hristoandreev/UA3REO-DDC-Transceiver/Schematic/Wolf/Altium_Designer/Mod-LZ1HAA-hardware/MOTHERBOARD/3d/conn-jack-sma-str-molex-73391-0060-rf-slash-coaxial/Renderings/floorsma.JPG

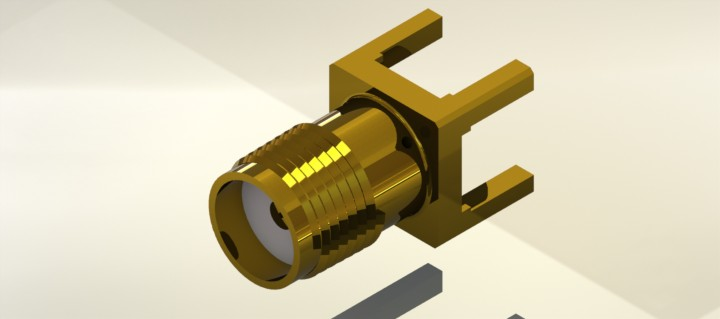
Schematic/Wolf/Altium_Designer/Mod-LZ1HAA-hardware/MOTHERBOARD/3d/conn-jack-sma-str-molex-73391-0060-rf-slash-coaxial/Renderings/floorsma.JPG
