hristoandreev/UA3REO-DDC-Transceiver/Schematic/Wolf/Altium_Designer/Mod-LZ1HAA-hardware/FRONT-UNIT-7/Project Outputs for FRONT-UNIT-7/BOM/Bill of Materials-FRONT-UNIT-7.xlsx

Comment | Description | Designator | Footprint | Quantity
0R | RES_0805 | R6, R7, R8 | RES_0805 | 3
1k | RES_0805 | R17, R18, R19, R20, R44 | RES_0805 | 5
1nF | CAP_1206 | C5 | CAP_1206 | 1
1uF | CAP_0805 | C48, C50, C51, C52, C53 | CAP_0805 | 5
1uF | CAP_1206 | C3 | CAP_1206 | 1
1uF 10V | CAPAE_4.3x4.3h5.4 | C34, C37, C42 | CAPAE_4.3x4.3h5.4 | 3
2k | RES_0805 | R21, R22, R23, R24 | RES_0805 | 4
4.7k | Chip Resistor | R32, R33 | R-0805 | 2
4.7k | RES_0805 | R3, R4, R5, R13, R14, R15, R16, R26, R27, R28, R29 | RES_0805 | 11
4.7k 1% | RES_0805 | R9 | RES_0805 | 1
5.6k | RES_0805 | R35, R36, R37, R38 | RES_0805 | 4
7.5k 1% | RES_0805 | R1 | RES_0805 | 1
10k | RES_0805 | R34, R39 | RES_0805 | 2
10nF | CAP_0805 | C30, C31 | CAP_0805 | 2
10uF 10V | CAPAE_4.3x4.3h5.4 | C15, C17, C18, C33, C35, C41, C44 | CAPAE_4.3x4.3h5.4 | 7
15k 1% | RES_0805 | R10 | RES_0805 | 1
22uF 10V | CAPAE_4.3x4.3h5.4 | C9, C11, C22, C24 | CAPAE_4.3x4.3h5.4 | 4
30k | RES_0805 | R45, R46 | RES_0805 | 2
39k 1% | RES_0805 | R2 | RES_0805 | 1
47k |  | R30 | CH0805R | 1
47k |  | R31 | CH0805C | 1
47k | RES_0805 | R41, R42, R43 | RES_0805 | 3
100nF |  | C27 | CH0805C | 1
100nF | CAP_0805 | C8, C10, C12, C14, C16, C19, C20, C21, C25, C26, C28, C29, C32, C36, C40, C43, C49 | CAP_0805 | 17
100nF | CAP_1206 | C4 | CAP_1206 | 1
100R |  | R25 | CH0805R | 1
120pF | CAP_1206 | C7 | CAP_1206 | 1
220pF | CAP_0805 | C38, C39, C45 | CAP_0805 | 3
470pF | CAP_1206 | C6 | CAP_1206 | 1
470uF 25V | CAP ALUM 470UF 20% 25V SMD | C1, C2 | SMD-G-10X10.2 | 2
680R | RES_0805 | R40 | RES_0805 | 1
42878-6216 | Connector | J3 | 428786216 | 1
744045003 | SMD-RF-Inductor WE-LQ, L = 3.30 µH | L3, L6 | WE-LQ-L | 2
AFC07-S60FCA-00 |  | J2 | AFC07-S60FCA-00 | 1
EEE1EA220SP | Capacitor Polarised | C13, C23 | EEE1AA101SP | 2
ESP8266_ESP-07 | Connector | J1 | ESP8266ESP07 | 1
IHLP2525CZER100M01 | Inductor | L1, L2, L4, L5 | INDPM6965X300N | 4
LCD-RA8875 | LCD-RA8875 | U1 | LCD-RA8875 | 1
MCP3008-I/SL | MCP3008-I/SL | U5 | MCP3008-I/SL | 1
MCP6001UT |  | U6, U7 | SOT23-5 | 2
PAM8406 | PAM8406 | U9 | PAM8403 | 1
PEC12 | PEC12 | ENC1 | PEC12 | 1
PJ-3583-B | Connector | J5, J6, J7 | PJ3583B | 3
PTS645SK50LFS | PTS645SK50LFS | S1, S2, S3, S4, S5, S6, S7, S8, S9, S10, S11, S12 | PTS645SK50LFS | 12
PTV09A-4030F-A102 | Adjustable Resistor PTV09 | R11, R12 | PTV09 | 2
S4B-PH-SM4-TB_LF__SN_ | Connector | J4 | S4B-PH-SM4-TB | 1
S5B-PH-SM4-TB(LF)(SN) | Male Header, Pitch 2 mm, 1 x 5 Position, Height 5.5 mm, -25 to 85 degC, RoHS, Tape and Reel | P1, P3 | JST-S5B-PH-SM4-TB_V | 2
S6B-PH-SM4-TB(LF)(SN) | Male Header, Pitch 2 mm, 1 x 6 Position, Height 5.5 mm, -25 to 85 degC | P2 | JST-S6B-PH-SM4-TB(LF)(SN)_V | 1
SMAJ5.0A-TR | Diode | D1, D2, D3, D4, D5, D6, D7 | SMBJ36CATR | 7
ST1S10 | ST1S10 | U2, U4 | ST1S10 | 2
T495D227K010ATE100 | CAP TANT 220UF 10% 10V 2917 | C46, C47 | FP-T495D227K010ATE100-MFG | 2
TPS79633DCQR | Single Output High PSRR LDO, 1 A, Fixed 3.3 V Output, 2.7 to 5.5 V Input, 6-pin SOT-223 (DCQ), -40 to 125 degC, Green (RoHS & no Sb/Br) | U3 | DCQ0006A_L | 1
WM8731 | WM8731 | U8 | WM8731 | 1
