hristoandreev/UA3REO-DDC-Transceiver/Schematic/Wolf/Altium_Designer/Mod-LZ1HAA-hardware/MOTHERBOARD/PDNAnalyzer_Output/MOTHERBOARD_Hristo_JLC2313_sdcard/Motherboard/Results-0/pins.csv

refdes | pin | voltage | current
J7 | 3 | 13.7993 | 0.0
J7 | 4 | 13.7993 | 0.0
J7 | 1 | 0.0 | -0.370706
J7 | 2 | 0.0 | -0.370706
L5 | 2 | 4.99822 | 1.6657
U12 | 9 | -0.000111179 | -0.308096
U12 | 8 | -0.000111179 | -0.308096
U12 | 4 | -0.000111179 | -0.308096
U11 | 107 | 2.49972 | -0.00799748
U11 | 96 | 2.49972 | -0.00799743
U11 | 75 | 2.49973 | -0.00799781
U11 | 35 | 2.49979 | -0.0080008
U11 | 3 | 2.49991 | -0.00800651
U11 | pdna_pin_145_1 | 0.00145045 | 0.02288067
U11 | pdna_pin_145_2 | 0.0 | 0.0
U11 | 140 | 0.00122659 | 0.02294482
U11 | 131 | 0.00114387 | 0.02296855
U11 | 123 | 0.00148096 | 0.02287187
U11 | 118 | 0.00122022 | 0.02294668
U11 | 108 | 0.00124122 | 0.022940620000000002
U11 | 97 | 0.0014233399999999997 | 0.02288838
U11 | 95 | 0.00144557 | 0.02288201
U11 | 94 | 0.00144526 | 0.02288213
U11 | 82 | 0.00158142 | 0.02284306
U11 | 79 | 0.00155592 | 0.02285042
U11 | 74 | 0.00161322 | 0.022833939999999997
U11 | 63 | 0.00166629 | 0.02281874
U11 | 57 | 0.0016726400000000002 | 0.022816879999999998
U11 | 48 | 0.0016924 | 0.022811230000000002
U11 | 41 | 0.00173304 | 0.02279963
U11 | 36 | 0.00173022 | 0.02280037
U11 | 27 | 0.00169233 | 0.022811230000000002
U11 | 22 | 0.0016202099999999997 | 0.02283192
U11 | 19 | 0.0015784199999999999 | 0.02284393
U11 | 4 | 0.0015008700000000003 | 0.022866200000000003
U11 | 2 | 0.00149893 | 0.02286678
U18 | 11 | 3.29584 | -0.0284892
U18 | 20 | 3.29595 | -0.0285227
U18 | 21 | 3.29597 | -0.0285296
U18 | 27 | 3.29628 | -0.0286243
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
U16 | 1 | 0.000621993 | 0.0001
L3 | 1 | 4.98913 | -0.1301
U4 | 2 | 0.00174795 | 0.0001
U7 | 3 | 4.99413 | -0.09759999999999999
U7 | 1 | 4.99413 | -0.09759999999999999
U7 | 2 | 0.000861907 | 0.0001
U8 | 3 | 3.29911 | -0.07005
U8 | 1 | 3.29911 | -0.07005
U8 | 2 | 0.00149597 | 0.0001
U1 | 1 | 4.98743 | -0.27755
U1 | 2 | 4.98743 | -0.27755
U1 | 3 | 0.00179304 | 4.99981e-05
U1 | 6 | 0.00178536 | 5.00019e-05
U12 | 1 | 13.202 | -0.370767
U12 | 2 | 13.2019 | -0.370644
U13 | 4 | 3.30009 | 0.345
U15 | 4 | 2.50008 | 0.4401
U16 | 4 | 1.21233 | 0.4
U4 | 5 | 3.30009 | 0.13
U7 | 5 | 3.30009 | 0.1951
U8 | 5 | 1.80605 | 0.14
C1 | 1 | 3.30009 | 0.555
C75 | 2 | 13.2993 | -9.999999999177334e-07
C74 | 2 | 13.2029 | 0.741412
