hristoandreev/UA3REO-DDC-Transceiver/Schematic/Wolf/Altium_Designer/Mod-LZ1HAA-hardware/FRONT-UNIT-7/3d/SSOP28_10P2X5P3X1P75_CIR.step

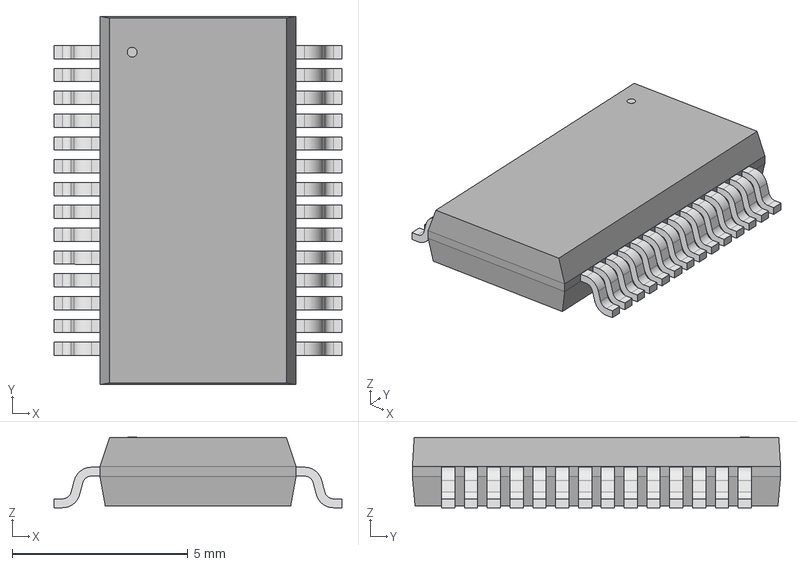
[picture p29: CAD file, 2022-07-08]
Schematic/Wolf/Altium_Designer/Mod-LZ1HAA-hardware/FRONT-UNIT-7/3d/SSOP28_10P2X5P3X1P75_CIR.step
8.20 x 10.5 x 2.01 mm
