hristoandreev/UA3REO-DDC-Transceiver/Schematic/Wolf/Altium_Designer/Mod-LZ1HAA-hardware/MOTHERBOARD/3d/SO8W_5P49X5P49_MRN.step

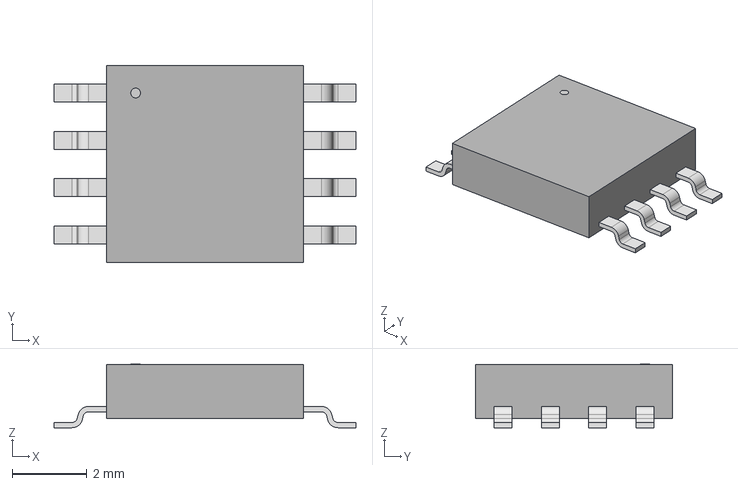
[picture p30: CAD file, 2022-07-08]
Schematic/Wolf/Altium_Designer/Mod-LZ1HAA-hardware/MOTHERBOARD/3d/SO8W_5P49X5P49_MRN.step
8.10 x 5.28 x 1.70 mm
