hristoandreev/UA3REO-DDC-Transceiver/Schematic/Wolf/CASE/3'2/3DPrinter/ST-212.step

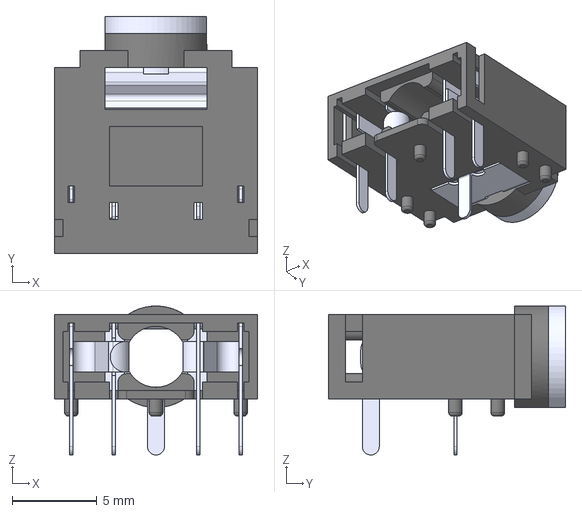
[picture p31: CAD file, 2022-07-29]
Schematic/Wolf/CASE/3'2/3DPrinter/ST-212.step
12.0 x 14.0 x 8.80 mm
