hristoandreev/UA3REO-DDC-Transceiver/Schematic/Wolf/CASE/VFO/VFO38WithExt.stl

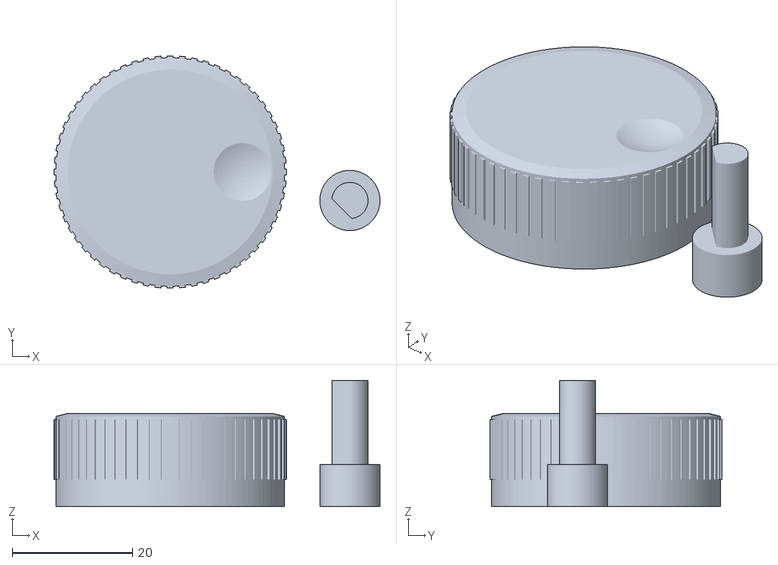
[picture p33: CAD file, 2022-07-29]
Schematic/Wolf/CASE/VFO/VFO38WithExt.stl
54.1 x 38.6 x 21.0
