hristoandreev/UA3REO-DDC-Transceiver/Schematic/Wolf/Altium_Designer/Mod-LZ1HAA-hardware/MOTHERBOARD/3d/QFN-64_UP_LIT.step

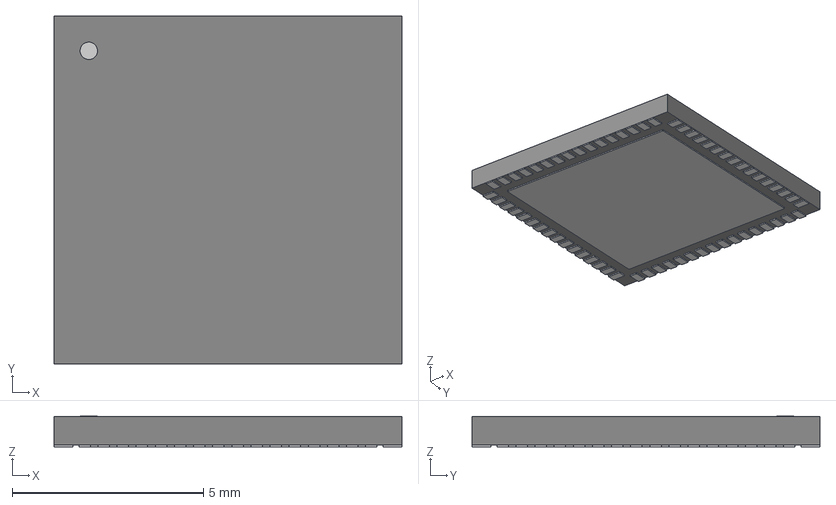
[picture p35: CAD file, 2022-07-08]
Schematic/Wolf/Altium_Designer/Mod-LZ1HAA-hardware/MOTHERBOARD/3d/QFN-64_UP_LIT.step
9.10 x 9.10 x 0.803 mm
