hristoandreev/UA3REO-DDC-Transceiver/Schematic/Wolf/CASE/VFO/ExtEncoder.stl

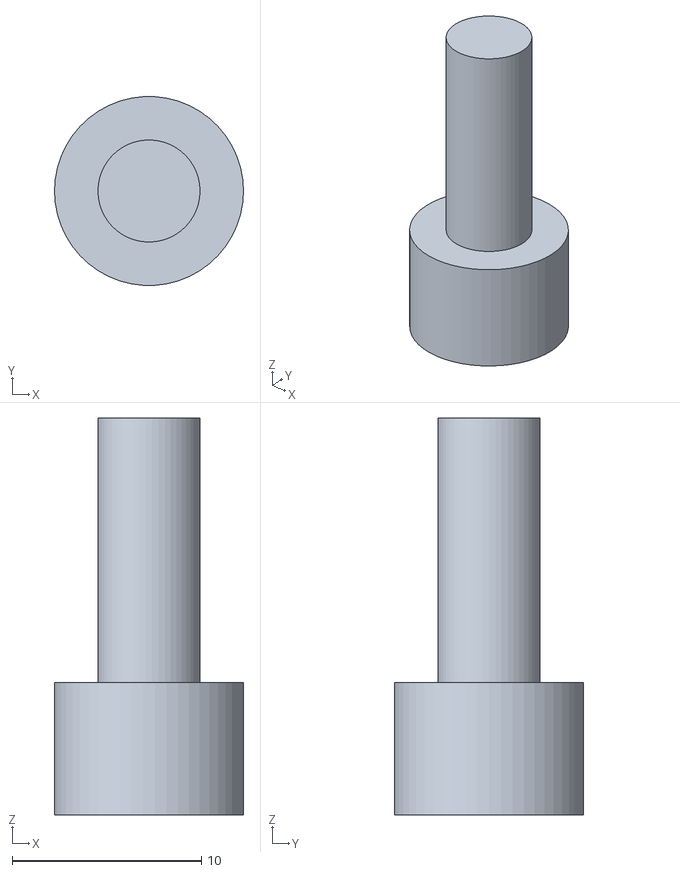
[picture p37: CAD file, 2022-07-29]
Schematic/Wolf/CASE/VFO/ExtEncoder.stl
10.0 x 9.98 x 21.0
