hristoandreev/UA3REO-DDC-Transceiver/Schematic/Wolf/Altium_Designer/Mod-LZ1HAA-hardware/MOTHERBOARD/3d/idc10.STEP

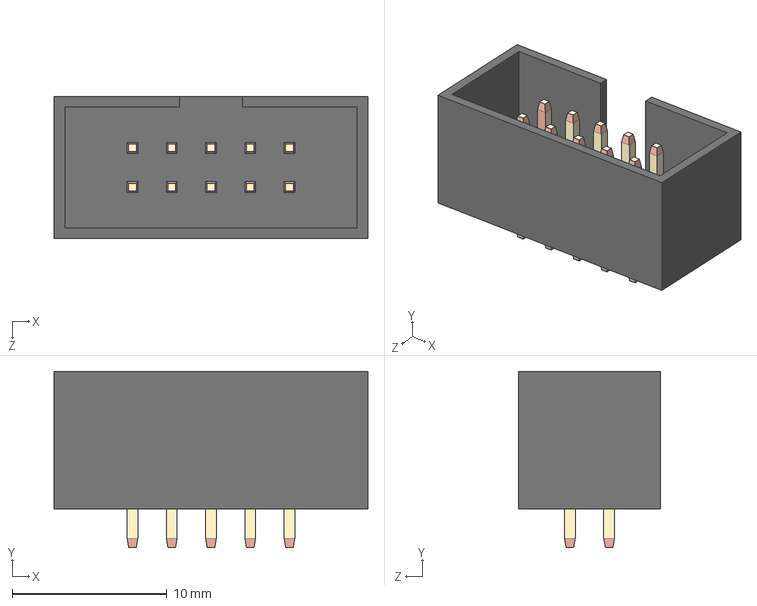
[picture p38: CAD file, 2022-07-08]
Schematic/Wolf/Altium_Designer/Mod-LZ1HAA-hardware/MOTHERBOARD/3d/idc10.STEP
20.3 x 11.4 x 9.20 mm
