hristoandreev/UA3REO-DDC-Transceiver/Schematic/Wolf/CASE/3'2/3DPrinter/case/encoder_mount_front.SLDPRT

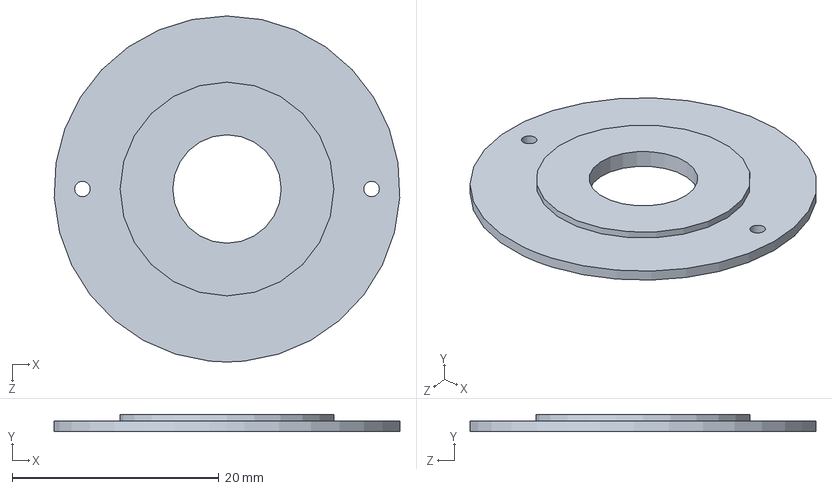
[picture p39: CAD file, 2022-07-29]
Schematic/Wolf/CASE/3'2/3DPrinter/case/encoder_mount_front.SLDPRT
33.5 x 1.65 x 33.5 mm
