hristoandreev/UA3REO-DDC-Transceiver/Schematic/Wolf/CASE/3'2/3DPrinter/Rotary Encoder.SLDPRT

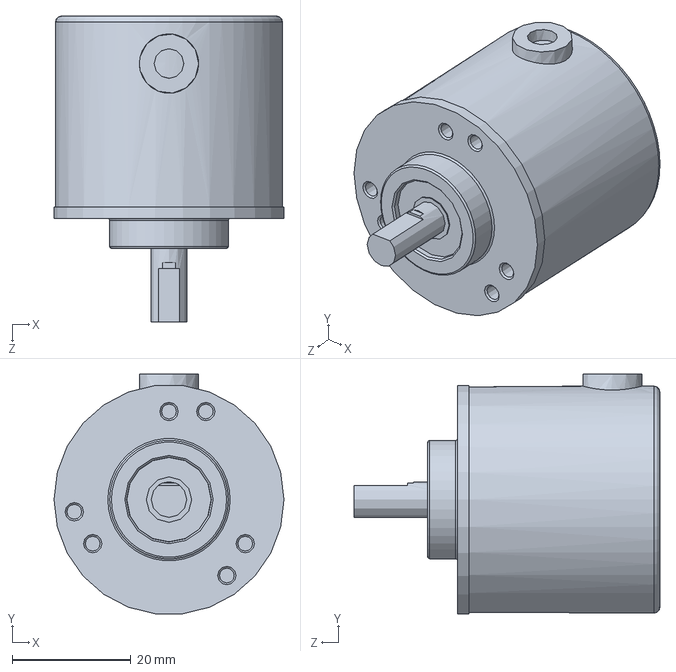
[picture p40: CAD file, 2022-07-29]
Schematic/Wolf/CASE/3'2/3DPrinter/Rotary Encoder.SLDPRT
38.7 x 40.3 x 51.5 mm
