hristoandreev/UA3REO-DDC-Transceiver/Schematic/Wolf/Altium_Designer/Mod-LZ1HAA-hardware/MOTHERBOARD/3d/SON_T4-6T_MNC.step

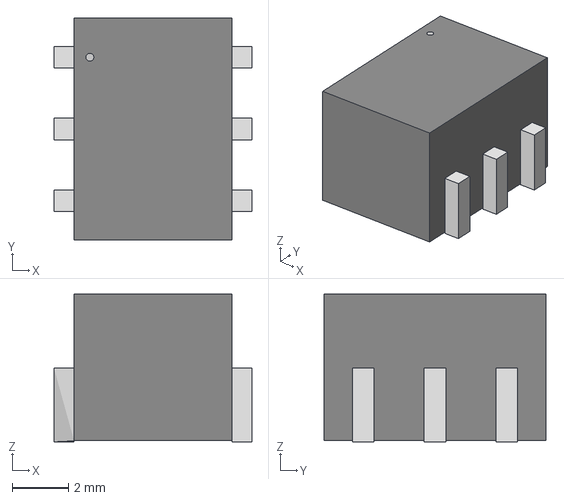
[picture p41: CAD file, 2022-07-08]
Schematic/Wolf/Altium_Designer/Mod-LZ1HAA-hardware/MOTHERBOARD/3d/SON_T4-6T_MNC.step
7.01 x 7.87 x 5.24 mm
