hristoandreev/UA3REO-DDC-Transceiver/Schematic/Wolf/CASE/3'2/3DPrinter/DS-261A.step

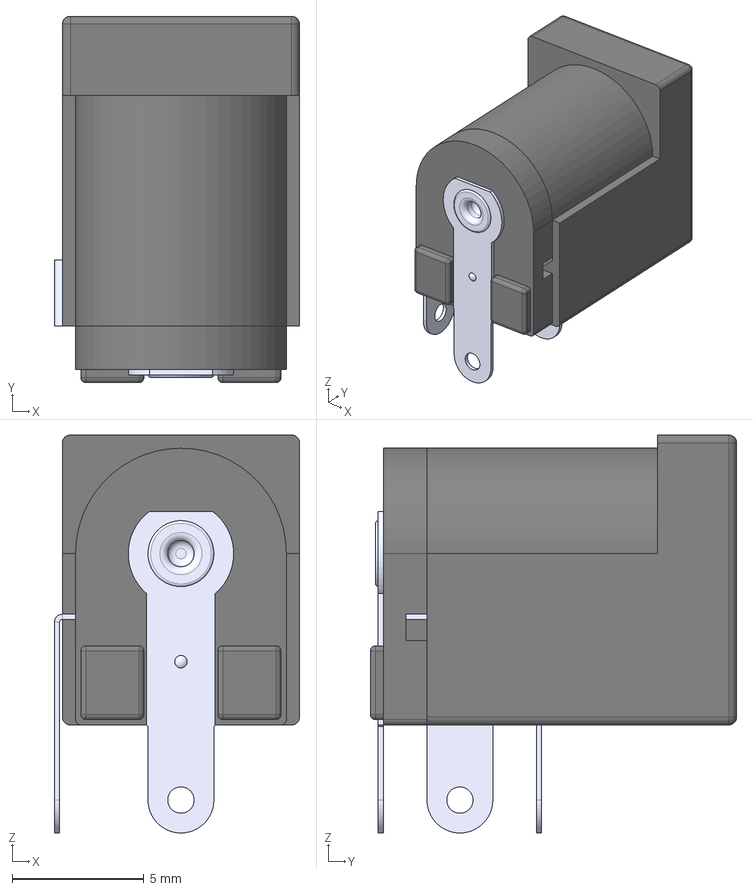
[picture p43: CAD file, 2022-07-29]
Schematic/Wolf/CASE/3'2/3DPrinter/DS-261A.step
9.30 x 13.9 x 15.1 mm
