hristoandreev/UA3REO-DDC-Transceiver/Schematic/Wolf/Altium_Designer/Mod-LZ1HAA-hardware/MOTHERBOARD/3d/NDP0003B.stp

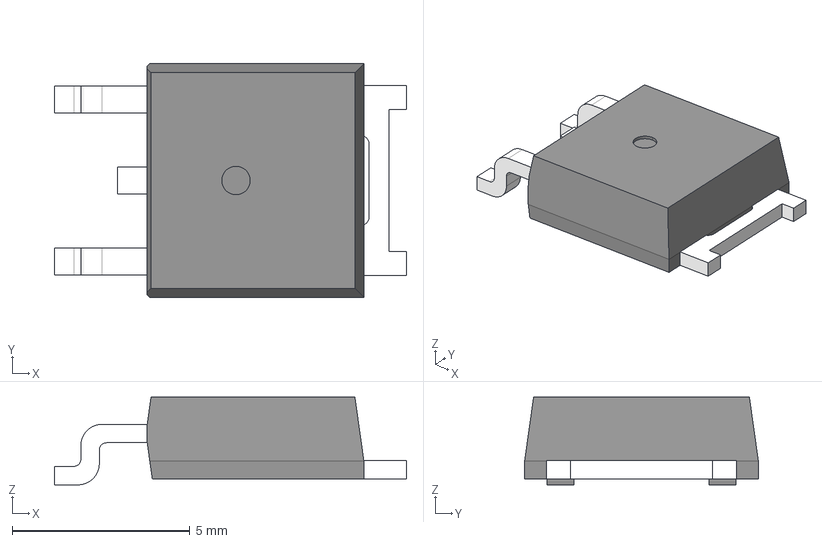
[picture p44: CAD file, 2022-07-08]
Schematic/Wolf/Altium_Designer/Mod-LZ1HAA-hardware/MOTHERBOARD/3d/NDP0003B.stp
9.91 x 6.58 x 2.47 mm
BODY_NDP0003B
HSINK_NDP0003B
LEAD_NDP0003B x 2
CLEAD_NDP0003B
