hristoandreev/UA3REO-DDC-Transceiver/Schematic/Wolf/CASE/3'2/3DPrinter/case/shuttle_knob.SLDPRT

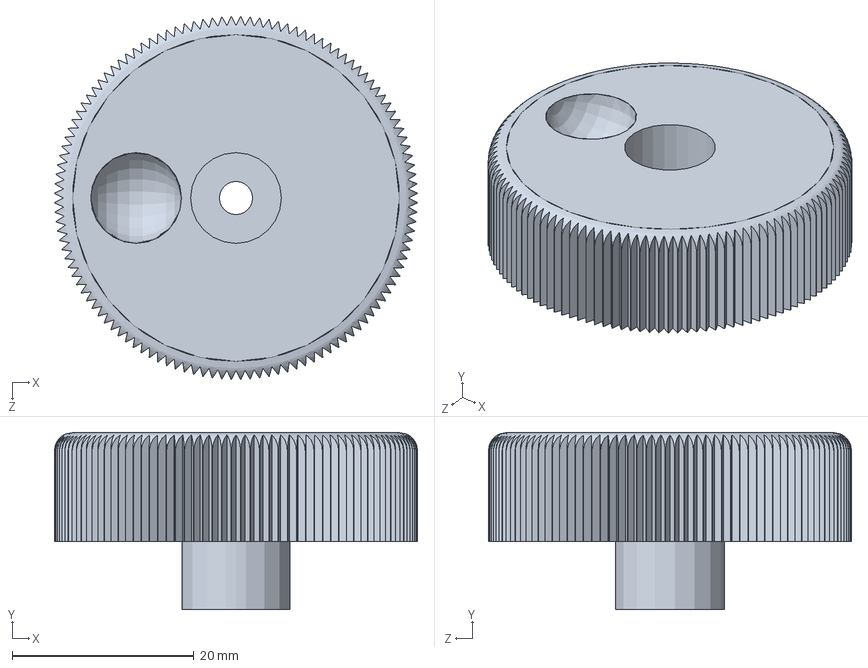
[picture p45: CAD file, 2022-07-29]
Schematic/Wolf/CASE/3'2/3DPrinter/case/shuttle_knob.SLDPRT
40.0 x 19.5 x 40.0 mm
