hristoandreev/UA3REO-DDC-Transceiver/Schematic/Wolf/Altium_Designer/Mod-LZ1HAA-hardware/MOTHERBOARD/3d/VG-4513CA122_8800M-GGCT3_EPS.step

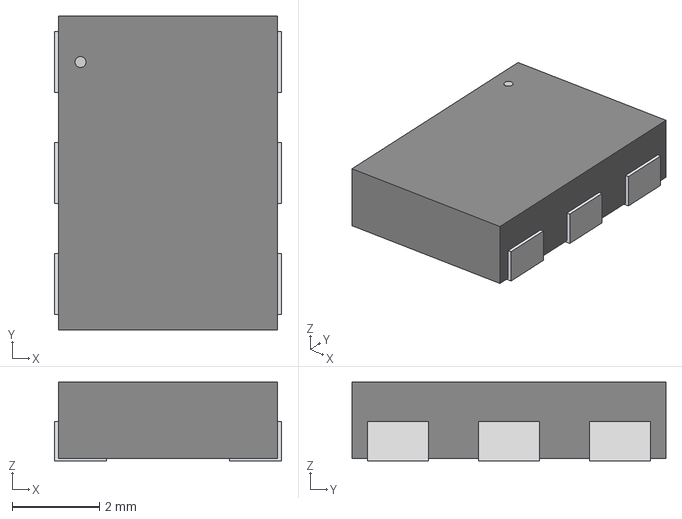
[picture p47: CAD file, 2022-07-08]
Schematic/Wolf/Altium_Designer/Mod-LZ1HAA-hardware/MOTHERBOARD/3d/VG-4513CA122_8800M-GGCT3_EPS.step
5.20 x 7.19 x 1.81 mm
