hristoandreev/UA3REO-DDC-Transceiver/Schematic/Wolf/Altium_Designer/Mod-LZ1HAA-hardware/MOTHERBOARD/3d/Pin Header 1x2 TH Pitch 2.54mm.stp

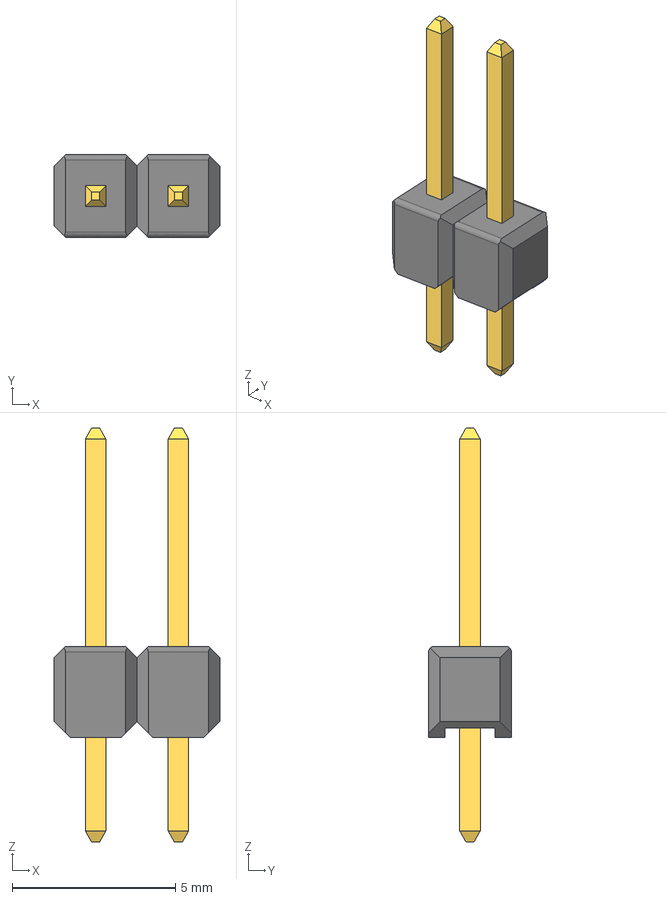
[picture p48: CAD file, 2022-07-08]
Schematic/Wolf/Altium_Designer/Mod-LZ1HAA-hardware/MOTHERBOARD/3d/Pin Header 1x2 TH Pitch 2.54mm.stp
5.08 x 2.54 x 12.7 mm
