hristoandreev/UA3REO-DDC-Transceiver/Schematic/Wolf/Altium_Designer/Mod-LZ1HAA-hardware/MOTHERBOARD/3d/SOIC_16JLSSIG_WIN.step

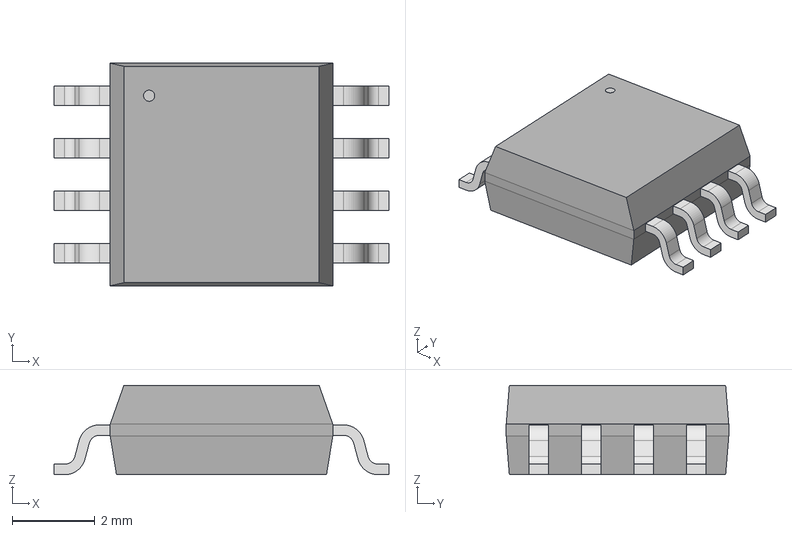
[picture p49: CAD file, 2022-07-08]
Schematic/Wolf/Altium_Designer/Mod-LZ1HAA-hardware/MOTHERBOARD/3d/SOIC_16JLSSIG_WIN.step
8.10 x 5.38 x 2.16 mm
