hristoandreev/UA3REO-DDC-Transceiver/Schematic/Wolf/Altium_Designer/Mod-LZ1HAA-hardware/MOTHERBOARD/3d/SOIC_150MIL_WIN.step

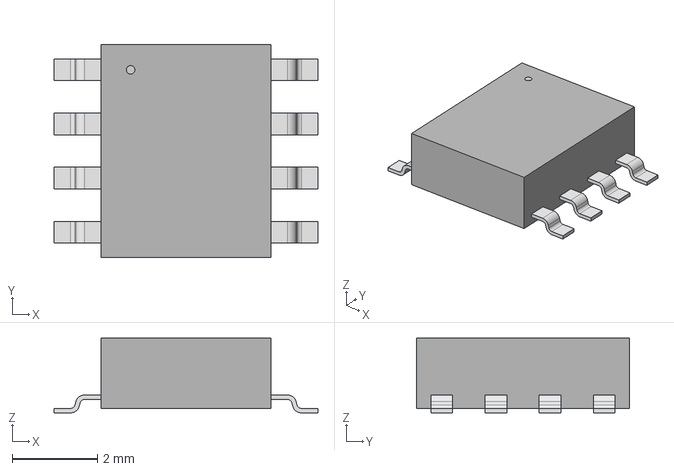
[picture p52: CAD file, 2022-07-08]
Schematic/Wolf/Altium_Designer/Mod-LZ1HAA-hardware/MOTHERBOARD/3d/SOIC_150MIL_WIN.step
6.20 x 5.00 x 1.75 mm
