hristoandreev/UA3REO-DDC-Transceiver/Schematic/Wolf/CASE/3'2/3DPrinter/case/case_connector_cap.SLDPRT

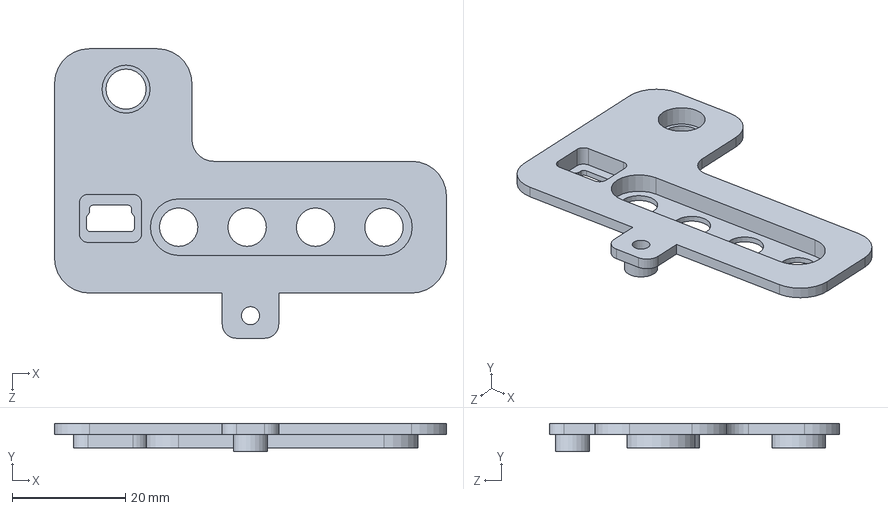
[picture p53: CAD file, 2022-07-29]
Schematic/Wolf/CASE/3'2/3DPrinter/case/case_connector_cap.SLDPRT
69.3 x 5.00 x 51.2 mm
