hristoandreev/UA3REO-DDC-Transceiver/Schematic/Wolf/CASE/3'2/3DPrinter/case/button.SLDPRT

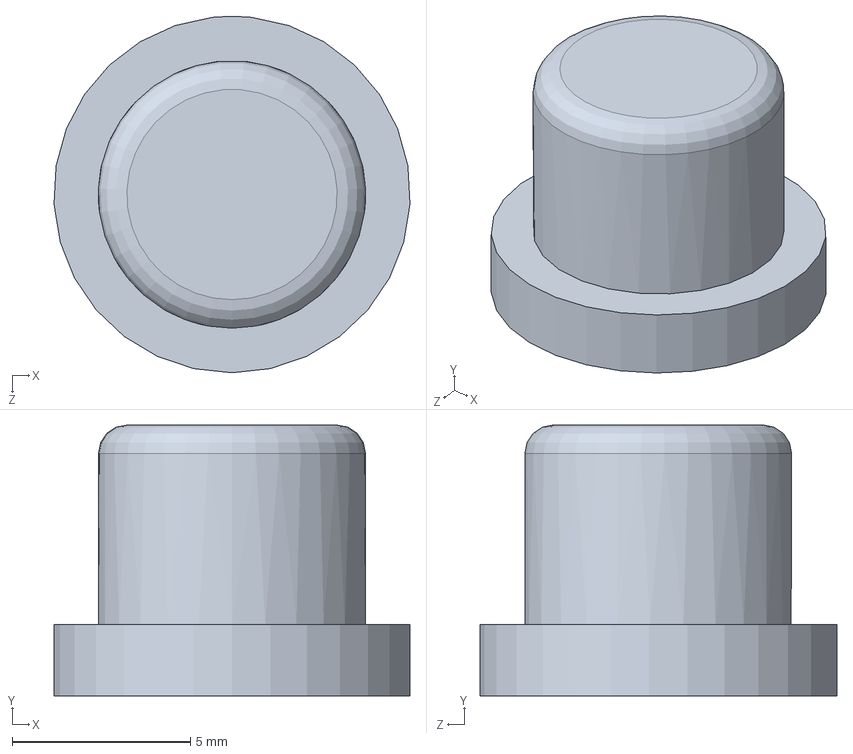
[picture p54: CAD file, 2022-07-29]
Schematic/Wolf/CASE/3'2/3DPrinter/case/button.SLDPRT
9.99 x 7.60 x 10.0 mm
