hristoandreev/UA3REO-DDC-Transceiver/Schematic/Wolf/CASE/3'2/3DPrinter/GX12-6P v2.step

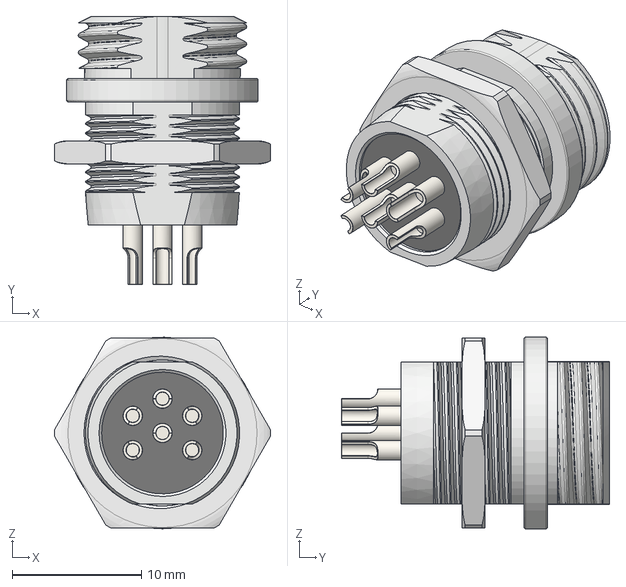
[picture p55: CAD file, 2022-07-29]
Schematic/Wolf/CASE/3'2/3DPrinter/GX12-6P v2.step
16.7 x 20.7 x 14.8 mm
