hristoandreev/UA3REO-DDC-Transceiver/Schematic/Wolf/CASE/3'2/3DPrinter/case/case_speaker_cap.SLDPRT

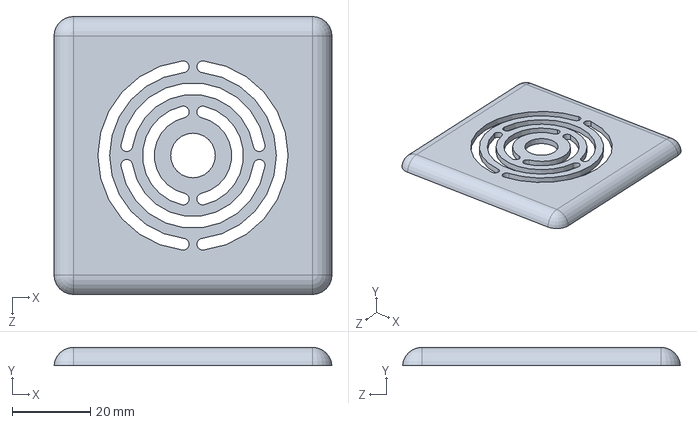
[picture p56: CAD file, 2022-07-29]
Schematic/Wolf/CASE/3'2/3DPrinter/case/case_speaker_cap.SLDPRT
71.0 x 4.70 x 71.0 mm
