hristoandreev/UA3REO-DDC-Transceiver/Schematic/Wolf/CASE/3'2/3DPrinter/tactileswitch-long.SLDPRT

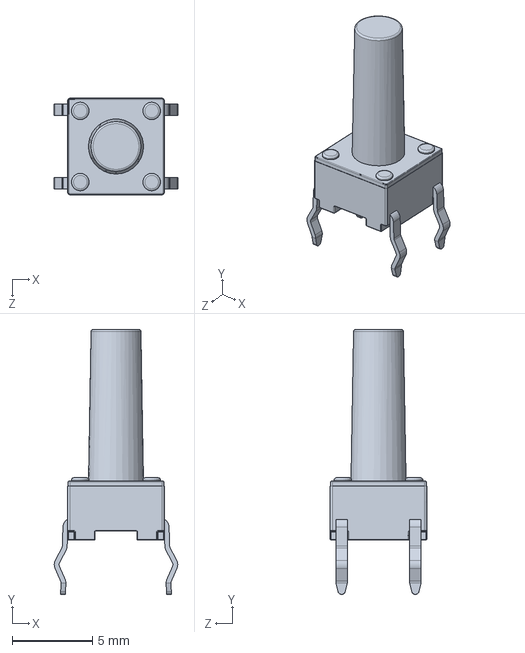
[picture p57: CAD file, 2022-07-29]
Schematic/Wolf/CASE/3'2/3DPrinter/tactileswitch-long.SLDPRT
7.69 x 16.5 x 6.01 mm
