hristoandreev/UA3REO-DDC-Transceiver/Schematic/Wolf/CASE/3'2/3DPrinter/RF.SLDPRT

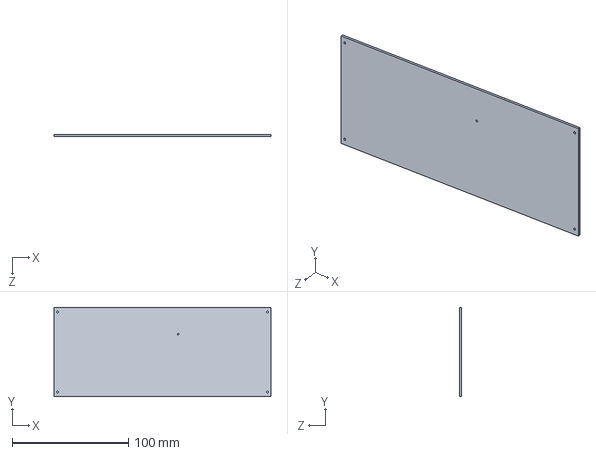
[picture p59: CAD file, 2022-07-29]
Schematic/Wolf/CASE/3'2/3DPrinter/RF.SLDPRT
187.0 x 77.0 x 1.60 mm
