hristoandreev/UA3REO-DDC-Transceiver/Schematic/Wolf/CASE/3'2/3DPrinter/beam_long.SLDPRT

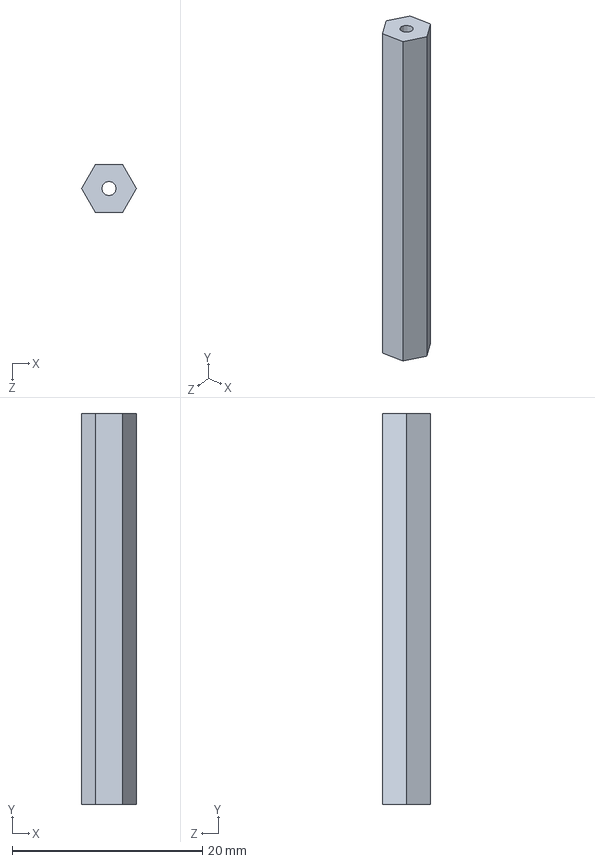
[picture p61: CAD file, 2022-07-29]
Schematic/Wolf/CASE/3'2/3DPrinter/beam_long.SLDPRT
5.77 x 41.1 x 5.00 mm
