hristoandreev/UA3REO-DDC-Transceiver/Schematic/Wolf/CASE/3'2/3DPrinter/encoder_knob.SLDPRT

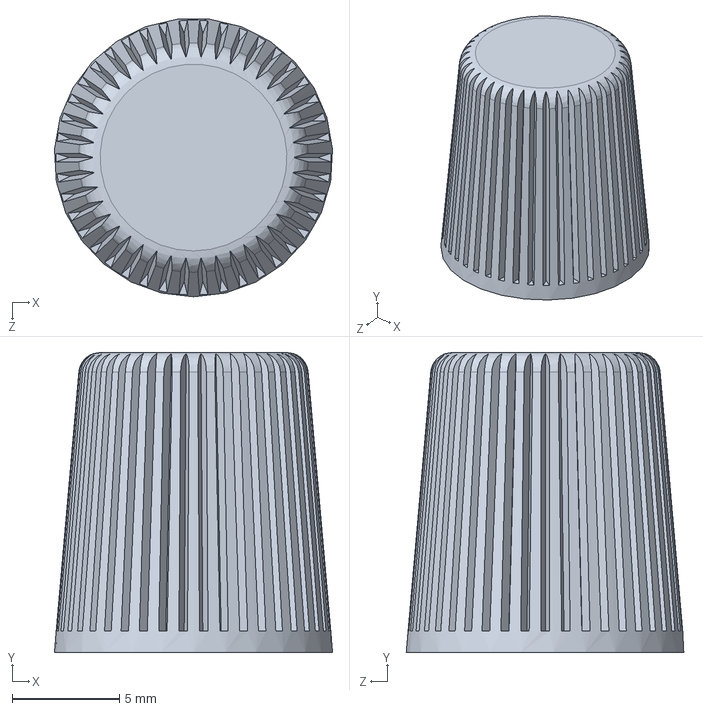
[picture p63: CAD file, 2022-07-29]
Schematic/Wolf/CASE/3'2/3DPrinter/encoder_knob.SLDPRT
13.0 x 14.0 x 13.0 mm
