hristoandreev/UA3REO-DDC-Transceiver/Schematic/Wolf/CASE/3'2/3DPrinter/Encoder_Axis.SLDPRT

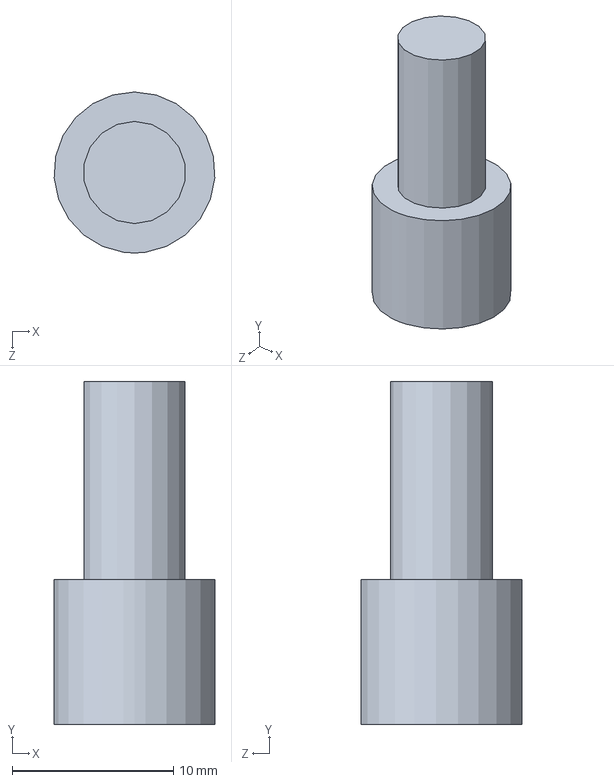
[picture p67: CAD file, 2022-07-29]
Schematic/Wolf/CASE/3'2/3DPrinter/Encoder_Axis.SLDPRT
9.98 x 21.3 x 10.0 mm
