hristoandreev/UA3REO-DDC-Transceiver/Schematic/Wolf/Addons/TS4994_Add_on_v1/_Print/3D_BOT.JPG

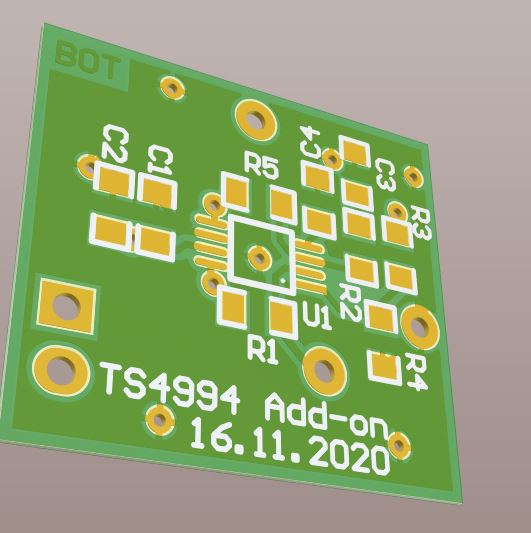
Schematic/Wolf/Addons/TS4994_Add_on_v1/_Print/3D_BOT.JPG
