hristoandreev/UA3REO-DDC-Transceiver/Schematic/Wolf/Altium_Designer/Mod-LZ1HAA-hardware/MOTHERBOARD/PDNAnalyzer_Output/MOTHERBOARD_Hristo_JLC2313_sdcard/FPGA_VCORE/Results/vias.csv

x | y | layer1 | layer2 | voltage1 | voltage2 | current
31.6703 | 563.937 | TOP_LAYER | GND | 0.000740942 | 0.00074094 | 1.50109e-05
31.6703 | 563.937 | GND | POWER | 0.00074094 | 0.000740908 | 1.50109e-05
31.6703 | 563.937 | POWER | BOTTOM_LAYER | 0.000740908 | 0.000740901 | 4.61479e-05
31.6703 | 591.657 | TOP_LAYER | GND | 0.000741112 | 0.000741107 | 3.77152e-05
31.6703 | 591.657 | GND | POWER | 0.000741107 | 0.000741026 | 3.77152e-05
31.6703 | 591.657 | POWER | BOTTOM_LAYER | 0.000741026 | 0.000741014 | 8.64245e-05
31.6703 | 1378.82 | TOP_LAYER | GND | 0.000743203 | 0.000743206 | -1.67594e-05
31.6703 | 1378.82 | GND | POWER | 0.000743206 | 0.000743242 | -1.67594e-05
31.6703 | 1378.82 | POWER | BOTTOM_LAYER | 0.000743242 | 0.000743241 | 7.50229e-07
31.7827 | 1406.54 | TOP_LAYER | GND | 0.000743247 | 0.000743248 | -6.72565e-06
31.7827 | 1406.54 | GND | POWER | 0.000743248 | 0.000743263 | -6.72565e-06
31.7827 | 1406.54 | POWER | BOTTOM_LAYER | 0.000743263 | 0.000743263 | -3.62727e-06
35.2127 | 42.7816 | TOP_LAYER | GND | 0.000733509 | 0.000733511 | -1.46654e-05
35.2127 | 42.7816 | GND | POWER | 0.000733511 | 0.000733503 | 3.67812e-06
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
