hristoandreev/UA3REO-DDC-Transceiver/Schematic/Wolf/Altium_Designer/Mod-LZ1HAA-hardware/MOTHERBOARD/PDNAnalyzer_Output/MOTHERBOARD_Hristo_JLC2313_sdcard/FPGA_VCORE/Results/vcomp2id.csv

vrefdes | id
VCOMP0 | 0
VCOMP1 | 1
