hristoandreev/UA3REO-DDC-Transceiver/Schematic/Wolf/Altium_Designer/Mod-LZ1HAA-hardware/MOTHERBOARD/PDNAnalyzer_Output/MOTHERBOARD_Hristo_JLC2313_sdcard/FPGA_VCORE/Results/vpins.csv

refdes | pin | voltage | current | rpin
VCOMP0 | VCOMP0-0 | 1.1995 | 0.5 | 0
VCOMP0 | VCOMP0-1 | 0 | -0.5 | 0
VCOMP1 | VCOMP1-0 | 1.19643 | -0.0277821 | 4.03902
VCOMP1 | VCOMP1-1 | 1.19647 | -0.0277921 | 4.03902
VCOMP1 | VCOMP1-2 | 1.19627 | -0.0277421 | 4.03902
VCOMP1 | VCOMP1-3 | 1.19594 | -0.0276596 | 4.03902
VCOMP1 | VCOMP1-4 | 1.19573 | -0.0276088 | 4.03902
VCOMP1 | VCOMP1-5 | 1.19605 | -0.0276876 | 4.03902
VCOMP1 | VCOMP1-6 | 1.19605 | -0.0276881 | 4.03902
VCOMP1 | VCOMP1-7 | 1.19614 | -0.0277096 | 4.03902
VCOMP1 | VCOMP1-8 | 1.1961 | -0.0277002 | 4.03902
VCOMP1 | VCOMP1-9 | 1.19619 | -0.0277233 | 4.03902
VCOMP1 | VCOMP1-10 | 1.19643 | -0.0277809 | 4.03902
VCOMP1 | VCOMP1-11 | 1.19675 | -0.0278616 | 4.03902
VCOMP1 | VCOMP1-12 | 1.19686 | -0.0278874 | 4.03902
VCOMP1 | VCOMP1-13 | 1.19684 | -0.0278834 | 4.03902
VCOMP1 | VCOMP1-14 | 1.19693 | -0.027906 | 4.03902
VCOMP1 | VCOMP1-15 | 1.19698 | -0.0279173 | 4.03902
VCOMP1 | VCOMP1-16 | 1.19663 | -0.0278308 | 4.03902
VCOMP1 | VCOMP1-17 | 1.19666 | -0.0278397 | 4.03902
VCOMP1 | VCOMP1-18 | 0.000726181 | 0.0227366 | 4.03902
VCOMP1 | VCOMP1-19 | 0 | 0 | 4.03902
VCOMP1 | VCOMP1-20 | 0.000656341 | 0.0227539 | 4.03902
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
