hristoandreev/UA3REO-DDC-Transceiver/Schematic/Wolf/Addons/R7KBI/RF-UNIT.pdf

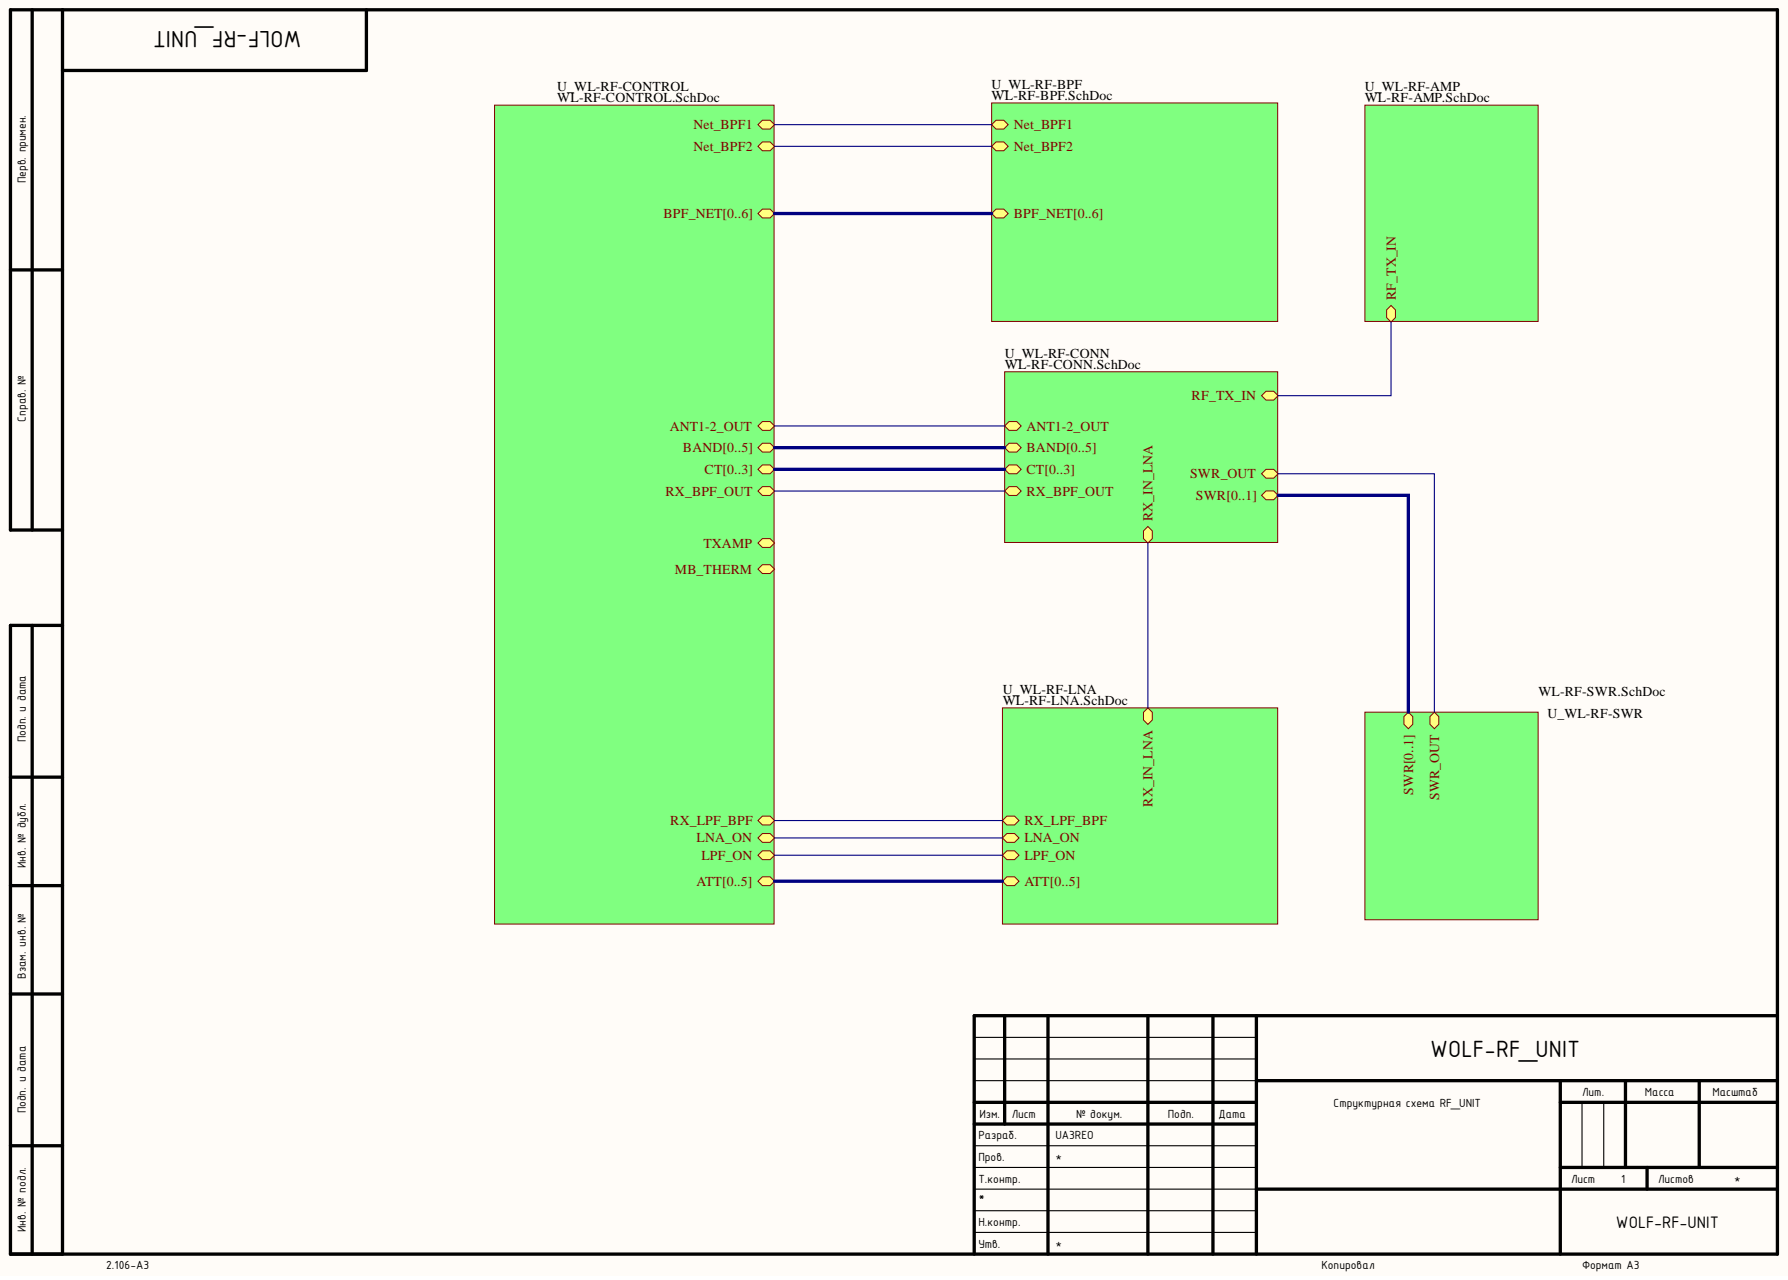
[picture p138: page 1]

U_WL-RF-CONTROL WL-RF-CONTROL.SchDoc

U_WL-RF-BPF WL-RF-BPF.SchDoc

U_WL-RF-AMP WL-RF-AMP.SchDoc

Инв. № подл. Инв. № дубл. Подп. и дата Взам. инв. № Подп. и дата Перв. примен. Справ. №

U_WL-RF-CONN WL-RF-CONN.SchDoc

U_WL-RF-LNA WL-RF-LNA.SchDoc

WL-RF-SWR.SchDoc
U_WL-RF-SWR

WOLF-RF_UNIT

Структурная схема RF_UNIT | Лит. | Масса | Масштаб

Изм. | Лист | № докум. | Подп. | Дата

Разраб. | | UA3REO

Пров. | | *

Т.контр. | | | | | Лист | Листов *
* | | | | | WOLF-RF-UNIT

Н.контр.

Утв. | *

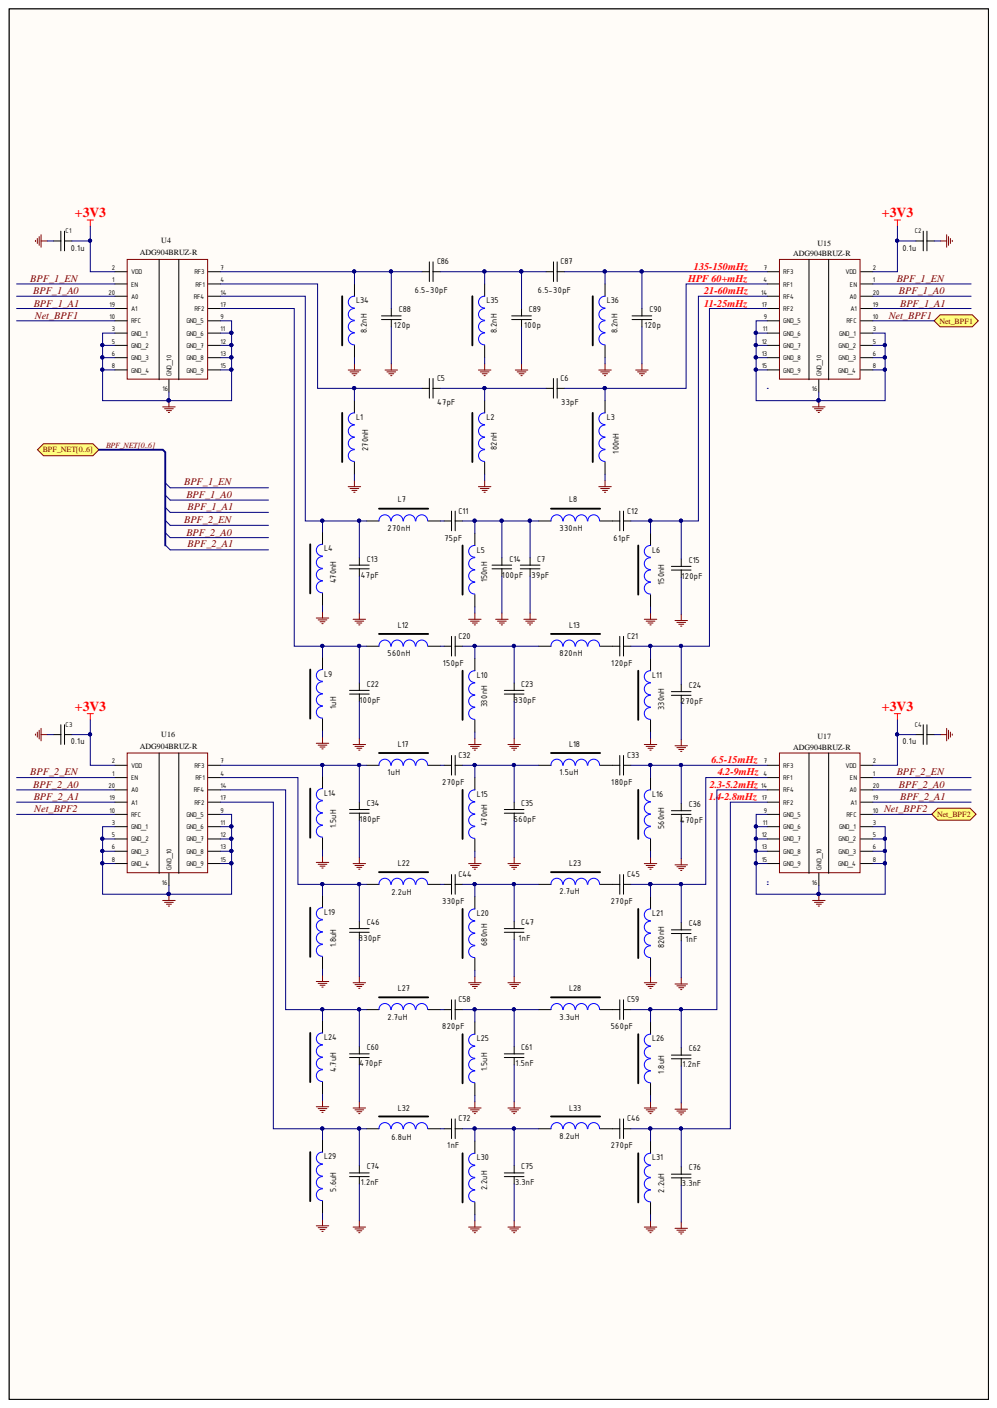
[picture p139: page 2]

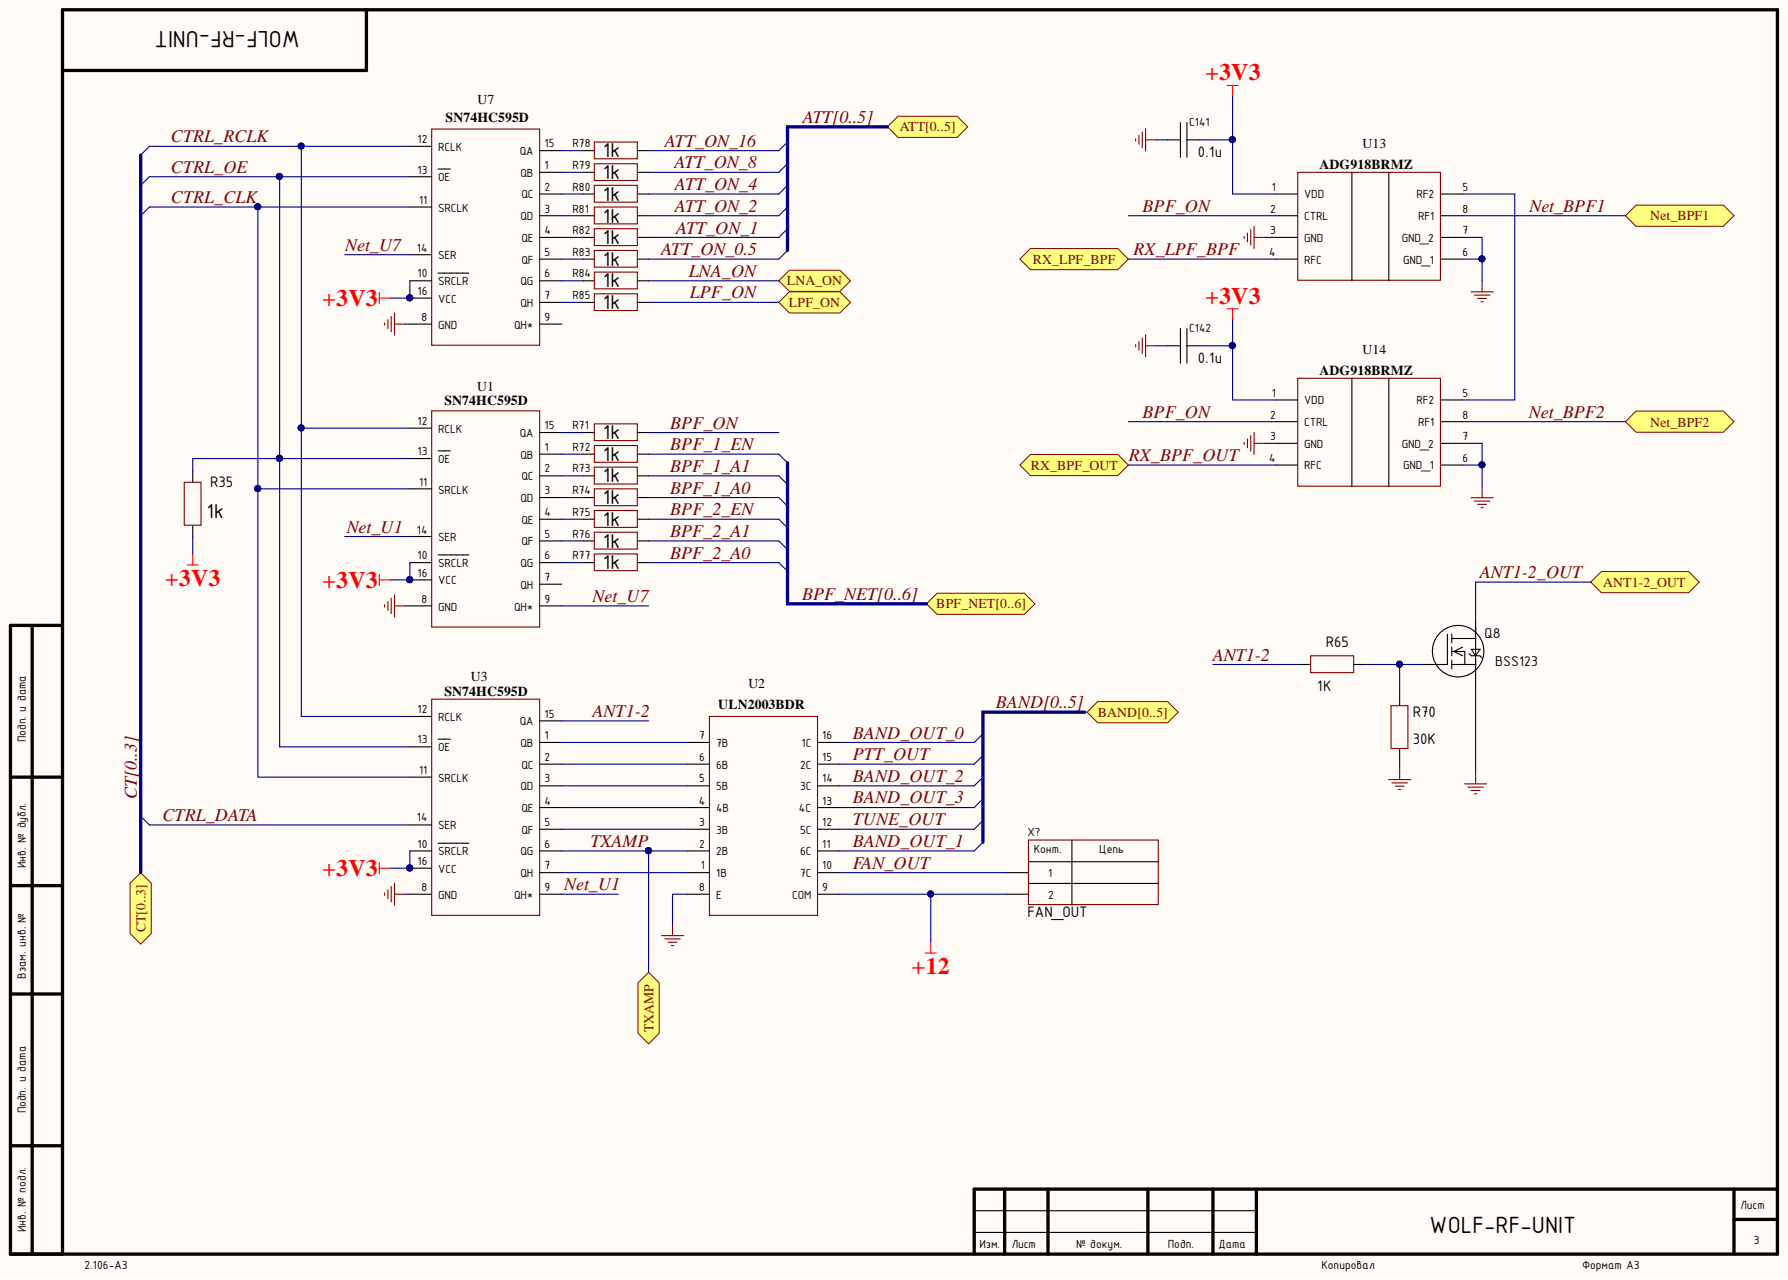
[picture p140: page 3]

VD D CT R L G N D RFC | RF2 RF1 G N D_2 G N D_1

1 6
8 | | 1 k

Инв. № подл. Инв. № дубл. Подп. и дата Взам. инв. № Подп. и дата

1 1 | 2 6 | 1 5 PTT_O U T

3 5 | BAND_O UT_2 1 4

4 4 | BAND_O UT_3 1 3

5 3 | TUNE_O U T 1 2

Конт . | Цепь

1 6 | 7 | 1 | FAN_O U T 1 0

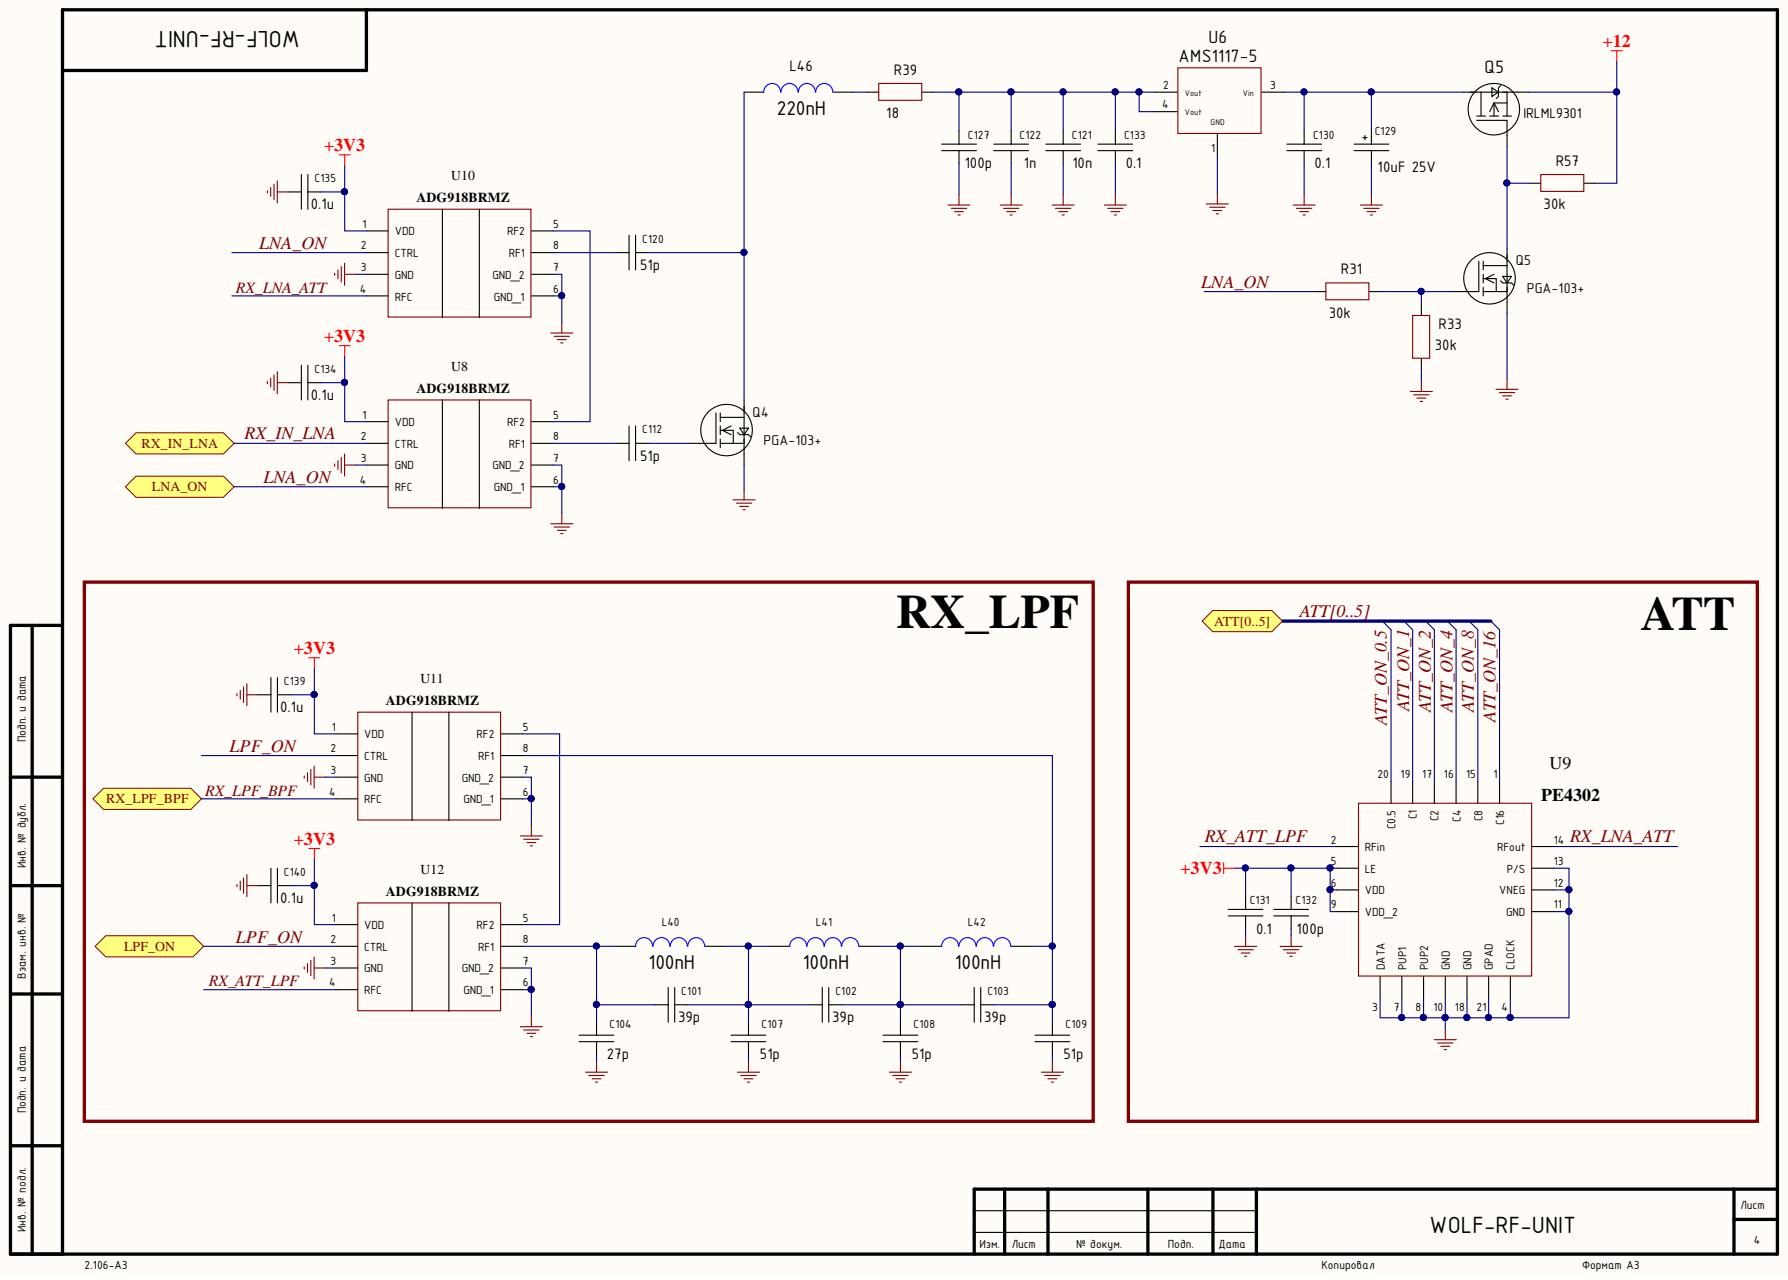
[picture p141: page 4]

Инв. № подл. Инв. № дубл. Подп. и дата Взам. инв. № Подп. и дата

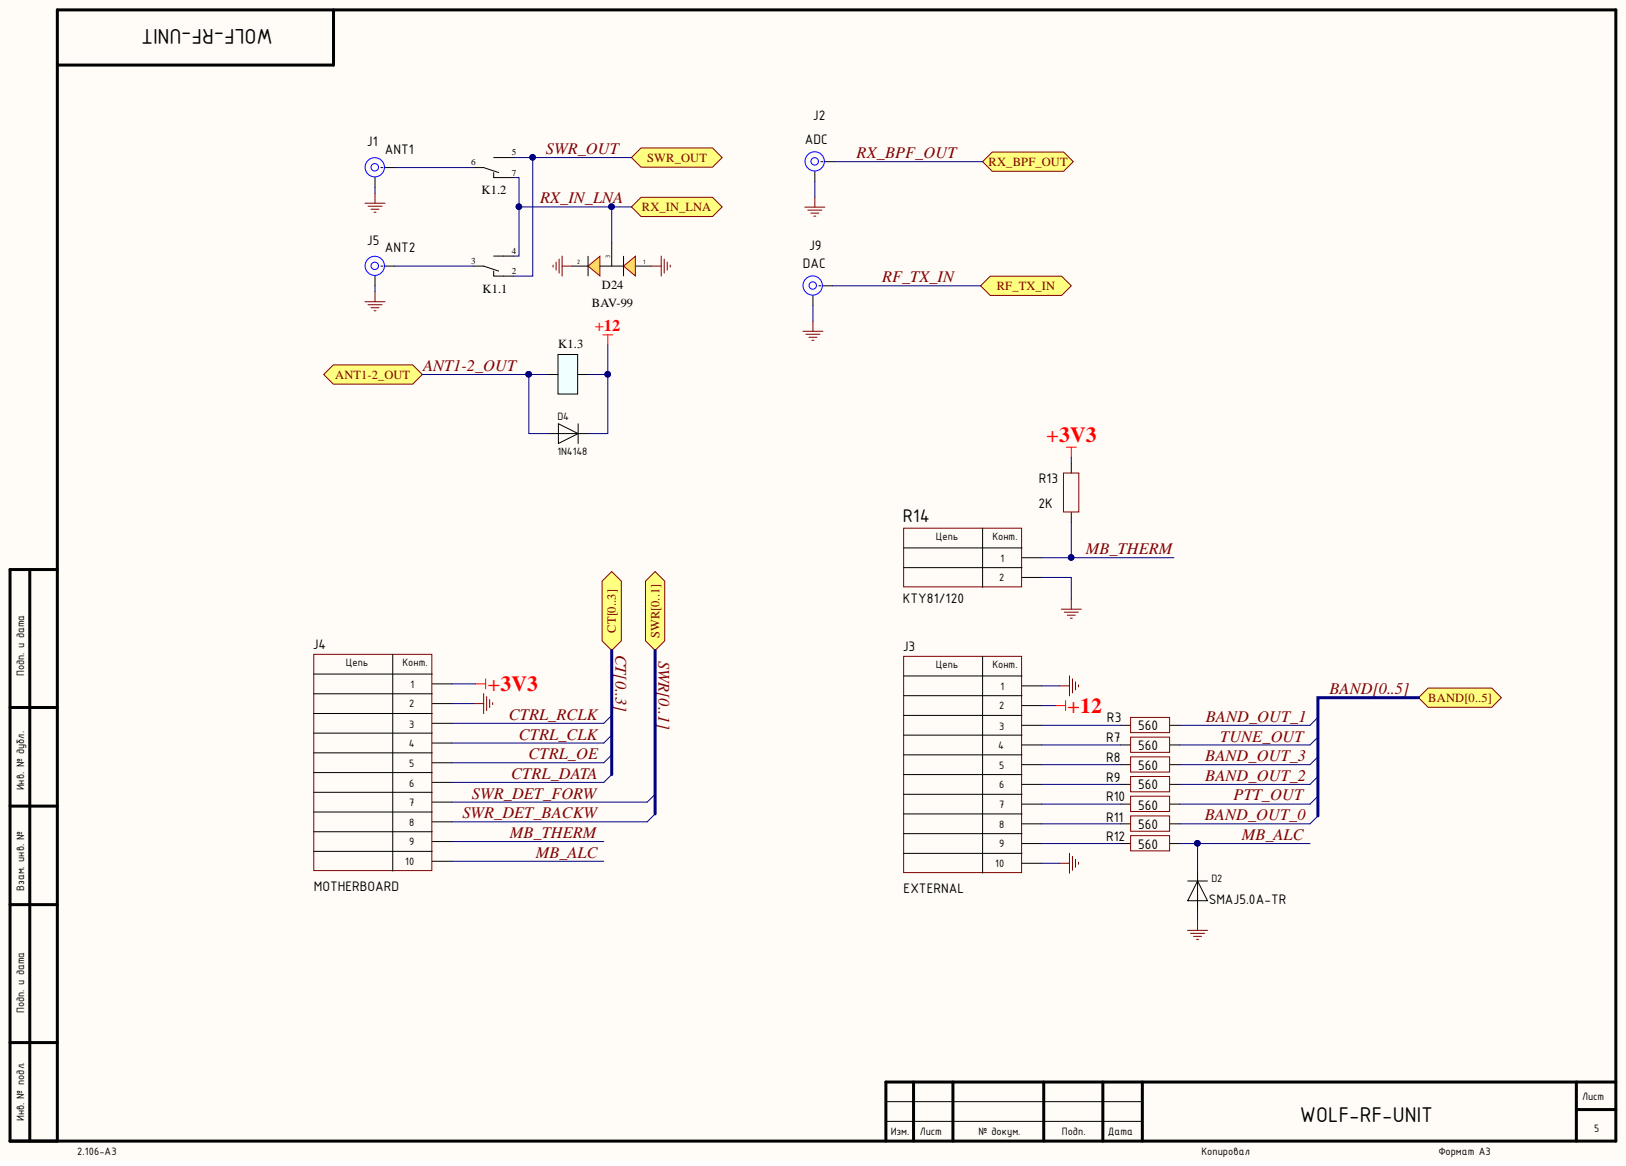
[picture p142: page 5]

Цепь | Конт .

Инв. № подл. Инв. № дубл. Подп. и дата Взам. инв. № Подп. и дата

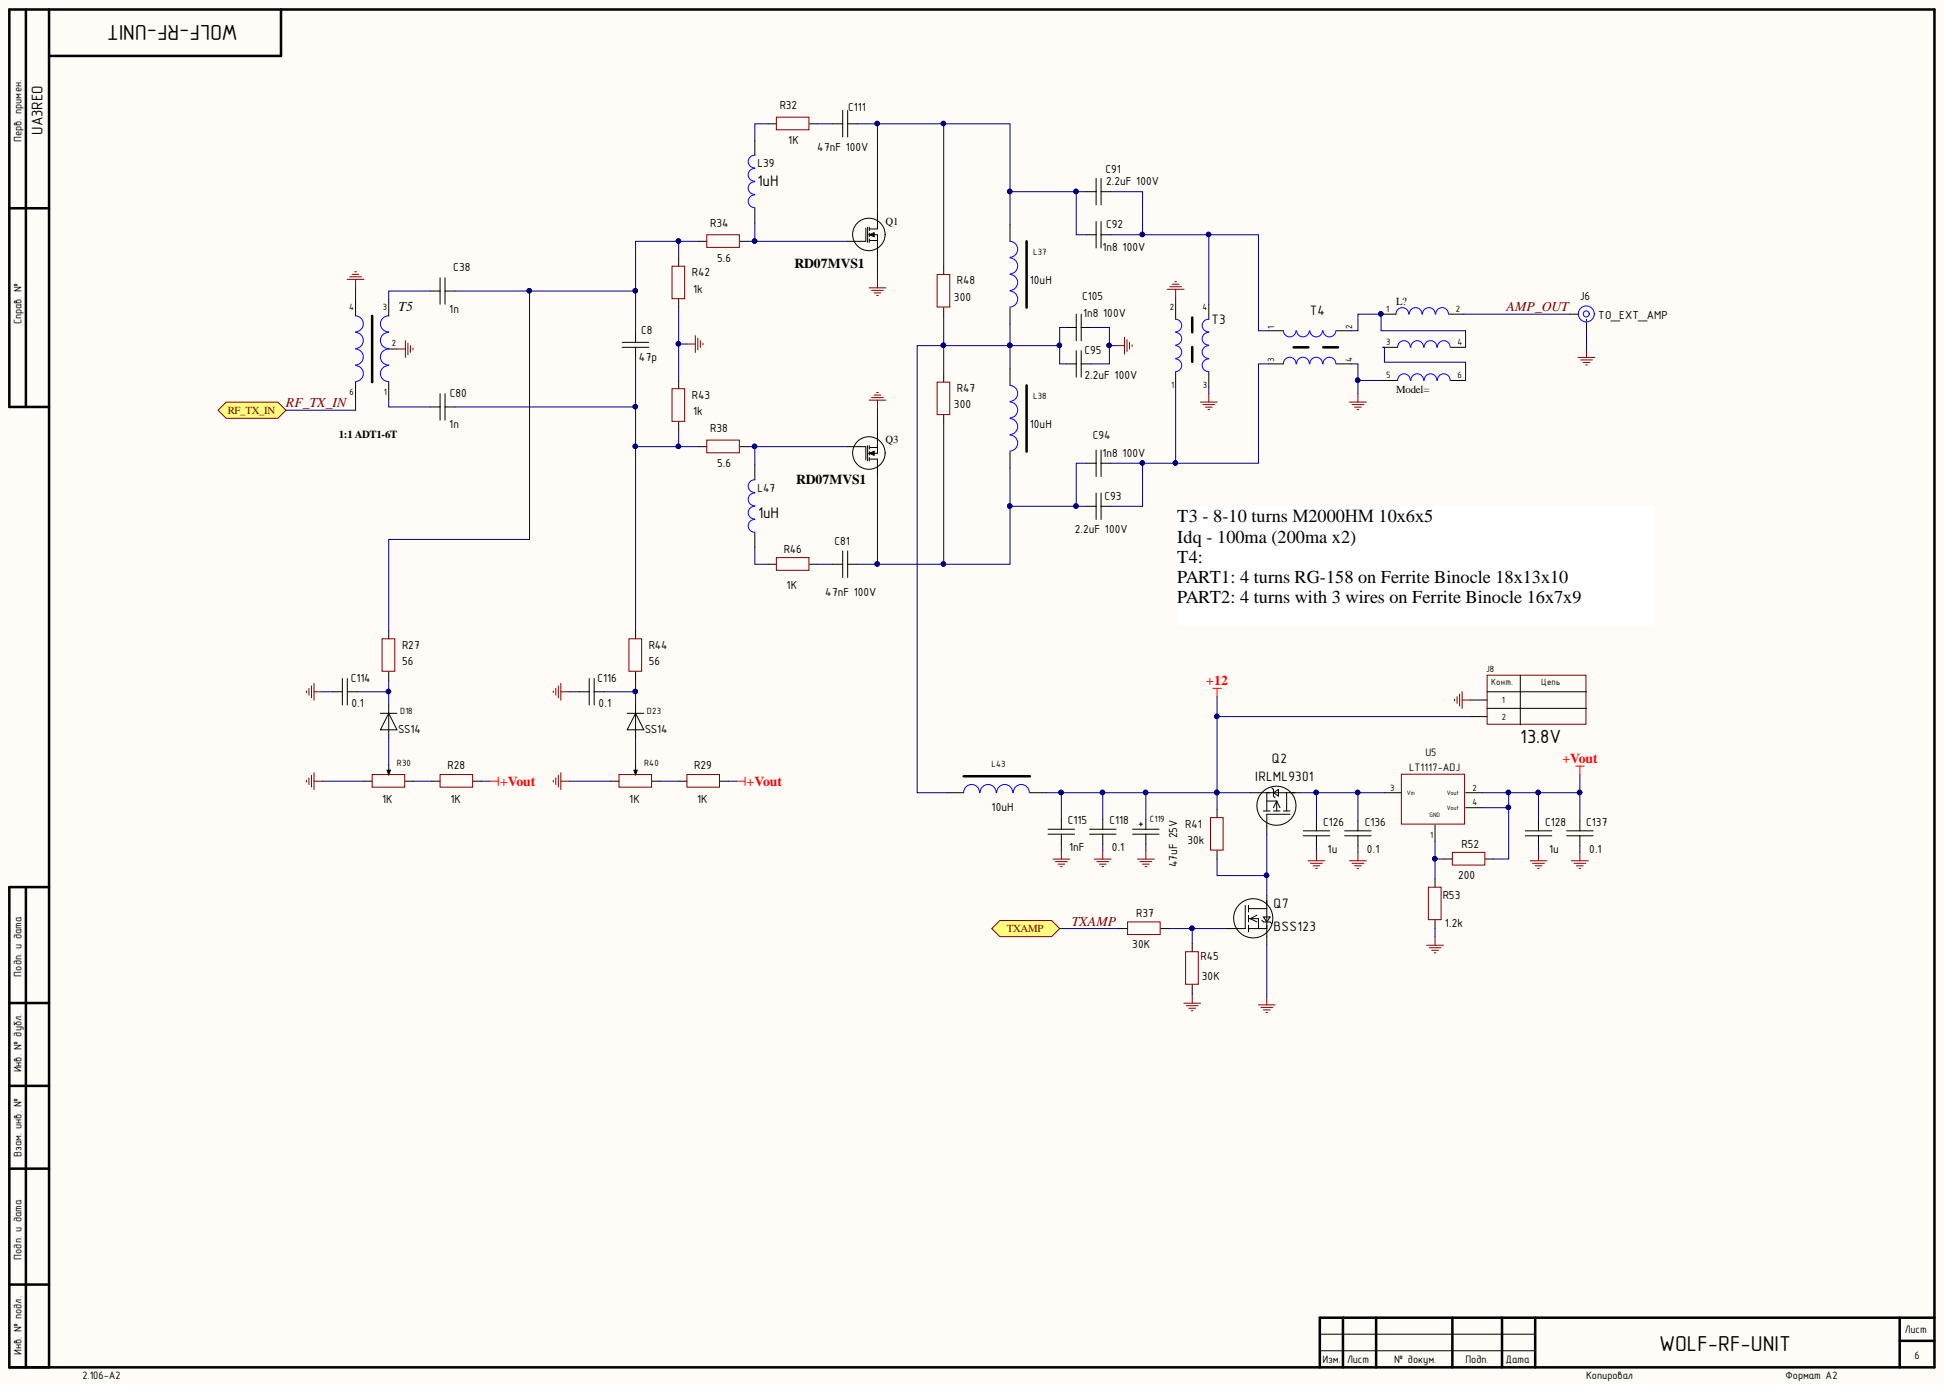
[picture p143: page 6]

Инв. № подл. Инв. № дубл. Подп. и дата Взам. инв. № Подп. и дата Перв. примен. Справ. №

T3 - 8-10 turns М2000НМ 10х6х5
Idq - 100ma (200ma x2)
PART1: 4 turns RG-158 on Ferrite Binocle 18х13x10
PART2: 4 turns with 3 wires on Ferrite Binocle 16x7x9

Конт. | Цепь

Лист | № докум. | Подп. | Дата | WOLF-RF-UNIT Изм.

Лист

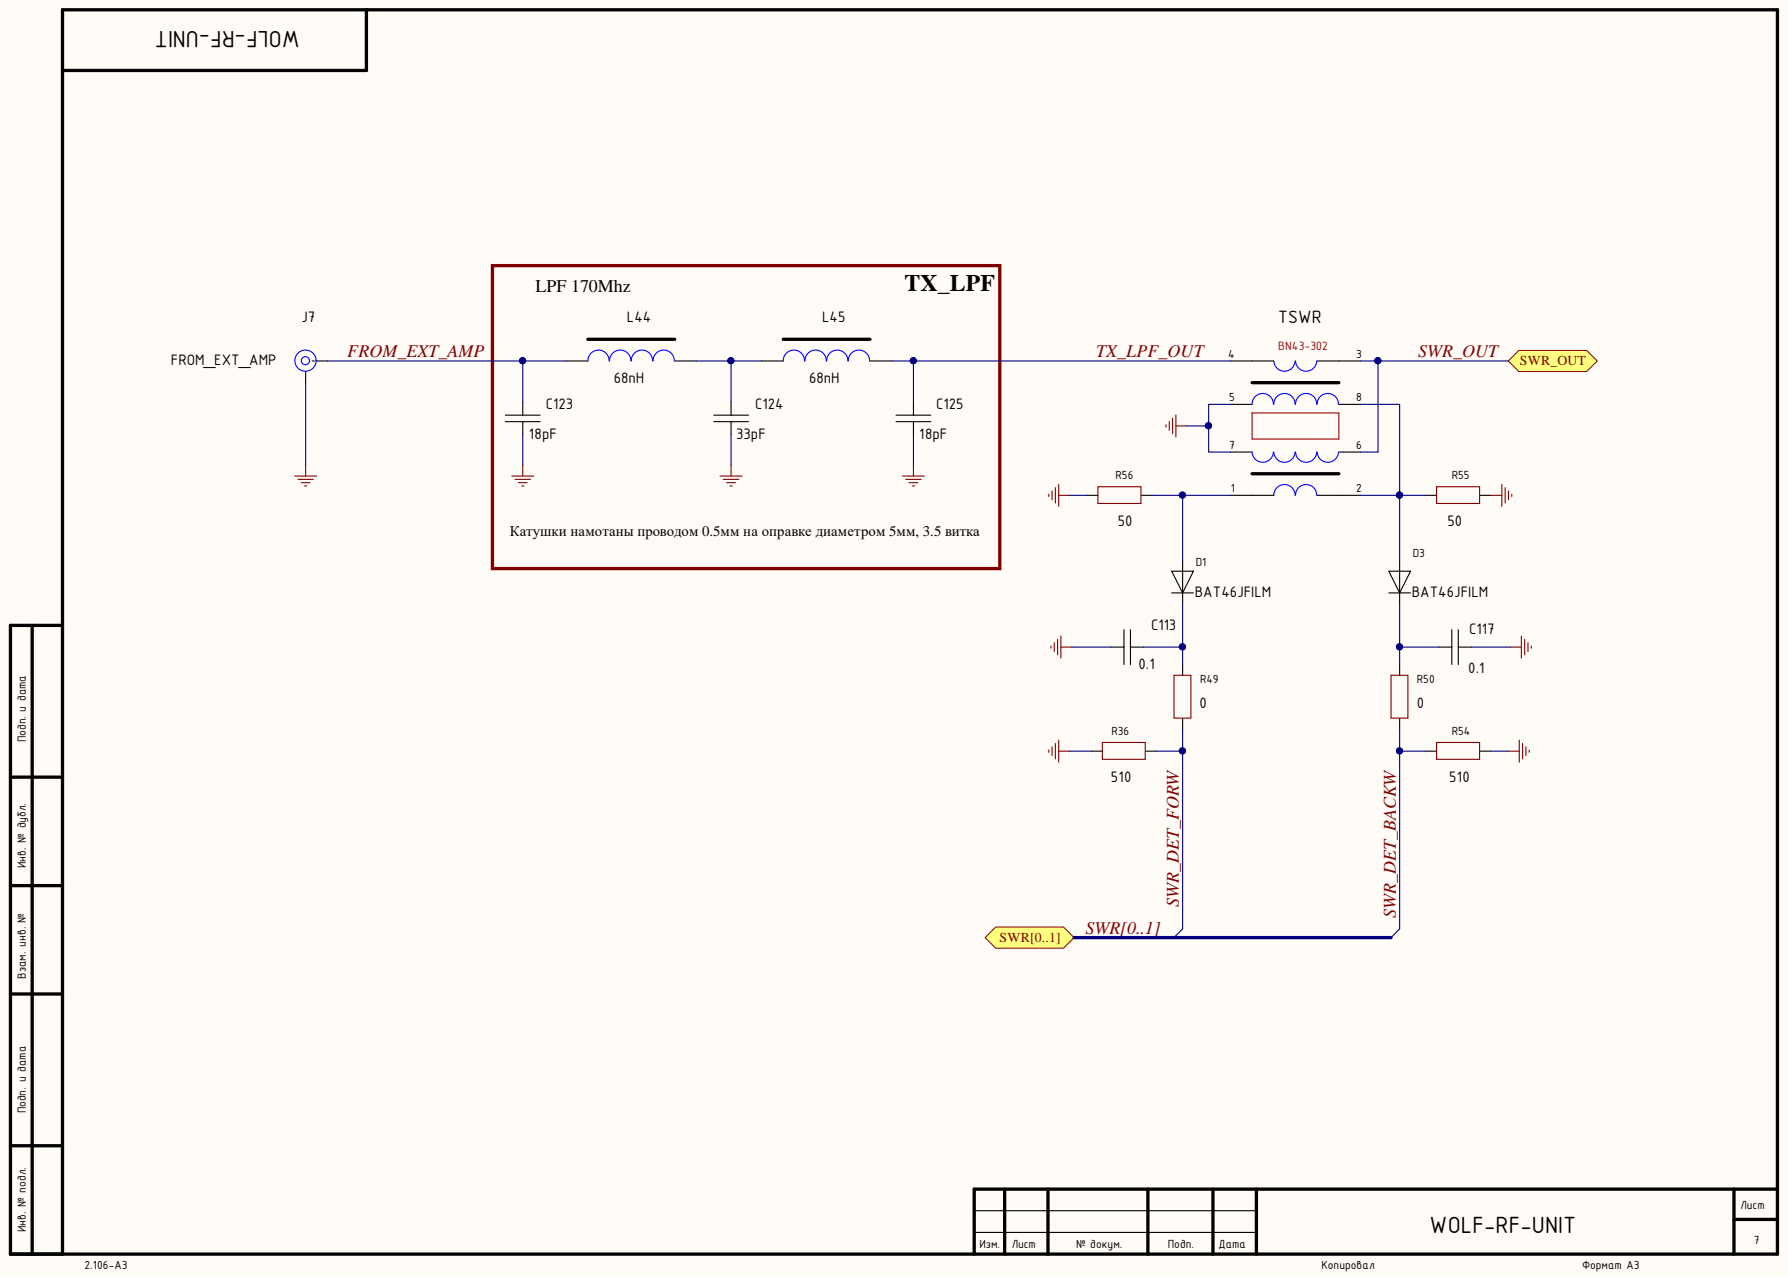
[picture p144: page 7]

Катушки намотаны проводом 0.5мм на оправке диаметром 5мм, 3.5 витка

Инв. № подл. Инв. № дубл. Подп. и дата Взам. инв. № Подп. и дата

Comment | Description | Designator | Footprint | LibRef | Quantity
0.1u | | C1, C2, C3, C4, C141, C142 | CH0201C | Capacitor | 6
47pF | | C5, C13 | CH0805C | Capacitor | 2
33pF | | C6, C124 | CH0805C | Capacitor | 2
39pF | | C7 | CH0805C | Capacitor | 1
47p | | C8 | CH0805C | Capacitor | 1
75pF | | C11 | CH0805C | Capacitor | 1
61pF | | C12 | CH0805C | Capacitor | 1
100pF | | C14, C22 | CH0805C | Capacitor | 2
120pF | | C15, C21 | CH0805C | Capacitor | 2
150pF | | C20 | CH0805C | Capacitor | 1
330pF | | C23, C44, C46 | CH0805C | Capacitor | 3
270pF | | C24, C32, C45, C46 | CH0805C | Capacitor | 4
180pF | | C33, C34 | CH0805C | Capacitor | 2
560pF | | C35, C59 | CH0805C | Capacitor | 2
470pF | | C36, C60 | CH0805C | Capacitor | 2
1n | | C38, C80, C122 | CH0805C | Capacitor | 3
1nF | | C47, C48, C72, C115 | CH0805C | Capacitor | 4
820pF | | C58 | CH0805C | Capacitor | 1
1.5nF | | C61 | CH0805C | Capacitor | 1
1.2nF | | C62, C74 | CH0805C | Capacitor | 2
3.3nF | | C75, C76 | CH0805C | Capacitor | 2
47nF 100V | | C81, C111 | CH0805C | Capacitor | 2
6.5-30pF | | C86, C87 | CH0805C | Capacitor | 2
120p | | C88, C90 | CH0805C | Capacitor | 2
100p | | C89, C127, C132 | CH0805C | Capacitor | 3
2.2uF 100V | | C91, C93, C95 | CH0805C | Capacitor | 3
1n8 100V | | C92, C94, C105 | CH0805C | Capacitor | 3
39p | | C101, C102, C103 | CH0805C | Capacitor | 3
27p | | C104 | CH0805C | Capacitor | 1
51p | | C107, C108, C109, C112, C120 | CH0805C | Capacitor | 5
0.1 | | C113, C114, C116, C117, C118, C130, C131, C133, C136, C137 | CH0805C | Capacitor | 10
47uF 25V | | C119 | TANTAL_B | TantalCap | 1
10n | | C121 | CH0805C | Capacitor | 1
18pF | | C123, C125 | CH0805C | Capacitor | 2
1u | | C126, C128 | CH0805C | Capacitor | 2
10uF 25V | | C129 | TANTAL_B | TantalCap | 1
0.1u | | C134, C135, C139, C140 | CH0805C | Capacitor | 4
BAT46JFILM | | D1, D3 | D9B | Diod | 2
SMAJ5.0A-TR | | D2 | SOD123 | Diod | 1
1N4148 | | D4 | SOD123 | Diod | 1
SS14 | | D18, D23 | SOD123 | Diod | 2
BAV-99 | | D24 | SOT23_132 | BAV-99 | 1
ANT1 | RF | J1 | CON: SMA | SMA | 1
ADC | RF | J2 | CON: SMA | SMA | 1
EXTERNAL | | J3 | CON: 0533751010 | 10-Connector | 1
MOTHERBOARD | | J4 | CON: 0533751010 | 10-Connector | 1
ANT2 | RF | J5 | CON: SMA | SMA | 1
TO_EXT_AMP | RF | J6 | CON: SMA | SMA | 1
FROM_EXT_AMP | RF | J7 | CON: SMA | SMA | 1
13.8V | | J8 | CON: 300-02P-5.0 | 2-Connector | 1
DAC | RF | J9 | CON: SMA | SMA | 1
IM06 | | K1 | IMG06 | IM06-1 | 1
270nH | | L1, L7 | L1210 | TRANS | 2
82nH | | L2 | L1210 | TRANS | 1
100nH | | L3 | L1210 | TRANS | 1
470nH | | L4, L15 | L1210 | TRANS | 2
150nH | | L5, L6 | L1210 | TRANS | 2
330nH | | L8, L10, L11 | L1210 | TRANS | 3
1uH | | L9, L17 | L1210 | TRANS | 2
560nH | | L12, L16 | L1210 | TRANS | 2
820nH | | L13, L21 | L1210 | TRANS | 2
1.5uH | | L14, L18, L25 | L1210 | TRANS | 3
1.8uH | | L19, L26 | L1210 | TRANS | 2
680nH | | L20 | L1210 | TRANS | 1
2.2uH | | L22, L30, L31 | L1210 | TRANS | 3
2.7uH | | L23, L27 | L1210 | TRANS | 2
4.7uH | | L24 | L1210 | TRANS | 1
3.3uH | | L28 | L1210 | TRANS | 1
5.6uH | | L29 | L1210 | TRANS | 1
6.8uH | | L32 | L1210 | TRANS | 1
8.2uH | | L33 | L1210 | TRANS | 1
8.2nH | | L34, L35, L36 | L1210 | TRANS | 3
10uH | | L37, L38, L43 | | TRANS | 3
1uH | | L39, L47 | IND: R24 | Inductor ring | 2
100nH | | L40, L41, L42 | IND: R24 | Inductor ring | 3
68nH | | L44, L45 | | TRANS | 2
220nH | | L46 | IND: R24 | Inductor ring | 1
Model= | | L? | | Inductor-3 | 1
RD07MVS1 | | Q1, Q3 | RD07 | N | 2
IRLML9301 | | Q2, Q5 | D2PAK_132 | P-KANAL | 2
PGA-103+ | | Q4, Q5 | SOT23_132 | N-KANAL | 2
BSS123 | | Q7, Q8 | SOT23_132 | N-KANAL | 2
560 | | R3, R7, R8, R9, R10, R11, R12 | CH0805R | Resistor | 7
2K | | R13 | CH0805R | Resistor | 1
KTY81/120 | | R14 | CON: CWF-2 | 2-Connector | 1
56 | | R27, R44 | CH0805R | Resistor | 2
1K | | R28, R29, R32, R35, R42, R43, R46, R65, R71, R72, R73, R74, R75, R76, R77, R78, R79, R80, R81, R82, R83, R84, R85 | CH0805R | Resistor | 23
1K | | R30, R40 | RES: 3296W | ADJ resistor | 2
30k | | R31, R33, R37, R41, R45, R57, R70 | CH0805R | Resistor | 7
5.6 | | R34, R38 | CH0805R | Resistor | 2
510 | | R36, R54 | CH1206R | Resistor | 2
18 | | R39 | CH0805R | Resistor | 1
300 | | R47, R48 | CH0805R | Resistor | 2
0 | | R49, R50 | CH1206R | Resistor | 2
200 | | R52 | CH0805R | Resistor | 1
1.2k | | R53 | CH0805R | Resistor | 1
50 | | R55, R56 | CH1206R | Resistor | 2
BN-43-302 | | T3, T4 | | BN-43-302 | 2
1:1 ADT1-6T | | T5 | TC1-4 | TC4-1 | 1
BN43-302 | | TSWR | TANDEM | BN43-302 | 1
SN74HC595D | | U1, U3, U7 | 16-SOIC | SN74HC595D | 3
ULN2003BDR | | U2 | 16-SOIC | ULN2003BDR_1 | 1
ADG904BRUZ-R | | U4, U15, U16, U17 | 20-SOIC (W) | ADG904BRUZ-R | 4
LT1117-ADJ | | U5 | SOT223 | AMS117 | 1
AMS1117-5 | | U6 | SOT223 | AMS117 | 1
ADG918BRMZ | | U8, U10, U11, U12, U13, U14 | 8-MSOP (NO PAD) | ADG918BRMZ | 6
PE4302 | | U9 | | PE4302 | 1
FAN_OUT | | X? | CON: 300-02P-5.0 | 2-Connector | 1
