hristoandreev/UA3REO-DDC-Transceiver/Schematic/Wolf/Altium_Designer/RF-UNIT-QRP_20W/!AdditionalInfo/Heatsink_QRP++.pdf

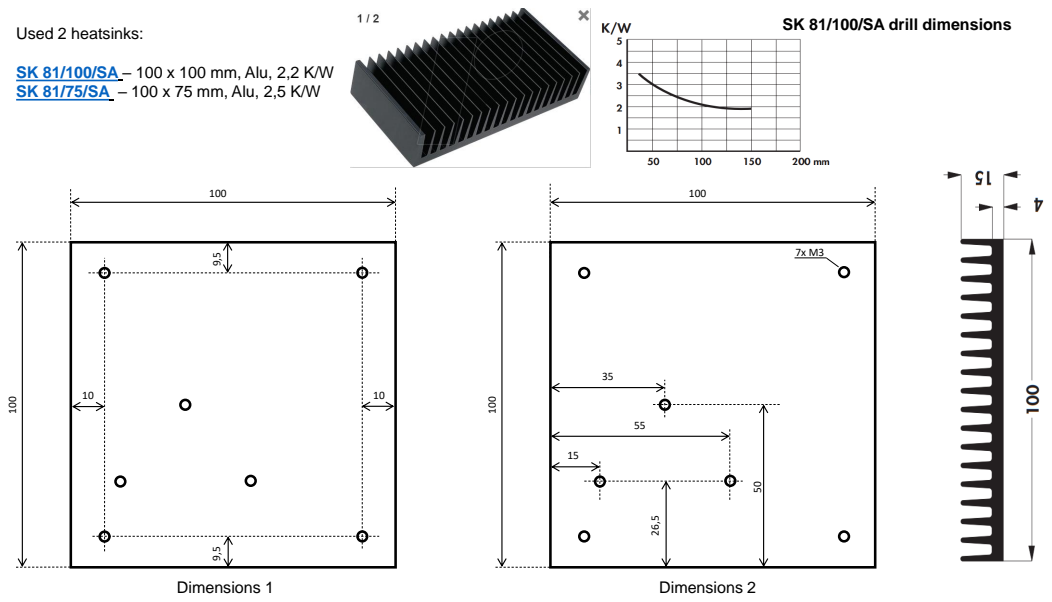
[picture p147: page 1]
Used 2 heatsinks:; Dimensions 1; Dimensions 2

SK 81/100/SA drill dimensions

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

SK 81/75/SA drill dimensions

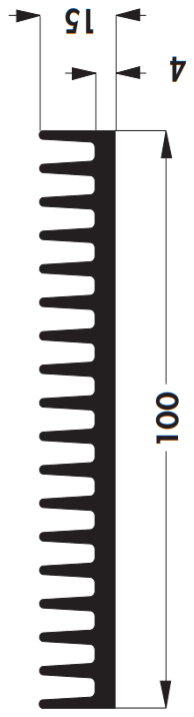
[picture p148: figure]
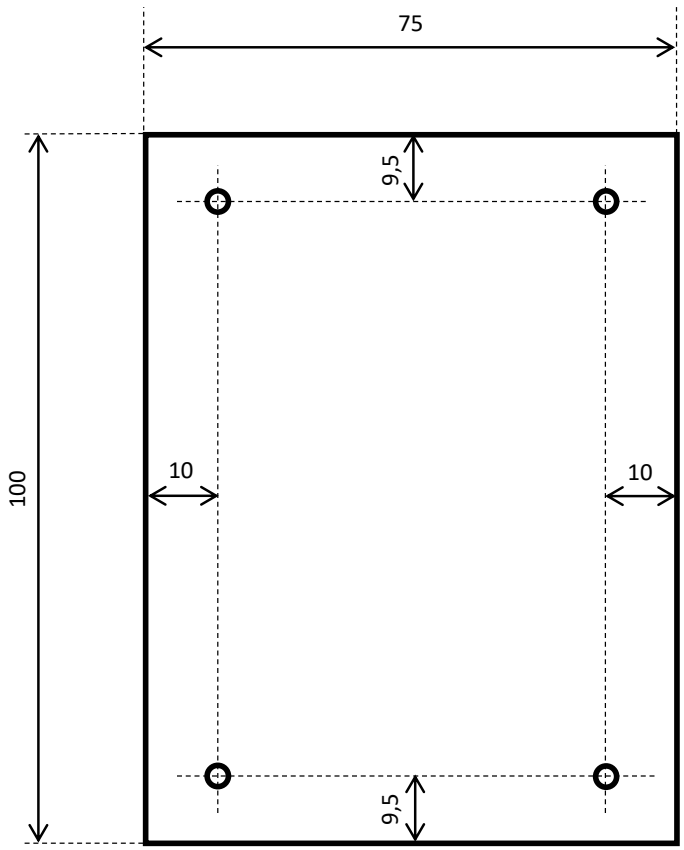
[picture p149: figure]
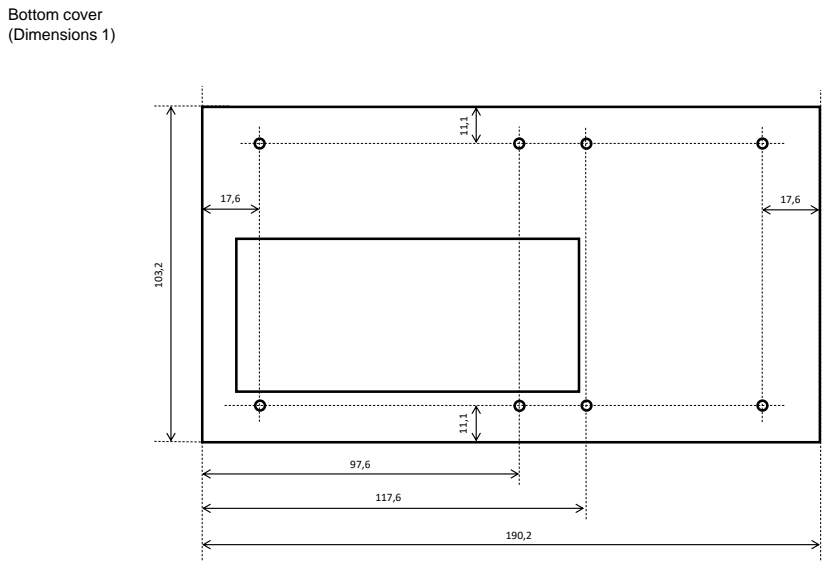
[picture p150: page 3]
Bottom cover (Dimensions 1)

Bottom cover
(Dimensions 2)

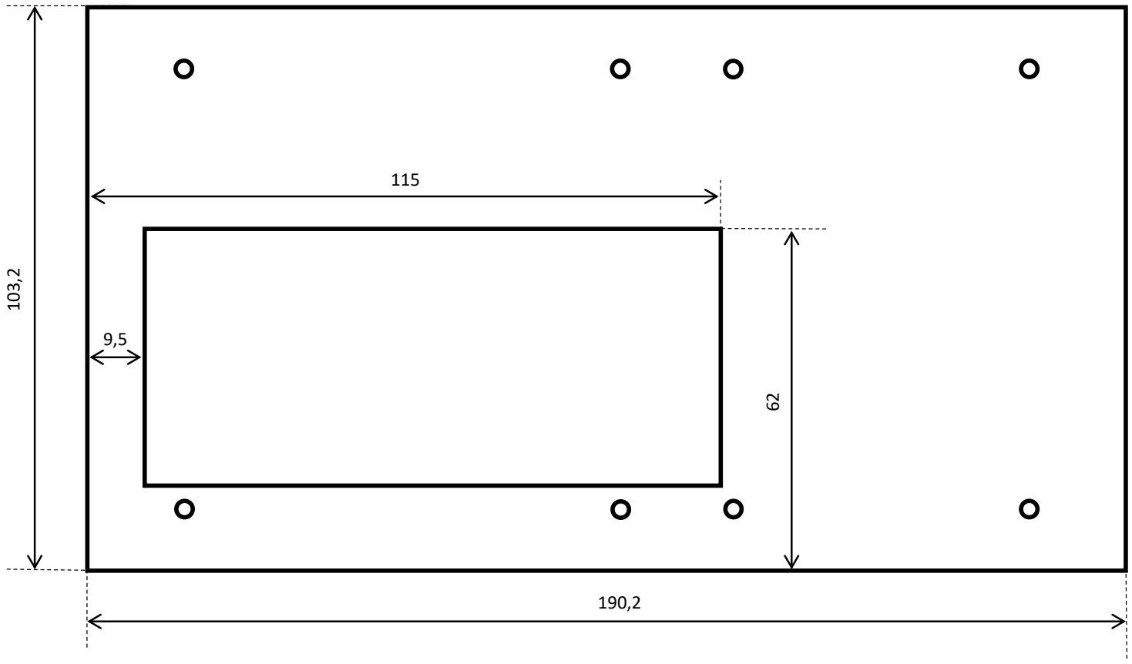
[picture p151: figure]
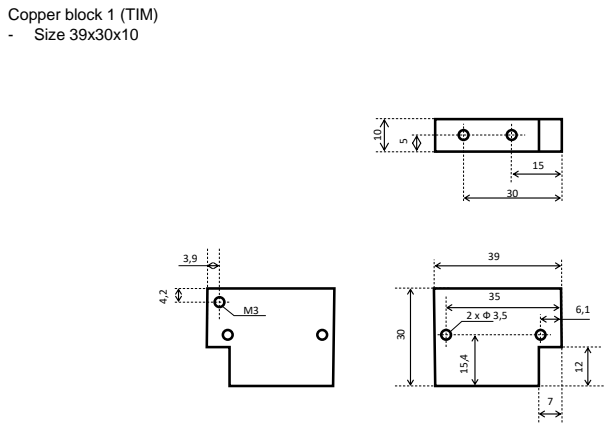
[picture p152: page 5]

Copper block 1 (TIM)
- Size 39x30x10

Copper block 1 (TIM)
- Size 39x20x8

8

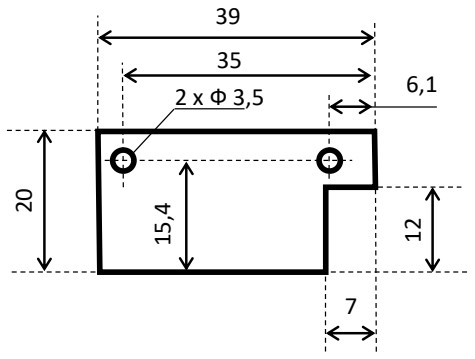
[picture p153: figure]
