hristoandreev/UA3REO-DDC-Transceiver/Schematic/Wolf-X1/Scheme/X1_PA_V0.4.pdf

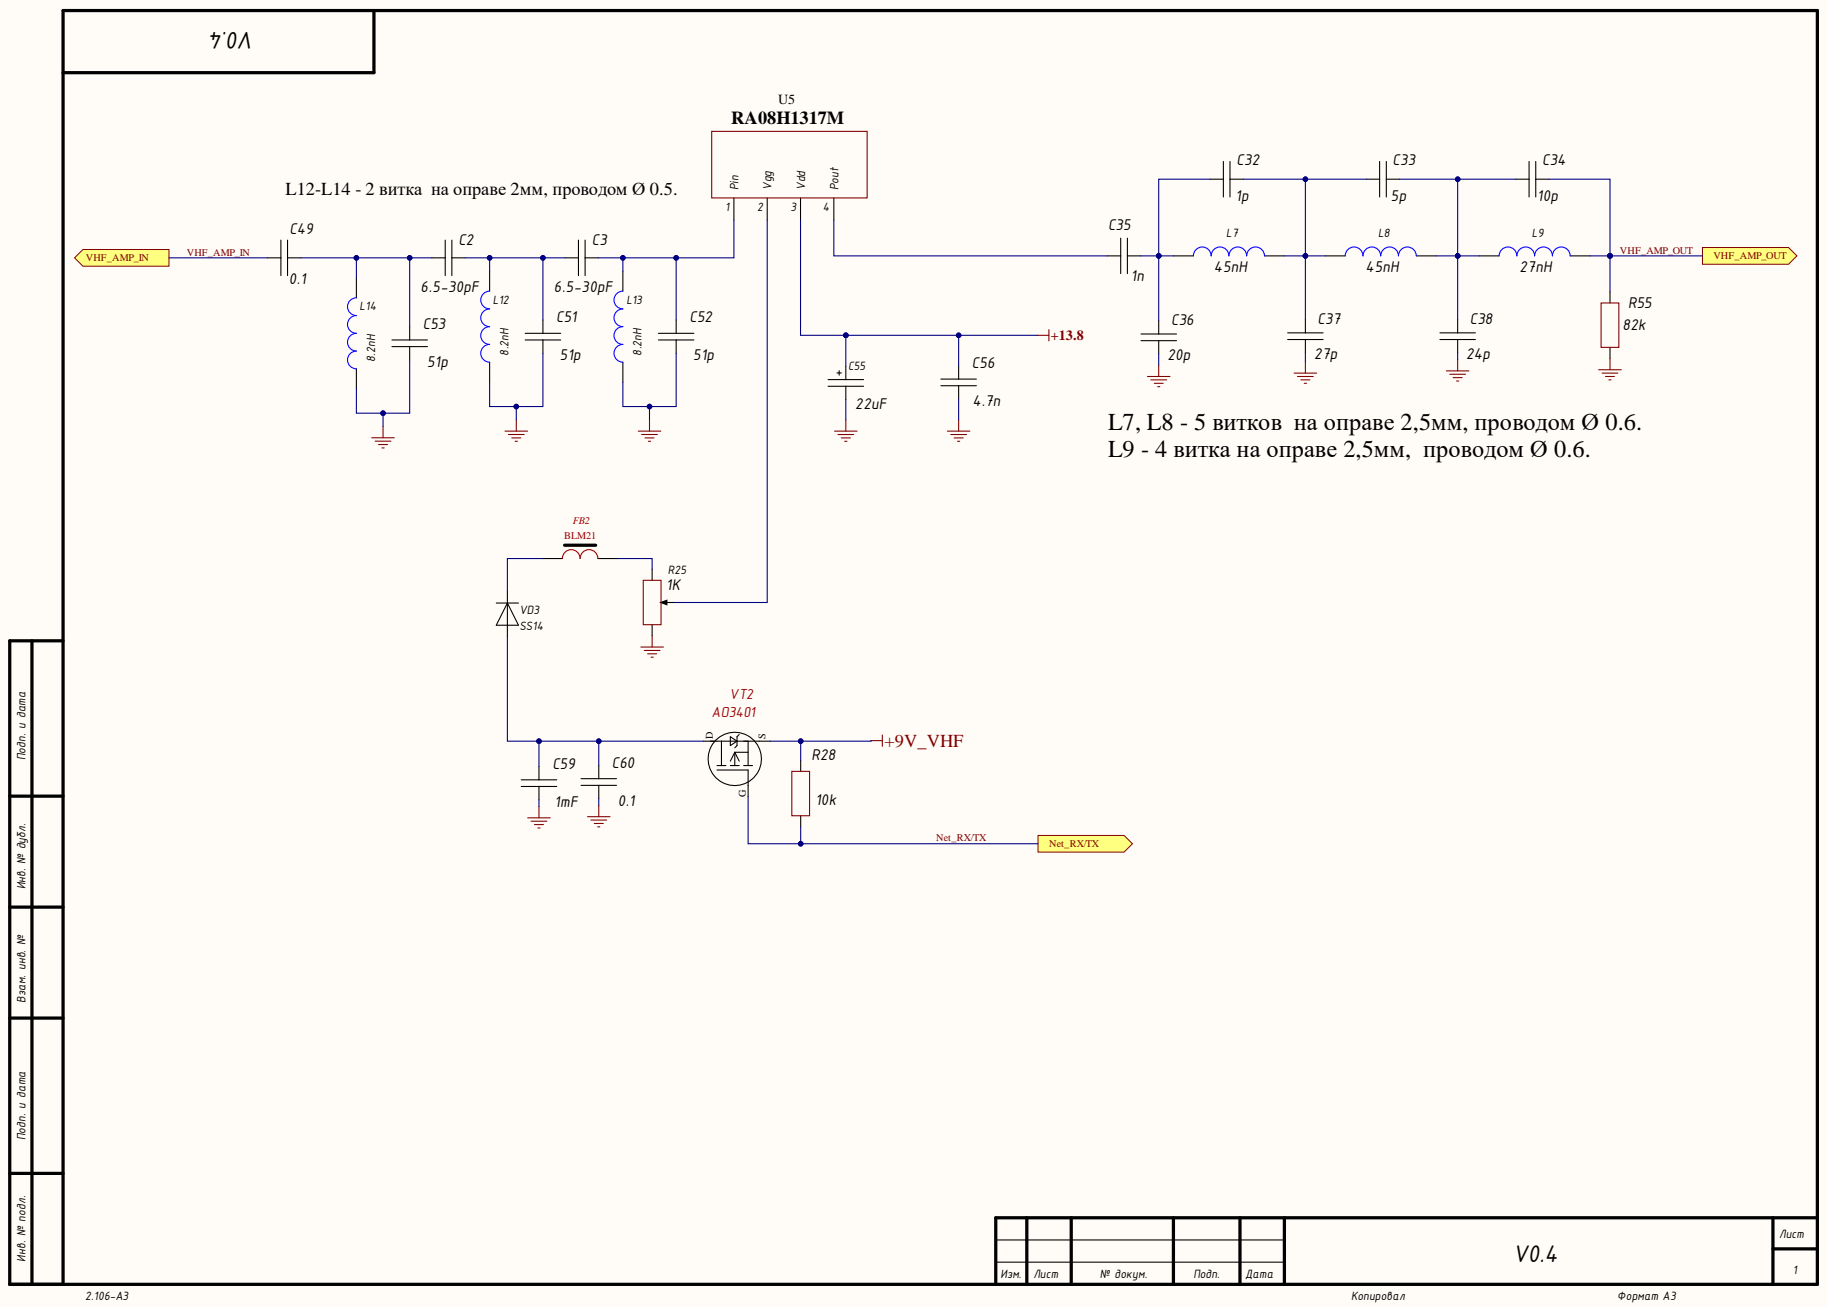
[picture p178: page 1]

L12-L14 - 2 витка на оправе 2мм, проводом Ø 0.5.

L7, L8 - 5 витков на оправе 2,5мм, проводом Ø 0.6.
L9 - 4 витка на оправе 2,5мм, проводом Ø 0.6.

Инв. № подл. Инв. № дубл. Подп. и дата Взам. инв. № Подп. и дата

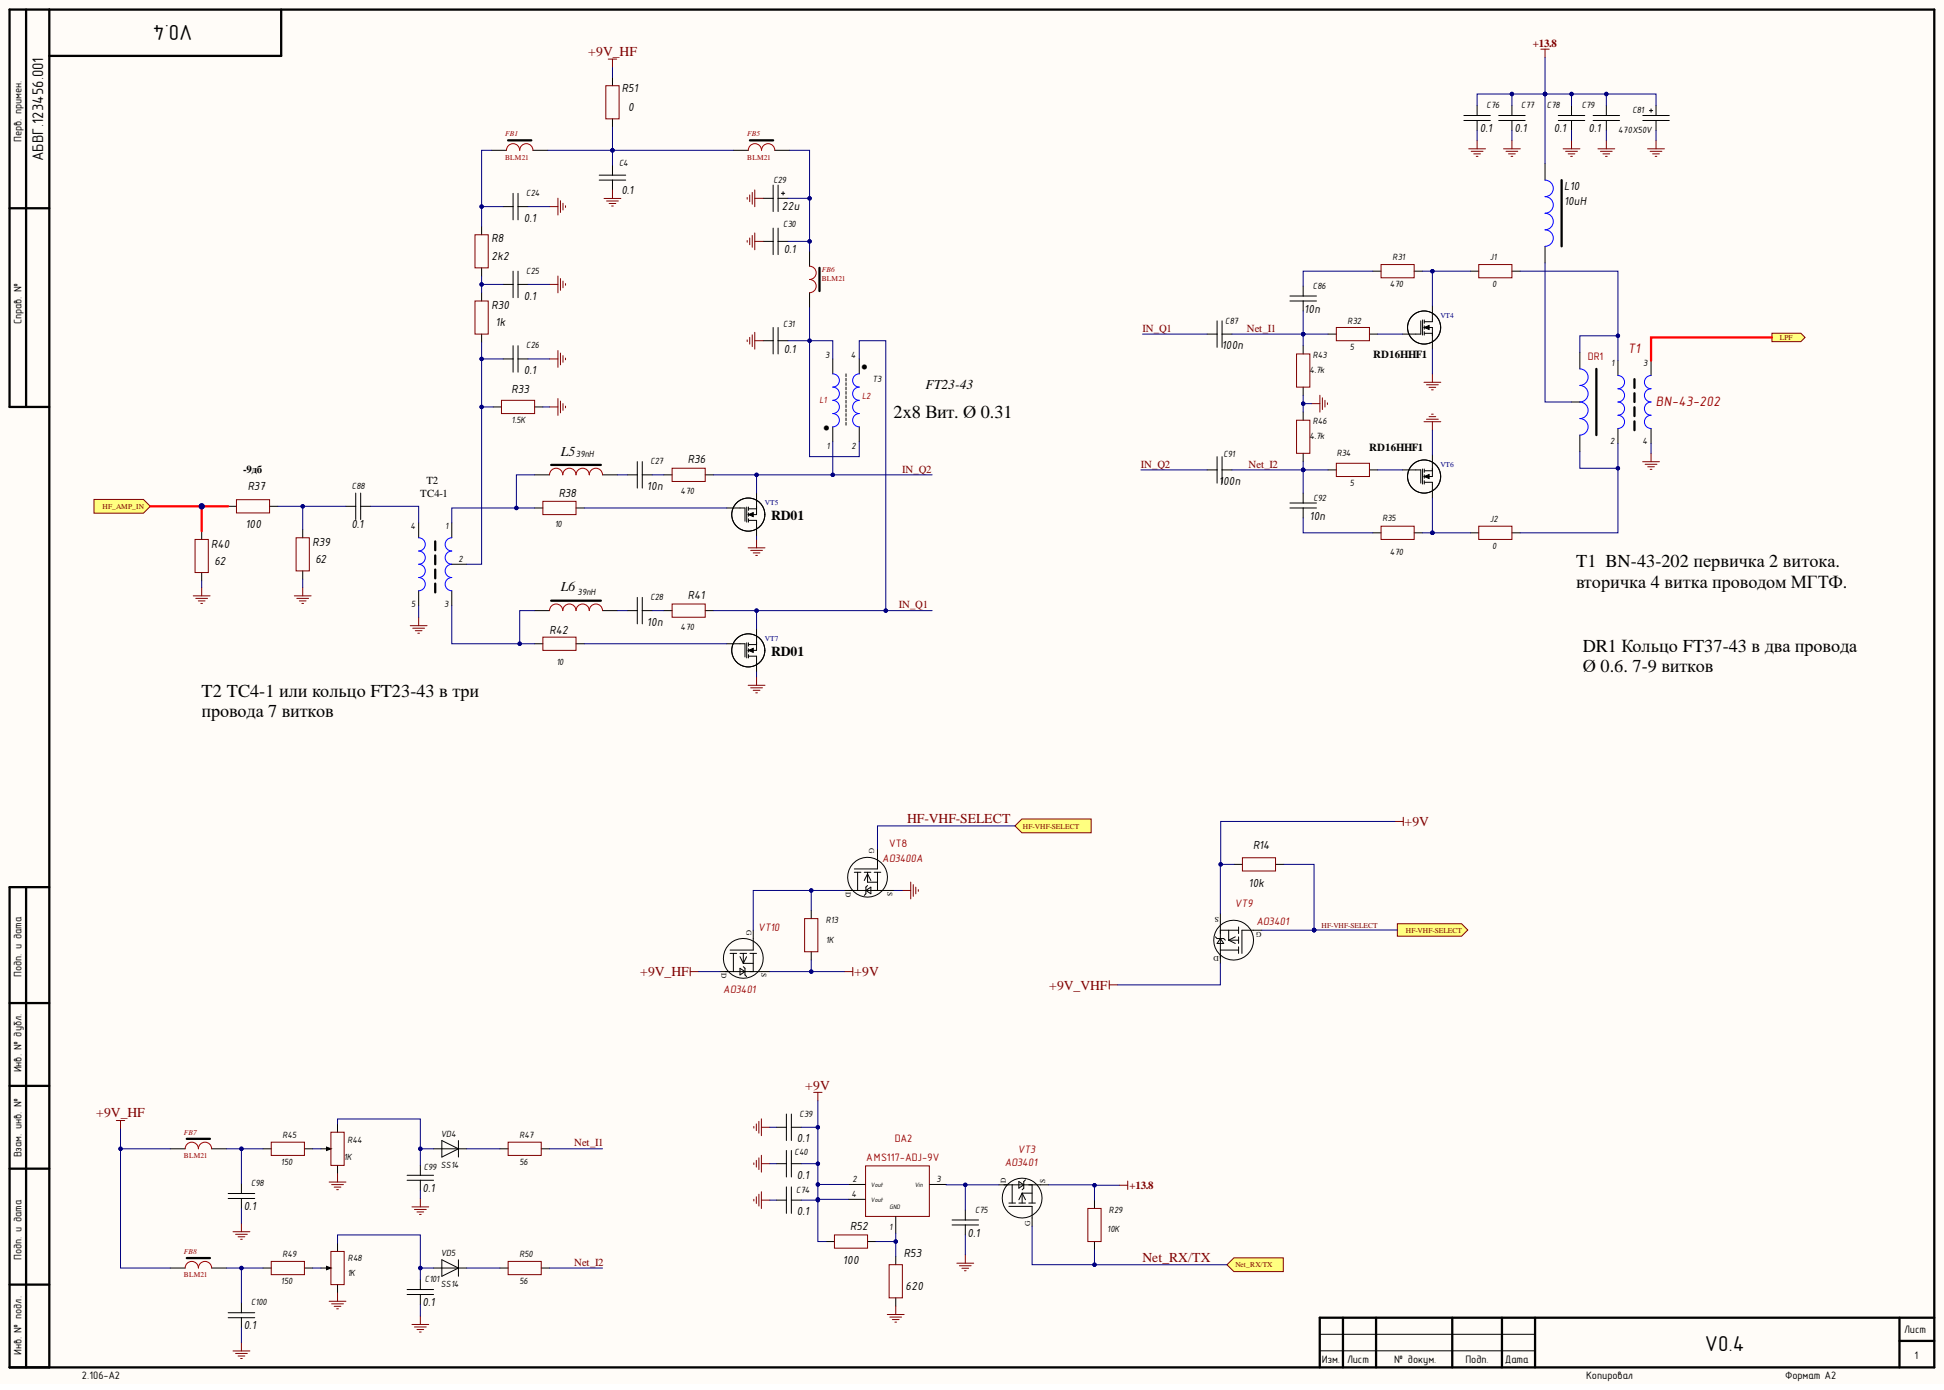
[picture p179: page 2]

Инв. № подл. Инв. № дубл. Подп. и дата Взам. инв. № Подп. и дата Перв. примен. Справ. №

T1 BN-43-202 первичка 2 витока.
вторичка 4 витка проводом МГТФ.

HF-VHF-SELECT

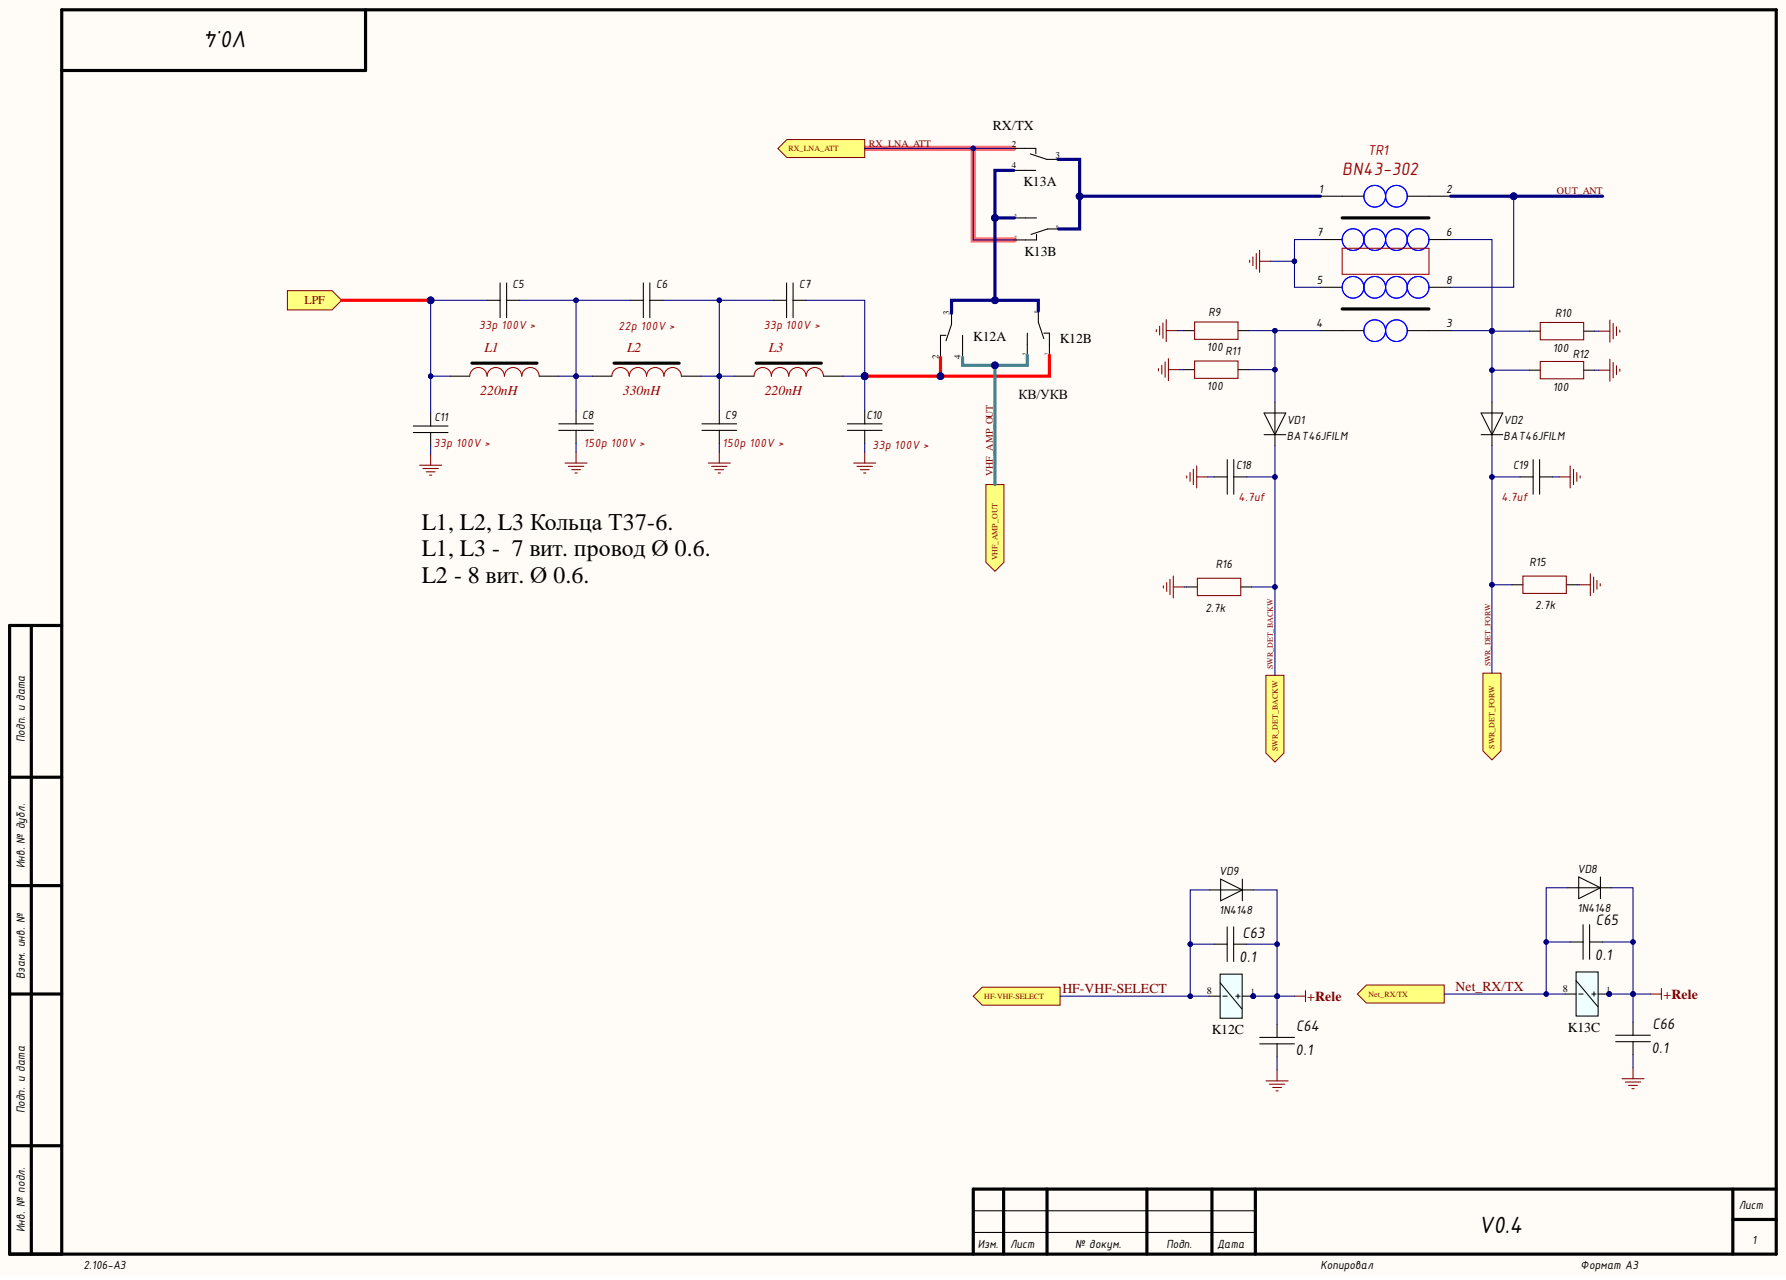
[picture p180: page 3]

Инв. № подл. Инв. № дубл. Подп. и дата Взам. инв. № Подп. и дата

+Rele HF-VHF-SELECT

Изм. | Лист | № докум. | Подп. | Дата

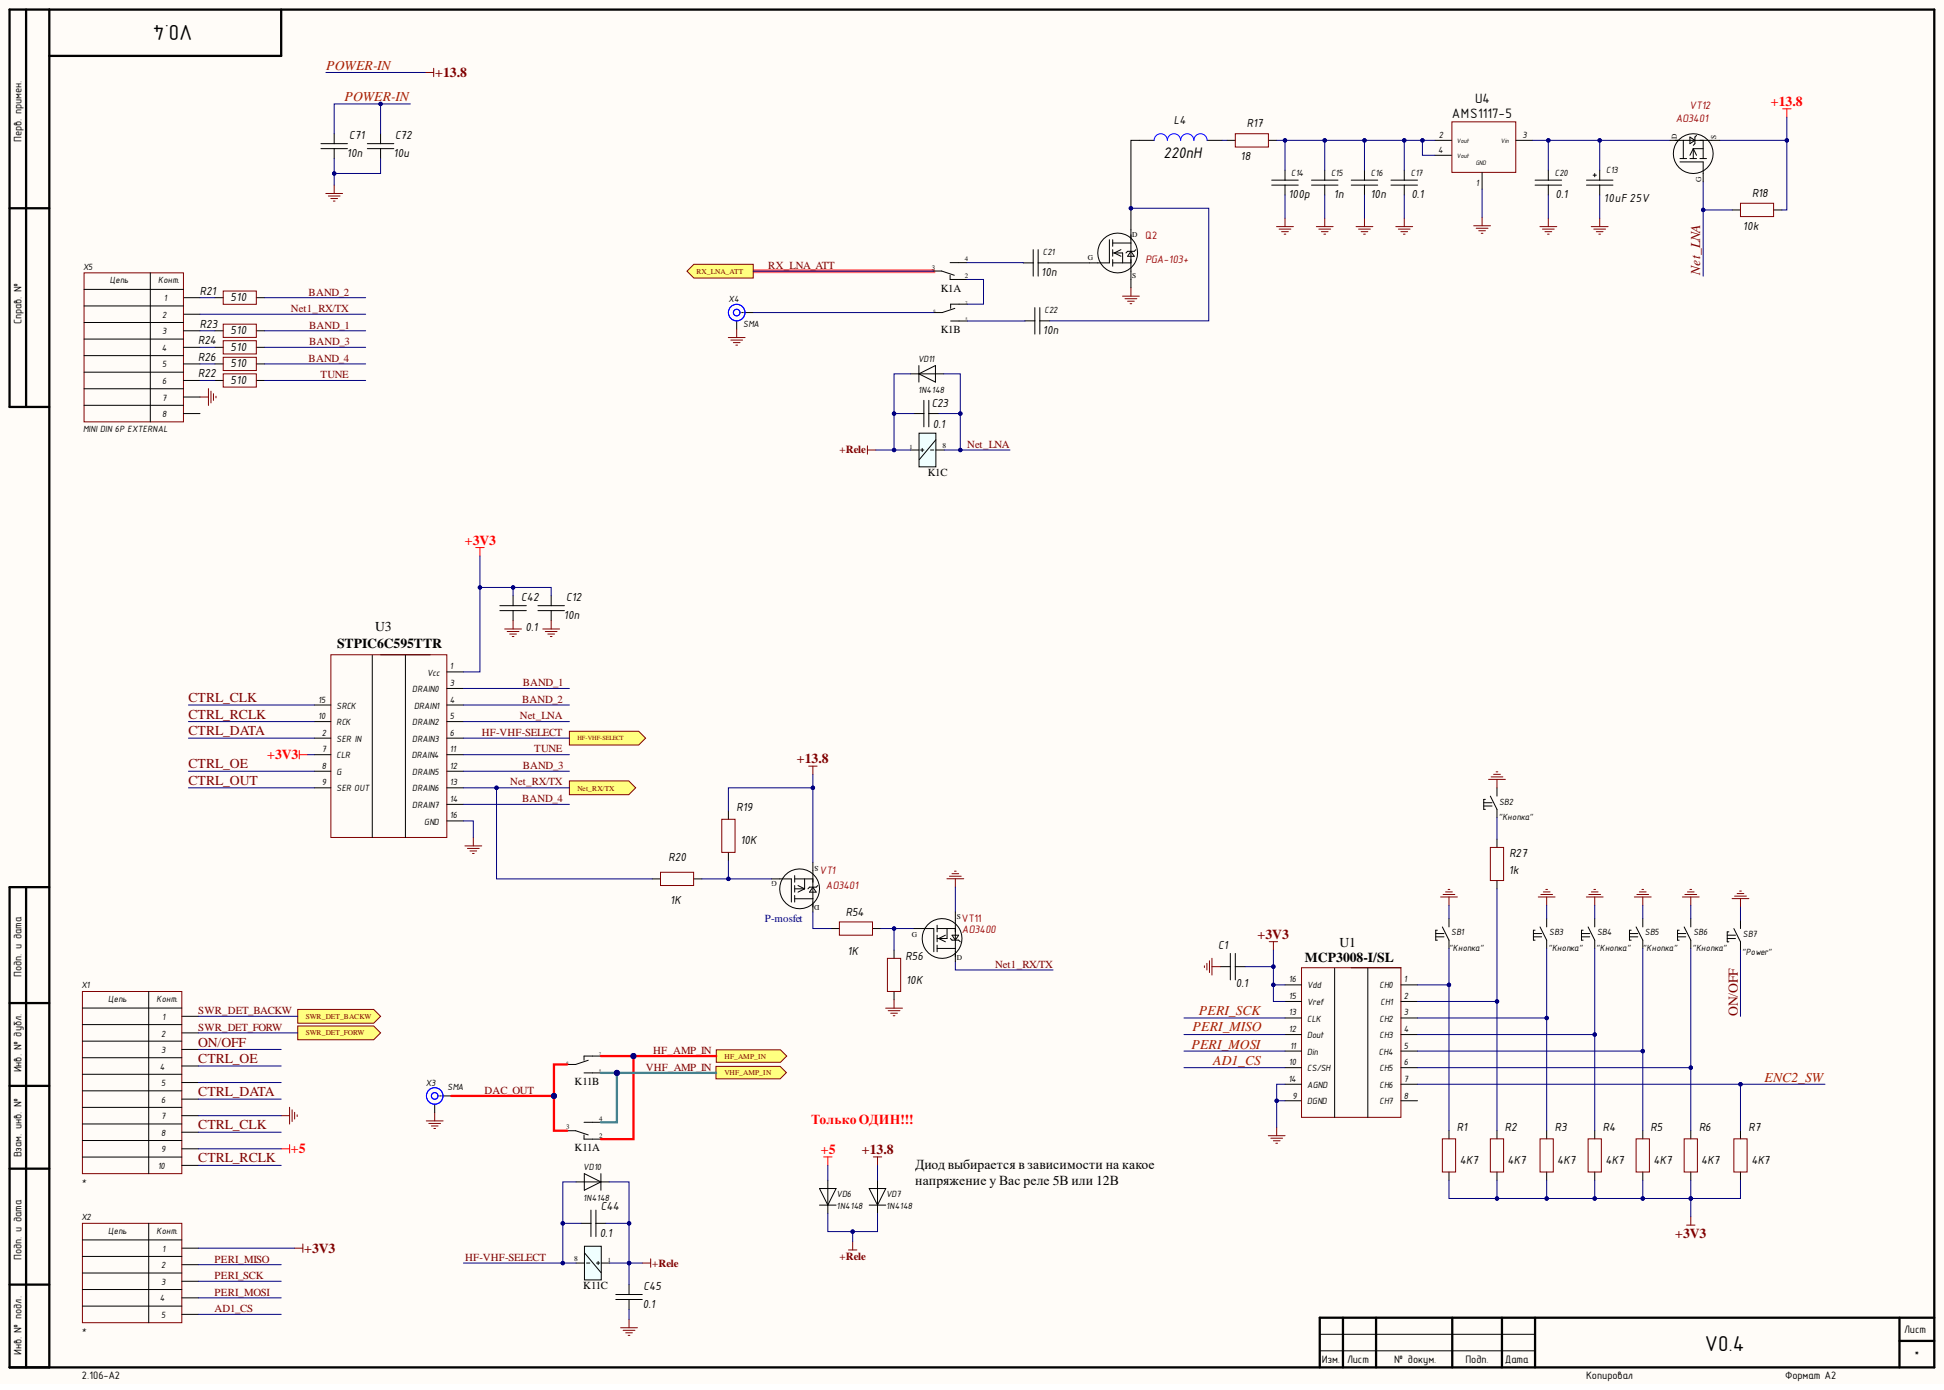
[picture p181: page 4]

Инв. № подл. Инв. № дубл. Подп. и дата Взам. инв. № Подп. и дата Перв. примен. Справ. №

Цепь | Конт.

Диод выбирается в зависимости на какое
напряжение у Вас реле 5В или 12В
