hristoandreev/UA3REO-DDC-Transceiver/Schematic/Wolf/Addons/R7KBI/MOTHERBOARD.pdf

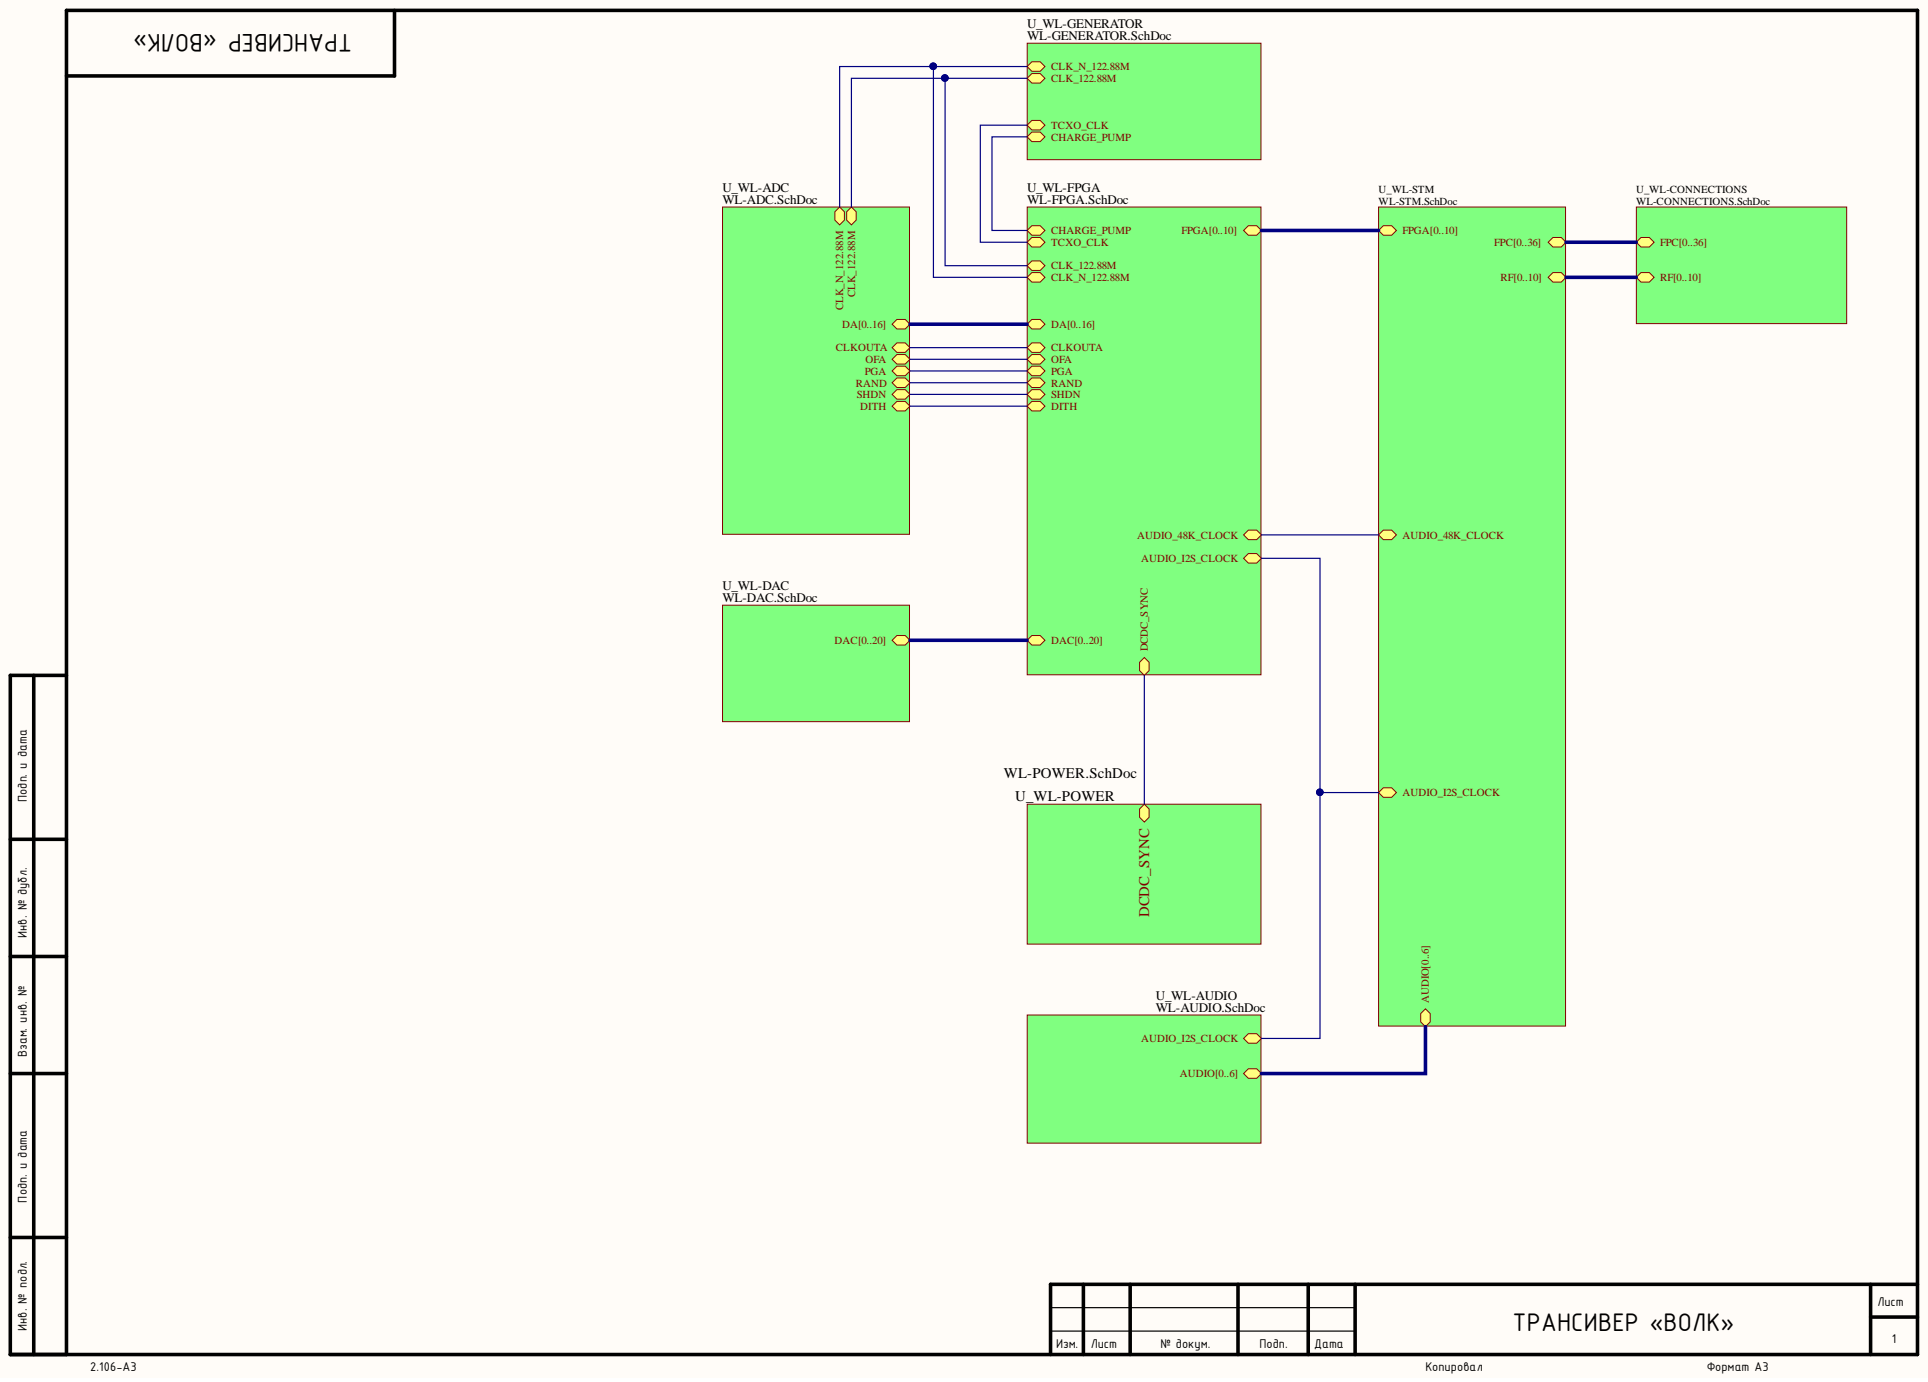
[picture p182: page 1]

U_WL-GENERATOR WL-GENERATOR.SchDoc

U_WL-ADC WL-ADC.SchDoc

U_WL-FPGA WL-FPGA.SchDoc

U_WL-DAC WL-DAC.SchDoc

Инв. № подл. Инв. № дубл. Подп. и дата Взам. инв. № Подп. и дата

U_WL-AUDIO WL-AUDIO.SchDoc

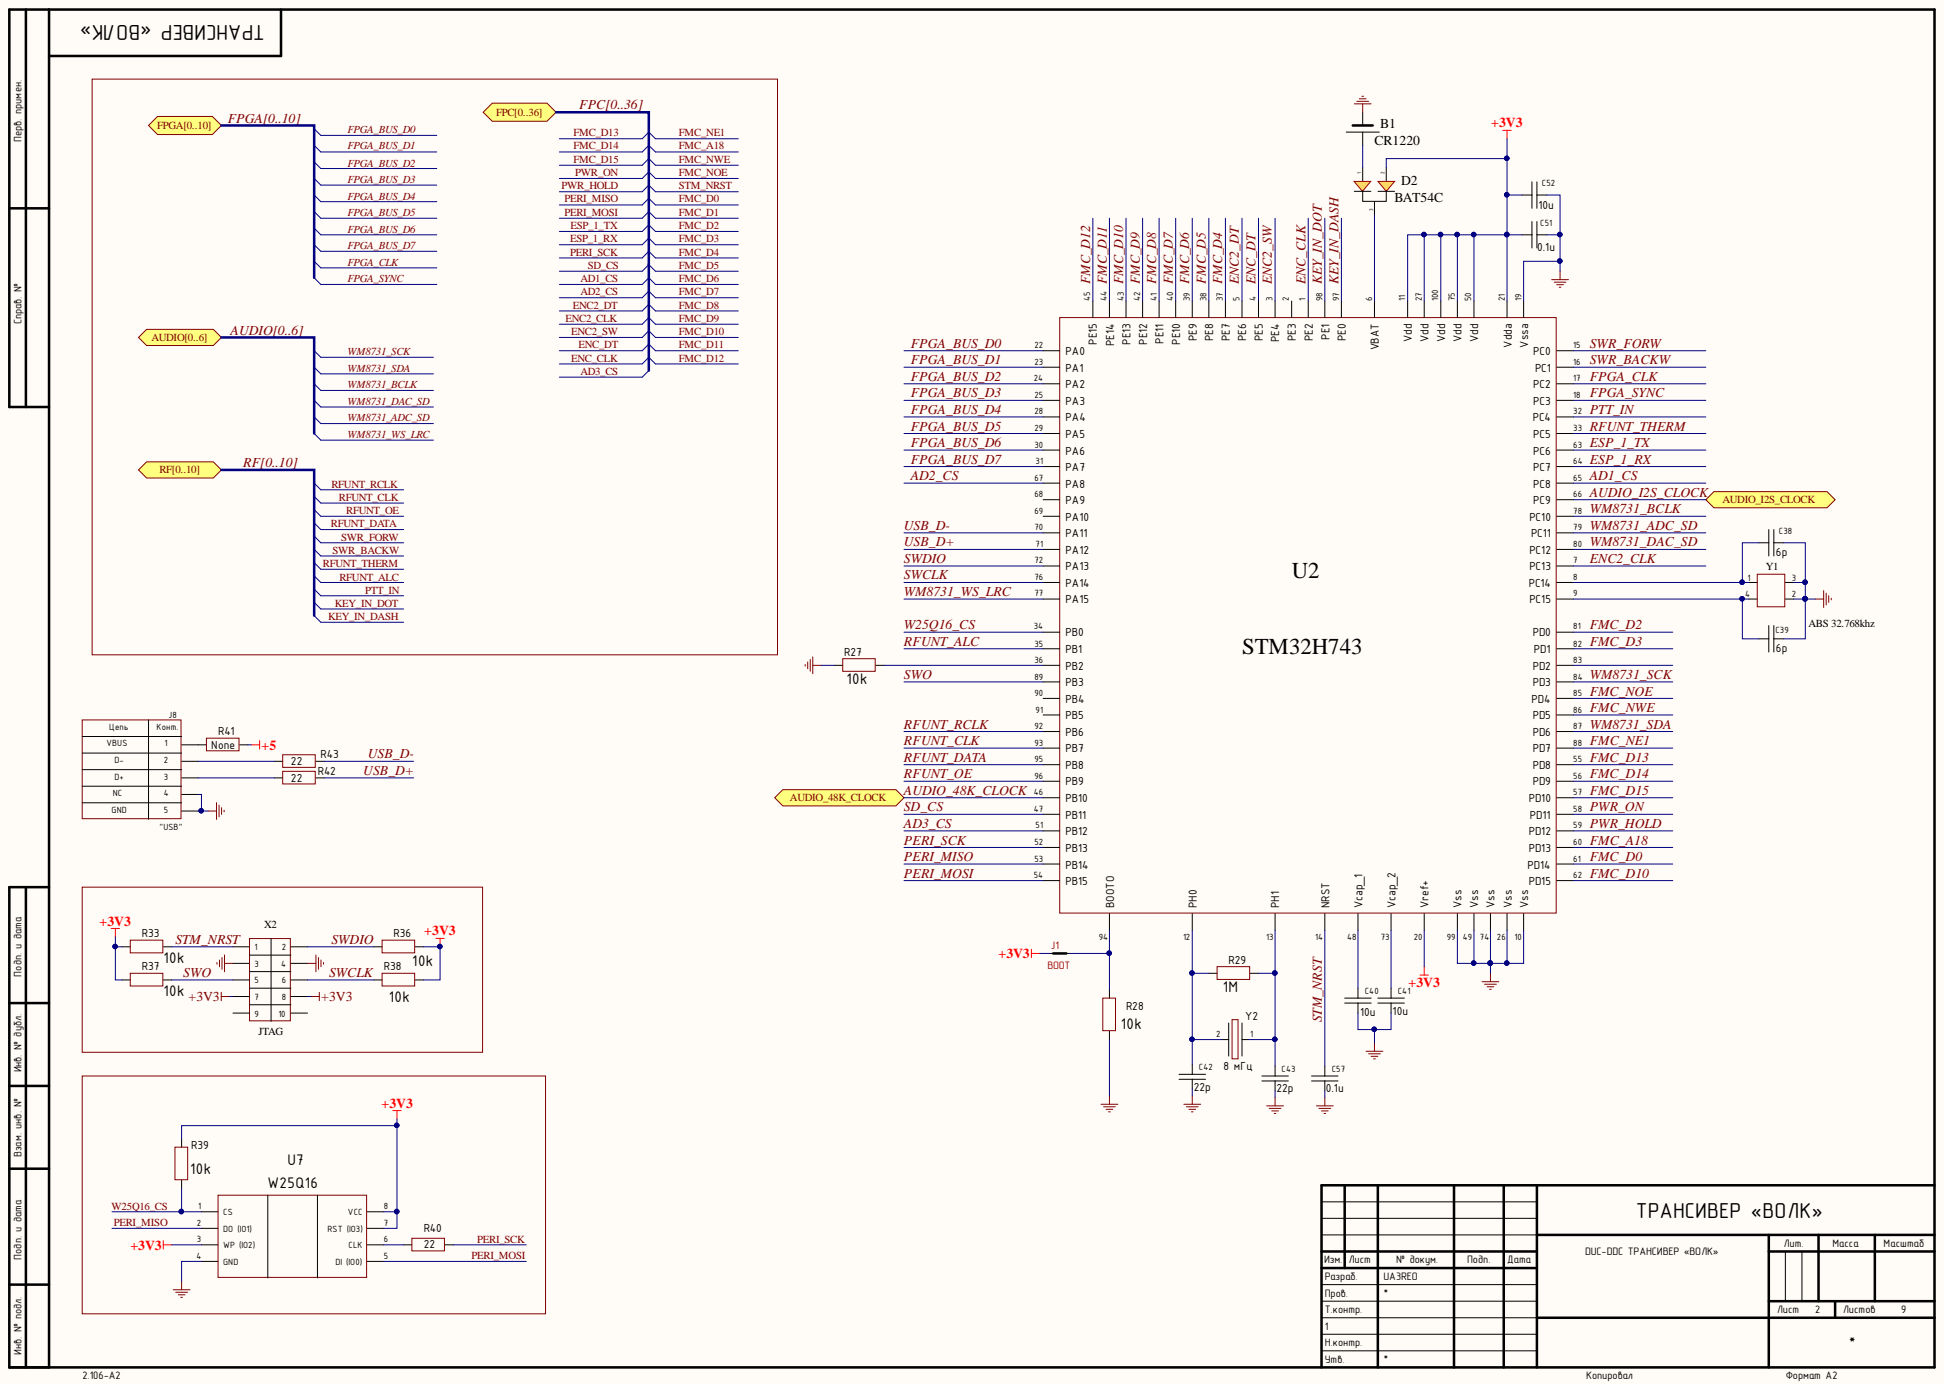
[picture p183: page 2]

Инв. № подл. Инв. № дубл. Подп. и дата Взам. инв. № Подп. и дата Перв. примен. Справ. №

Цепь | Конт.

VBUS | 1

D- | 2
D+ | 3 | R42 22

GND | 5

ТРАНСИВЕР «ВОЛК»

DUC-DDC ТРАНСИВЕР «ВОЛК» | Лит. | Масса | Масштаб

Изм. | Лист | № докум. | Подп. | Дата
Разраб. | | UA3REO
Пров. | | *
Т.контр. | | | | | Лист | Листов 9

Н.контр.
Утв. | *

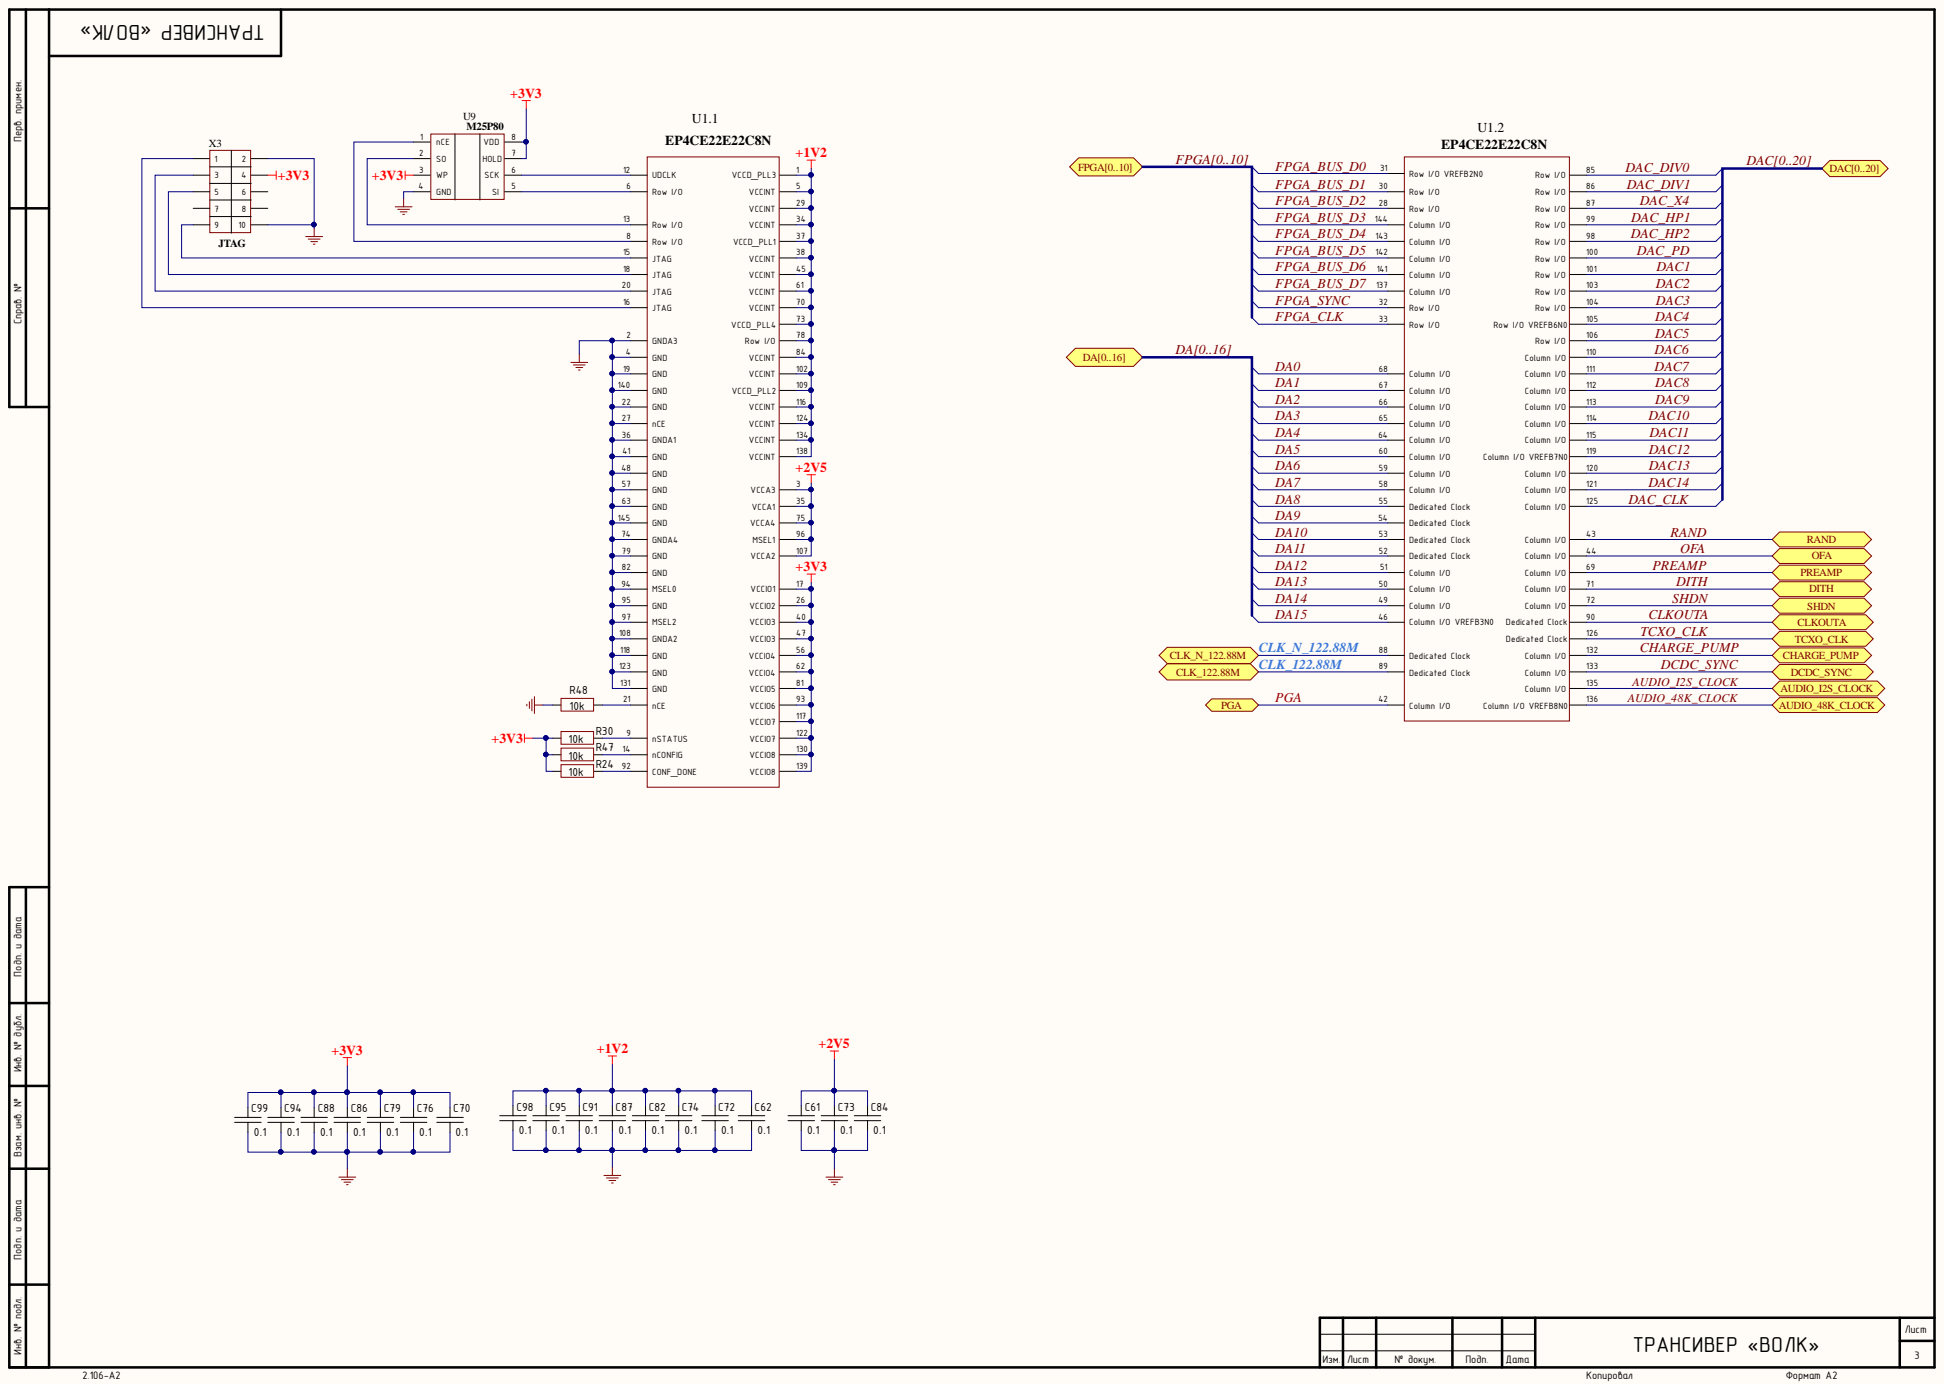
[picture p184: page 3]

Инв. № подл. Инв. № дубл. Подп. и дата Взам. инв. № Подп. и дата Перв. примен. Справ. №

nCE 1

1 | 2 | +3V3 | +3V3 | WP 3 | SCK | 6

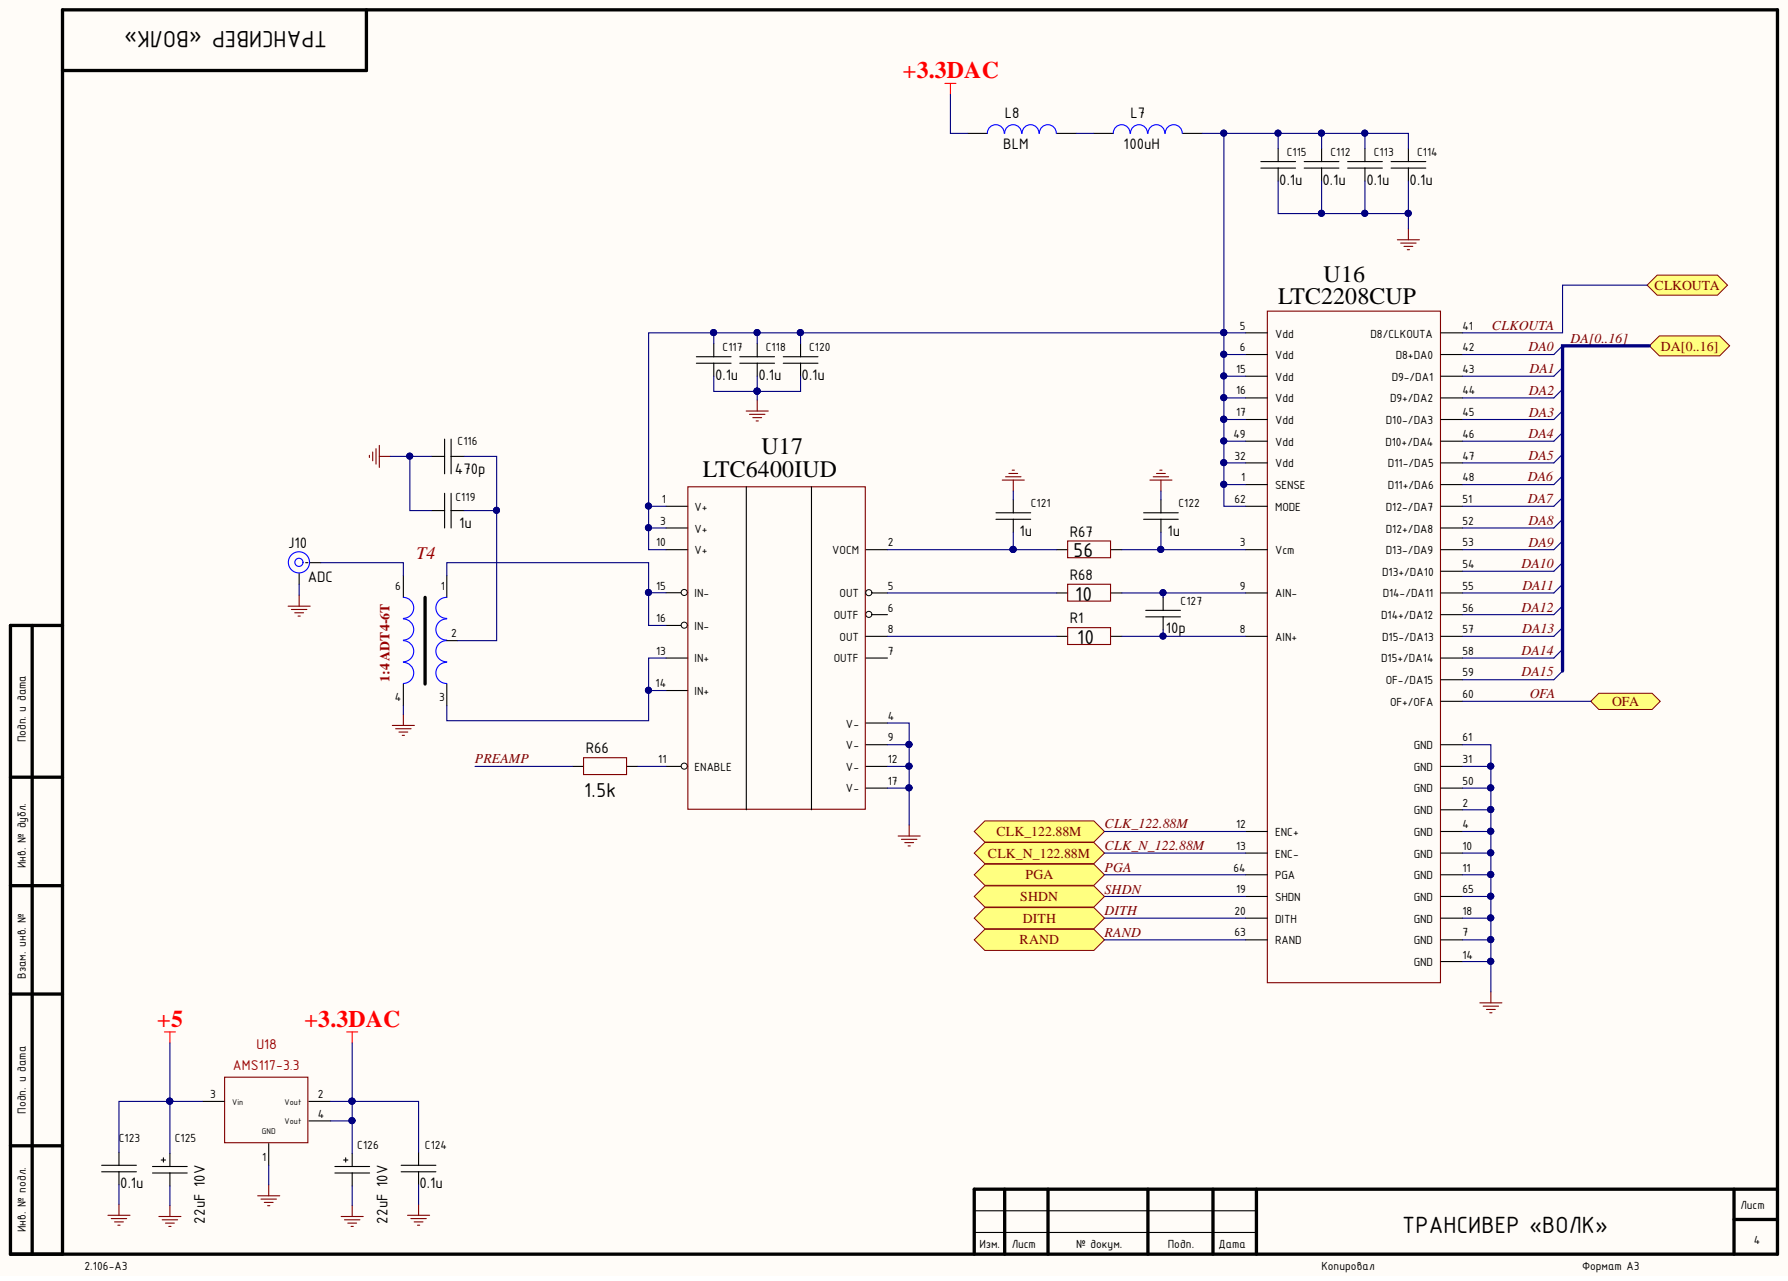
[picture p185: page 4]

Инв. № подл. Инв. № дубл. Подп. и дата Взам. инв. № Подп. и дата

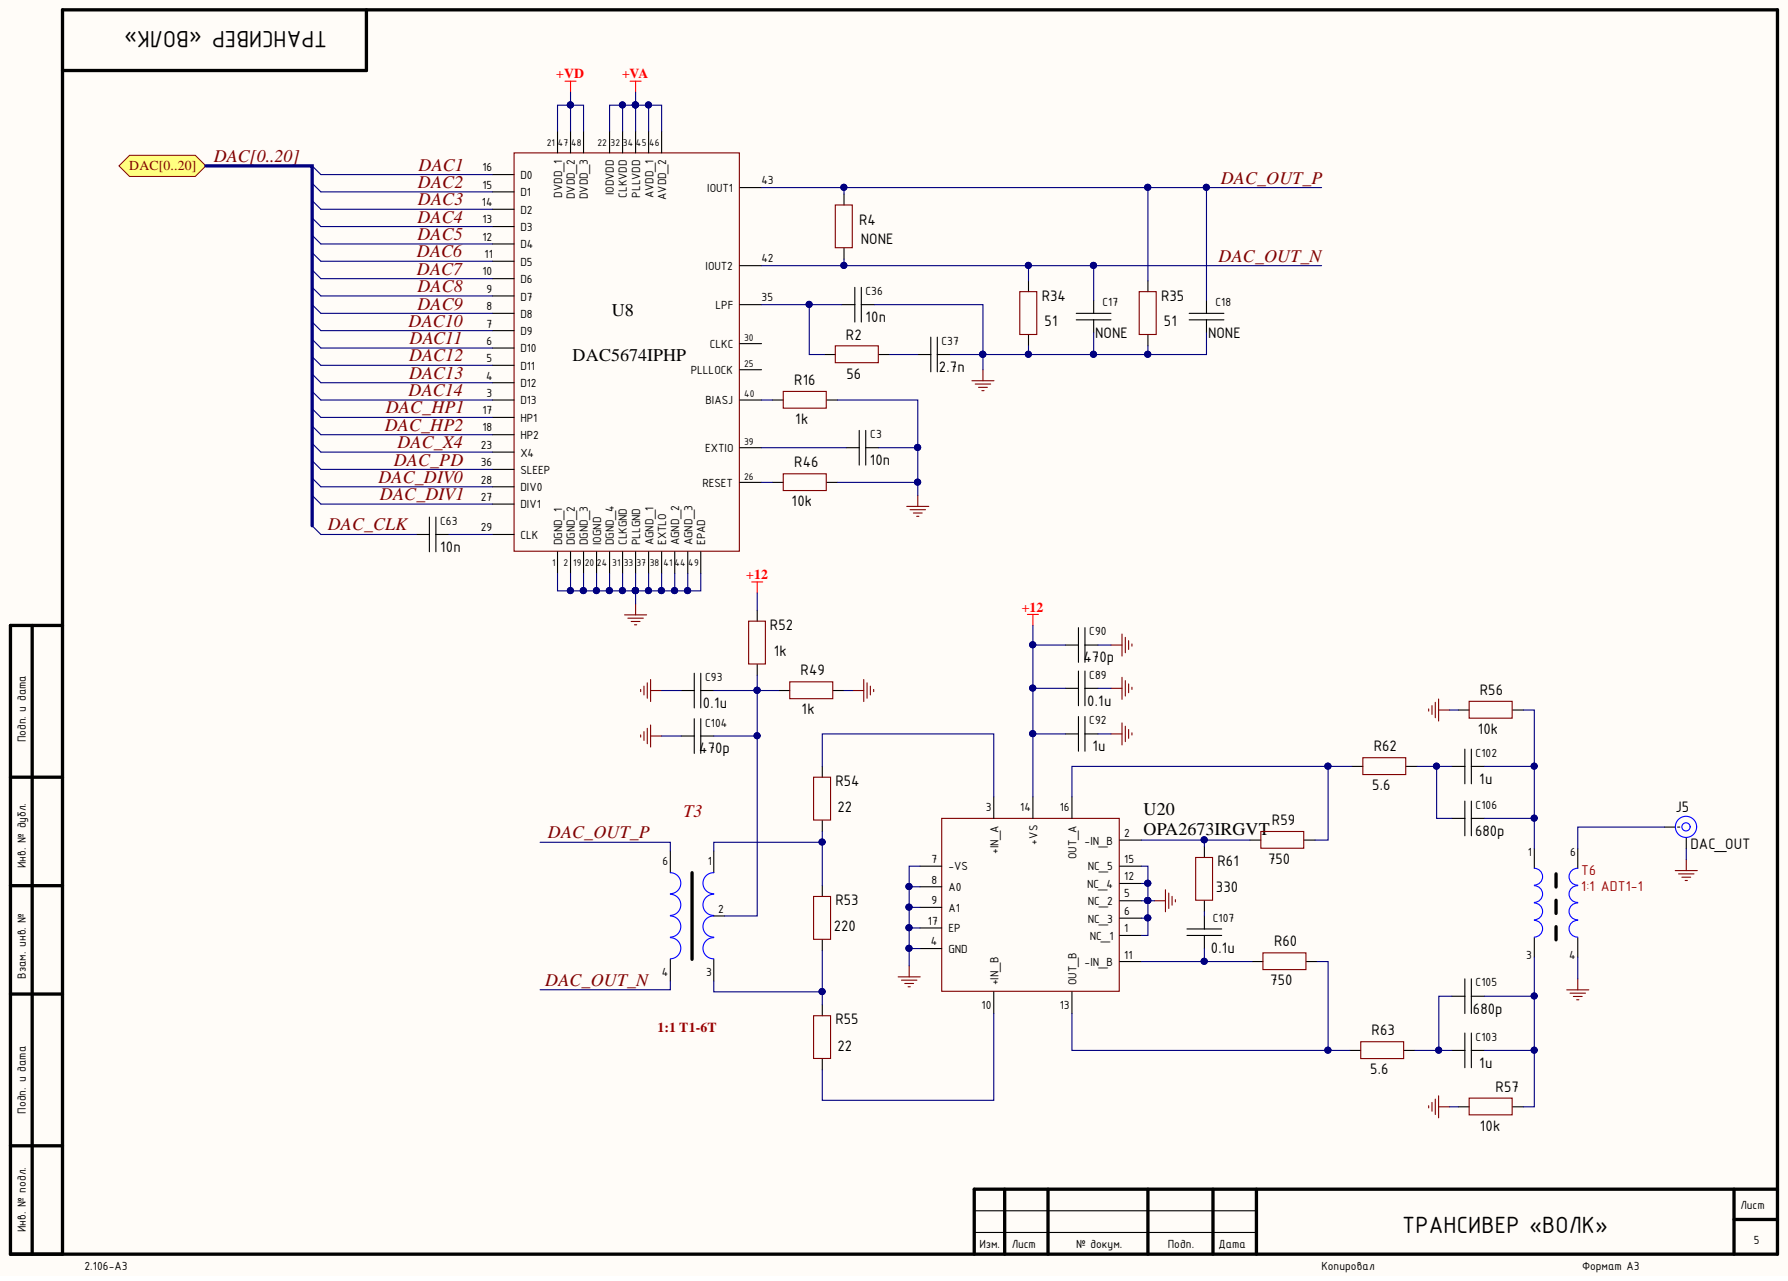
[picture p186: page 5]

Инв. № подл. Инв. № дубл. Подп. и дата Взам. инв. № Подп. и дата

8 | 1 2

1 7

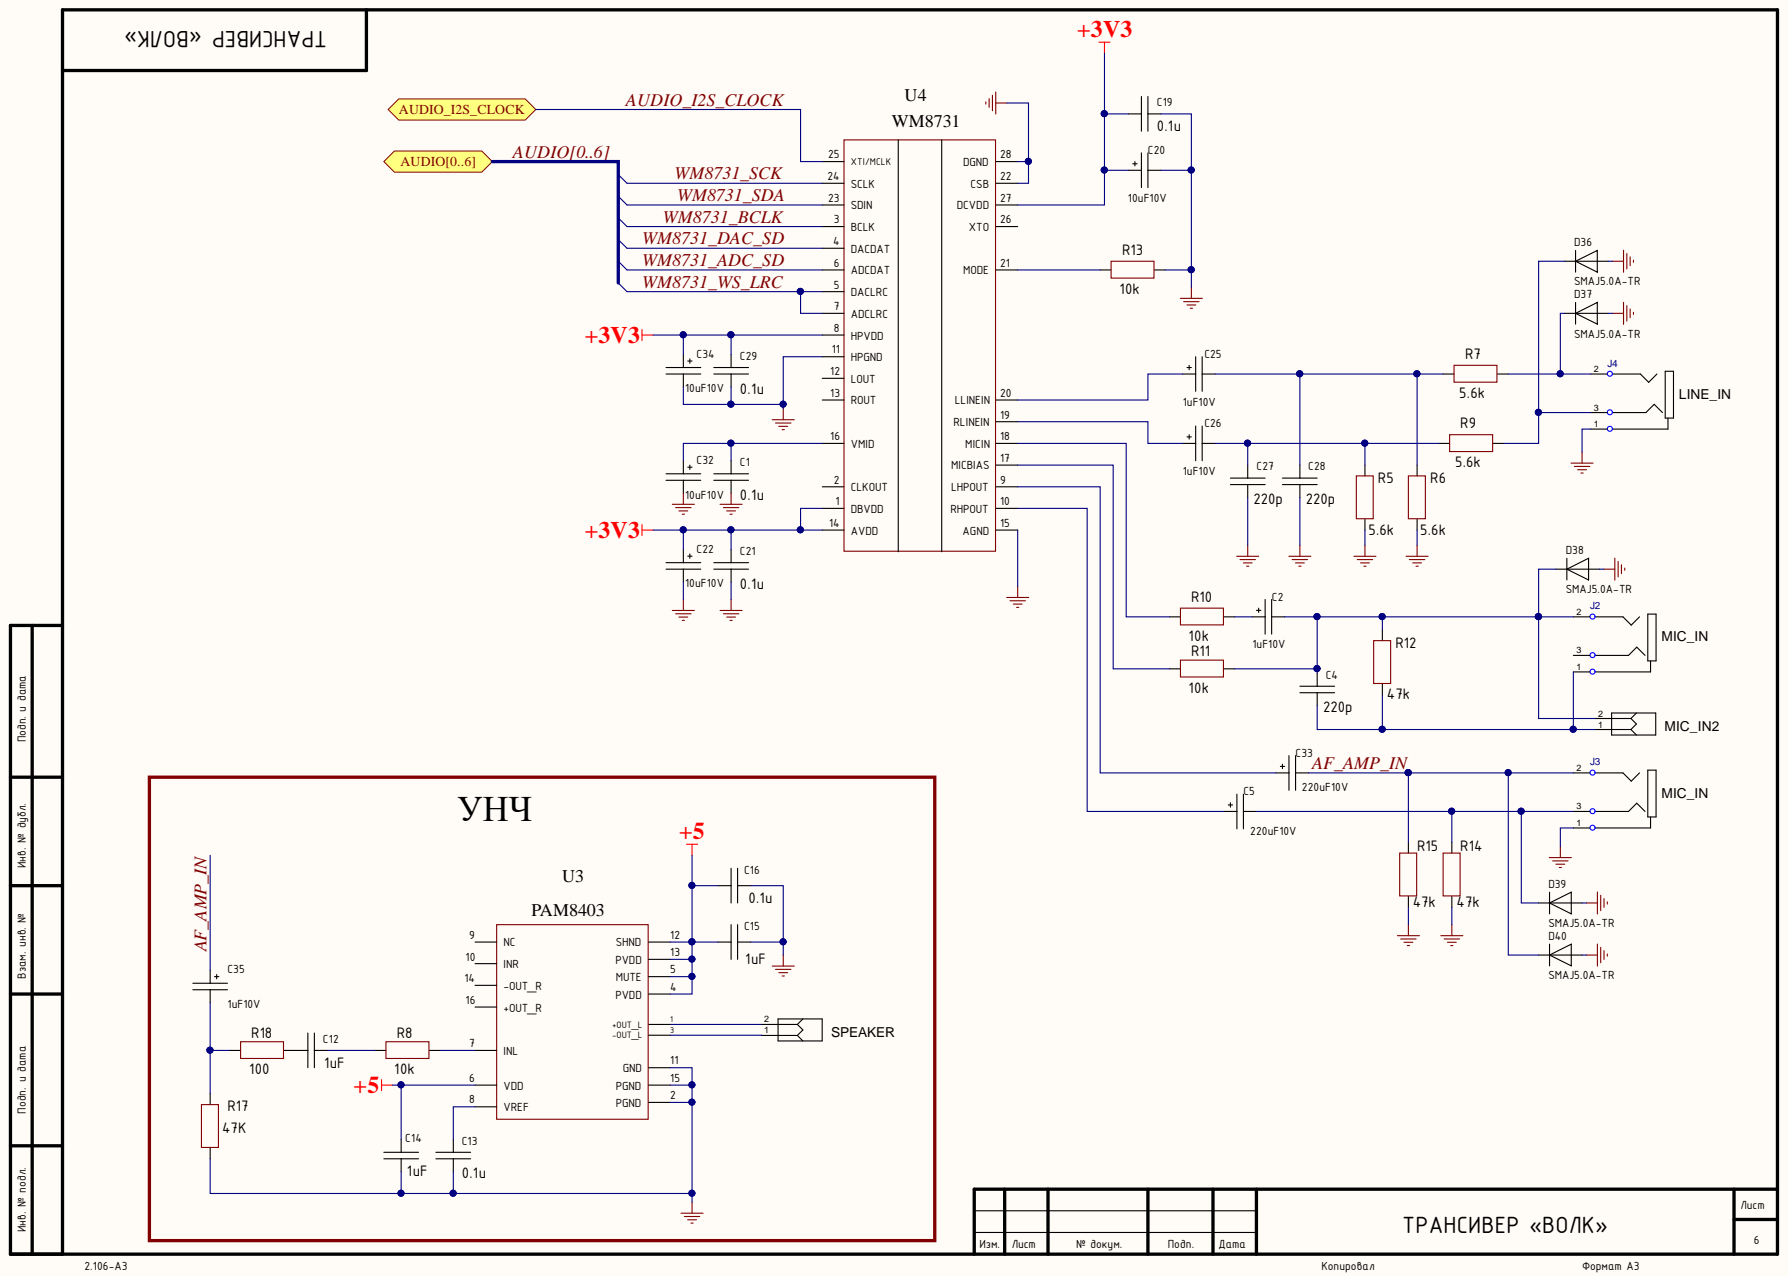
[picture p187: page 6]

XTI/MCLK 25

SCLK 24 SDIN 23 BCLK 3 DACDAT 4 ADCDAT 6 DACLRC 5 ADCLRC 7

LOUT 12

Инв. № подл. Инв. № дубл. Подп. и дата Взам. инв. № Подп. и дата

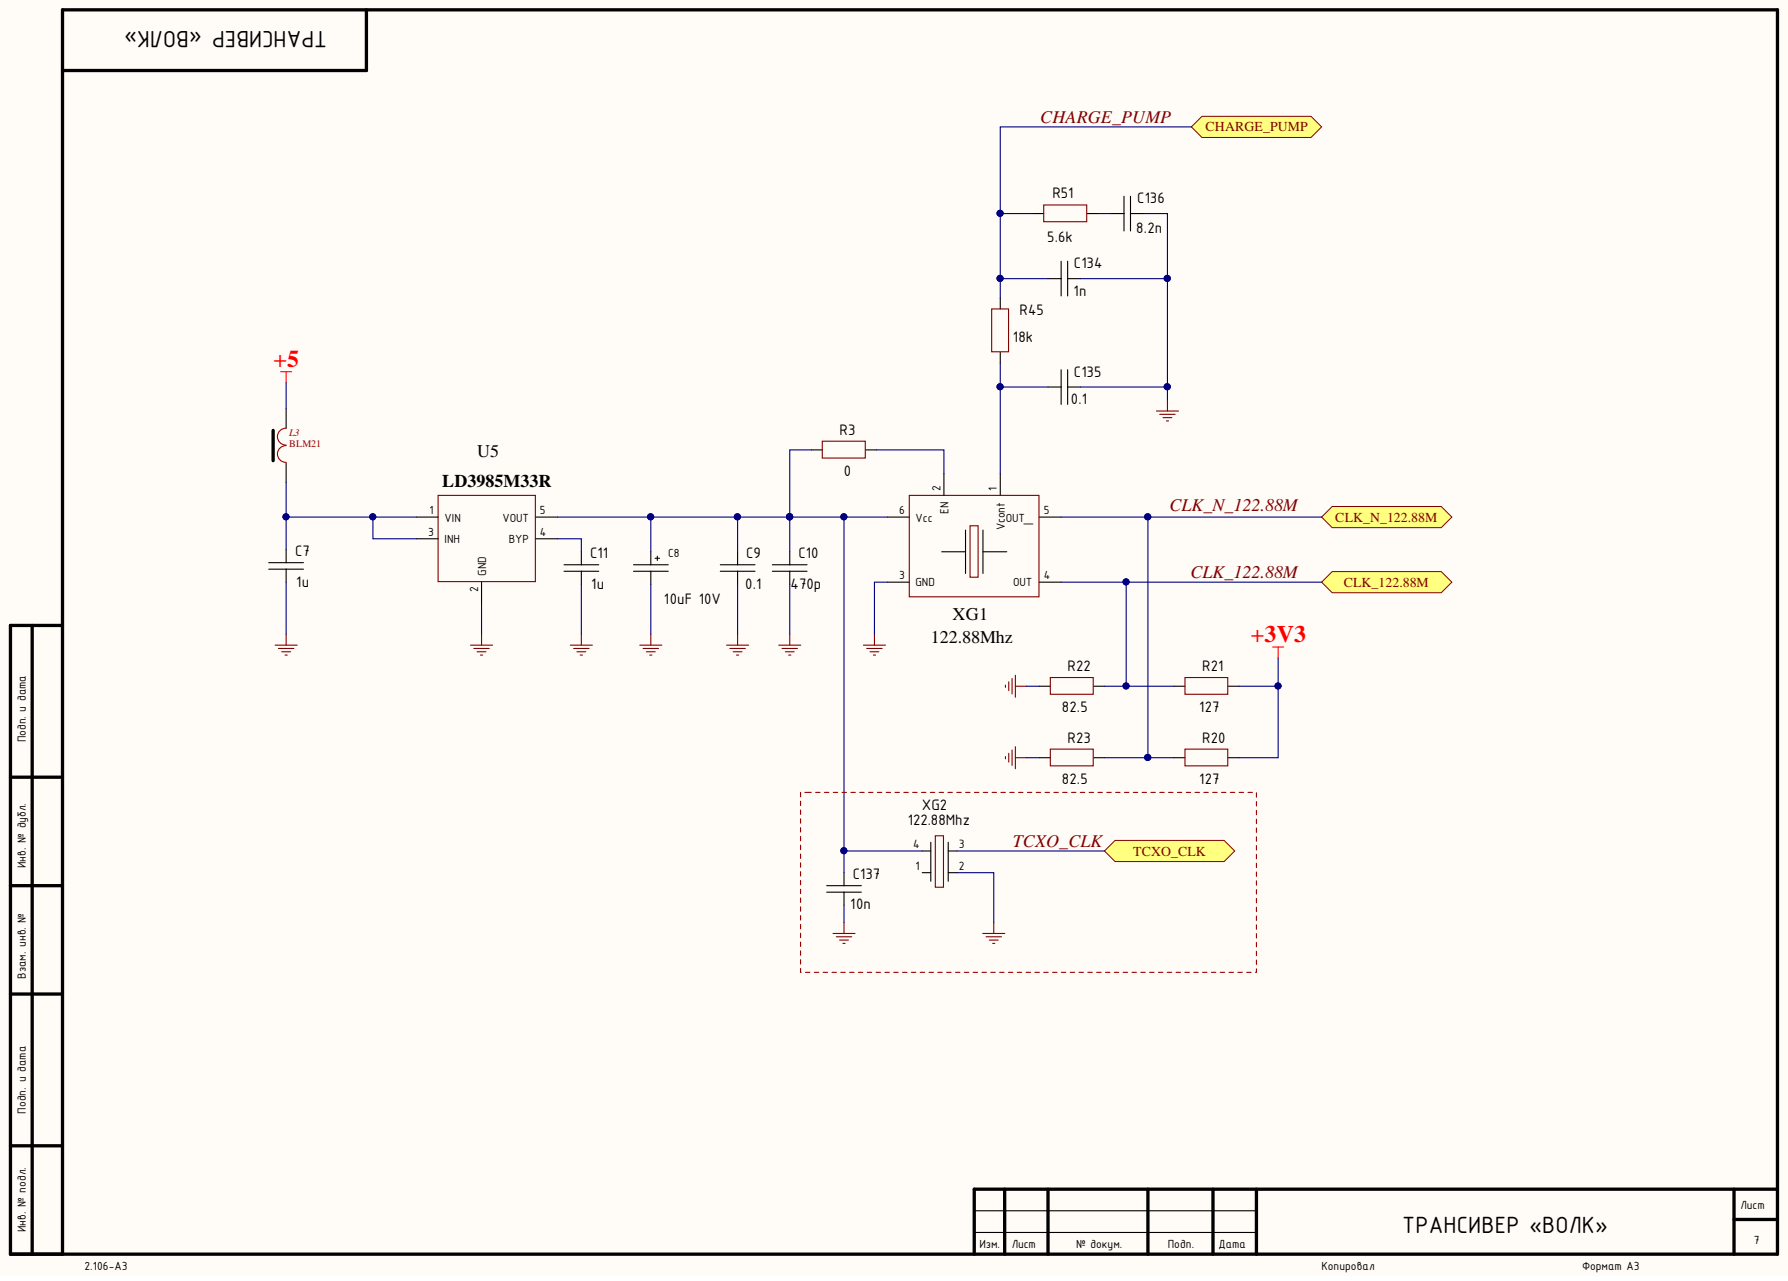
[picture p188: page 7]

Инв. № подл. Инв. № дубл. Подп. и дата Взам. инв. № Подп. и дата

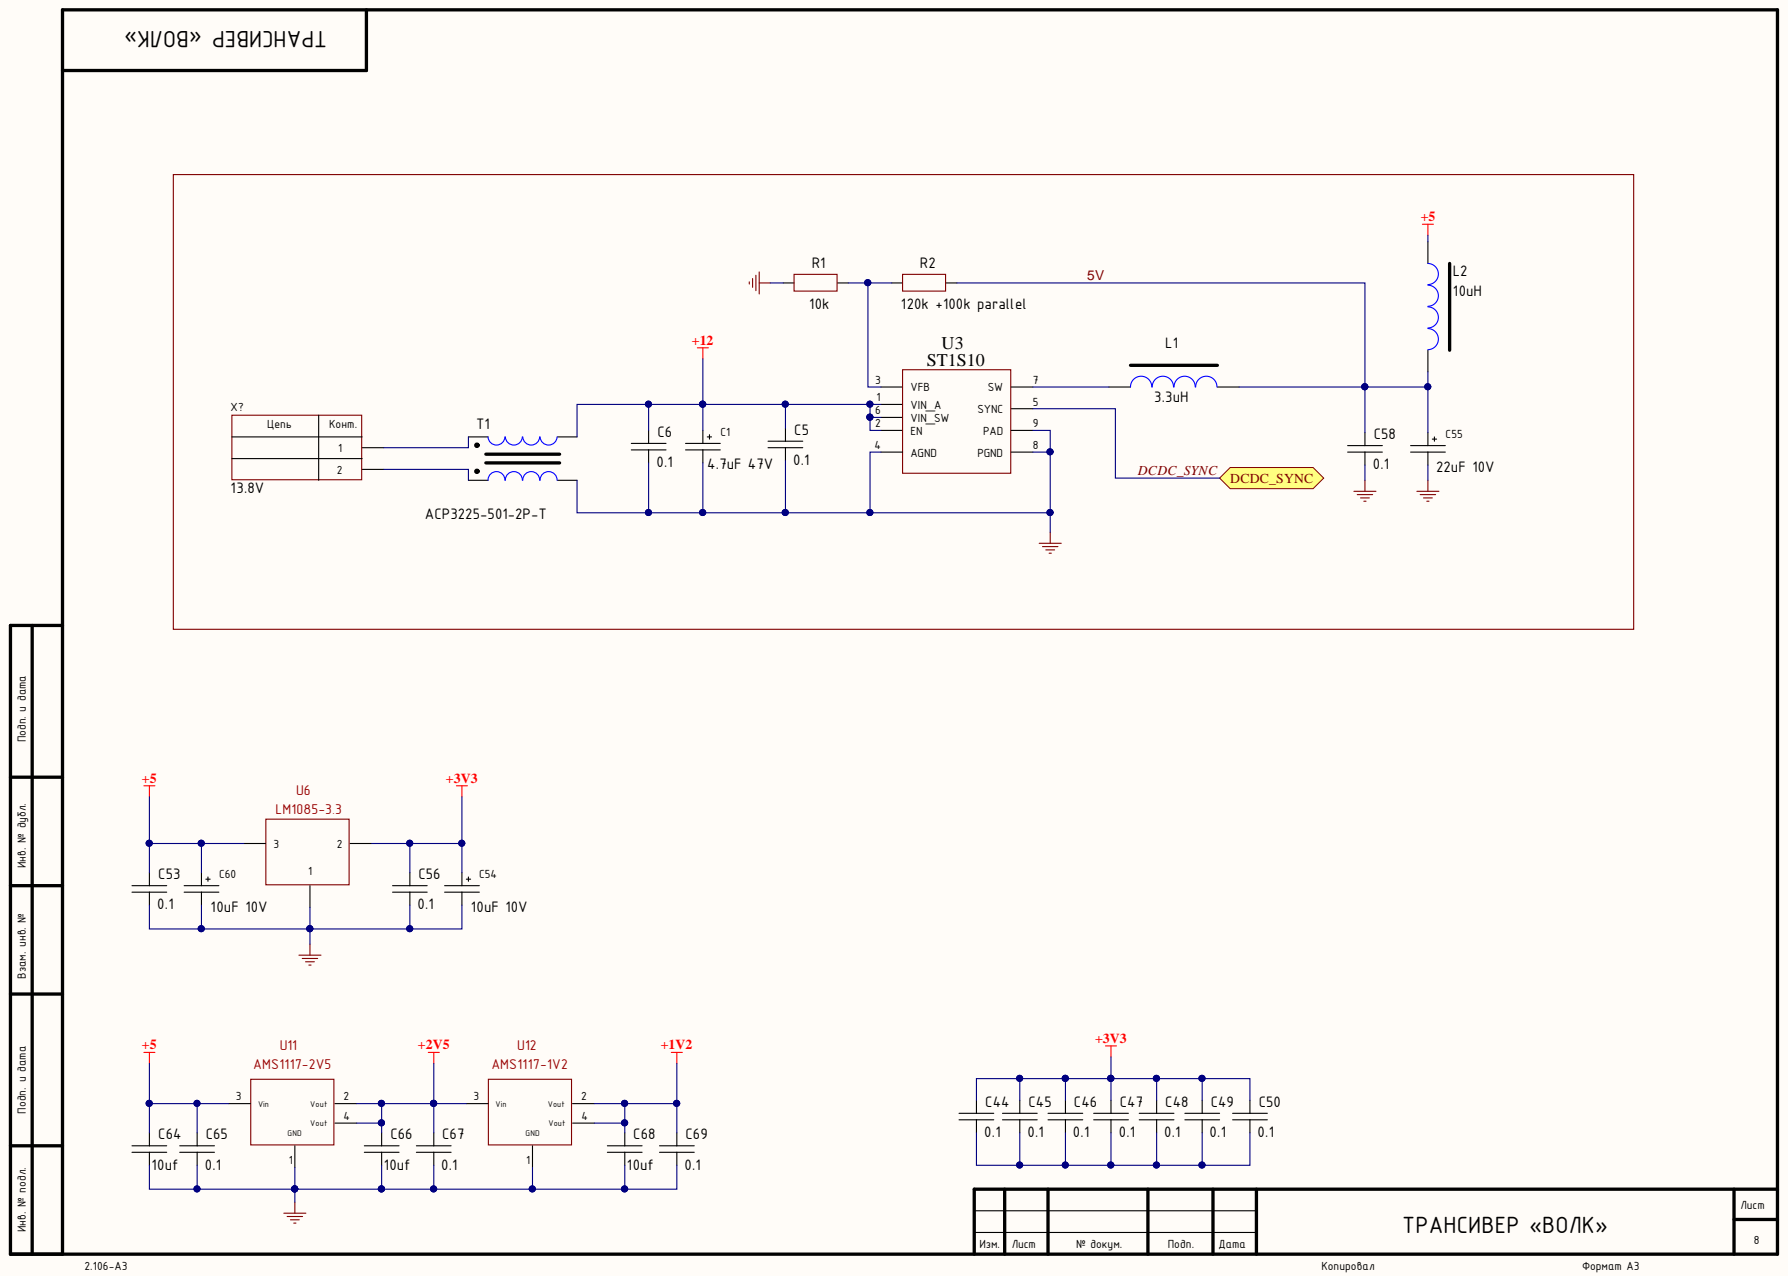
[picture p189: page 8]

VIN_A 1 VFB 3 SYNC PGND | 3.3uH

EN 2 VIN_SW 6 | 5

Цепь | Конт.

AGND 4 | | 8

Инв. № подл. Инв. № дубл. Подп. и дата Взам. инв. № Подп. и дата

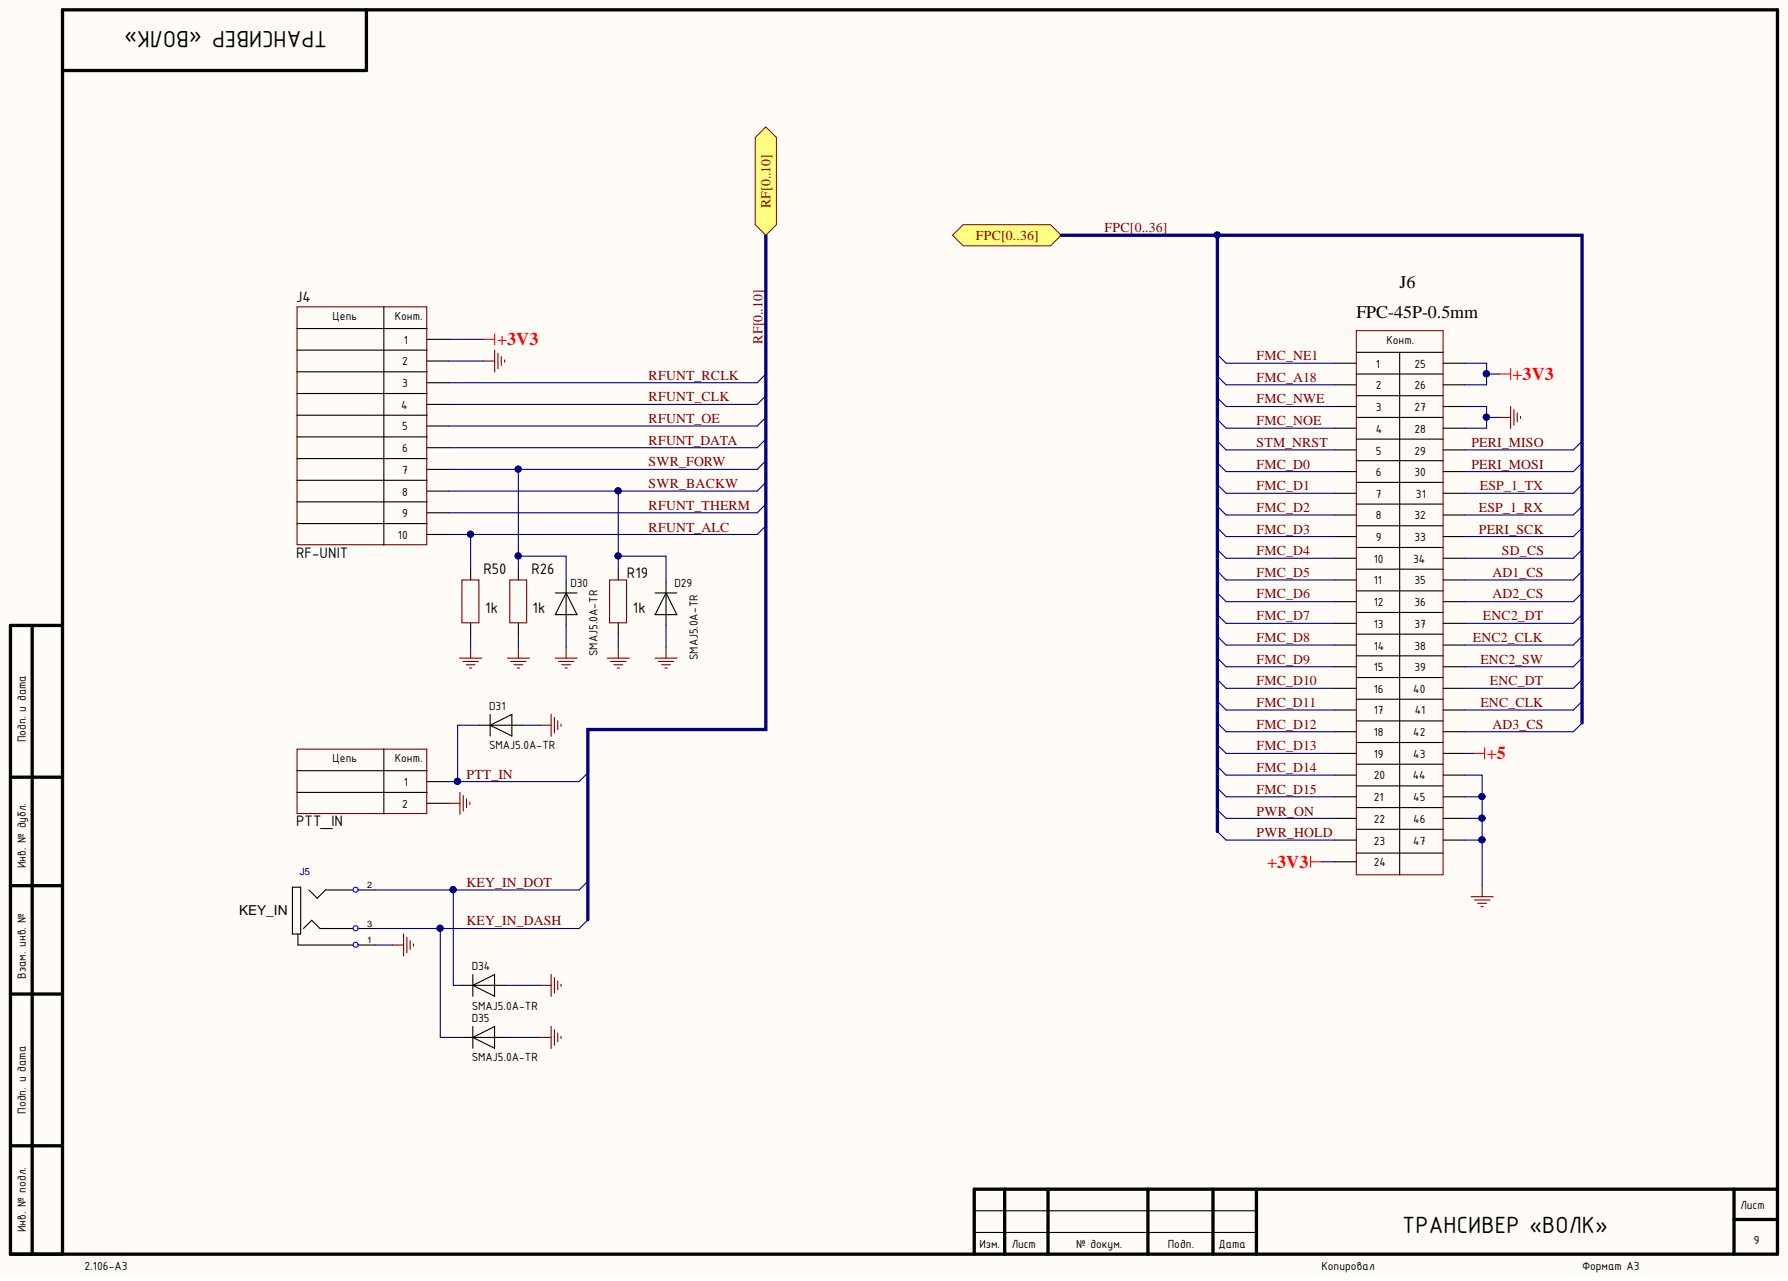
[picture p190: page 9]

S W R_BACKW
R FUNT_THER M
R FUNT_ALC

39
241 40

Инв. № подл. Инв. № дубл. Подп. и дата Взам. инв. № Подп. и дата

Цепь | Конт .
