hristoandreev/UA3REO-DDC-Transceiver/STM32/Src/system_menu.c

#include "system_menu.h"
#include "FT8/FT8_main.h"
#include "INA226_PWR_monitor.h"
#include "agc.h"
#include "audio_filters.h"
#include "auto_calibration.h"
#include "bands.h"
#include "bootloader.h"
#include "callsign.h"
#include "cw.h"
#include "filemanager.h"
#include "fonts.h"
#include "front_unit.h"
#include "functions.h"
#include "hardware.h"
#include "lcd.h"
#include "locator.h"
#include "noise_blanker.h"
#include "rf_unit.h"
#include "rtty_decoder.h"
#include "screen_layout.h"
#include "sd.h"
#include "self_test.h"
#include "settings.h"
#include "spec_analyzer.h"
#include "swr_analyzer.h"
#include "usbd_ua3reo.h"
#include "wifi.h"
#include "wspr.h"

static void SYSMENU_HANDL_TRX_RFPower(int8_t direction);
static void SYSMENU_HANDL_TRX_BandMap(int8_t direction);
static void SYSMENU_HANDL_TRX_ChannelMode(int8_t direction);
static void SYSMENU_HANDL_TRX_RF_Gain_For_Each_Band(int8_t direction);
static void SYSMENU_HANDL_TRX_RF_Gain_For_Each_Mode(int8_t direction);
static void SYSMENU_HANDL_TRX_AutoGain(int8_t direction);
static void SYSMENU_HANDL_TRX_TWO_SIGNAL_TUNE(int8_t direction);
static void SYSMENU_HANDL_TRX_RFFilters(int8_t direction);
static void SYSMENU_HANDL_TRX_INPUT_TYPE_MAIN(int8_t direction);
static void SYSMENU_HANDL_TRX_INPUT_TYPE_DIGI(int8_t direction);
static void SYSMENU_HANDL_TRX_Auto_Input_Switch(int8_t direction);
static void SYSMENU_HANDL_TRX_Auto_Snap(int8_t direction);
static void SYSMENU_HANDL_TRX_RIT_INTERVAL(int8_t direction);
static void SYSMENU_HANDL_TRX_XIT_INTERVAL(int8_t direction);
static void SYSMENU_HANDL_TRX_SAMPLERATE_MAIN(int8_t direction);
static void SYSMENU_HANDL_TRX_SAMPLERATE_FM(int8_t direction);
static void SYSMENU_HANDL_TRX_FRQ_STEP(int8_t direction);
static void SYSMENU_HANDL_TRX_FRQ_FAST_STEP(int8_t direction);
static void SYSMENU_HANDL_TRX_FRQ_ENC_STEP(int8_t direction);
static void SYSMENU_HANDL_TRX_FRQ_ENC_FAST_STEP(int8_t direction);
static void SYSMENU_HANDL_TRX_FRQ_ENC_WFM_STEP_KHZ(int8_t direction);
static void SYSMENU_HANDL_TRX_FRQ_CW_STEP_DIVIDER(int8_t direction);
static void SYSMENU_HANDL_TRX_ENC_ACCELERATE(int8_t direction);
static void SYSMENU_HANDL_TRX_ATT_STEP(int8_t direction);
static void SYSMENU_HANDL_TRX_ATT_DB(int8_t direction);
static void SYSMENU_HANDL_TRX_DEBUG_TYPE(int8_t direction);
static void SYSMENU_HANDL_TRX_SetCallsign(int8_t direction);
static void SYSMENU_HANDL_TRX_SetLocator(int8_t direction);
static void SYSMENU_HANDL_TRX_SetURSICode(int8_t direction);
static void SYSMENU_HANDL_TRX_TRANSV_ENABLE(int8_t direction);
static void SYSMENU_HANDL_TRX_ATU_I(int8_t direction);
static void SYSMENU_HANDL_TRX_ATU_C(int8_t direction);
static void SYSMENU_HANDL_TRX_ATU_T(int8_t direction);
static void SYSMENU_HANDL_TRX_ATU_Enabled(int8_t direction);
static void SYSMENU_HANDL_TRX_TUNER_Enabled(int8_t direction);
static void SYSMENU_HANDL_TRX_TRANSV_70CM(int8_t direction);
static void SYSMENU_HANDL_TRX_TRANSV_23CM(int8_t direction);
static void SYSMENU_HANDL_TRX_TRANSV_13CM(int8_t direction);
static void SYSMENU_HANDL_TRX_TRANSV_6CM(int8_t direction);
static void SYSMENU_HANDL_TRX_TRANSV_3CM(int8_t direction);
static void SYSMENU_HANDL_TRX_FineRITTune(int8_t direction);
static void SYSMENU_HANDL_TRX_VGA_GAIN(int8_t direction);

static void SYSMENU_HANDL_AUDIO_Volume(int8_t direction);
static void SYSMENU_HANDL_AUDIO_Volume_Step(int8_t direction);
static void SYSMENU_HANDL_AUDIO_IFGain(int8_t direction);
static void SYSMENU_HANDL_AUDIO_DNR(int8_t direction);
static void SYSMENU_HANDL_AUDIO_NOISE_BLANKER(int8_t direction);
static void SYSMENU_HANDL_AUDIO_AGC(int8_t direction);
static void SYSMENU_HANDL_AUDIO_AGC_GAIN_TARGET(int8_t direction);
static void SYSMENU_HANDL_AUDIO_MIC_Gain(int8_t direction);
static void SYSMENU_HANDL_AUDIO_MIC_Boost(int8_t direction);
static void SYSMENU_HANDL_AUDIO_MIC_NOISE_GATE(int8_t direction);
static void SYSMENU_HANDL_AUDIO_DNR1_THRES(int8_t direction);
static void SYSMENU_HANDL_AUDIO_DNR2_THRES(int8_t direction);
static void SYSMENU_HANDL_AUDIO_DNR_AVERAGE(int8_t direction);
static void SYSMENU_HANDL_AUDIO_DNR_MINMAL(int8_t direction);
static void SYSMENU_HANDL_AUDIO_NOISE_BLANKER_THRESHOLD(int8_t direction);
static void SYSMENU_HANDL_AUDIO_MIC_EQ_P1_SSB(int8_t direction);
static void SYSMENU_HANDL_AUDIO_MIC_EQ_P2_SSB(int8_t direction);
static void SYSMENU_HANDL_AUDIO_MIC_EQ_P3_SSB(int8_t direction);
static void SYSMENU_HANDL_AUDIO_MIC_EQ_P4_SSB(int8_t direction);
static void SYSMENU_HANDL_AUDIO_MIC_EQ_P5_SSB(int8_t direction);
static void SYSMENU_HANDL_AUDIO_MIC_EQ_P1_AMFM(int8_t direction);
static void SYSMENU_HANDL_AUDIO_MIC_EQ_P2_AMFM(int8_t direction);
static void SYSMENU_HANDL_AUDIO_MIC_EQ_P3_AMFM(int8_t direction);
static void SYSMENU_HANDL_AUDIO_MIC_EQ_P4_AMFM(int8_t direction);
static void SYSMENU_HANDL_AUDIO_MIC_EQ_P5_AMFM(int8_t direction);
static void SYSMENU_HANDL_AUDIO_MIC_REVERBER(int8_t direction);
static void SYSMENU_HANDL_AUDIO_RX_EQ_P1(int8_t direction);
static void SYSMENU_HANDL_AUDIO_RX_EQ_P2(int8_t direction);
static void SYSMENU_HANDL_AUDIO_RX_EQ_P3(int8_t direction);
static void SYSMENU_HANDL_AUDIO_RX_EQ_P4(int8_t direction);
static void SYSMENU_HANDL_AUDIO_RX_EQ_P5(int8_t direction);
static void SYSMENU_HANDL_AUDIO_RX_AGC_SSB_Speed(int8_t direction);
static void SYSMENU_HANDL_AUDIO_RX_AGC_CW_Speed(int8_t direction);
static void SYSMENU_HANDL_AUDIO_RX_AGC_Max_gain(int8_t direction);
static void SYSMENU_HANDL_AUDIO_RX_AGC_Hold(int8_t direction);
static void SYSMENU_HANDL_AUDIO_TX_CompressorSpeed_SSB(int8_t direction);
static void SYSMENU_HANDL_AUDIO_TX_CompressorSpeed_AMFM(int8_t direction);
static void SYSMENU_HANDL_AUDIO_TX_CompressorMaxGain_SSB(int8_t direction);
static void SYSMENU_HANDL_AUDIO_TX_CompressorMaxGain_AMFM(int8_t direction);
static void SYSMENU_HANDL_AUDIO_FMSquelch(int8_t direction);
static void SYSMENU_HANDL_AUDIO_Squelch(int8_t direction);
static void SYSMENU_HANDL_AUDIO_Beeper(int8_t direction);
static void SYSMENU_HANDL_AUDIO_CTCSS_Freq(int8_t direction);
static void SYSMENU_HANDL_AUDIO_SELFHEAR_Volume(int8_t direction);
static void SYSMENU_HANDL_AUDIO_FM_Stereo(int8_t direction);
static void SYSMENU_HANDL_AUDIO_AGC_Spectral(int8_t direction);
static void SYSMENU_HANDL_AUDIO_TX_CESSB(int8_t direction);
static void SYSMENU_HANDL_AUDIO_TX_CESSB_COMPRESS_DB(int8_t direction);
static void SYSMENU_HANDL_AUDIO_VAD_THRESHOLD(int8_t direction);
static void SYSMENU_HANDL_AUDIO_VOX(int8_t direction);
static void SYSMENU_HANDL_AUDIO_VOX_TIMEOUT(int8_t direction);
static void SYSMENU_HANDL_AUDIO_VOX_THRESHOLD(int8_t direction);

static void SYSMENU_HANDL_CW_Pitch(int8_t direction);
static void SYSMENU_HANDL_CW_SelfHear(int8_t direction);
static void SYSMENU_HANDL_CW_Keyer(int8_t direction);
static void SYSMENU_HANDL_CW_Keyer_WPM(int8_t direction);
static void SYSMENU_HANDL_CW_Key_timeout(int8_t direction);
static void SYSMENU_HANDL_CW_GaussFilter(int8_t direction);
static void SYSMENU_HANDL_CW_DotToDashRate(int8_t direction);
static void SYSMENU_HANDL_CW_Iambic(int8_t direction);
static void SYSMENU_HANDL_CW_Invert(int8_t direction);
static void SYSMENU_HANDL_CW_PTT_Type(int8_t direction);

static void SYSMENU_HANDL_SCREEN_FFT_Enabled(int8_t direction);
static void SYSMENU_HANDL_SCREEN_COLOR_THEME(int8_t direction);
static void SYSMENU_HANDL_SCREEN_LAYOUT_THEME(int8_t direction);
static void SYSMENU_HANDL_SCREEN_FFT_Averaging(int8_t direction);
static void SYSMENU_HANDL_SCREEN_FFT_Window(int8_t direction);
static void SYSMENU_HANDL_SCREEN_FFT_Zoom(int8_t direction);
static void SYSMENU_HANDL_SCREEN_FFT_ZoomCW(int8_t direction);
static void SYSMENU_HANDL_SCREEN_LCD_Brightness(int8_t direction);
static void SYSMENU_HANDL_SCREEN_LCD_SleepTimeout(int8_t direction);
static void SYSMENU_HANDL_SCREEN_WTF_Moving(int8_t direction);
static void SYSMENU_HANDL_SCREEN_FFT_Height(int8_t direction);
static void SYSMENU_HANDL_SCREEN_FFT_Style(int8_t direction);
static void SYSMENU_HANDL_SCREEN_FFT_BW_Style(int8_t direction);
static void SYSMENU_HANDL_SCREEN_FFT_Color(int8_t direction);
static void SYSMENU_HANDL_SCREEN_WTF_Color(int8_t direction);
static void SYSMENU_HANDL_SCREEN_FFT_FreqGrid(int8_t direction);
static void SYSMENU_HANDL_SCREEN_FFT_dBmGrid(int8_t direction);
static void SYSMENU_HANDL_SCREEN_FFT_Background(int8_t direction);
static void SYSMENU_HANDL_SCREEN_FFT_Speed(int8_t direction);
static void SYSMENU_HANDL_SCREEN_FFT_Sensitivity(int8_t direction);
static void SYSMENU_HANDL_SCREEN_FFT_Compressor(int8_t direction);
static void SYSMENU_HANDL_SCREEN_FFT_Lens(int8_t direction);
static void SYSMENU_HANDL_SCREEN_FFT_HoldPeaks(int8_t direction);
static void SYSMENU_HANDL_SCREEN_FFT_3D(int8_t direction);
static void SYSMENU_HANDL_SCREEN_FFT_Automatic(int8_t direction);
static void SYSMENU_HANDL_SCREEN_FFT_ManualBottom(int8_t direction);
static void SYSMENU_HANDL_SCREEN_FFT_ManualTop(int8_t direction);
#if HRDW_HAS_WIFI
static void SYSMENU_HANDL_SCREEN_FFT_DXCluster(int8_t direction);
static void SYSMENU_HANDL_SCREEN_FFT_DXCluster_Azimuth(int8_t direction);
static void SYSMENU_HANDL_SCREEN_FFT_DXCluster_Timeout(int8_t direction);
#endif
static void SYSMENU_HANDL_SCREEN_Show_Sec_VFO(int8_t direction);
static void SYSMENU_HANDL_SCREEN_FFT_Scale_Type(int8_t direction);
static void SYSMENU_HANDL_SCREEN_FUNC_BUTTON1(int8_t direction);
static void SYSMENU_HANDL_SCREEN_FUNC_BUTTON2(int8_t direction);
static void SYSMENU_HANDL_SCREEN_FUNC_BUTTON3(int8_t direction);
static void SYSMENU_HANDL_SCREEN_FUNC_BUTTON4(int8_t direction);
static void SYSMENU_HANDL_SCREEN_FUNC_BUTTON5(int8_t direction);
static void SYSMENU_HANDL_SCREEN_FUNC_BUTTON6(int8_t direction);
static void SYSMENU_HANDL_SCREEN_FUNC_BUTTON7(int8_t direction);
static void SYSMENU_HANDL_SCREEN_FUNC_BUTTON8(int8_t direction);
static void SYSMENU_HANDL_SCREEN_FUNC_BUTTON9(int8_t direction);
static void SYSMENU_HANDL_SCREEN_FUNC_BUTTON10(int8_t direction);
static void SYSMENU_HANDL_SCREEN_FUNC_BUTTON11(int8_t direction);
static void SYSMENU_HANDL_SCREEN_FUNC_BUTTON12(int8_t direction);
static void SYSMENU_HANDL_SCREEN_FUNC_BUTTON13(int8_t direction);
static void SYSMENU_HANDL_SCREEN_FUNC_BUTTON14(int8_t direction);
static void SYSMENU_HANDL_SCREEN_FUNC_BUTTON15(int8_t direction);
static void SYSMENU_HANDL_SCREEN_FUNC_BUTTON16(int8_t direction);
static void SYSMENU_HANDL_SCREEN_FUNC_BUTTON17(int8_t direction);
static void SYSMENU_HANDL_SCREEN_FUNC_BUTTON18(int8_t direction);
static void SYSMENU_HANDL_SCREEN_FUNC_BUTTON19(int8_t direction);
static void SYSMENU_HANDL_SCREEN_FUNC_BUTTON20(int8_t direction);
static void SYSMENU_HANDL_SCREEN_FUNC_BUTTON21(int8_t direction);
static void SYSMENU_HANDL_SCREEN_FUNC_BUTTON22(int8_t direction);
static void SYSMENU_HANDL_SCREEN_FUNC_BUTTON23(int8_t direction);
static void SYSMENU_HANDL_SCREEN_FUNC_BUTTON24(int8_t direction);
static void SYSMENU_HANDL_SCREEN_FUNC_BUTTON25(int8_t direction);
static void SYSMENU_HANDL_SCREEN_FUNC_BUTTON26(int8_t direction);
static void SYSMENU_HANDL_SCREEN_FUNC_BUTTON27(int8_t direction);
static void SYSMENU_HANDL_SCREEN_FUNC_BUTTON28(int8_t direction);
#if FUNCBUTTONS_COUNT > 28
static void SYSMENU_HANDL_SCREEN_FUNC_BUTTON29(int8_t direction);
static void SYSMENU_HANDL_SCREEN_FUNC_BUTTON30(int8_t direction);
#if FUNCBUTTONS_COUNT > 30
static void SYSMENU_HANDL_SCREEN_FUNC_BUTTON31(int8_t direction);
static void SYSMENU_HANDL_SCREEN_FUNC_BUTTON32(int8_t direction);
#endif
#endif

static void SYSMENU_HANDL_DECODERS_CW_Decoder(int8_t direction);
static void SYSMENU_HANDL_DECODERS_CW_Decoder_Threshold(int8_t direction);
static void SYSMENU_HANDL_DECODERS_RDS_Decoder(int8_t direction);
static void SYSMENU_HANDL_DECODERS_RTTY_Speed(int8_t direction);
static void SYSMENU_HANDL_DECODERS_RTTY_Shift(int8_t direction);
static void SYSMENU_HANDL_DECODERS_RTTY_Freq(int8_t direction);
static void SYSMENU_HANDL_DECODERS_RTTY_StopBits(int8_t direction);
static void SYSMENU_HANDL_DECODERS_RTTY_InvertBits(int8_t direction);

static void SYSMENU_HANDL_ADC_PGA(int8_t direction);
static void SYSMENU_HANDL_ADC_RAND(int8_t direction);
static void SYSMENU_HANDL_ADC_SHDN(int8_t direction);
static void SYSMENU_HANDL_ADC_DITH(int8_t direction);
static void SYSMENU_HANDL_ADC_DRIVER(int8_t direction);

#if HRDW_HAS_WIFI
static void SYSMENU_HANDL_WIFI_Enabled(int8_t direction);
static void SYSMENU_HANDL_WIFI_SelectAP1(int8_t direction);
static void SYSMENU_HANDL_WIFI_SetAP1password(int8_t direction);
static void SYSMENU_HANDL_WIFI_SelectAP2(int8_t direction);
static void SYSMENU_HANDL_WIFI_SetAP2password(int8_t direction);
static void SYSMENU_HANDL_WIFI_SelectAP3(int8_t direction);
static void SYSMENU_HANDL_WIFI_SetAP3password(int8_t direction);
static void SYSMENU_HANDL_WIFI_Timezone(int8_t direction);
static void SYSMENU_HANDL_WIFI_CAT_Server(int8_t direction);
static void SYSMENU_HANDL_WIFI_UpdateFW(int8_t direction);
#endif

#if HRDW_HAS_SD
static void SYSMENU_HANDL_SD_Filemanager(int8_t direction);
static void SYSMENU_HANDL_SD_FormatDialog(int8_t direction);
static void SYSMENU_HANDL_SD_Format(int8_t direction);
static void SYSMENU_HANDL_SD_ExportSettingsDialog(int8_t direction);
static void SYSMENU_HANDL_SD_ExportSettings(int8_t direction);
static void SYSMENU_HANDL_SD_ImportSettingsDialog(int8_t direction);
static void SYSMENU_HANDL_SD_ImportSettings(int8_t direction);
static void SYSMENU_HANDL_SD_USB(int8_t direction);
#endif

static void SYSMENU_HANDL_SETTIME(int8_t direction);
static void SYSMENU_HANDL_Bootloader(int8_t direction);
#if HRDW_HAS_SD
static void SYSMENU_HANDL_OTA_Update(int8_t direction);
#endif
static void SYSMENU_HANDL_SYSINFO(int8_t direction);
static void SYSMENU_HANDL_SUPPORT(int8_t direction);
static void SYSMENU_HANDL_Back(int8_t direction);

static void SYSMENU_HANDL_CALIB_ENCODER_SLOW_RATE(int8_t direction);
static void SYSMENU_HANDL_CALIB_ENCODER_INVERT(int8_t direction);
static void SYSMENU_HANDL_CALIB_ENCODER2_INVERT(int8_t direction);
static void SYSMENU_HANDL_CALIB_ENCODER_DEBOUNCE(int8_t direction);
static void SYSMENU_HANDL_CALIB_ENCODER2_DEBOUNCE(int8_t direction);
static void SYSMENU_HANDL_CALIB_ENCODER_ON_FALLING(int8_t direction);
static void SYSMENU_HANDL_CALIB_ENCODER_ACCELERATION(int8_t direction);
static void SYSMENU_HANDL_CALIB_RF_unit_type(int8_t direction);
static void SYSMENU_HANDL_CALIB_TangentType(int8_t direction);
static void SYSMENU_HANDL_CALIB_CICCOMP_48K_SHIFT(int8_t direction);
static void SYSMENU_HANDL_CALIB_CICCOMP_96K_SHIFT(int8_t direction);
static void SYSMENU_HANDL_CALIB_CICCOMP_192K_SHIFT(int8_t direction);
static void SYSMENU_HANDL_CALIB_CICCOMP_384K_SHIFT(int8_t direction);
static void SYSMENU_HANDL_CALIB_TXCICCOMP_SHIFT(int8_t direction);
static void SYSMENU_HANDL_CALIB_DAC_SHIFT(int8_t direction);
static void SYSMENU_HANDL_CALIB_DAC_driver_mode(int8_t direction);
static void SYSMENU_HANDL_CALIB_RF_GAIN_2200M(int8_t direction);
static void SYSMENU_HANDL_CALIB_RF_GAIN_160M(int8_t direction);
static void SYSMENU_HANDL_CALIB_RF_GAIN_80M(int8_t direction);
static void SYSMENU_HANDL_CALIB_RF_GAIN_40M(int8_t direction);
static void SYSMENU_HANDL_CALIB_RF_GAIN_30M(int8_t direction);
static void SYSMENU_HANDL_CALIB_RF_GAIN_20M(int8_t direction);
static void SYSMENU_HANDL_CALIB_RF_GAIN_17M(int8_t direction);
static void SYSMENU_HANDL_CALIB_RF_GAIN_15M(int8_t direction);
static void SYSMENU_HANDL_CALIB_RF_GAIN_12M(int8_t direction);
static void SYSMENU_HANDL_CALIB_RF_GAIN_CB(int8_t direction);
static void SYSMENU_HANDL_CALIB_RF_GAIN_10M(int8_t direction);
static void SYSMENU_HANDL_CALIB_RF_GAIN_6M(int8_t direction);
static void SYSMENU_HANDL_CALIB_RF_GAIN_4M(int8_t direction);
static void SYSMENU_HANDL_CALIB_RF_GAIN_2M(int8_t direction);
static void SYSMENU_HANDL_CALIB_S_METER_HF(int8_t direction);
static void SYSMENU_HANDL_CALIB_S_METER_VHF(int8_t direction);
static void SYSMENU_HANDL_CALIB_ADC_OFFSET(int8_t direction);
static void SYSMENU_HANDL_CALIB_LPF_END(int8_t direction);
static void SYSMENU_HANDL_CALIB_BPF_0_START(int8_t direction);
static void SYSMENU_HANDL_CALIB_BPF_0_END(int8_t direction);
static void SYSMENU_HANDL_CALIB_BPF_1_START(int8_t direction);
static void SYSMENU_HANDL_CALIB_BPF_1_END(int8_t direction);
static void SYSMENU_HANDL_CALIB_BPF_2_START(int8_t direction);
static void SYSMENU_HANDL_CALIB_BPF_2_END(int8_t direction);
static void SYSMENU_HANDL_CALIB_BPF_3_START(int8_t direction);
static void SYSMENU_HANDL_CALIB_BPF_3_END(int8_t direction);
static void SYSMENU_HANDL_CALIB_BPF_4_START(int8_t direction);
static void SYSMENU_HANDL_CALIB_BPF_4_END(int8_t direction);
static void SYSMENU_HANDL_CALIB_BPF_5_START(int8_t direction);
static void SYSMENU_HANDL_CALIB_BPF_5_END(int8_t direction);
static void SYSMENU_HANDL_CALIB_BPF_6_START(int8_t direction);
static void SYSMENU_HANDL_CALIB_BPF_6_END(int8_t direction);
static void SYSMENU_HANDL_CALIB_BPF_7_START(int8_t direction);
static void SYSMENU_HANDL_CALIB_BPF_7_END(int8_t direction);
static void SYSMENU_HANDL_CALIB_BPF_8_START(int8_t direction);
static void SYSMENU_HANDL_CALIB_BPF_8_END(int8_t direction);
static void SYSMENU_HANDL_CALIB_BPF_9_START(int8_t direction);
static void SYSMENU_HANDL_CALIB_BPF_9_END(int8_t direction);
static void SYSMENU_HANDL_CALIB_HPF_START(int8_t direction);
static void SYSMENU_HANDL_CALIB_MAX_RF_POWER_ON_METER(int8_t direction);
static void SYSMENU_HANDL_CALIB_SWR_FWD_RATE_HF(int8_t direction);
static void SYSMENU_HANDL_CALIB_SWR_REF_RATE_HF(int8_t direction);
static void SYSMENU_HANDL_CALIB_SWR_FWD_RATE_6M(int8_t direction);
static void SYSMENU_HANDL_CALIB_SWR_REF_RATE_6M(int8_t direction);
static void SYSMENU_HANDL_CALIB_SWR_FWD_RATE_VHF(int8_t direction);
static void SYSMENU_HANDL_CALIB_SWR_REF_RATE_VHF(int8_t direction);
static void SYSMENU_HANDL_CALIB_VCXO(int8_t direction);
static void SYSMENU_HANDL_CALIB_FW_AD8307_SLP(int8_t direction);  // Tisho
static void SYSMENU_HANDL_CALIB_FW_AD8307_OFFS(int8_t direction); // Tisho
static void SYSMENU_HANDL_CALIB_BW_AD8307_SLP(int8_t direction);  // Tisho
static void SYSMENU_HANDL_CALIB_BW_AD8307_OFFS(int8_t direction); // Tisho
static void SYSMENU_HANDL_CALIB_FAN_MEDIUM_START(int8_t direction);
static void SYSMENU_HANDL_CALIB_FAN_MEDIUM_STOP(int8_t direction);
static void SYSMENU_HANDL_CALIB_FAN_FULL_START(int8_t direction);
static void SYSMENU_HANDL_CALIB_TRX_MAX_RF_TEMP(int8_t direction);
static void SYSMENU_HANDL_CALIB_TRX_MAX_SWR(int8_t direction);
static void SYSMENU_HANDL_CALIB_FM_DEVIATION_SCALE(int8_t direction);
static void SYSMENU_HANDL_CALIB_SSB_POWER_ADDITION(int8_t direction);
static void SYSMENU_HANDL_CALIB_AM_MODULATION_INDEX(int8_t direction);
static void SYSMENU_HANDL_CALIB_TUNE_MAX_POWER(int8_t direction);
static void SYSMENU_HANDL_CALIB_RTC_COARSE_CALIBRATION(int8_t direction);
static void SYSMENU_HANDL_CALIB_RTC_CALIBRATION(int8_t direction);
static void SYSMENU_HANDL_CALIB_EXT_2200m(int8_t direction);
static void SYSMENU_HANDL_CALIB_EXT_160m(int8_t direction);
static void SYSMENU_HANDL_CALIB_EXT_80m(int8_t direction);
static void SYSMENU_HANDL_CALIB_EXT_60m(int8_t direction);
static void SYSMENU_HANDL_CALIB_EXT_40m(int8_t direction);
static void SYSMENU_HANDL_CALIB_EXT_30m(int8_t direction);
static void SYSMENU_HANDL_CALIB_EXT_20m(int8_t direction);
static void SYSMENU_HANDL_CALIB_EXT_17m(int8_t direction);
static void SYSMENU_HANDL_CALIB_EXT_15m(int8_t direction);
static void SYSMENU_HANDL_CALIB_EXT_12m(int8_t direction);
static void SYSMENU_HANDL_CALIB_EXT_CB(int8_t direction);
static void SYSMENU_HANDL_CALIB_EXT_10m(int8_t direction);
static void SYSMENU_HANDL_CALIB_EXT_6m(int8_t direction);
static void SYSMENU_HANDL_CALIB_EXT_4m(int8_t direction);
static void SYSMENU_HANDL_CALIB_EXT_FM(int8_t direction);
static void SYSMENU_HANDL_CALIB_EXT_2m(int8_t direction);
static void SYSMENU_HANDL_CALIB_EXT_70cm(int8_t direction);
static void SYSMENU_HANDL_CALIB_EXT_TRANSV_70cm(int8_t direction);
static void SYSMENU_HANDL_CALIB_EXT_TRANSV_23cm(int8_t direction);
static void SYSMENU_HANDL_CALIB_EXT_TRANSV_13cm(int8_t direction);
static void SYSMENU_HANDL_CALIB_EXT_TRANSV_6cm(int8_t direction);
static void SYSMENU_HANDL_CALIB_EXT_TRANSV_3cm(int8_t direction);
static void SYSMENU_HANDL_CALIB_NOTX_NOTHAM(int8_t direction);
static void SYSMENU_HANDL_CALIB_NOTX_2200m(int8_t direction);
static void SYSMENU_HANDL_CALIB_NOTX_160m(int8_t direction);
static void SYSMENU_HANDL_CALIB_NOTX_80m(int8_t direction);
static void SYSMENU_HANDL_CALIB_NOTX_60m(int8_t direction);
static void SYSMENU_HANDL_CALIB_NOTX_40m(int8_t direction);
static void SYSMENU_HANDL_CALIB_NOTX_30m(int8_t direction);
static void SYSMENU_HANDL_CALIB_NOTX_20m(int8_t direction);
static void SYSMENU_HANDL_CALIB_NOTX_17m(int8_t direction);
static void SYSMENU_HANDL_CALIB_NOTX_15m(int8_t direction);
static void SYSMENU_HANDL_CALIB_NOTX_12m(int8_t direction);
static void SYSMENU_HANDL_CALIB_NOTX_CB(int8_t direction);
static void SYSMENU_HANDL_CALIB_NOTX_10m(int8_t direction);
static void SYSMENU_HANDL_CALIB_NOTX_6m(int8_t direction);
static void SYSMENU_HANDL_CALIB_NOTX_4m(int8_t direction);
static void SYSMENU_HANDL_CALIB_NOTX_FM(int8_t direction);
static void SYSMENU_HANDL_CALIB_NOTX_2m(int8_t direction);
static void SYSMENU_HANDL_CALIB_NOTX_70cm(int8_t direction);
static void SYSMENU_HANDL_CALIB_ENABLE_60m_band(int8_t direction);
static void SYSMENU_HANDL_CALIB_ENABLE_4m_band(int8_t direction);
static void SYSMENU_HANDL_CALIB_ENABLE_AIR_band(int8_t direction);
static void SYSMENU_HANDL_CALIB_ENABLE_marine_band(int8_t direction);
static void SYSMENU_HANDL_CALIB_TRANSV_OFFSET_Custom(int8_t direction);
static void SYSMENU_HANDL_CALIB_TRANSV_RF_70cm(int8_t direction);
static void SYSMENU_HANDL_CALIB_TRANSV_IF_70cm(int8_t direction);
static void SYSMENU_HANDL_CALIB_TRANSV_RF_23cm(int8_t direction);
static void SYSMENU_HANDL_CALIB_TRANSV_IF_23cm(int8_t direction);
static void SYSMENU_HANDL_CALIB_TRANSV_RF_13cm(int8_t direction);
static void SYSMENU_HANDL_CALIB_TRANSV_IF_13cm(int8_t direction);
static void SYSMENU_HANDL_CALIB_TRANSV_RF_6cm(int8_t direction);
static void SYSMENU_HANDL_CALIB_TRANSV_IF_6cm(int8_t direction);
static void SYSMENU_HANDL_CALIB_TRANSV_RF_3cm(int8_t direction);
static void SYSMENU_HANDL_CALIB_TRANSV_IF_3cm(int8_t direction);
static void SYSMENU_HANDL_CALIB_OTA_update(int8_t direction);
static void SYSMENU_HANDL_CALIB_TX_StartDelay(int8_t direction);
static void SYSMENU_HANDL_CALIB_PWR_VLT_Calibration(int8_t direction);
static void SYSMENU_HANDL_CALIB_PWR_CUR_Calibration(int8_t direction);
static void SYSMENU_HANDL_CALIB_LCD_Rotate(int8_t direction);
static void SYSMENU_HANDL_CALIB_TOUCHPAD_horizontal_flip(int8_t direction);
static void SYSMENU_HANDL_INA226_PWR_MON(int8_t direction); // Tisho
static void SYSMENU_HANDL_INA226_CUR_CALL(int8_t direction);
static void SYSMENU_HANDL_CALIB_ATU_AVERAGING(int8_t direction);
static void SYSMENU_HANDL_CALIB_CAT_Type(int8_t direction);
static void SYSMENU_HANDL_CALIB_LNA_compensation(int8_t direction);
static void SYSMENU_HANDL_CALIB_TwoSignalTune_Balance(int8_t direction);
static void SYSMENU_HANDL_CALIB_LinearPowerControl(int8_t direction);
static void SYSMENU_HANDL_CALIB_FlashGT911(int8_t direction);
static void SYSMENU_HANDL_CALIB_IF_GAIN_MIN(int8_t direction);
static void SYSMENU_HANDL_CALIB_IF_GAIN_MAX(int8_t direction);
static void SYSMENU_HANDL_CALIB_SETTINGS_RESET(int8_t direction);
static void SYSMENU_HANDL_CALIB_CALIBRATION_RESET(int8_t direction);
static void SYSMENU_HANDL_CALIB_WIFI_RESET(int8_t direction);

static void SYSMENU_HANDL_TRXMENU(int8_t direction);
static void SYSMENU_HANDL_AUDIOMENU(int8_t direction);
static void SYSMENU_HANDL_CWMENU(int8_t direction);
static void SYSMENU_HANDL_LCDMENU(int8_t direction);
static void SYSMENU_HANDL_DECODERSMENU(int8_t direction);
static void SYSMENU_HANDL_ADCMENU(int8_t direction);
static void SYSMENU_HANDL_CALIBRATIONMENU(int8_t direction);

#if HRDW_HAS_WIFI
static void SYSMENU_HANDL_WIFIMENU(int8_t direction);
static void SYSMENU_HANDL_DX_CLUSTER(int8_t direction);
static void SYSMENU_HANDL_RDA_STATS(int8_t direction);
static void SYSMENU_HANDL_PROPAGINATION(int8_t direction);
static void SYSMENU_HANDL_DAYNIGHT_MAP(int8_t direction);
static void SYSMENU_HANDL_IONOGRAM(int8_t direction);
#endif
static void SYSMENU_HANDL_SPECTRUMMENU(int8_t direction);
static void SYSMENU_HANDL_SWR_ANALYSER_MENU(int8_t direction);
static void SYSMENU_HANDL_WSPRMENU(int8_t direction);
#if HRDW_HAS_SD
static void SYSMENU_HANDL_SDMENU(int8_t direction);
static void SYSMENU_HANDL_RECORD_CQ_WAV(int8_t direction);
#endif
static void SYSMENU_HANDL_FT8_Decoder(int8_t direction);     // Tisho
static void SYSMENU_HANDL_SWR_Tandem_Ctrl(int8_t direction); // Tisho
static void SYSMENU_HANDL_LOCATOR_INFO(int8_t direction);
static void SYSMENU_HANDL_CALLSIGN_INFO(int8_t direction);
static void SYSMENU_HANDL_SELF_TEST(int8_t direction);
static void SYSMENU_HANDL_AUTO_CALIBRATION(int8_t direction);

static void SYSMENU_HANDL_SPECTRUM_Begin(int8_t direction);
static void SYSMENU_HANDL_SPECTRUM_Start(int8_t direction);
static void SYSMENU_HANDL_SPECTRUM_End(int8_t direction);
static void SYSMENU_HANDL_SPECTRUM_TopDBM(int8_t direction);
static void SYSMENU_HANDL_SPECTRUM_BottomDBM(int8_t direction);

static void SYSMENU_HANDL_SWR_BAND_START(int8_t direction);
static void SYSMENU_HANDL_SWR_HF_START(int8_t direction);
static void SYSMENU_HANDL_SWR_CUSTOM_Begin(int8_t direction);
static void SYSMENU_HANDL_SWR_CUSTOM_Start(int8_t direction);
static void SYSMENU_HANDL_SWR_CUSTOM_End(int8_t direction);

static void SYSMENU_HANDL_WSPR_Start(int8_t direction);
static void SYSMENU_HANDL_WSPR_FREQ_OFFSET(int8_t direction);
static void SYSMENU_HANDL_WSPR_BAND160(int8_t direction);
static void SYSMENU_HANDL_WSPR_BAND80(int8_t direction);
static void SYSMENU_HANDL_WSPR_BAND40(int8_t direction);
static void SYSMENU_HANDL_WSPR_BAND30(int8_t direction);
static void SYSMENU_HANDL_WSPR_BAND20(int8_t direction);
static void SYSMENU_HANDL_WSPR_BAND17(int8_t direction);
static void SYSMENU_HANDL_WSPR_BAND15(int8_t direction);
static void SYSMENU_HANDL_WSPR_BAND12(int8_t direction);
static void SYSMENU_HANDL_WSPR_BAND10(int8_t direction);
static void SYSMENU_HANDL_WSPR_BAND6(int8_t direction);
static void SYSMENU_HANDL_WSPR_BAND2(int8_t direction);

static void SYSMENU_HANDL_AUTO_CALIBRATION_SWR(int8_t direction);
static void SYSMENU_HANDL_AUTO_CALIBRATION_POWER(int8_t direction);

static bool SYSMENU_HANDL_CHECK_HAS_LPF(void);
static bool SYSMENU_HANDL_CHECK_HAS_HPF(void);
static bool SYSMENU_HANDL_CHECK_HAS_BPF_8(void);
static bool SYSMENU_HANDL_CHECK_HAS_BPF_9(void);
static bool SYSMENU_HANDL_CHECK_HAS_BPF_10(void);
static bool SYSMENU_HANDL_CHECK_HAS_RFFILTERS_BYPASS(void);
static bool SYSMENU_HANDL_CHECK_HIDDEN_ENABLED(void);

#ifdef LCD_SMALL_INTERFACE
#define interactive_menu_top 46
#else
#define interactive_menu_top 54
#endif

const static struct sysmenu_item_handler sysmenu_handlers[] =
	{
		{"TRX Settings", SYSMENU_MENU, NULL, NULL, SYSMENU_HANDL_TRXMENU},
		{"AUDIO Settings", SYSMENU_MENU, NULL, NULL, SYSMENU_HANDL_AUDIOMENU},
		{"CW Settings", SYSMENU_MENU, NULL, NULL, SYSMENU_HANDL_CWMENU},
		{"SCREEN Settings", SYSMENU_MENU, NULL, NULL, SYSMENU_HANDL_LCDMENU},
		{"Decoders", SYSMENU_MENU, NULL, NULL, SYSMENU_HANDL_DECODERSMENU},
		{"ADC/DAC Settings", SYSMENU_MENU, NULL, NULL, SYSMENU_HANDL_ADCMENU},
		#if HRDW_HAS_WIFI
		{"WIFI Settings", SYSMENU_MENU, NULL, NULL, SYSMENU_HANDL_WIFIMENU},
		#endif
		#if HRDW_HAS_SD
		{"SD Card", SYSMENU_MENU, NULL, NULL, SYSMENU_HANDL_SDMENU},
		#endif
		{"Set Clock Time", SYSMENU_RUN, NULL, NULL, SYSMENU_HANDL_SETTIME},
		{"DFU Mode", SYSMENU_RUN, NULL, NULL, SYSMENU_HANDL_Bootloader},
		#if HRDW_HAS_SD
		{"OTA Update", SYSMENU_RUN, NULL, NULL, SYSMENU_HANDL_OTA_Update},
		#endif
		{"Services", SYSMENU_RUN, NULL, NULL, SYSMENU_HANDL_SERVICESMENU},
		{"System info", SYSMENU_RUN, NULL, NULL, SYSMENU_HANDL_SYSINFO},
		{"Support project", SYSMENU_RUN, NULL, NULL, SYSMENU_HANDL_SUPPORT},
		{"Calibration", SYSMENU_MENU, SYSMENU_HANDL_CHECK_HIDDEN_ENABLED, NULL, SYSMENU_HANDL_CALIBRATIONMENU},
};

const static struct sysmenu_item_handler sysmenu_trx_handlers[] =
	{
		{"RF Power", SYSMENU_UINT8, NULL, &TRX.RF_Gain, SYSMENU_HANDL_TRX_RFPower},
        {"Power for each band", SYSMENU_BOOLEAN, NULL, &TRX.RF_Gain_For_Each_Band, SYSMENU_HANDL_TRX_RF_Gain_For_Each_Band},
        {"Power for each mode", SYSMENU_BOOLEAN, NULL, &TRX.RF_Gain_For_Each_Mode, SYSMENU_HANDL_TRX_RF_Gain_For_Each_Mode},
        {"Channel Mode", SYSMENU_BOOLEAN, NULL, &TRX.ChannelMode, SYSMENU_HANDL_TRX_ChannelMode},
		{"Band Map", SYSMENU_BOOLEAN, NULL, &TRX.BandMapEnabled, SYSMENU_HANDL_TRX_BandMap},
		{"AutoGainer", SYSMENU_BOOLEAN, NULL, &TRX.AutoGain, SYSMENU_HANDL_TRX_AutoGain},
#if !defined(FRONTPANEL_LITE)
		{"RF_Filters", SYSMENU_BOOLEAN, SYSMENU_HANDL_CHECK_HAS_RFFILTERS_BYPASS, &TRX.RF_Filters, SYSMENU_HANDL_TRX_RFFilters},
#endif
		{"Two Signal TUNE", SYSMENU_BOOLEAN, NULL, &TRX.TWO_SIGNAL_TUNE, SYSMENU_HANDL_TRX_TWO_SIGNAL_TUNE},
		{"RIT Interval", SYSMENU_UINT16, NULL, &TRX.RIT_INTERVAL, SYSMENU_HANDL_TRX_RIT_INTERVAL},
		{"XIT Interval", SYSMENU_UINT16, NULL, &TRX.XIT_INTERVAL, SYSMENU_HANDL_TRX_XIT_INTERVAL},
#if !defined(FRONTPANEL_LITE) && !defined(FRONTPANEL_X1)
		{"Fine RIT Tune", SYSMENU_BOOLEAN, NULL, &TRX.FineRITTune, SYSMENU_HANDL_TRX_FineRITTune},
#endif
		{"TRX Samplerate", SYSMENU_ENUM, NULL, &TRX.SAMPLERATE_MAIN, SYSMENU_HANDL_TRX_SAMPLERATE_MAIN, {"48khz", "96khz", "192khz", "384khz"}},
		{"FM Samplerate", SYSMENU_ENUM, NULL, &TRX.SAMPLERATE_FM, SYSMENU_HANDL_TRX_SAMPLERATE_FM, {"48khz", "96khz", "192khz", "384khz"}},
		{"Freq Step", SYSMENU_UINT32R, NULL, &TRX.FRQ_STEP, SYSMENU_HANDL_TRX_FRQ_STEP},
		{"Freq Step FAST", SYSMENU_UINT32R, NULL, &TRX.FRQ_FAST_STEP, SYSMENU_HANDL_TRX_FRQ_FAST_STEP},
		{"Freq Step ENC2", SYSMENU_UINT32R, NULL, &TRX.FRQ_ENC_STEP, SYSMENU_HANDL_TRX_FRQ_ENC_STEP},
		{"Freq Step ENC2 FAST", SYSMENU_UINT32R, NULL, &TRX.FRQ_ENC_FAST_STEP, SYSMENU_HANDL_TRX_FRQ_ENC_FAST_STEP},
		{"Freq Step WFM, kHz", SYSMENU_UINT32R, NULL, &TRX.FRQ_ENC_WFM_STEP_KHZ, SYSMENU_HANDL_TRX_FRQ_ENC_WFM_STEP_KHZ},
		{"CW Freq Step divider", SYSMENU_UINT8, NULL, &TRX.FRQ_CW_STEP_DIVIDER, SYSMENU_HANDL_TRX_FRQ_CW_STEP_DIVIDER},
		{"Encoder Accelerate", SYSMENU_BOOLEAN, NULL, &TRX.Encoder_Accelerate, SYSMENU_HANDL_TRX_ENC_ACCELERATE},
		{"Att step, dB", SYSMENU_UINT8, NULL, &TRX.ATT_STEP, SYSMENU_HANDL_TRX_ATT_STEP},
		{"Attenuation, dB", SYSMENU_FLOAT32, NULL, &TRX.ATT_DB, SYSMENU_HANDL_TRX_ATT_DB},
#if HRDW_HAS_VGA
        {"VGA Gain, dB", SYSMENU_FLOAT32, NULL, &TRX.VGA_GAIN, SYSMENU_HANDL_TRX_VGA_GAIN},
#endif
#if HRDW_HAS_USB_DEBUG
		{"DEBUG Console", SYSMENU_ENUM, NULL, &TRX.Debug_Type, SYSMENU_HANDL_TRX_DEBUG_TYPE, {"OFF", "SYSTEM", "WIFI", "BUTTONS", "TOUCH", "CAT"}},
#endif
		{"Auto Input Switch", SYSMENU_BOOLEAN, NULL, &TRX.Auto_Input_Switch, SYSMENU_HANDL_TRX_Auto_Input_Switch},
		{"Auto Snap", SYSMENU_BOOLEAN, NULL, &TRX.Auto_Snap, SYSMENU_HANDL_TRX_Auto_Snap},
		{"Input Type MAIN", SYSMENU_ENUM, NULL, &TRX.InputType_MAIN, SYSMENU_HANDL_TRX_INPUT_TYPE_MAIN, {"MIC", "LINE", "USB"}},
		{"Input Type DIGI", SYSMENU_ENUM, NULL, &TRX.InputType_DIGI, SYSMENU_HANDL_TRX_INPUT_TYPE_DIGI, {"MIC", "LINE", "USB"}},
		{"Callsign", SYSMENU_RUN, NULL, NULL, SYSMENU_HANDL_TRX_SetCallsign},
		{"Locator", SYSMENU_RUN, NULL, NULL, SYSMENU_HANDL_TRX_SetLocator},
		{"URSI Code", SYSMENU_RUN, NULL, NULL, SYSMENU_HANDL_TRX_SetURSICode},
		{"Transverter 70cm", SYSMENU_BOOLEAN, NULL, &TRX.Transverter_70cm, SYSMENU_HANDL_TRX_TRANSV_70CM},
		{"Transverter 23cm", SYSMENU_BOOLEAN, NULL, &TRX.Transverter_23cm, SYSMENU_HANDL_TRX_TRANSV_23CM},
		{"Transverter 13cm", SYSMENU_BOOLEAN, NULL, &TRX.Transverter_13cm, SYSMENU_HANDL_TRX_TRANSV_13CM},
		{"Transverter 6cm", SYSMENU_BOOLEAN, NULL, &TRX.Transverter_6cm, SYSMENU_HANDL_TRX_TRANSV_6CM},
		{"Transverter 3cm", SYSMENU_BOOLEAN, NULL, &TRX.Transverter_3cm, SYSMENU_HANDL_TRX_TRANSV_3CM},
		{"Custom Transverter", SYSMENU_BOOLEAN, NULL, &TRX.Custom_Transverter_Enabled, SYSMENU_HANDL_TRX_TRANSV_ENABLE},
		{"TUNER Enabled", SYSMENU_BOOLEAN, SYSMENU_HANDL_CHECK_HAS_ATU, &TRX.TUNER_Enabled, SYSMENU_HANDL_TRX_TUNER_Enabled},
		{"ATU Enabled", SYSMENU_BOOLEAN, SYSMENU_HANDL_CHECK_HAS_ATU, &TRX.ATU_Enabled, SYSMENU_HANDL_TRX_ATU_Enabled},
		{"ATU Ind", SYSMENU_ATU_I, SYSMENU_HANDL_CHECK_HAS_ATU, &TRX.ATU_I, SYSMENU_HANDL_TRX_ATU_I},
		{"ATU Cap", SYSMENU_ATU_C, SYSMENU_HANDL_CHECK_HAS_ATU, &TRX.ATU_C, SYSMENU_HANDL_TRX_ATU_C},
		{"ATU T", SYSMENU_BOOLEAN, SYSMENU_HANDL_CHECK_HAS_ATU, &TRX.ATU_T, SYSMENU_HANDL_TRX_ATU_T},
		{"", SYSMENU_INFOLINE, SYSMENU_HANDL_CHECK_HAS_ATU, NULL},
		{"SWR:", SYSMENU_INFOLINE, SYSMENU_HANDL_CHECK_HAS_ATU, NULL},
		{TRX_SWR_SMOOTHED_STR, SYSMENU_INFOLINE, SYSMENU_HANDL_CHECK_HAS_ATU, NULL},
};

const static struct sysmenu_item_handler sysmenu_audio_handlers[] = {
#if defined(FRONTPANEL_X1) || defined(FRONTPANEL_LITE)
		{"Volume", SYSMENU_UINT8, NULL, &TRX.Volume, SYSMENU_HANDL_AUDIO_Volume},
		{"Volume Step", SYSMENU_UINT8, NULL, &TRX.Volume_Step, SYSMENU_HANDL_AUDIO_Volume_Step},
#endif
    {"IF Gain, dB", SYSMENU_UINT8, NULL, &TRX.IF_Gain, SYSMENU_HANDL_AUDIO_IFGain},
    {"DNR", SYSMENU_ENUM, NULL, &TRX.DNR_shadow, SYSMENU_HANDL_AUDIO_DNR, {"OFF", "DNR1", "DNR2"}},
    {"AGC", SYSMENU_BOOLEAN, NULL, &TRX.AGC_shadow, SYSMENU_HANDL_AUDIO_AGC},
    {"AGC Gain target, LKFS", SYSMENU_INT8, NULL, &TRX.AGC_GAIN_TARGET, SYSMENU_HANDL_AUDIO_AGC_GAIN_TARGET},
    {"Mic Gain, dB", SYSMENU_FLOAT32, NULL, &TRX.MIC_GAIN_DB, SYSMENU_HANDL_AUDIO_MIC_Gain},
    {"Mic Boost", SYSMENU_BOOLEAN, NULL, &TRX.MIC_Boost, SYSMENU_HANDL_AUDIO_MIC_Boost},
    {"MIC Noise Gate", SYSMENU_INT8, NULL, &TRX.MIC_NOISE_GATE, SYSMENU_HANDL_AUDIO_MIC_NOISE_GATE},
    {"DNR1 Threshold", SYSMENU_UINT8, NULL, &TRX.DNR1_SNR_THRESHOLD, SYSMENU_HANDL_AUDIO_DNR1_THRES},
#if !defined(FRONTPANEL_LITE)
		{"DNR2 Threshold", SYSMENU_UINT8, NULL, &TRX.DNR2_SNR_THRESHOLD, SYSMENU_HANDL_AUDIO_DNR2_THRES},
#endif
    {"DNR Average", SYSMENU_UINT8, NULL, &TRX.DNR_AVERAGE, SYSMENU_HANDL_AUDIO_DNR_AVERAGE},
    {"DNR Minimal", SYSMENU_UINT8, NULL, &TRX.DNR_MINIMAL, SYSMENU_HANDL_AUDIO_DNR_MINMAL},
    {"Noise blanker", SYSMENU_BOOLEAN, NULL, &TRX.NOISE_BLANKER, SYSMENU_HANDL_AUDIO_NOISE_BLANKER},
    {"NB Threshold", SYSMENU_UINT8, NULL, &TRX.NOISE_BLANKER_THRESHOLD, SYSMENU_HANDL_AUDIO_NOISE_BLANKER_THRESHOLD},
    {"SSB HPF RX Pass", SYSMENU_UINT16, NULL, &TRX.SSB_HPF_RX_Filter, SYSMENU_HANDL_AUDIO_SSB_HPF_RX_pass},
    {"SSB HPF TX Pass", SYSMENU_UINT16, NULL, &TRX.SSB_HPF_TX_Filter, SYSMENU_HANDL_AUDIO_SSB_HPF_TX_pass},
    {"SSB LPF RX Pass", SYSMENU_UINT16, NULL, &TRX.SSB_LPF_RX_Filter, SYSMENU_HANDL_AUDIO_SSB_LPF_RX_pass},
    {"SSB LPF TX Pass", SYSMENU_UINT16, NULL, &TRX.SSB_LPF_TX_Filter, SYSMENU_HANDL_AUDIO_SSB_LPF_TX_pass},
    {"CW LPF Pass", SYSMENU_UINT16, NULL, &TRX.CW_LPF_Filter, SYSMENU_HANDL_AUDIO_CW_LPF_pass},
    {"DIGI LPF Pass", SYSMENU_UINT16, NULL, &TRX.DIGI_LPF_Filter, SYSMENU_HANDL_AUDIO_DIGI_LPF_pass},
    {"AM LPF RX Pass", SYSMENU_UINT16, NULL, &TRX.AM_LPF_RX_Filter, SYSMENU_HANDL_AUDIO_AM_LPF_RX_pass},
    {"AM LPF TX Pass", SYSMENU_UINT16, NULL, &TRX.AM_LPF_TX_Filter, SYSMENU_HANDL_AUDIO_AM_LPF_TX_pass},
    {"FM LPF RX Pass", SYSMENU_UINT16, NULL, &TRX.FM_LPF_RX_Filter, SYSMENU_HANDL_AUDIO_FM_LPF_RX_pass},
    {"FM LPF TX Pass", SYSMENU_UINT16, NULL, &TRX.FM_LPF_TX_Filter, SYSMENU_HANDL_AUDIO_FM_LPF_TX_pass},
    {"Squelch", SYSMENU_BOOLEAN, NULL, &TRX.SQL_shadow, SYSMENU_HANDL_AUDIO_Squelch},
    {"FM Squelch level, dbm", SYSMENU_INT8, NULL, &TRX.FM_SQL_threshold_dbm_shadow, SYSMENU_HANDL_AUDIO_FMSquelch},
    {"Beeper", SYSMENU_BOOLEAN, NULL, &TRX.Beeper, SYSMENU_HANDL_AUDIO_Beeper},
#if !defined(STM32F407xx)
		{"MIC Reverber", SYSMENU_UINT8, NULL, &TRX.MIC_REVERBER, SYSMENU_HANDL_AUDIO_MIC_REVERBER},
#endif
		{"MIC EQ 0.3k SSB", SYSMENU_INT8, NULL, &TRX.MIC_EQ_P1_SSB, SYSMENU_HANDL_AUDIO_MIC_EQ_P1_SSB},
		{"MIC EQ 0.7k SSB", SYSMENU_INT8, NULL, &TRX.MIC_EQ_P2_SSB, SYSMENU_HANDL_AUDIO_MIC_EQ_P2_SSB},
		{"MIC EQ 1.2k SSB", SYSMENU_INT8, NULL, &TRX.MIC_EQ_P3_SSB, SYSMENU_HANDL_AUDIO_MIC_EQ_P3_SSB},
		{"MIC EQ 1.8k SSB", SYSMENU_INT8, NULL, &TRX.MIC_EQ_P4_SSB, SYSMENU_HANDL_AUDIO_MIC_EQ_P4_SSB},
		{"MIC EQ 2.3k SSB", SYSMENU_INT8, NULL, &TRX.MIC_EQ_P5_SSB, SYSMENU_HANDL_AUDIO_MIC_EQ_P5_SSB},
		{"MIC EQ 0.3k AMFM", SYSMENU_INT8, NULL, &TRX.MIC_EQ_P1_AMFM, SYSMENU_HANDL_AUDIO_MIC_EQ_P1_AMFM},
		{"MIC EQ 0.7k AMFM", SYSMENU_INT8, NULL, &TRX.MIC_EQ_P2_AMFM, SYSMENU_HANDL_AUDIO_MIC_EQ_P2_AMFM},
		{"MIC EQ 1.2k AMFM", SYSMENU_INT8, NULL, &TRX.MIC_EQ_P3_AMFM, SYSMENU_HANDL_AUDIO_MIC_EQ_P3_AMFM},
		{"MIC EQ 1.8k AMFM", SYSMENU_INT8, NULL, &TRX.MIC_EQ_P4_AMFM, SYSMENU_HANDL_AUDIO_MIC_EQ_P4_AMFM},
		{"MIC EQ 2.3k AMFM", SYSMENU_INT8, NULL, &TRX.MIC_EQ_P5_AMFM, SYSMENU_HANDL_AUDIO_MIC_EQ_P5_AMFM},
		{"RX EQ 0.3k", SYSMENU_INT8, NULL, &TRX.RX_EQ_P1, SYSMENU_HANDL_AUDIO_RX_EQ_P1},
		{"RX EQ 0.7k", SYSMENU_INT8, NULL, &TRX.RX_EQ_P2, SYSMENU_HANDL_AUDIO_RX_EQ_P2},
		{"RX EQ 1.2k", SYSMENU_INT8, NULL, &TRX.RX_EQ_P3, SYSMENU_HANDL_AUDIO_RX_EQ_P3},
		{"RX EQ 1.8k", SYSMENU_INT8, NULL, &TRX.RX_EQ_P4, SYSMENU_HANDL_AUDIO_RX_EQ_P4},
		{"RX EQ 2.3k", SYSMENU_INT8, NULL, &TRX.RX_EQ_P5, SYSMENU_HANDL_AUDIO_RX_EQ_P5},
		{"RX AGC SSB Speed", SYSMENU_UINT8, NULL, &TRX.RX_AGC_SSB_speed, SYSMENU_HANDL_AUDIO_RX_AGC_SSB_Speed},
		{"RX AGC CW Speed", SYSMENU_UINT8, NULL, &TRX.RX_AGC_CW_speed, SYSMENU_HANDL_AUDIO_RX_AGC_CW_Speed},
		{"RX AGC Max gain", SYSMENU_UINT8, NULL, &TRX.RX_AGC_Max_gain, SYSMENU_HANDL_AUDIO_RX_AGC_Max_gain},
		{"RX AGC Hold time", SYSMENU_UINT16, NULL, &TRX.RX_AGC_Hold, SYSMENU_HANDL_AUDIO_RX_AGC_Hold},
		{"TX Compr Speed SSB", SYSMENU_UINT8, NULL, &TRX.TX_Compressor_speed_SSB, SYSMENU_HANDL_AUDIO_TX_CompressorSpeed_SSB},
		{"TX Compr MaxGain SSB", SYSMENU_UINT8, NULL, &TRX.TX_Compressor_maxgain_SSB, SYSMENU_HANDL_AUDIO_TX_CompressorMaxGain_SSB},
		{"TX Compr Speed AMFM", SYSMENU_UINT8, NULL, &TRX.TX_Compressor_speed_AMFM, SYSMENU_HANDL_AUDIO_TX_CompressorSpeed_AMFM},
		{"TX Compr MaxGain AMFM", SYSMENU_UINT8, NULL, &TRX.TX_Compressor_maxgain_AMFM, SYSMENU_HANDL_AUDIO_TX_CompressorMaxGain_AMFM},
		{"CTCSS Frequency", SYSMENU_FLOAT32, NULL, &TRX.CTCSS_Freq, SYSMENU_HANDL_AUDIO_CTCSS_Freq},
		{"SelfHear Volume", SYSMENU_UINT8, NULL, &TRX.SELFHEAR_Volume, SYSMENU_HANDL_AUDIO_SELFHEAR_Volume},
#if !defined(STM32F407xx)
		{"WFM Stereo", SYSMENU_BOOLEAN, NULL, &TRX.FM_Stereo, SYSMENU_HANDL_AUDIO_FM_Stereo},
#endif
		{"AGC Spectral", SYSMENU_BOOLEAN, NULL, &TRX.AGC_Spectral, SYSMENU_HANDL_AUDIO_AGC_Spectral},
		{"TX CESSB", SYSMENU_BOOLEAN, NULL, &TRX.TX_CESSB, SYSMENU_HANDL_AUDIO_TX_CESSB},
		{"TX CESSB Compress, dB", SYSMENU_FLOAT32, NULL, &TRX.TX_CESSB_COMPRESS_DB, SYSMENU_HANDL_AUDIO_TX_CESSB_COMPRESS_DB},
		{"VAD Threshold", SYSMENU_UINT8, NULL, &TRX.VAD_THRESHOLD, SYSMENU_HANDL_AUDIO_VAD_THRESHOLD},
		{"VOX", SYSMENU_BOOLEAN, NULL, &TRX.VOX, SYSMENU_HANDL_AUDIO_VOX},
		{"VOX Timeout, ms", SYSMENU_UINT16, NULL, &TRX.VOX_TIMEOUT, SYSMENU_HANDL_AUDIO_VOX_TIMEOUT},
		{"VOX Threshold, dbFS", SYSMENU_INT8, NULL, &TRX.VOX_THRESHOLD, SYSMENU_HANDL_AUDIO_VOX_THRESHOLD},
};

const static struct sysmenu_item_handler sysmenu_cw_handlers[] =
	{
		{"CW Key timeout", SYSMENU_UINT16, NULL, &TRX.CW_Key_timeout, SYSMENU_HANDL_CW_Key_timeout},
		{"CW Pitch", SYSMENU_UINT16, NULL, &TRX.CW_Pitch, SYSMENU_HANDL_CW_Pitch},
		{"CW Self Hear", SYSMENU_BOOLEAN, NULL, &TRX.CW_SelfHear, SYSMENU_HANDL_CW_SelfHear},
		{"CW Keyer", SYSMENU_BOOLEAN, NULL, &TRX.CW_KEYER, SYSMENU_HANDL_CW_Keyer},
		{"CW Keyer WPM", SYSMENU_UINT8, NULL, &TRX.CW_KEYER_WPM, SYSMENU_HANDL_CW_Keyer_WPM},
		{"CW Gauss filter", SYSMENU_BOOLEAN, NULL, &TRX.CW_GaussFilter, SYSMENU_HANDL_CW_GaussFilter},
		{"CW DotToDash Rate", SYSMENU_FLOAT32, NULL, &TRX.CW_DotToDashRate, SYSMENU_HANDL_CW_DotToDashRate},
		{"CW Iambic Keyer", SYSMENU_BOOLEAN, NULL, &TRX.CW_Iambic, SYSMENU_HANDL_CW_Iambic},
		{"CW Key Invert", SYSMENU_BOOLEAN, NULL, &TRX.CW_Invert, SYSMENU_HANDL_CW_Invert},
		{"CW PTT Type", SYSMENU_ENUMR, NULL, &TRX.CW_PTT_Type, SYSMENU_HANDL_CW_PTT_Type, {"Key", "PTT", "KEY+PTT"}},
};

const static struct sysmenu_item_handler sysmenu_screen_handlers[] =
	{
		{"FFT Zoom", SYSMENU_UINT8, NULL, &TRX.FFT_Zoom, SYSMENU_HANDL_SCREEN_FFT_Zoom},
		{"FFT Zoom CW", SYSMENU_UINT8, NULL, &TRX.FFT_ZoomCW, SYSMENU_HANDL_SCREEN_FFT_ZoomCW},
#ifdef HAS_BRIGHTNESS_CONTROL
		{"LCD Brightness", SYSMENU_UINT8, NULL, &TRX.LCD_Brightness, SYSMENU_HANDL_SCREEN_LCD_Brightness},
		{"LCD Sleep Timeout", SYSMENU_UINT16, NULL, &TRX.LCD_SleepTimeout, SYSMENU_HANDL_SCREEN_LCD_SleepTimeout},
#endif
#ifdef LAY_160x128
		{"Color Theme", SYSMENU_ENUMR, NULL, &TRX.ColorThemeId, SYSMENU_HANDL_SCREEN_COLOR_THEME, {"Black", "White", "Colored", "CN", "C+Green", "C+White"}},
#else
		{"Color Theme", SYSMENU_ENUMR, NULL, &TRX.ColorThemeId, SYSMENU_HANDL_SCREEN_COLOR_THEME, {"Black", "White", "Colored", "CN", "CN+Green", "CN+White"}},
#endif
#ifdef LAY_480x320
		{"Layout Theme", SYSMENU_ENUMR, NULL, &TRX.LayoutThemeId, SYSMENU_HANDL_SCREEN_LAYOUT_THEME, {"Default", "7 Segm"}},
#endif
#ifdef LAY_800x480
		{"Layout Theme", SYSMENU_ENUMR, NULL, &TRX.LayoutThemeId, SYSMENU_HANDL_SCREEN_LAYOUT_THEME, {"Default", "Analog", "7 Segm", "Classic", "Default+", "Analog+", "CN", "CN+"}},
#endif
		{"FFT Speed", SYSMENU_UINT8, NULL, &TRX.FFT_Speed, SYSMENU_HANDL_SCREEN_FFT_Speed},
		{"FFT Automatic", SYSMENU_BOOLEAN, NULL, &TRX.FFT_Automatic, SYSMENU_HANDL_SCREEN_FFT_Automatic},
		{"FFT Scale Type", SYSMENU_ENUM, NULL, &TRX.FFT_Scale_Type, SYSMENU_HANDL_SCREEN_FFT_Scale_Type, {"Ampl", "Squared", "dBm"}},
		{"FFT Sensitivity", SYSMENU_UINT8, NULL, &TRX.FFT_Sensitivity, SYSMENU_HANDL_SCREEN_FFT_Sensitivity},
		{"FFT Manual Bottom, dBm", SYSMENU_INT16, NULL, &TRX.FFT_ManualBottom, SYSMENU_HANDL_SCREEN_FFT_ManualBottom},
		{"FFT Manual Top, dBm", SYSMENU_INT16, NULL, &TRX.FFT_ManualTop, SYSMENU_HANDL_SCREEN_FFT_ManualTop},
		{"FFT Height", SYSMENU_UINT8, NULL, &TRX.FFT_Height, SYSMENU_HANDL_SCREEN_FFT_Height},
		{"FFT Style", SYSMENU_ENUMR, NULL, &TRX.FFT_Style, SYSMENU_HANDL_SCREEN_FFT_Style, {"", "Gradien", "Fill", "Dots", "Contour"}},
#if !defined(FRONTPANEL_LITE)
		{"FFT BW Style", SYSMENU_ENUMR, NULL, &TRX.FFT_BW_Style, SYSMENU_HANDL_SCREEN_FFT_BW_Style, {"", "Fill", "LowOp", "Line"}},
#endif
    {"FFT Color",
     SYSMENU_ENUMR,
     NULL,
     &TRX.FFT_Color,
     SYSMENU_HANDL_SCREEN_FFT_Color,
     {"Blu>Y>R", "BlB>Y>R", "BlR>Y>R", "BGYRM", "Bla>Y>R", "Bla>Y>G", "Bla>R", "Bla>G", "Bla>Blu", "Bla>W"}},
    {"WTF Color",
     SYSMENU_ENUMR,
     NULL,
     &TRX.WTF_Color,
     SYSMENU_HANDL_SCREEN_WTF_Color,
     {"Blu>Y>R", "BlB>Y>R", "BlR>Y>R", "BGYRM", "Bla>Y>R", "Bla>Y>G", "Bla>R", "Bla>G", "Bla>Blu", "Bla>W"}},
    {"FFT Freq Grid", SYSMENU_ENUM, NULL, (uint32_t *)&TRX.FFT_FreqGrid, SYSMENU_HANDL_SCREEN_FFT_FreqGrid, {"NO", "Top", "All", "Bott"}},
#if !defined(FRONTPANEL_LITE)
		{"FFT dBm Grid", SYSMENU_BOOLEAN, NULL, &TRX.FFT_dBmGrid, SYSMENU_HANDL_SCREEN_FFT_dBmGrid},
#endif
		{"FFT Background", SYSMENU_BOOLEAN, NULL, &TRX.FFT_Background, SYSMENU_HANDL_SCREEN_FFT_Background},
#if !defined(FRONTPANEL_LITE)
		{"FFT Lens", SYSMENU_BOOLEAN, NULL, &TRX.FFT_Lens, SYSMENU_HANDL_SCREEN_FFT_Lens},
		{"FFT Hold Peaks", SYSMENU_BOOLEAN, NULL, &TRX.FFT_HoldPeaks, SYSMENU_HANDL_SCREEN_FFT_HoldPeaks},
		{"FFT 3D Mode", SYSMENU_ENUM, NULL, &TRX.FFT_3D, SYSMENU_HANDL_SCREEN_FFT_3D, {"NO", "Lines", "Dots"}},
#endif
		{"FFT Enabled", SYSMENU_BOOLEAN, NULL, &TRX.FFT_Enabled, SYSMENU_HANDL_SCREEN_FFT_Enabled},
		{"WTF Moving", SYSMENU_BOOLEAN, NULL, &TRX.WTF_Moving, SYSMENU_HANDL_SCREEN_WTF_Moving},
		{"FFT Compressor", SYSMENU_BOOLEAN, NULL, &TRX.FFT_Compressor, SYSMENU_HANDL_SCREEN_FFT_Compressor},
		{"FFT Averaging", SYSMENU_UINT8, NULL, &TRX.FFT_Averaging, SYSMENU_HANDL_SCREEN_FFT_Averaging},
		{"FFT Window", SYSMENU_ENUMR, NULL, &TRX.FFT_Window, SYSMENU_HANDL_SCREEN_FFT_Window, {"", "Dolph", "Blckman", "Nutall", "BlNutll", "Hann", "Hamming", "No"}},
#if HRDW_HAS_WIFI
		{"FFT DXCluster", SYSMENU_BOOLEAN, NULL, &TRX.FFT_DXCluster, SYSMENU_HANDL_SCREEN_FFT_DXCluster},
		{"FFT DXCluster Azimuth", SYSMENU_BOOLEAN, NULL, &TRX.FFT_DXCluster_Azimuth, SYSMENU_HANDL_SCREEN_FFT_DXCluster_Azimuth},
		{"FFT DXCluster Timeout", SYSMENU_UINT8, NULL, &TRX.FFT_DXCluster_Timeout, SYSMENU_HANDL_SCREEN_FFT_DXCluster_Timeout},
#endif
#if !defined(FRONTPANEL_LITE)
		{"Show Sec VFO", SYSMENU_BOOLEAN, NULL, &TRX.Show_Sec_VFO, SYSMENU_HANDL_SCREEN_Show_Sec_VFO},
#endif
#ifdef HRDW_HAS_FUNCBUTTONS
		{"Func button 1", SYSMENU_FUNCBUTTON, NULL, &TRX.FuncButtons[0], SYSMENU_HANDL_SCREEN_FUNC_BUTTON1},
		{"Func button 2", SYSMENU_FUNCBUTTON, NULL, &TRX.FuncButtons[1], SYSMENU_HANDL_SCREEN_FUNC_BUTTON2},
		{"Func button 3", SYSMENU_FUNCBUTTON, NULL, &TRX.FuncButtons[2], SYSMENU_HANDL_SCREEN_FUNC_BUTTON3},
		{"Func button 4", SYSMENU_FUNCBUTTON, NULL, &TRX.FuncButtons[3], SYSMENU_HANDL_SCREEN_FUNC_BUTTON4},
		{"Func button 5", SYSMENU_FUNCBUTTON, NULL, &TRX.FuncButtons[4], SYSMENU_HANDL_SCREEN_FUNC_BUTTON5},
		{"Func button 6", SYSMENU_FUNCBUTTON, NULL, &TRX.FuncButtons[5], SYSMENU_HANDL_SCREEN_FUNC_BUTTON6},
		{"Func button 7", SYSMENU_FUNCBUTTON, NULL, &TRX.FuncButtons[6], SYSMENU_HANDL_SCREEN_FUNC_BUTTON7},
		{"Func button 8", SYSMENU_FUNCBUTTON, NULL, &TRX.FuncButtons[7], SYSMENU_HANDL_SCREEN_FUNC_BUTTON8},
		{"Func button 9", SYSMENU_FUNCBUTTON, NULL, &TRX.FuncButtons[8], SYSMENU_HANDL_SCREEN_FUNC_BUTTON9},
		{"Func button 10", SYSMENU_FUNCBUTTON, NULL, &TRX.FuncButtons[9], SYSMENU_HANDL_SCREEN_FUNC_BUTTON10},
		{"Func button 11", SYSMENU_FUNCBUTTON, NULL, &TRX.FuncButtons[10], SYSMENU_HANDL_SCREEN_FUNC_BUTTON11},
		{"Func button 12", SYSMENU_FUNCBUTTON, NULL, &TRX.FuncButtons[11], SYSMENU_HANDL_SCREEN_FUNC_BUTTON12},
		{"Func button 13", SYSMENU_FUNCBUTTON, NULL, &TRX.FuncButtons[12], SYSMENU_HANDL_SCREEN_FUNC_BUTTON13},
		{"Func button 14", SYSMENU_FUNCBUTTON, NULL, &TRX.FuncButtons[13], SYSMENU_HANDL_SCREEN_FUNC_BUTTON14},
		{"Func button 15", SYSMENU_FUNCBUTTON, NULL, &TRX.FuncButtons[14], SYSMENU_HANDL_SCREEN_FUNC_BUTTON15},
		{"Func button 16", SYSMENU_FUNCBUTTON, NULL, &TRX.FuncButtons[15], SYSMENU_HANDL_SCREEN_FUNC_BUTTON16},
		{"Func button 17", SYSMENU_FUNCBUTTON, NULL, &TRX.FuncButtons[16], SYSMENU_HANDL_SCREEN_FUNC_BUTTON17},
		{"Func button 18", SYSMENU_FUNCBUTTON, NULL, &TRX.FuncButtons[17], SYSMENU_HANDL_SCREEN_FUNC_BUTTON18},
		{"Func button 19", SYSMENU_FUNCBUTTON, NULL, &TRX.FuncButtons[18], SYSMENU_HANDL_SCREEN_FUNC_BUTTON19},
		{"Func button 20", SYSMENU_FUNCBUTTON, NULL, &TRX.FuncButtons[19], SYSMENU_HANDL_SCREEN_FUNC_BUTTON20},
		{"Func button 21", SYSMENU_FUNCBUTTON, NULL, &TRX.FuncButtons[20], SYSMENU_HANDL_SCREEN_FUNC_BUTTON21},
		{"Func button 22", SYSMENU_FUNCBUTTON, NULL, &TRX.FuncButtons[21], SYSMENU_HANDL_SCREEN_FUNC_BUTTON22},
		{"Func button 23", SYSMENU_FUNCBUTTON, NULL, &TRX.FuncButtons[22], SYSMENU_HANDL_SCREEN_FUNC_BUTTON23},
		{"Func button 24", SYSMENU_FUNCBUTTON, NULL, &TRX.FuncButtons[23], SYSMENU_HANDL_SCREEN_FUNC_BUTTON24},
		{"Func button 25", SYSMENU_FUNCBUTTON, NULL, &TRX.FuncButtons[24], SYSMENU_HANDL_SCREEN_FUNC_BUTTON25},
#if (FUNCBUTTONS_ON_PAGE * FUNCBUTTONS_PAGES) > 25
		{"Func button 26", SYSMENU_FUNCBUTTON, NULL, &TRX.FuncButtons[25], SYSMENU_HANDL_SCREEN_FUNC_BUTTON26},
		{"Func button 27", SYSMENU_FUNCBUTTON, NULL, &TRX.FuncButtons[26], SYSMENU_HANDL_SCREEN_FUNC_BUTTON27},
#if (FUNCBUTTONS_ON_PAGE * FUNCBUTTONS_PAGES) > 27
		{"Func button 28", SYSMENU_FUNCBUTTON, NULL, &TRX.FuncButtons[27], SYSMENU_HANDL_SCREEN_FUNC_BUTTON28},
		{"Func button 29", SYSMENU_FUNCBUTTON, NULL, &TRX.FuncButtons[28], SYSMENU_HANDL_SCREEN_FUNC_BUTTON29},
		{"Func button 30", SYSMENU_FUNCBUTTON, NULL, &TRX.FuncButtons[29], SYSMENU_HANDL_SCREEN_FUNC_BUTTON30},
#if (FUNCBUTTONS_ON_PAGE * FUNCBUTTONS_PAGES) > 30
		{"Func button 31", SYSMENU_FUNCBUTTON, NULL, &TRX.FuncButtons[30], SYSMENU_HANDL_SCREEN_FUNC_BUTTON31},
		{"Func button 32", SYSMENU_FUNCBUTTON, NULL, &TRX.FuncButtons[31], SYSMENU_HANDL_SCREEN_FUNC_BUTTON32},
#endif
#endif
#endif
#endif
};

const static struct sysmenu_item_handler sysmenu_decoders_handlers[] =
	{
		#if !defined(FRONTPANEL_LITE)
		{"CW Decoder", SYSMENU_BOOLEAN, NULL, &TRX.CW_Decoder, SYSMENU_HANDL_DECODERS_CW_Decoder},
		{"CW Decoder Threshold", SYSMENU_UINT8, NULL, &TRX.CW_Decoder_Threshold, SYSMENU_HANDL_DECODERS_CW_Decoder_Threshold},
		{"RDS Decoder", SYSMENU_BOOLEAN, NULL, &TRX.RDS_Decoder, SYSMENU_HANDL_DECODERS_RDS_Decoder},
		#endif
		{"RTTY Speed", SYSMENU_UINT16, NULL, &TRX.RTTY_Speed, SYSMENU_HANDL_DECODERS_RTTY_Speed},
		{"RTTY Shift", SYSMENU_UINT16, NULL, &TRX.RTTY_Shift, SYSMENU_HANDL_DECODERS_RTTY_Shift},
		{"RTTY Freq", SYSMENU_UINT16, NULL, &TRX.RTTY_Freq, SYSMENU_HANDL_DECODERS_RTTY_Freq},
		{"RTTY StopBits", SYSMENU_ENUM, NULL, &TRX.RTTY_StopBits, SYSMENU_HANDL_DECODERS_RTTY_StopBits, {"1", "1.5", "2"}},
		{"RTTY InvertBits", SYSMENU_BOOLEAN, NULL, &TRX.RTTY_InvertBits, SYSMENU_HANDL_DECODERS_RTTY_InvertBits},
};

const static struct sysmenu_item_handler sysmenu_adc_handlers[] =
	{
		{"ADC Driver", SYSMENU_BOOLEAN, NULL, &TRX.ADC_Driver, SYSMENU_HANDL_ADC_DRIVER},
		#if !defined(FRONTPANEL_LITE)
		{"ADC Preamp", SYSMENU_BOOLEAN, NULL, &TRX.ADC_PGA, SYSMENU_HANDL_ADC_PGA},
		{"ADC Dither", SYSMENU_BOOLEAN, NULL, &TRX.ADC_DITH, SYSMENU_HANDL_ADC_DITH},
		{"ADC Randomizer", SYSMENU_BOOLEAN, NULL, &TRX.ADC_RAND, SYSMENU_HANDL_ADC_RAND},
		#endif
		{"ADC Shutdown", SYSMENU_BOOLEAN, NULL, &TRX.ADC_SHDN, SYSMENU_HANDL_ADC_SHDN},
};

#if HRDW_HAS_WIFI
const static struct sysmenu_item_handler sysmenu_wifi_handlers[] =
	{
		{"WIFI Enabled", SYSMENU_BOOLEAN, NULL, &WIFI.Enabled, SYSMENU_HANDL_WIFI_Enabled},
		{"WIFI Network 1", SYSMENU_RUN, NULL, NULL, SYSMENU_HANDL_WIFI_SelectAP1},
		{"WIFI Network 1 Pass", SYSMENU_RUN, NULL, NULL, SYSMENU_HANDL_WIFI_SetAP1password},
		{"WIFI Network 2", SYSMENU_RUN, NULL, NULL, SYSMENU_HANDL_WIFI_SelectAP2},
		{"WIFI Network 2 Pass", SYSMENU_RUN, NULL, NULL, SYSMENU_HANDL_WIFI_SetAP2password},
		{"WIFI Network 3", SYSMENU_RUN, NULL, NULL, SYSMENU_HANDL_WIFI_SelectAP3},
		{"WIFI Network 3 Pass", SYSMENU_RUN, NULL, NULL, SYSMENU_HANDL_WIFI_SetAP3password},
		{"WIFI Timezone", SYSMENU_INT8, NULL, &WIFI.Timezone, SYSMENU_HANDL_WIFI_Timezone},
		{"WIFI CAT Server", SYSMENU_BOOLEAN, NULL, &WIFI.CAT_Server, SYSMENU_HANDL_WIFI_CAT_Server},
		{"WIFI Update ESP firmware", SYSMENU_RUN, NULL, NULL, SYSMENU_HANDL_WIFI_UpdateFW},
		{"", SYSMENU_INFOLINE, NULL, NULL},
		{"NET:", SYSMENU_INFOLINE, NULL, NULL},
		{WIFI_AP, SYSMENU_INFOLINE, NULL, NULL},
		{"", SYSMENU_INFOLINE, NULL, NULL},
		{"IP:", SYSMENU_INFOLINE, NULL, NULL},
		{WIFI_IP, SYSMENU_INFOLINE, NULL, NULL},
};
#endif

#if HRDW_HAS_SD
const static struct sysmenu_item_handler sysmenu_sd_handlers[] =
	{
		{"File Manager", SYSMENU_RUN, NULL, 0, SYSMENU_HANDL_SD_Filemanager},
		{"USB SD Card Reader", SYSMENU_BOOLEAN, NULL, &SD_USBCardReader, SYSMENU_HANDL_SD_USB},
		{"Export Settings to SD", SYSMENU_RUN, NULL, 0, SYSMENU_HANDL_SD_ExportSettingsDialog},
		{"Import Settings from SD", SYSMENU_RUN, NULL, 0, SYSMENU_HANDL_SD_ImportSettingsDialog},
		{"Format SD card", SYSMENU_RUN, NULL, 0, SYSMENU_HANDL_SD_FormatDialog},
};

const static struct sysmenu_item_handler sysmenu_sd_export_handlers[] =
	{
		{"Back", SYSMENU_RUN, NULL, NULL, SYSMENU_HANDL_Back},
		{"Yes, Export Settings", SYSMENU_RUN, NULL, NULL, SYSMENU_HANDL_SD_ExportSettings},
};

const static struct sysmenu_item_handler sysmenu_sd_import_handlers[] =
	{
		{"Back", SYSMENU_RUN, NULL, NULL, SYSMENU_HANDL_Back},
		{"Yes, Import Settings", SYSMENU_RUN, NULL, NULL, SYSMENU_HANDL_SD_ImportSettings},
};
const static struct sysmenu_item_handler sysmenu_sd_format_handlers[] =
	{
		{"Back", SYSMENU_RUN, NULL, NULL, SYSMENU_HANDL_Back},
		{"Yes, Format SD Card", SYSMENU_RUN, NULL, NULL, SYSMENU_HANDL_SD_Format},
};
#endif

const static struct sysmenu_item_handler sysmenu_calibration_handlers[] =
	{
		{"Encoder invert", SYSMENU_BOOLEAN, NULL, &CALIBRATE.ENCODER_INVERT, SYSMENU_HANDL_CALIB_ENCODER_INVERT},
		{"Encoder2 invert", SYSMENU_BOOLEAN, NULL, &CALIBRATE.ENCODER2_INVERT, SYSMENU_HANDL_CALIB_ENCODER2_INVERT},
		{"Encoder debounce", SYSMENU_UINT8, NULL, &CALIBRATE.ENCODER_DEBOUNCE, SYSMENU_HANDL_CALIB_ENCODER_DEBOUNCE},
		{"Encoder2 debounce", SYSMENU_UINT8, NULL, &CALIBRATE.ENCODER2_DEBOUNCE, SYSMENU_HANDL_CALIB_ENCODER2_DEBOUNCE},
		{"Encoder slow rate", SYSMENU_UINT8, NULL, &CALIBRATE.ENCODER_SLOW_RATE, SYSMENU_HANDL_CALIB_ENCODER_SLOW_RATE},
		{"Encoder on falling", SYSMENU_BOOLEAN, NULL, &CALIBRATE.ENCODER_ON_FALLING, SYSMENU_HANDL_CALIB_ENCODER_ON_FALLING},
		{"Encoder acceleration", SYSMENU_UINT8, NULL, &CALIBRATE.ENCODER_ACCELERATION, SYSMENU_HANDL_CALIB_ENCODER_ACCELERATION},
#if !defined(FRONTPANEL_LITE)
		{"RF-Unit Type", SYSMENU_ENUM, NULL, &CALIBRATE.RF_unit_type, SYSMENU_HANDL_CALIB_RF_unit_type, {"NONE", "QRP", "BIG", "SPLIT", "RU4PN", "LZ1HAA","WF-100D"}},
#endif
#if defined(FRONTPANEL_BIG_V1) || defined(FRONTPANEL_WF_100D)
		{"Tangent Type", SYSMENU_ENUM, NULL, &CALIBRATE.TangentType, SYSMENU_HANDL_CALIB_TangentType, {"MH-36", "MH-48"}},
#endif
		{"CICCOMP 48K Shift", SYSMENU_UINT8, NULL, &CALIBRATE.CICFIR_GAINER_48K_val, SYSMENU_HANDL_CALIB_CICCOMP_48K_SHIFT},
		{"CICCOMP 96K Shift", SYSMENU_UINT8, NULL, &CALIBRATE.CICFIR_GAINER_96K_val, SYSMENU_HANDL_CALIB_CICCOMP_96K_SHIFT},
		{"CICCOMP 192K Shift", SYSMENU_UINT8, NULL, &CALIBRATE.CICFIR_GAINER_192K_val, SYSMENU_HANDL_CALIB_CICCOMP_192K_SHIFT},
		{"CICCOMP 384K Shift", SYSMENU_UINT8, NULL, &CALIBRATE.CICFIR_GAINER_384K_val, SYSMENU_HANDL_CALIB_CICCOMP_384K_SHIFT},
		{"TX CICCOMP Shift", SYSMENU_UINT8, NULL, &CALIBRATE.TXCICFIR_GAINER_val, SYSMENU_HANDL_CALIB_TXCICCOMP_SHIFT},
		{"DAC Shift", SYSMENU_UINT8, NULL, &CALIBRATE.DAC_GAINER_val, SYSMENU_HANDL_CALIB_DAC_SHIFT},
#if !defined(FRONTPANEL_LITE)
		{"DAC Driver Mode", SYSMENU_UINT8, NULL, &CALIBRATE.DAC_driver_mode, SYSMENU_HANDL_CALIB_DAC_driver_mode},
#endif
		{"RF GAIN 2200m", SYSMENU_UINT8, NULL, &CALIBRATE.rf_out_power_2200m, SYSMENU_HANDL_CALIB_RF_GAIN_2200M},
		{"RF GAIN 160m", SYSMENU_UINT8, NULL, &CALIBRATE.rf_out_power_160m, SYSMENU_HANDL_CALIB_RF_GAIN_160M},
		{"RF GAIN 80m", SYSMENU_UINT8, NULL, &CALIBRATE.rf_out_power_80m, SYSMENU_HANDL_CALIB_RF_GAIN_80M},
		{"RF GAIN 40m", SYSMENU_UINT8, NULL, &CALIBRATE.rf_out_power_40m, SYSMENU_HANDL_CALIB_RF_GAIN_40M},
		{"RF GAIN 30m", SYSMENU_UINT8, NULL, &CALIBRATE.rf_out_power_30m, SYSMENU_HANDL_CALIB_RF_GAIN_30M},
		{"RF GAIN 20m", SYSMENU_UINT8, NULL, &CALIBRATE.rf_out_power_20m, SYSMENU_HANDL_CALIB_RF_GAIN_20M},
		{"RF GAIN 17m", SYSMENU_UINT8, NULL, &CALIBRATE.rf_out_power_17m, SYSMENU_HANDL_CALIB_RF_GAIN_17M},
		{"RF GAIN 15m", SYSMENU_UINT8, NULL, &CALIBRATE.rf_out_power_15m, SYSMENU_HANDL_CALIB_RF_GAIN_15M},
		{"RF GAIN 12m", SYSMENU_UINT8, NULL, &CALIBRATE.rf_out_power_12m, SYSMENU_HANDL_CALIB_RF_GAIN_12M},
		{"RF GAIN CB", SYSMENU_UINT8, NULL, &CALIBRATE.rf_out_power_cb, SYSMENU_HANDL_CALIB_RF_GAIN_CB},
		{"RF GAIN 10m", SYSMENU_UINT8, NULL, &CALIBRATE.rf_out_power_10m, SYSMENU_HANDL_CALIB_RF_GAIN_10M},
#if !defined(FRONTPANEL_LITE)
		{"RF GAIN 6m", SYSMENU_UINT8, NULL, &CALIBRATE.rf_out_power_6m, SYSMENU_HANDL_CALIB_RF_GAIN_6M},
		{"RF GAIN 4m", SYSMENU_UINT8, NULL, &CALIBRATE.rf_out_power_4m, SYSMENU_HANDL_CALIB_RF_GAIN_4M},
		{"RF GAIN 2m", SYSMENU_UINT8, NULL, &CALIBRATE.rf_out_power_2m, SYSMENU_HANDL_CALIB_RF_GAIN_2M},
#endif
		{"S METER HF", SYSMENU_INT16, NULL, &CALIBRATE.smeter_calibration_hf, SYSMENU_HANDL_CALIB_S_METER_HF},
		{"S METER VHF", SYSMENU_INT16, NULL, &CALIBRATE.smeter_calibration_vhf, SYSMENU_HANDL_CALIB_S_METER_VHF},
		{"ADC OFFSET", SYSMENU_INT16, NULL, &CALIBRATE.adc_offset, SYSMENU_HANDL_CALIB_ADC_OFFSET},
#if !defined(FRONTPANEL_LITE)
		{"LPF END", SYSMENU_UINT32, SYSMENU_HANDL_CHECK_HAS_LPF, &CALIBRATE.RFU_LPF_END, SYSMENU_HANDL_CALIB_LPF_END},
		{"HPF START", SYSMENU_UINT32, SYSMENU_HANDL_CHECK_HAS_HPF, &CALIBRATE.RFU_HPF_START, SYSMENU_HANDL_CALIB_HPF_START},
		{"BPF 0 START", SYSMENU_UINT32, NULL, &CALIBRATE.RFU_BPF_0_START, SYSMENU_HANDL_CALIB_BPF_0_START},
		{"BPF 0 END", SYSMENU_UINT32, NULL, &CALIBRATE.RFU_BPF_0_END, SYSMENU_HANDL_CALIB_BPF_0_END},
		{"BPF 1 START", SYSMENU_UINT32, NULL, &CALIBRATE.RFU_BPF_1_START, SYSMENU_HANDL_CALIB_BPF_1_START},
		{"BPF 1 END", SYSMENU_UINT32, NULL, &CALIBRATE.RFU_BPF_1_END, SYSMENU_HANDL_CALIB_BPF_1_END},
		{"BPF 2 START", SYSMENU_UINT32, NULL, &CALIBRATE.RFU_BPF_2_START, SYSMENU_HANDL_CALIB_BPF_2_START},
		{"BPF 2 END", SYSMENU_UINT32, NULL, &CALIBRATE.RFU_BPF_2_END, SYSMENU_HANDL_CALIB_BPF_2_END},
		{"BPF 3 START", SYSMENU_UINT32, NULL, &CALIBRATE.RFU_BPF_3_START, SYSMENU_HANDL_CALIB_BPF_3_START},
		{"BPF 3 END", SYSMENU_UINT32, NULL, &CALIBRATE.RFU_BPF_3_END, SYSMENU_HANDL_CALIB_BPF_3_END},
		{"BPF 4 START", SYSMENU_UINT32, NULL, &CALIBRATE.RFU_BPF_4_START, SYSMENU_HANDL_CALIB_BPF_4_START},
		{"BPF 4 END", SYSMENU_UINT32, NULL, &CALIBRATE.RFU_BPF_4_END, SYSMENU_HANDL_CALIB_BPF_4_END},
		{"BPF 5 START", SYSMENU_UINT32, NULL, &CALIBRATE.RFU_BPF_5_START, SYSMENU_HANDL_CALIB_BPF_5_START},
		{"BPF 5 END", SYSMENU_UINT32, NULL, &CALIBRATE.RFU_BPF_5_END, SYSMENU_HANDL_CALIB_BPF_5_END},
		{"BPF 6 START", SYSMENU_UINT32, NULL, &CALIBRATE.RFU_BPF_6_START, SYSMENU_HANDL_CALIB_BPF_6_START},
		{"BPF 6 END", SYSMENU_UINT32, NULL, &CALIBRATE.RFU_BPF_6_END, SYSMENU_HANDL_CALIB_BPF_6_END},
		{"BPF 7 START", SYSMENU_UINT32, SYSMENU_HANDL_CHECK_HAS_BPF_8, &CALIBRATE.RFU_BPF_7_START, SYSMENU_HANDL_CALIB_BPF_7_START},
		{"BPF 7 END", SYSMENU_UINT32, SYSMENU_HANDL_CHECK_HAS_BPF_8, &CALIBRATE.RFU_BPF_7_END, SYSMENU_HANDL_CALIB_BPF_7_END},
		{"BPF 8 START", SYSMENU_UINT32, SYSMENU_HANDL_CHECK_HAS_BPF_9, &CALIBRATE.RFU_BPF_8_START, SYSMENU_HANDL_CALIB_BPF_8_START},
		{"BPF 8 END", SYSMENU_UINT32, SYSMENU_HANDL_CHECK_HAS_BPF_9, &CALIBRATE.RFU_BPF_8_END, SYSMENU_HANDL_CALIB_BPF_8_END},
        {"BPF 9 START", SYSMENU_UINT32, SYSMENU_HANDL_CHECK_HAS_BPF_10, &CALIBRATE.RFU_BPF_9_START, SYSMENU_HANDL_CALIB_BPF_9_START},
        {"BPF 9 END", SYSMENU_UINT32, SYSMENU_HANDL_CHECK_HAS_BPF_10, &CALIBRATE.RFU_BPF_9_END, SYSMENU_HANDL_CALIB_BPF_9_END},
#endif
		{"MAX PWR on Meter", SYSMENU_UINT8, NULL, &CALIBRATE.MAX_RF_POWER_ON_METER, SYSMENU_HANDL_CALIB_MAX_RF_POWER_ON_METER},
		{"MAX Power in TUNE", SYSMENU_UINT8, NULL, &CALIBRATE.TUNE_MAX_POWER, SYSMENU_HANDL_CALIB_TUNE_MAX_POWER},
		{"SSB Power addition", SYSMENU_UINT8, NULL, &CALIBRATE.SSB_POWER_ADDITION, SYSMENU_HANDL_CALIB_SSB_POWER_ADDITION},
		{"SWR FWD RATE HF", SYSMENU_FLOAT32, NULL, &CALIBRATE.SWR_FWD_Calibration_HF, SYSMENU_HANDL_CALIB_SWR_FWD_RATE_HF},
		{"SWR BWD RATE HF", SYSMENU_FLOAT32, NULL, &CALIBRATE.SWR_BWD_Calibration_HF, SYSMENU_HANDL_CALIB_SWR_REF_RATE_HF},
#if !defined(FRONTPANEL_LITE)
		{"SWR FWD RATE 6M", SYSMENU_FLOAT32, NULL, &CALIBRATE.SWR_FWD_Calibration_6M, SYSMENU_HANDL_CALIB_SWR_FWD_RATE_6M},
		{"SWR BWD RATE 6M", SYSMENU_FLOAT32, NULL, &CALIBRATE.SWR_BWD_Calibration_6M, SYSMENU_HANDL_CALIB_SWR_REF_RATE_6M},
		{"SWR FWD RATE VHF", SYSMENU_FLOAT32, NULL, &CALIBRATE.SWR_FWD_Calibration_VHF, SYSMENU_HANDL_CALIB_SWR_FWD_RATE_VHF},
		{"SWR BWD RATE VHF", SYSMENU_FLOAT32, NULL, &CALIBRATE.SWR_BWD_Calibration_VHF, SYSMENU_HANDL_CALIB_SWR_REF_RATE_VHF},
#endif
		{"VCXO Correction", SYSMENU_INT16, NULL, &CALIBRATE.VCXO_correction, SYSMENU_HANDL_CALIB_VCXO},
#ifdef SWR_AD8307_LOG
		{"FW_AD8307_Slope (mv/dB)", SYSMENU_FLOAT32, NULL, &CALIBRATE.FW_AD8307_SLP, SYSMENU_HANDL_CALIB_FW_AD8307_SLP},
		{"FW_AD8307_Offset (mV)", SYSMENU_FLOAT32, NULL, &CALIBRATE.FW_AD8307_OFFS, SYSMENU_HANDL_CALIB_FW_AD8307_OFFS},
		{"BW_AD8307_Slope (mv/dB)", SYSMENU_FLOAT32, NULL, &CALIBRATE.BW_AD8307_SLP, SYSMENU_HANDL_CALIB_BW_AD8307_SLP},
		{"BW_AD8307_Offset (mV)", SYSMENU_FLOAT32, NULL, &CALIBRATE.BW_AD8307_OFFS, SYSMENU_HANDL_CALIB_BW_AD8307_OFFS},
#endif
#if !defined(FRONTPANEL_LITE)
		{"FAN Medium start", SYSMENU_UINT8, NULL, &CALIBRATE.FAN_MEDIUM_START, SYSMENU_HANDL_CALIB_FAN_MEDIUM_START},
		{"FAN Medium stop", SYSMENU_UINT8, NULL, &CALIBRATE.FAN_MEDIUM_STOP, SYSMENU_HANDL_CALIB_FAN_MEDIUM_STOP},
		{"FAN Full start", SYSMENU_UINT8, NULL, &CALIBRATE.FAN_FULL_START, SYSMENU_HANDL_CALIB_FAN_FULL_START},
		{"MAX RF Temp", SYSMENU_UINT8, NULL, &CALIBRATE.TRX_MAX_RF_TEMP, SYSMENU_HANDL_CALIB_TRX_MAX_RF_TEMP},
#endif
		{"MAX SWR", SYSMENU_UINT8, NULL, &CALIBRATE.TRX_MAX_SWR, SYSMENU_HANDL_CALIB_TRX_MAX_SWR},
		{"FM Deviation Scale", SYSMENU_UINT8, NULL, &CALIBRATE.FM_DEVIATION_SCALE, SYSMENU_HANDL_CALIB_FM_DEVIATION_SCALE},
		{"AM Modulation Index", SYSMENU_UINT8, NULL, &CALIBRATE.AM_MODULATION_INDEX, SYSMENU_HANDL_CALIB_AM_MODULATION_INDEX},
		{"RTC COARSE CALIBR", SYSMENU_UINT8, NULL, &CALIBRATE.RTC_Coarse_Calibration, SYSMENU_HANDL_CALIB_RTC_COARSE_CALIBRATION},
		{"RTC FINE CALIBR", SYSMENU_INT16, NULL, &CALIBRATE.RTC_Calibration, SYSMENU_HANDL_CALIB_RTC_CALIBRATION},
#if !defined(FRONTPANEL_LITE)
		{"EXT 2200m", SYSMENU_B4, NULL, &CALIBRATE.EXT_2200m, SYSMENU_HANDL_CALIB_EXT_2200m},
		{"EXT 160m", SYSMENU_B4, NULL, &CALIBRATE.EXT_160m, SYSMENU_HANDL_CALIB_EXT_160m},
		{"EXT 80m", SYSMENU_B4, NULL, &CALIBRATE.EXT_80m, SYSMENU_HANDL_CALIB_EXT_80m},
		{"EXT 60m", SYSMENU_B4, NULL, &CALIBRATE.EXT_60m, SYSMENU_HANDL_CALIB_EXT_60m},
		{"EXT 40m", SYSMENU_B4, NULL, &CALIBRATE.EXT_40m, SYSMENU_HANDL_CALIB_EXT_40m},
		{"EXT 30m", SYSMENU_B4, NULL, &CALIBRATE.EXT_30m, SYSMENU_HANDL_CALIB_EXT_30m},
		{"EXT 20m", SYSMENU_B4, NULL, &CALIBRATE.EXT_20m, SYSMENU_HANDL_CALIB_EXT_20m},
		{"EXT 17m", SYSMENU_B4, NULL, &CALIBRATE.EXT_17m, SYSMENU_HANDL_CALIB_EXT_17m},
		{"EXT 15m", SYSMENU_B4, NULL, &CALIBRATE.EXT_15m, SYSMENU_HANDL_CALIB_EXT_15m},
		{"EXT 12m", SYSMENU_B4, NULL, &CALIBRATE.EXT_12m, SYSMENU_HANDL_CALIB_EXT_12m},
		{"EXT CB", SYSMENU_B4, NULL, &CALIBRATE.EXT_CB, SYSMENU_HANDL_CALIB_EXT_CB},
		{"EXT 10m", SYSMENU_B4, NULL, &CALIBRATE.EXT_10m, SYSMENU_HANDL_CALIB_EXT_10m},
		{"EXT 6m", SYSMENU_B4, NULL, &CALIBRATE.EXT_6m, SYSMENU_HANDL_CALIB_EXT_6m},
		{"EXT 4m", SYSMENU_B4, NULL, &CALIBRATE.EXT_4m, SYSMENU_HANDL_CALIB_EXT_4m},
		{"EXT FM", SYSMENU_B4, NULL, &CALIBRATE.EXT_FM, SYSMENU_HANDL_CALIB_EXT_FM},
		{"EXT 2m", SYSMENU_B4, NULL, &CALIBRATE.EXT_2m, SYSMENU_HANDL_CALIB_EXT_2m},
		{"EXT 70cm", SYSMENU_B4, NULL, &CALIBRATE.EXT_70cm, SYSMENU_HANDL_CALIB_EXT_70cm},
		{"EXT Transv 70cm", SYSMENU_B4, NULL, &CALIBRATE.EXT_TRANSV_70cm, SYSMENU_HANDL_CALIB_EXT_TRANSV_70cm},
		{"EXT Transv 23cm", SYSMENU_B4, NULL, &CALIBRATE.EXT_TRANSV_23cm, SYSMENU_HANDL_CALIB_EXT_TRANSV_23cm},
		{"EXT Transv 13cm", SYSMENU_B4, NULL, &CALIBRATE.EXT_TRANSV_13cm, SYSMENU_HANDL_CALIB_EXT_TRANSV_13cm},
		{"EXT Transv 6cm", SYSMENU_B4, NULL, &CALIBRATE.EXT_TRANSV_6cm, SYSMENU_HANDL_CALIB_EXT_TRANSV_6cm},
		{"EXT Transv 3cm", SYSMENU_B4, NULL, &CALIBRATE.EXT_TRANSV_3cm, SYSMENU_HANDL_CALIB_EXT_TRANSV_3cm},
        {"Transverter Offset, mHz", SYSMENU_UINT16, NULL, &CALIBRATE.Transverter_Custom_Offset_Mhz, SYSMENU_HANDL_CALIB_TRANSV_OFFSET_Custom},
        {"Transverter 70cm RF, mHz", SYSMENU_UINT16, NULL, &CALIBRATE.Transverter_70cm_RF_Mhz, SYSMENU_HANDL_CALIB_TRANSV_RF_70cm},
        {"Transverter 70cm IF, mHz", SYSMENU_UINT16, NULL, &CALIBRATE.Transverter_70cm_IF_Mhz, SYSMENU_HANDL_CALIB_TRANSV_IF_70cm},
        {"Transverter 23cm RF, mHz", SYSMENU_UINT16, NULL, &CALIBRATE.Transverter_23cm_RF_Mhz, SYSMENU_HANDL_CALIB_TRANSV_RF_23cm},
        {"Transverter 23cm IF, mHz", SYSMENU_UINT16, NULL, &CALIBRATE.Transverter_23cm_IF_Mhz, SYSMENU_HANDL_CALIB_TRANSV_IF_23cm},
        {"Transverter 13cm RF, mHz", SYSMENU_UINT16, NULL, &CALIBRATE.Transverter_13cm_RF_Mhz, SYSMENU_HANDL_CALIB_TRANSV_RF_13cm},
        {"Transverter 13cm IF, mHz", SYSMENU_UINT16, NULL, &CALIBRATE.Transverter_13cm_IF_Mhz, SYSMENU_HANDL_CALIB_TRANSV_IF_13cm},
        {"Transverter 6cm RF, mHz", SYSMENU_UINT16, NULL, &CALIBRATE.Transverter_6cm_RF_Mhz, SYSMENU_HANDL_CALIB_TRANSV_RF_6cm},
        {"Transverter 6cm IF, mHz", SYSMENU_UINT16, NULL, &CALIBRATE.Transverter_6cm_IF_Mhz, SYSMENU_HANDL_CALIB_TRANSV_IF_6cm},
        {"Transverter 3cm RF, mHz", SYSMENU_UINT16, NULL, &CALIBRATE.Transverter_3cm_RF_Mhz, SYSMENU_HANDL_CALIB_TRANSV_RF_3cm},
        {"Transverter 3cm IF, mHz", SYSMENU_UINT16, NULL, &CALIBRATE.Transverter_3cm_IF_Mhz, SYSMENU_HANDL_CALIB_TRANSV_IF_3cm},
#endif
		{"NOTX NOT HAM", SYSMENU_BOOLEAN, NULL, &CALIBRATE.NOTX_NOTHAM, SYSMENU_HANDL_CALIB_NOTX_NOTHAM},
		{"NOTX 2200m", SYSMENU_BOOLEAN, NULL, &CALIBRATE.NOTX_2200m, SYSMENU_HANDL_CALIB_NOTX_2200m},
		{"NOTX 160m", SYSMENU_BOOLEAN, NULL, &CALIBRATE.NOTX_160m, SYSMENU_HANDL_CALIB_NOTX_160m},
		{"NOTX 80m", SYSMENU_BOOLEAN, NULL, &CALIBRATE.NOTX_80m, SYSMENU_HANDL_CALIB_NOTX_80m},
		{"NOTX 60m", SYSMENU_BOOLEAN, NULL, &CALIBRATE.NOTX_60m, SYSMENU_HANDL_CALIB_NOTX_60m},
		{"NOTX 40m", SYSMENU_BOOLEAN, NULL, &CALIBRATE.NOTX_40m, SYSMENU_HANDL_CALIB_NOTX_40m},
		{"NOTX 30m", SYSMENU_BOOLEAN, NULL, &CALIBRATE.NOTX_30m, SYSMENU_HANDL_CALIB_NOTX_30m},
		{"NOTX 20m", SYSMENU_BOOLEAN, NULL, &CALIBRATE.NOTX_20m, SYSMENU_HANDL_CALIB_NOTX_20m},
		{"NOTX 17m", SYSMENU_BOOLEAN, NULL, &CALIBRATE.NOTX_17m, SYSMENU_HANDL_CALIB_NOTX_17m},
		{"NOTX 15m", SYSMENU_BOOLEAN, NULL, &CALIBRATE.NOTX_15m, SYSMENU_HANDL_CALIB_NOTX_15m},
		{"NOTX 12m", SYSMENU_BOOLEAN, NULL, &CALIBRATE.NOTX_12m, SYSMENU_HANDL_CALIB_NOTX_12m},
		{"NOTX CB", SYSMENU_BOOLEAN, NULL, &CALIBRATE.NOTX_CB, SYSMENU_HANDL_CALIB_NOTX_CB},
		{"NOTX 10m", SYSMENU_BOOLEAN, NULL, &CALIBRATE.NOTX_10m, SYSMENU_HANDL_CALIB_NOTX_10m},
#if !defined(FRONTPANEL_LITE)
		{"NOTX 6m", SYSMENU_BOOLEAN, NULL, &CALIBRATE.NOTX_6m, SYSMENU_HANDL_CALIB_NOTX_6m},
		{"NOTX 4m", SYSMENU_BOOLEAN, NULL, &CALIBRATE.NOTX_4m, SYSMENU_HANDL_CALIB_NOTX_4m},
		{"NOTX 2m", SYSMENU_BOOLEAN, NULL, &CALIBRATE.NOTX_2m, SYSMENU_HANDL_CALIB_NOTX_2m},
		{"NOTX 70cm", SYSMENU_BOOLEAN, NULL, &CALIBRATE.NOTX_70cm, SYSMENU_HANDL_CALIB_NOTX_70cm},
#endif
		{"ENABLE 60M Band", SYSMENU_BOOLEAN, NULL, &CALIBRATE.ENABLE_60m_band, SYSMENU_HANDL_CALIB_ENABLE_60m_band},
#if !defined(FRONTPANEL_LITE)
		{"ENABLE 4M Band", SYSMENU_BOOLEAN, NULL, &CALIBRATE.ENABLE_4m_band, SYSMENU_HANDL_CALIB_ENABLE_4m_band},
		{"ENABLE Air Band", SYSMENU_BOOLEAN, NULL, &CALIBRATE.ENABLE_AIR_band, SYSMENU_HANDL_CALIB_ENABLE_AIR_band},
		{"ENABLE Marine Band", SYSMENU_BOOLEAN, NULL, &CALIBRATE.ENABLE_marine_band, SYSMENU_HANDL_CALIB_ENABLE_marine_band},
#endif
#if HRDW_HAS_WIFI
		{"OTA Update", SYSMENU_BOOLEAN, NULL, &CALIBRATE.OTA_update, SYSMENU_HANDL_CALIB_OTA_update},
#endif
		{"TX Start Delay", SYSMENU_UINT16, NULL, &CALIBRATE.TX_StartDelay, SYSMENU_HANDL_CALIB_TX_StartDelay},
		{"LCD Rotate", SYSMENU_BOOLEAN, NULL, &CALIBRATE.LCD_Rotate, SYSMENU_HANDL_CALIB_LCD_Rotate},
#ifdef TOUCHPAD_GT911
        {"TOUCHPAD horiz flip", SYSMENU_BOOLEAN, NULL, &CALIBRATE.TOUCHPAD_horizontal_flip, SYSMENU_HANDL_CALIB_TOUCHPAD_horizontal_flip},
        {"Flash GT911", SYSMENU_RUN, NULL, NULL, SYSMENU_HANDL_CALIB_FlashGT911},
#endif
#if defined(FRONTPANEL_BIG_V1) || defined(FRONTPANEL_WF_100D)
		{"INA226_PWR_MON", SYSMENU_BOOLEAN, NULL, &CALIBRATE.INA226_EN, SYSMENU_HANDL_INA226_PWR_MON},				  // Tisho
		{"INA226_Cur_Calc(mA/Bit)", SYSMENU_FLOAT32, NULL, &CALIBRATE.INA226_CurCalc, SYSMENU_HANDL_INA226_CUR_CALL}, // Tisho
#endif
#if defined(FRONTPANEL_X1) || defined(FRONTPANEL_LITE)
		{"PWR VLT Calibr", SYSMENU_FLOAT32, NULL, &CALIBRATE.PWR_VLT_Calibration, SYSMENU_HANDL_CALIB_PWR_VLT_Calibration},
#endif
		#if defined(FRONTPANEL_X1)
		{"PWR CUR Calibr", SYSMENU_FLOAT32, NULL, &CALIBRATE.PWR_CUR_Calibration, SYSMENU_HANDL_CALIB_PWR_CUR_Calibration},
#endif
		{"ATU Averaging", SYSMENU_UINT8, SYSMENU_HANDL_CHECK_HAS_ATU, &CALIBRATE.ATU_AVERAGING, SYSMENU_HANDL_CALIB_ATU_AVERAGING},
		{"CAT Type", SYSMENU_ENUM, NULL, &CALIBRATE.CAT_Type, SYSMENU_HANDL_CALIB_CAT_Type, {"FT-450", "TS2000"}},
#if !defined(FRONTPANEL_LITE)
		{"LNA Compensation", SYSMENU_INT8, NULL, &CALIBRATE.LNA_compensation, SYSMENU_HANDL_CALIB_LNA_compensation},
#endif
		{"TSignal Balance", SYSMENU_UINT8, NULL, &CALIBRATE.TwoSignalTune_Balance, SYSMENU_HANDL_CALIB_TwoSignalTune_Balance},
		{"Linear Pwr Control", SYSMENU_BOOLEAN, NULL, &CALIBRATE.LinearPowerControl, SYSMENU_HANDL_CALIB_LinearPowerControl},
		{"IF Gain MIN", SYSMENU_UINT8, NULL, &CALIBRATE.IF_GAIN_MIN, SYSMENU_HANDL_CALIB_IF_GAIN_MIN},
		{"IF Gain MAX", SYSMENU_UINT8, NULL, &CALIBRATE.IF_GAIN_MAX, SYSMENU_HANDL_CALIB_IF_GAIN_MAX},
		{"Settings reset", SYSMENU_RUN, NULL, NULL, SYSMENU_HANDL_CALIB_SETTINGS_RESET},
		{"Calibrate reset", SYSMENU_RUN, NULL, NULL, SYSMENU_HANDL_CALIB_CALIBRATION_RESET},
#if HRDW_HAS_WIFI
        {"WiFi settings reset", SYSMENU_RUN, NULL, NULL, SYSMENU_HANDL_CALIB_WIFI_RESET},
#endif
};

const static struct sysmenu_item_handler sysmenu_swr_analyser_handlers[] =
	{
		{"Band SWR", SYSMENU_RUN, NULL, NULL, SYSMENU_HANDL_SWR_BAND_START},
		{"HF SWR", SYSMENU_RUN, NULL, NULL, SYSMENU_HANDL_SWR_HF_START},
		{"Custom SWR", SYSMENU_RUN, NULL, NULL, SYSMENU_HANDL_SWR_CUSTOM_Start},
		{"Custom Begin, kHz", SYSMENU_UINT32, NULL, &TRX.SWR_CUSTOM_Begin, SYSMENU_HANDL_SWR_CUSTOM_Begin},
		{"Custom End, kHz", SYSMENU_UINT32, NULL, &TRX.SWR_CUSTOM_End, SYSMENU_HANDL_SWR_CUSTOM_End},
};

const static struct sysmenu_item_handler sysmenu_spectrum_handlers[] =
	{
		{"Spectrum START", SYSMENU_RUN, NULL, NULL, SYSMENU_HANDL_SPECTRUM_Start},
		{"Begin, mHz", SYSMENU_UINT32, NULL, &TRX.SPEC_Begin, SYSMENU_HANDL_SPECTRUM_Begin},
		{"End, mHz", SYSMENU_UINT32, NULL, &TRX.SPEC_End, SYSMENU_HANDL_SPECTRUM_End},
		{"Top, dBm", SYSMENU_INT16, NULL, &TRX.SPEC_TopDBM, SYSMENU_HANDL_SPECTRUM_TopDBM},
		{"Bottom, dBm", SYSMENU_INT16, NULL, &TRX.SPEC_BottomDBM, SYSMENU_HANDL_SPECTRUM_BottomDBM},
};

const static struct sysmenu_item_handler sysmenu_wspr_handlers[] =
	{
		{"WSPR Beacon START", SYSMENU_RUN, NULL, NULL, SYSMENU_HANDL_WSPR_Start},
		{"Freq offset", SYSMENU_INT16, NULL, &TRX.WSPR_FREQ_OFFSET, SYSMENU_HANDL_WSPR_FREQ_OFFSET},
		{"BAND 160m", SYSMENU_BOOLEAN, NULL, &TRX.WSPR_BANDS_160, SYSMENU_HANDL_WSPR_BAND160},
		{"BAND 80m", SYSMENU_BOOLEAN, NULL, &TRX.WSPR_BANDS_80, SYSMENU_HANDL_WSPR_BAND80},
		{"BAND 40m", SYSMENU_BOOLEAN, NULL, &TRX.WSPR_BANDS_40, SYSMENU_HANDL_WSPR_BAND40},
		{"BAND 30m", SYSMENU_BOOLEAN, NULL, &TRX.WSPR_BANDS_30, SYSMENU_HANDL_WSPR_BAND30},
		{"BAND 20m", SYSMENU_BOOLEAN, NULL, &TRX.WSPR_BANDS_20, SYSMENU_HANDL_WSPR_BAND20},
		{"BAND 17m", SYSMENU_BOOLEAN, NULL, &TRX.WSPR_BANDS_17, SYSMENU_HANDL_WSPR_BAND17},
		{"BAND 15m", SYSMENU_BOOLEAN, NULL, &TRX.WSPR_BANDS_15, SYSMENU_HANDL_WSPR_BAND15},
		{"BAND 12m", SYSMENU_BOOLEAN, NULL, &TRX.WSPR_BANDS_12, SYSMENU_HANDL_WSPR_BAND12},
		{"BAND 10m", SYSMENU_BOOLEAN, NULL, &TRX.WSPR_BANDS_10, SYSMENU_HANDL_WSPR_BAND10},
		{"BAND 6m", SYSMENU_BOOLEAN, NULL, &TRX.WSPR_BANDS_6, SYSMENU_HANDL_WSPR_BAND6},
		{"BAND 2m", SYSMENU_BOOLEAN, NULL, &TRX.WSPR_BANDS_2, SYSMENU_HANDL_WSPR_BAND2},
		{"", SYSMENU_INFOLINE, NULL, NULL},
};

const static struct sysmenu_item_handler sysmenu_auto_calibration_handlers[] =
	{
		{"Calibrate SWR", SYSMENU_RUN, NULL, NULL, SYSMENU_HANDL_AUTO_CALIBRATION_SWR},
		{"Calibrate Power", SYSMENU_RUN, NULL, NULL, SYSMENU_HANDL_AUTO_CALIBRATION_POWER},
};

const static struct sysmenu_item_handler sysmenu_services_handlers[] = {
#if HRDW_HAS_WIFI && !defined(FRONTPANEL_X1)
		{"DX Cluster", SYSMENU_RUN, NULL, NULL, SYSMENU_HANDL_DX_CLUSTER},
		{"Propagination", SYSMENU_RUN, NULL, NULL, SYSMENU_HANDL_PROPAGINATION},
		#if LCD_WIDTH >= 800
		{"DayNight Map", SYSMENU_RUN, NULL, NULL, SYSMENU_HANDL_DAYNIGHT_MAP},
        {"Ionogram", SYSMENU_RUN, NULL, NULL, SYSMENU_HANDL_IONOGRAM},
        #endif
		{"RDA Statistics", SYSMENU_RUN, NULL, NULL, SYSMENU_HANDL_RDA_STATS},
#endif
		{"SWR Analyzer", SYSMENU_MENU, NULL, NULL, SYSMENU_HANDL_SWR_ANALYSER_MENU},
		{"Spectrum Analyzer", SYSMENU_MENU, NULL, NULL, SYSMENU_HANDL_SPECTRUMMENU},
#ifndef STM32F407xx
		{"WSPR Beacon", SYSMENU_MENU, NULL, NULL, SYSMENU_HANDL_WSPRMENU},
#endif
#if HRDW_HAS_SD
		{"Record CQ message", SYSMENU_RUN, NULL, NULL, SYSMENU_HANDL_RECORD_CQ_WAV},
#endif
#if FT8_SUPPORT
		{"FT-8", SYSMENU_RUN, NULL, NULL, SYSMENU_HANDL_FT8_Decoder}, // Tisho
#endif
#ifdef SWR_AD8307_LOG
		{"SWR Tandem Match Contr.", SYSMENU_RUN, NULL, NULL, SYSMENU_HANDL_SWR_Tandem_Ctrl}, // Tisho
#endif
#ifdef LAY_800x480
		{"Locator info", SYSMENU_RUN, NULL, NULL, SYSMENU_HANDL_LOCATOR_INFO},
		{"Callsign info", SYSMENU_RUN, NULL, NULL, SYSMENU_HANDL_CALLSIGN_INFO},
#endif
		{"Self Test", SYSMENU_RUN, NULL, NULL, SYSMENU_HANDL_SELF_TEST},
		{"Auto Calibration", SYSMENU_MENU, NULL, NULL, SYSMENU_HANDL_AUTO_CALIBRATION},
};

static struct sysmenu_menu_wrapper sysmenu_wrappers[] = {
    {.menu_handler = sysmenu_handlers, .currentIndex = 0},
    {.menu_handler = sysmenu_trx_handlers, .currentIndex = 0},
    {.menu_handler = sysmenu_audio_handlers, .currentIndex = 0},
    {.menu_handler = sysmenu_cw_handlers, .currentIndex = 0},
    {.menu_handler = sysmenu_screen_handlers, .currentIndex = 0},
    {.menu_handler = sysmenu_decoders_handlers, .currentIndex = 0},
    {.menu_handler = sysmenu_adc_handlers, .currentIndex = 0},
#if HRDW_HAS_WIFI
    {.menu_handler = sysmenu_wifi_handlers, .currentIndex = 0},
#endif
#if HRDW_HAS_SD
    {.menu_handler = sysmenu_sd_handlers, .currentIndex = 0},
    {.menu_handler = sysmenu_sd_export_handlers, .currentIndex = 0},
    {.menu_handler = sysmenu_sd_import_handlers, .currentIndex = 0},
    {.menu_handler = sysmenu_sd_format_handlers, .currentIndex = 0},
#endif
    {.menu_handler = sysmenu_calibration_handlers, .currentIndex = 0},
    {.menu_handler = sysmenu_swr_analyser_handlers, .currentIndex = 0},
    {.menu_handler = sysmenu_spectrum_handlers, .currentIndex = 0},
    {.menu_handler = sysmenu_wspr_handlers, .currentIndex = 0},
    {.menu_handler = sysmenu_services_handlers, .currentIndex = 0},
    {.menu_handler = sysmenu_auto_calibration_handlers, .currentIndex = 0},
};

// COMMON MENU
static void drawSystemMenuElement(const struct sysmenu_item_handler *menuElement, bool onlyVal);
#if HRDW_HAS_WIFI
static void SYSMENU_WIFI_DrawSelectAP1Menu(bool full_redraw);
static void SYSMENU_WIFI_SelectAP1MenuMove(int8_t dir);
static void SYSMENU_WIFI_DrawAP1passwordMenu(bool full_redraw);
static void SYSMENU_WIFI_RotatePasswordChar1(int8_t dir);
static void SYSMENU_WIFI_DrawSelectAP2Menu(bool full_redraw);
static void SYSMENU_WIFI_SelectAP2MenuMove(int8_t dir);
static void SYSMENU_WIFI_DrawAP2passwordMenu(bool full_redraw);
static void SYSMENU_WIFI_RotatePasswordChar2(int8_t dir);
static void SYSMENU_WIFI_DrawSelectAP3Menu(bool full_redraw);
static void SYSMENU_WIFI_SelectAP3MenuMove(int8_t dir);
static void SYSMENU_WIFI_DrawAP3passwordMenu(bool full_redraw);
static void SYSMENU_WIFI_RotatePasswordChar3(int8_t dir);
#endif
static void SYSMENU_TRX_DrawCallsignMenu(bool full_redraw);
static void SYSMENU_TRX_RotateCallsignChar(int8_t dir);
static void SYSMENU_TRX_DrawLocatorMenu(bool full_redraw);
static void SYSMENU_TRX_RotateLocatorChar(int8_t dir);
static void SYSMENU_TRX_DrawURSICodeMenu(bool full_redraw);
static void SYSMENU_TRX_RotateURSICodeChar(int8_t dir);
static uint8_t SYSTMENU_getVisibleIdFromReal(uint8_t realIndex);
static uint8_t SYSTMENU_getPageFromRealIndex(uint8_t realIndex);
static void setCurrentMenuIndex(uint8_t index);
static uint8_t getCurrentMenuIndex(void);
static uint16_t getIndexByName(const struct sysmenu_item_handler *menu, uint16_t menu_length, char *name);

static const struct sysmenu_item_handler *sysmenu_handlers_selected = (const struct sysmenu_item_handler *)&sysmenu_handlers[0];
static uint8_t sysmenu_item_count = sizeof(sysmenu_handlers) / sizeof(sysmenu_handlers[0]);
static uint16_t sysmenu_y = 5;
static uint8_t sysmenu_i = 0;
static bool sysmenu_onroot = true;
bool SYSMENU_hiddenmenu_enabled = false;
static bool sysmenu_services_opened = false;
static bool sysmenu_infowindow_opened = false;
static bool sysmenu_sysinfo_opened = false;
static bool sysmenu_filemanager_opened = false;
static bool sysmenu_item_selected_by_enc2 = false;
bool sysmenu_ota_opened = false;
uint8_t sysmenu_ota_opened_state = 0;
bool SYSMENU_FT8_DECODER_opened = false;

// WIFI
static bool sysmenu_wifi_needupdate_ap = true;
bool sysmenu_wifi_selectap1_menu_opened = false;
bool sysmenu_wifi_selectap2_menu_opened = false;
bool sysmenu_wifi_selectap3_menu_opened = false;
static bool sysmenu_wifi_setAP1password_menu_opened = false;
static bool sysmenu_wifi_setAP2password_menu_opened = false;
static bool sysmenu_wifi_setAP3password_menu_opened = false;
static bool sysmenu_trx_setCallsign_menu_opened = false;
static bool sysmenu_trx_setLocator_menu_opened = false;
static bool sysmenu_trx_setURSICode_menu_opened = false;
static uint8_t sysmenu_wifi_selected_ap_index = 0;
static uint8_t sysmenu_wifi_selected_ap_password_char_index = 0;
static uint8_t sysmenu_trx_selected_callsign_char_index = 0;
static uint8_t sysmenu_trx_selected_locator_char_index = 0;
static uint8_t sysmenu_trx_selected_ursi_code_char_index = 0;

// Time menu
static bool sysmenu_timeMenuOpened = false;
static uint8_t TimeMenuSelection = 0;

// TRX MENU

static void SYSMENU_HANDL_TRXMENU(int8_t direction)
{
    (void) direction;

	sysmenu_handlers_selected = (const struct sysmenu_item_handler *)&sysmenu_trx_handlers[0];
	sysmenu_item_count = sizeof(sysmenu_trx_handlers) / sizeof(sysmenu_trx_handlers[0]);
	sysmenu_onroot = false;
	LCD_UpdateQuery.SystemMenuRedraw = true;
}

void SYSMENU_TRX_RFPOWER_HOTKEY(void) {
	SYSMENU_HANDL_TRXMENU(0);
	uint16_t index = getIndexByName(sysmenu_handlers_selected, sysmenu_item_count, "RF Power");
	setCurrentMenuIndex(index);
	LCD_redraw(false);
}

void SYSMENU_TRX_STEP_HOTKEY(void) {
	SYSMENU_HANDL_TRXMENU(0);
	uint16_t index = getIndexByName(sysmenu_handlers_selected, sysmenu_item_count, "Freq Step");
	if (TRX.Fast) {
		index = getIndexByName(sysmenu_handlers_selected, sysmenu_item_count, "Freq Step FAST");
	}

	setCurrentMenuIndex(index);
	LCD_redraw(false);
}

static void SYSMENU_HANDL_TRX_BandMap(int8_t direction) {
	if (direction > 0) {
		TRX.BandMapEnabled = true;
	}
	if (direction < 0) {
		TRX.BandMapEnabled = false;
	}
}

static void SYSMENU_HANDL_TRX_RF_Gain_For_Each_Band(int8_t direction) {
	if (direction > 0) {
		TRX.RF_Gain_For_Each_Band = true;
	}
	if (direction < 0) {
		TRX.RF_Gain_For_Each_Band = false;
	}
}

static void SYSMENU_HANDL_TRX_RF_Gain_For_Each_Mode(int8_t direction) {
	if (direction > 0) {
		TRX.RF_Gain_For_Each_Mode = true;
	}
	if (direction < 0) {
		TRX.RF_Gain_For_Each_Mode = false;
	}
}

static void SYSMENU_HANDL_TRX_ChannelMode(int8_t direction) {
	if (direction > 0) {
		TRX.ChannelMode = true;
	}
	if (direction < 0) {
		TRX.ChannelMode = false;
	}
}

static void SYSMENU_HANDL_TRX_AutoGain(int8_t direction) {
	if (direction > 0) {
		TRX.AutoGain = true;
	}
	if (direction < 0) {
		TRX.AutoGain = false;
	}
	FPGA_NeedSendParams = true;
}

static void SYSMENU_HANDL_TRX_RFFilters(int8_t direction) {
	if (direction > 0) {
		TRX.RF_Filters = true;
	}
	if (direction < 0) {
		TRX.RF_Filters = false;
	}
}

static void SYSMENU_HANDL_TRX_TWO_SIGNAL_TUNE(int8_t direction) {
	if (direction > 0) {
		TRX.TWO_SIGNAL_TUNE = true;
	}
	if (direction < 0) {
		TRX.TWO_SIGNAL_TUNE = false;
	}
}

static void SYSMENU_HANDL_TRX_FineRITTune(int8_t direction) {
	if (direction > 0) {
		TRX.FineRITTune = true;
	}
	if (direction < 0) {
		TRX.FineRITTune = false;
	}
}

static void SYSMENU_HANDL_TRX_RFPower(int8_t direction) {
	if (direction > 0 || TRX.RF_Gain > 0) {
		TRX.RF_Gain += direction;
	}
	if (TRX.RF_Gain > 100) {
		TRX.RF_Gain = 100;
	}

	int8_t band = getBandFromFreq(CurrentVFO->RealRXFreq, true);
	if (band >= 0) {
		TRX.BANDS_SAVED_SETTINGS[band].RF_Gain = TRX.RF_Gain;
	}

	APROC_TX_clip_gain = 1.0f;
	ATU_TunePowerStabilized = false;
}

static void SYSMENU_HANDL_TRX_Auto_Input_Switch(int8_t direction) {
	if (direction > 0) {
		TRX.Auto_Input_Switch = true;
	}
	if (direction < 0) {
		TRX.Auto_Input_Switch = false;
	}
}

static void SYSMENU_HANDL_TRX_Auto_Snap(int8_t direction) {
	if (direction > 0) {
		TRX.Auto_Snap = true;
	}
	if (direction < 0) {
		TRX.Auto_Snap = false;
	}
}

static void SYSMENU_HANDL_TRX_INPUT_TYPE_MAIN(int8_t direction) {
	if (direction > 0 || TRX.InputType_MAIN > 0) {
		TRX.InputType_MAIN += direction;
	}
	if (TRX.InputType_MAIN > 2) {
		TRX.InputType_MAIN = 2;
	}
	CODEC_TXRX_mode();
}

static void SYSMENU_HANDL_TRX_INPUT_TYPE_DIGI(int8_t direction) {
	if (direction > 0 || TRX.InputType_DIGI > 0) {
		TRX.InputType_DIGI += direction;
	}
	if (TRX.InputType_DIGI > 2) {
		TRX.InputType_DIGI = 2;
	}
	CODEC_TXRX_mode();
}

static void SYSMENU_HANDL_TRX_DEBUG_TYPE(int8_t direction) {
	if (direction > 0 || TRX.Debug_Type > 0) {
		TRX.Debug_Type += direction;
	}
	if (TRX.Debug_Type > 5) {
		TRX.Debug_Type = 5;
	}
}

static void SYSMENU_HANDL_TRX_SAMPLERATE_MAIN(int8_t direction) {
	if (direction > 0 || TRX.SAMPLERATE_MAIN > 0) {
		TRX.SAMPLERATE_MAIN += direction;
	}
	if (TRX.SAMPLERATE_MAIN > 3) {
		TRX.SAMPLERATE_MAIN = 3;
	}

#ifdef STM32F407xx
	if (TRX.SAMPLERATE_MAIN > 1) {
		TRX.SAMPLERATE_MAIN = 1;
	}
#endif

	int8_t band = getBandFromFreq(CurrentVFO->Freq, true);
	TRX.BANDS_SAVED_SETTINGS[band].SAMPLERATE = TRX.SAMPLERATE_MAIN;

	FFT_Init();
	NeedReinitAudioFilters = true;
}

static void SYSMENU_HANDL_TRX_SAMPLERATE_FM(int8_t direction) {
	if (direction > 0 || TRX.SAMPLERATE_FM > 0) {
		TRX.SAMPLERATE_FM += direction;
	}
	if (TRX.SAMPLERATE_FM > 3) {
		TRX.SAMPLERATE_FM = 3;
	}

#ifdef STM32F407xx
	if (TRX.SAMPLERATE_FM > 1) {
		TRX.SAMPLERATE_FM = 1;
	}
#endif

	FFT_Init();
	NeedReinitAudioFilters = true;
}

static void SYSMENU_HANDL_TRX_RIT_INTERVAL(int8_t direction) {
	TRX.RIT_INTERVAL += direction * 100;
	if (TRX.RIT_INTERVAL < 100) {
		TRX.RIT_INTERVAL = 100;
	}
	if (TRX.RIT_INTERVAL > 10000) {
		TRX.RIT_INTERVAL = 10000;
	}
}

static void SYSMENU_HANDL_TRX_XIT_INTERVAL(int8_t direction) {
	TRX.XIT_INTERVAL += direction * 100;
	if (TRX.XIT_INTERVAL < 100) {
		TRX.XIT_INTERVAL = 100;
	}
	if (TRX.XIT_INTERVAL > 10000) {
		TRX.XIT_INTERVAL = 10000;
	}
}

static const uint32_t freq_steps[] = {1, 10, 25, 50, 100, 500, 1000, 2500, 5000, 25000, 50000, 100000, 250000, 500000};
static void SYSMENU_HANDL_TRX_FRQ_STEP(int8_t direction) {
	for (uint8_t i = 0; i < ARRLENTH(freq_steps); i++) {
		if (TRX.FRQ_STEP == freq_steps[i]) {
			if (direction < 0) {
				if (i > 0) {
					TRX.FRQ_STEP = freq_steps[i - 1];
				} else {
					TRX.FRQ_STEP = freq_steps[0];
				}
				return;
			} else {
				if (i < (ARRLENTH(freq_steps) - 1)) {
					TRX.FRQ_STEP = freq_steps[i + 1];
				} else {
					TRX.FRQ_STEP = freq_steps[ARRLENTH(freq_steps) - 1];
				}
				return;
			}
		}
	}
	TRX.FRQ_STEP = freq_steps[0];
}

static void SYSMENU_HANDL_TRX_FRQ_FAST_STEP(int8_t direction) {
	for (uint8_t i = 0; i < ARRLENTH(freq_steps); i++) {
		if (TRX.FRQ_FAST_STEP == freq_steps[i]) {
			if (direction < 0) {
				if (i > 0) {
					TRX.FRQ_FAST_STEP = freq_steps[i - 1];
				} else {
					TRX.FRQ_FAST_STEP = freq_steps[0];
				}
				return;
			} else {
				if (i < (ARRLENTH(freq_steps) - 1)) {
					TRX.FRQ_FAST_STEP = freq_steps[i + 1];
				} else {
					TRX.FRQ_FAST_STEP = freq_steps[ARRLENTH(freq_steps) - 1];
				}
				return;
			}
		}
	}
	TRX.FRQ_FAST_STEP = freq_steps[0];
}

static void SYSMENU_HANDL_TRX_FRQ_ENC_STEP(int8_t direction) {
	for (uint8_t i = 0; i < ARRLENTH(freq_steps); i++) {
		if (TRX.FRQ_ENC_STEP == freq_steps[i]) {
			if (direction < 0) {
				if (i > 0) {
					TRX.FRQ_ENC_STEP = freq_steps[i - 1];
				} else {
					TRX.FRQ_ENC_STEP = freq_steps[0];
				}
				return;
			} else {
				if (i < (ARRLENTH(freq_steps) - 1)) {
					TRX.FRQ_ENC_STEP = freq_steps[i + 1];
				} else {
					TRX.FRQ_ENC_STEP = freq_steps[ARRLENTH(freq_steps) - 1];
				}
				return;
			}
		}
	}
	TRX.FRQ_ENC_STEP = freq_steps[0];
}

static void SYSMENU_HANDL_TRX_FRQ_ENC_FAST_STEP(int8_t direction) {
	for (uint8_t i = 0; i < ARRLENTH(freq_steps); i++) {
		if (TRX.FRQ_ENC_FAST_STEP == freq_steps[i]) {
			if (direction < 0) {
				if (i > 0) {
					TRX.FRQ_ENC_FAST_STEP = freq_steps[i - 1];
				} else {
					TRX.FRQ_ENC_FAST_STEP = freq_steps[0];
				}
				return;
			} else {
				if (i < (ARRLENTH(freq_steps) - 1)) {
					TRX.FRQ_ENC_FAST_STEP = freq_steps[i + 1];
				} else {
					TRX.FRQ_ENC_FAST_STEP = freq_steps[ARRLENTH(freq_steps) - 1];
				}
				return;
			}
		}
	}
	TRX.FRQ_ENC_FAST_STEP = freq_steps[0];
}

static void SYSMENU_HANDL_TRX_FRQ_ENC_WFM_STEP_KHZ(int8_t direction) {
	const uint32_t wfm_freq_steps[] = {1, 2, 5, 10, 20, 25, 50, 100, 200, 500, 1000};

	for (uint8_t i = 0; i < ARRLENTH(wfm_freq_steps); i++) {
		if (TRX.FRQ_ENC_WFM_STEP_KHZ == wfm_freq_steps[i]) {
			if (direction < 0) {
				if (i > 0) {
					TRX.FRQ_ENC_WFM_STEP_KHZ = wfm_freq_steps[i - 1];
				} else {
					TRX.FRQ_ENC_WFM_STEP_KHZ = wfm_freq_steps[0];
				}
				return;
			} else {
				if (i < (ARRLENTH(wfm_freq_steps) - 1)) {
					TRX.FRQ_ENC_WFM_STEP_KHZ = wfm_freq_steps[i + 1];
				} else {
					TRX.FRQ_ENC_WFM_STEP_KHZ = wfm_freq_steps[ARRLENTH(wfm_freq_steps) - 1];
				}
				return;
			}
		}
	}
	TRX.FRQ_ENC_WFM_STEP_KHZ = wfm_freq_steps[0];
}

static void SYSMENU_HANDL_TRX_FRQ_CW_STEP_DIVIDER(int8_t direction) {
	TRX.FRQ_CW_STEP_DIVIDER += direction;
	if (TRX.FRQ_CW_STEP_DIVIDER < 1) {
		TRX.FRQ_CW_STEP_DIVIDER = 1;
	}
	if (TRX.FRQ_CW_STEP_DIVIDER > 100) {
		TRX.FRQ_CW_STEP_DIVIDER = 100;
	}
}

static void SYSMENU_HANDL_TRX_ENC_ACCELERATE(int8_t direction) {
	if (direction > 0) {
		TRX.Encoder_Accelerate = true;
	}
	if (direction < 0) {
		TRX.Encoder_Accelerate = false;
	}
}

static void SYSMENU_HANDL_TRX_ATT_STEP(int8_t direction) {
	TRX.ATT_STEP += direction;
	if (TRX.ATT_STEP < 1) {
		TRX.ATT_STEP = 1;
	}
	if (TRX.ATT_STEP > 15) {
		TRX.ATT_STEP = 15;
	}
}

static void SYSMENU_HANDL_TRX_ATT_DB(int8_t direction) {
	TRX.ATT_DB += (float32_t)direction * 0.5f;
	if (TRX.ATT_DB < 0.5f) {
		TRX.ATT_DB = 0.5f;
	}
	if (TRX.ATT_DB > 31.5f) {
		TRX.ATT_DB = 31.5f;
	}
}

#if HRDW_HAS_VGA
static void SYSMENU_HANDL_TRX_VGA_GAIN(int8_t direction) {
	TRX.VGA_GAIN += (float32_t)direction * 1.5f;
	if (TRX.VGA_GAIN < 10.5f) {
		TRX.VGA_GAIN = 10.5f;
	}
	if (TRX.VGA_GAIN > 33.0f) {
		TRX.VGA_GAIN = 33.0f;
	}
}
#endif

static void SYSMENU_TRX_Callsign_keyboardHandler(uint32_t parameter) {
	if (parameter == '<') // backspace
	{
		TRX.CALLSIGN[sysmenu_trx_selected_callsign_char_index] = 0;

		if (sysmenu_trx_selected_callsign_char_index > 0) {
			sysmenu_trx_selected_callsign_char_index--;
		}
	} else {
		TRX.CALLSIGN[sysmenu_trx_selected_callsign_char_index] = parameter;

		if (sysmenu_trx_selected_callsign_char_index < (MAX_CALLSIGN_LENGTH - 1)) {
			sysmenu_trx_selected_callsign_char_index++;
		}
	}

	LCD_UpdateQuery.SystemMenuRedraw = true;
}

static void SYSMENU_TRX_DrawCallsignMenu(bool full_redraw) {
	if (full_redraw) {
		LCDDriver_Fill(BG_COLOR);
		LCDDriver_printText("CALLSIGN:", 5, 5, FG_COLOR, BG_COLOR, LAYOUT->SYSMENU_FONT_SIZE);
	}

	LCDDriver_printText(TRX.CALLSIGN, 10, 37, COLOR_GREEN, BG_COLOR, LAYOUT->SYSMENU_FONT_SIZE);
	LCDDriver_drawFastHLine(8 + sysmenu_trx_selected_callsign_char_index * RASTR_FONT_W * LAYOUT->SYSMENU_FONT_SIZE, interactive_menu_top, RASTR_FONT_W * LAYOUT->SYSMENU_FONT_SIZE, COLOR_RED);

#if (defined(HAS_TOUCHPAD) && defined(LAY_800x480))
	LCD_printKeyboard(SYSMENU_TRX_Callsign_keyboardHandler, false);
#endif
}

static void SYSMENU_TRX_Locator_keyboardHandler(uint32_t parameter) {
	if (parameter == '<') // backspace
	{
		TRX.LOCATOR[sysmenu_trx_selected_locator_char_index] = 0;

		if (sysmenu_trx_selected_locator_char_index > 0) {
			sysmenu_trx_selected_locator_char_index--;
		}
	} else {
		TRX.LOCATOR[sysmenu_trx_selected_locator_char_index] = parameter;

		if (sysmenu_trx_selected_locator_char_index < (MAX_CALLSIGN_LENGTH - 1)) {
			sysmenu_trx_selected_locator_char_index++;
		}
	}

	LCD_UpdateQuery.SystemMenuRedraw = true;
}

static void SYSMENU_TRX_DrawLocatorMenu(bool full_redraw) {
	if (full_redraw) {
		LCDDriver_Fill(BG_COLOR);
		LCDDriver_printText("LOCATOR:", 5, 5, FG_COLOR, BG_COLOR, LAYOUT->SYSMENU_FONT_SIZE);
	}

	LCDDriver_printText(TRX.LOCATOR, 10, 37, COLOR_GREEN, BG_COLOR, LAYOUT->SYSMENU_FONT_SIZE);
	LCDDriver_drawFastHLine(8 + sysmenu_trx_selected_locator_char_index * RASTR_FONT_W * LAYOUT->SYSMENU_FONT_SIZE, interactive_menu_top, RASTR_FONT_W * LAYOUT->SYSMENU_FONT_SIZE, COLOR_RED);

#if (defined(HAS_TOUCHPAD) && defined(LAY_800x480))
	LCD_printKeyboard(SYSMENU_TRX_Locator_keyboardHandler, false);
#endif
}

static void SYSMENU_TRX_URSICode_keyboardHandler(uint32_t parameter) {
	if (parameter == '<') // backspace
	{
		TRX.URSI_CODE[sysmenu_trx_selected_ursi_code_char_index] = 0;

		if (sysmenu_trx_selected_ursi_code_char_index > 0) {
			sysmenu_trx_selected_ursi_code_char_index--;
		}
	} else {
		TRX.URSI_CODE[sysmenu_trx_selected_ursi_code_char_index] = parameter;

		if (sysmenu_trx_selected_ursi_code_char_index < (MAX_CALLSIGN_LENGTH - 1)) {
			sysmenu_trx_selected_ursi_code_char_index++;
		}
	}

	LCD_UpdateQuery.SystemMenuRedraw = true;
}

static void SYSMENU_TRX_DrawURSICodeMenu(bool full_redraw) {
	if (full_redraw) {
		LCDDriver_Fill(BG_COLOR);
		LCDDriver_printText("URSI Code:", 5, 5, FG_COLOR, BG_COLOR, LAYOUT->SYSMENU_FONT_SIZE);
	}

	LCDDriver_printText(TRX.URSI_CODE, 10, 37, COLOR_GREEN, BG_COLOR, LAYOUT->SYSMENU_FONT_SIZE);
	LCDDriver_drawFastHLine(8 + sysmenu_trx_selected_ursi_code_char_index * RASTR_FONT_W * LAYOUT->SYSMENU_FONT_SIZE, interactive_menu_top, RASTR_FONT_W * LAYOUT->SYSMENU_FONT_SIZE,
	                        COLOR_RED);

#if (defined(HAS_TOUCHPAD) && defined(LAY_800x480))
	LCD_printKeyboard(SYSMENU_TRX_URSICode_keyboardHandler, false);
#endif
}

static void SYSMENU_TRX_RotateCallsignChar(int8_t dir) {
	bool full_redraw = false;
	if (TRX.CALLSIGN[sysmenu_trx_selected_callsign_char_index] == 0) {
		full_redraw = true;
	}
	TRX.CALLSIGN[sysmenu_trx_selected_callsign_char_index] += dir;

	// do not show special characters
	if (TRX.CALLSIGN[sysmenu_trx_selected_callsign_char_index] >= 1 && TRX.CALLSIGN[sysmenu_trx_selected_callsign_char_index] <= 32 && dir > 0) {
		TRX.CALLSIGN[sysmenu_trx_selected_callsign_char_index] = 33;
	}
	if (TRX.CALLSIGN[sysmenu_trx_selected_callsign_char_index] >= 1 && TRX.CALLSIGN[sysmenu_trx_selected_callsign_char_index] <= 32 && dir < 0) {
		TRX.CALLSIGN[sysmenu_trx_selected_callsign_char_index] = 0;
	}
	if (TRX.CALLSIGN[sysmenu_trx_selected_callsign_char_index] >= 127) {
		TRX.CALLSIGN[sysmenu_trx_selected_callsign_char_index] = 0;
	}
	if (TRX.CALLSIGN[sysmenu_trx_selected_callsign_char_index] == 0) {
		full_redraw = true;
	}

	if (full_redraw) {
		LCD_UpdateQuery.SystemMenuRedraw = true;
	} else {
		LCD_UpdateQuery.SystemMenu = true;
	}
}

static void SYSMENU_TRX_RotateLocatorChar(int8_t dir) {
	bool full_redraw = false;
	if (TRX.LOCATOR[sysmenu_trx_selected_locator_char_index] == 0) {
		full_redraw = true;
	}
	TRX.LOCATOR[sysmenu_trx_selected_locator_char_index] += dir;

	// do not show special characters
	if (TRX.LOCATOR[sysmenu_trx_selected_locator_char_index] >= 1 && TRX.LOCATOR[sysmenu_trx_selected_locator_char_index] <= 32 && dir > 0) {
		TRX.LOCATOR[sysmenu_trx_selected_locator_char_index] = 33;
	}
	if (TRX.LOCATOR[sysmenu_trx_selected_locator_char_index] >= 1 && TRX.LOCATOR[sysmenu_trx_selected_locator_char_index] <= 32 && dir < 0) {
		TRX.LOCATOR[sysmenu_trx_selected_locator_char_index] = 0;
	}
	if (TRX.LOCATOR[sysmenu_trx_selected_locator_char_index] >= 127) {
		TRX.LOCATOR[sysmenu_trx_selected_locator_char_index] = 0;
	}
	if (TRX.LOCATOR[sysmenu_trx_selected_locator_char_index] == 0) {
		full_redraw = true;
	}

	if (full_redraw) {
		LCD_UpdateQuery.SystemMenuRedraw = true;
	} else {
		LCD_UpdateQuery.SystemMenu = true;
	}
}

static void SYSMENU_TRX_RotateURSICodeChar(int8_t dir) {
	bool full_redraw = false;
	if (TRX.URSI_CODE[sysmenu_trx_selected_ursi_code_char_index] == 0) {
		full_redraw = true;
	}
	TRX.URSI_CODE[sysmenu_trx_selected_ursi_code_char_index] += dir;

	// do not show special characters
	if (TRX.URSI_CODE[sysmenu_trx_selected_ursi_code_char_index] >= 1 && TRX.URSI_CODE[sysmenu_trx_selected_ursi_code_char_index] <= 32 && dir > 0) {
		TRX.URSI_CODE[sysmenu_trx_selected_ursi_code_char_index] = 33;
	}
	if (TRX.URSI_CODE[sysmenu_trx_selected_ursi_code_char_index] >= 1 && TRX.URSI_CODE[sysmenu_trx_selected_ursi_code_char_index] <= 32 && dir < 0) {
		TRX.URSI_CODE[sysmenu_trx_selected_ursi_code_char_index] = 0;
	}
	if (TRX.URSI_CODE[sysmenu_trx_selected_ursi_code_char_index] >= 127) {
		TRX.URSI_CODE[sysmenu_trx_selected_ursi_code_char_index] = 0;
	}
	if (TRX.URSI_CODE[sysmenu_trx_selected_ursi_code_char_index] == 0) {
		full_redraw = true;
	}

	if (full_redraw) {
		LCD_UpdateQuery.SystemMenuRedraw = true;
	} else {
		LCD_UpdateQuery.SystemMenu = true;
	}
}

static void SYSMENU_HANDL_TRX_SetCallsign(int8_t direction)
{
    (void) direction;

    sysmenu_trx_setCallsign_menu_opened = true;
	SYSMENU_TRX_DrawCallsignMenu(true);
	LCD_UpdateQuery.SystemMenuRedraw = true;
}

static void SYSMENU_HANDL_TRX_SetLocator(int8_t direction)
{
    (void) direction;

    sysmenu_trx_setLocator_menu_opened = true;
	SYSMENU_TRX_DrawLocatorMenu(true);
	LCD_UpdateQuery.SystemMenuRedraw = true;
}

static void SYSMENU_HANDL_TRX_SetURSICode(int8_t direction)
{
    (void) direction;

	sysmenu_trx_setURSICode_menu_opened = true;
	SYSMENU_TRX_DrawURSICodeMenu(true);
	LCD_UpdateQuery.SystemMenuRedraw = true;
}

static void SYSMENU_HANDL_TRX_TRANSV_ENABLE(int8_t direction) {
	if (direction > 0) {
		TRX.Custom_Transverter_Enabled = true;
	}
	if (direction < 0) {
		TRX.Custom_Transverter_Enabled = false;
	}
}

static void SYSMENU_HANDL_TRX_TRANSV_70CM(int8_t direction) {
	if (direction > 0) {
		TRX.Transverter_70cm = true;
	}
	if (direction < 0) {
		TRX.Transverter_70cm = false;
	}
}

static void SYSMENU_HANDL_TRX_TRANSV_23CM(int8_t direction) {
	if (direction > 0) {
		TRX.Transverter_23cm = true;
	}
	if (direction < 0) {
		TRX.Transverter_23cm = false;
	}

	BANDS[BANDID_23cm].selectable = TRX.Transverter_23cm;
}

static void SYSMENU_HANDL_TRX_TRANSV_13CM(int8_t direction) {
	if (direction > 0) {
		TRX.Transverter_13cm = true;
	}
	if (direction < 0) {
		TRX.Transverter_13cm = false;
	}

	BANDS[BANDID_13cm].selectable = TRX.Transverter_13cm;
}

static void SYSMENU_HANDL_TRX_TRANSV_6CM(int8_t direction) {
	if (direction > 0) {
		TRX.Transverter_6cm = true;
	}
	if (direction < 0) {
		TRX.Transverter_6cm = false;
	}

	BANDS[BANDID_6cm].selectable = TRX.Transverter_6cm;
}

static void SYSMENU_HANDL_TRX_TRANSV_3CM(int8_t direction) {
	if (direction > 0) {
		TRX.Transverter_3cm = true;
	}
	if (direction < 0) {
		TRX.Transverter_3cm = false;
	}

	BANDS[BANDID_3cm].selectable = TRX.Transverter_3cm;
}

static void SYSMENU_HANDL_TRX_ATU_I(int8_t direction) {
	if (TRX.ATU_I > 0 || direction > 0) {
		TRX.ATU_I += direction;
	}
	if (TRX.ATU_I > ATU_MAXPOS) {
		TRX.ATU_I = ATU_MAXPOS;
	}

	int8_t band = getBandFromFreq(CurrentVFO->Freq, true);
	if (band >= 0) {
		TRX.BANDS_SAVED_SETTINGS[band].BEST_ATU_I = TRX.ATU_I;
		TRX.BANDS_SAVED_SETTINGS[band].BEST_ATU_C = TRX.ATU_C;
		TRX.BANDS_SAVED_SETTINGS[band].BEST_ATU_T = TRX.ATU_T;
	}
}

static void SYSMENU_HANDL_TRX_ATU_C(int8_t direction) {
	if (TRX.ATU_C > 0 || direction > 0) {
		TRX.ATU_C += direction;
	}
	if (TRX.ATU_C > ATU_MAXPOS) {
		TRX.ATU_C = ATU_MAXPOS;
	}

	int8_t band = getBandFromFreq(CurrentVFO->Freq, true);
	if (band >= 0) {
		TRX.BANDS_SAVED_SETTINGS[band].BEST_ATU_I = TRX.ATU_I;
		TRX.BANDS_SAVED_SETTINGS[band].BEST_ATU_C = TRX.ATU_C;
		TRX.BANDS_SAVED_SETTINGS[band].BEST_ATU_T = TRX.ATU_T;
	}
}

static void SYSMENU_HANDL_TRX_ATU_T(int8_t direction) {
	if (direction > 0) {
		TRX.ATU_T = true;
	}
	if (direction < 0) {
		TRX.ATU_T = false;
	}

	int8_t band = getBandFromFreq(CurrentVFO->Freq, true);
	if (band >= 0) {
		TRX.BANDS_SAVED_SETTINGS[band].BEST_ATU_I = TRX.ATU_I;
		TRX.BANDS_SAVED_SETTINGS[band].BEST_ATU_C = TRX.ATU_C;
		TRX.BANDS_SAVED_SETTINGS[band].BEST_ATU_T = TRX.ATU_T;
	}
}

static void SYSMENU_HANDL_TRX_ATU_Enabled(int8_t direction) {
	if (direction > 0) {
		TRX.ATU_Enabled = true;
	}
	if (direction < 0) {
		TRX.ATU_Enabled = false;
	}
}

static void SYSMENU_HANDL_TRX_TUNER_Enabled(int8_t direction) {
	if (direction > 0) {
		TRX.TUNER_Enabled = true;
	}
	if (direction < 0) {
		TRX.TUNER_Enabled = false;
	}
}

// AUDIO MENU

static void SYSMENU_HANDL_AUDIOMENU(int8_t direction)
{
    (void) direction;

    sysmenu_handlers_selected = (const struct sysmenu_item_handler *)&sysmenu_audio_handlers[0];
	sysmenu_item_count = sizeof(sysmenu_audio_handlers) / sizeof(sysmenu_audio_handlers[0]);
	sysmenu_onroot = false;
	LCD_UpdateQuery.SystemMenuRedraw = true;
}

void SYSMENU_AUDIO_BW_SSB_HOTKEY(void) {
	SYSMENU_HANDL_AUDIOMENU(0);
	uint16_t index = getIndexByName(sysmenu_handlers_selected, sysmenu_item_count, "SSB LPF RX Pass");
	setCurrentMenuIndex(index);
	LCD_redraw(false);
}

void SYSMENU_AUDIO_IF_HOTKEY(void) {
	SYSMENU_HANDL_AUDIOMENU(0);
	uint16_t index = getIndexByName(sysmenu_handlers_selected, sysmenu_item_count, "IF Gain, dB");
	setCurrentMenuIndex(index);
	LCD_redraw(false);
}

void SYSMENU_AUDIO_BW_CW_HOTKEY(void) {
	SYSMENU_HANDL_AUDIOMENU(0);
	uint16_t index = getIndexByName(sysmenu_handlers_selected, sysmenu_item_count, "CW LPF Pass");
	setCurrentMenuIndex(index);
	LCD_redraw(false);
}

void SYSMENU_AUDIO_BW_AM_HOTKEY(void) {
	SYSMENU_HANDL_AUDIOMENU(0);
	uint16_t index = getIndexByName(sysmenu_handlers_selected, sysmenu_item_count, "AM LPF RX Pass");
	setCurrentMenuIndex(index);
	LCD_redraw(false);
}

void SYSMENU_AUDIO_BW_FM_HOTKEY(void) {
	SYSMENU_HANDL_AUDIOMENU(0);
	uint16_t index = getIndexByName(sysmenu_handlers_selected, sysmenu_item_count, "FM LPF RX Pass");
	setCurrentMenuIndex(index);
	LCD_redraw(false);
}

void SYSMENU_AUDIO_HPF_SSB_HOTKEY(void) {
	SYSMENU_HANDL_AUDIOMENU(0);
	uint16_t index = getIndexByName(sysmenu_handlers_selected, sysmenu_item_count, "SSB HPF RX Pass");
	setCurrentMenuIndex(index);
	LCD_redraw(false);
}

void SYSMENU_AUDIO_SQUELCH_HOTKEY(void) {
	SYSMENU_HANDL_AUDIOMENU(0);
	uint16_t index = getIndexByName(sysmenu_handlers_selected, sysmenu_item_count, "FM Squelch level, dbm");
	setCurrentMenuIndex(index);
	LCD_redraw(false);
}

void SYSMENU_AUDIO_DNR_HOTKEY(void) {
	SYSMENU_HANDL_AUDIOMENU(0);
	uint16_t index = getIndexByName(sysmenu_handlers_selected, sysmenu_item_count, "DNR1 Threshold");
	setCurrentMenuIndex(index);
	LCD_redraw(false);
}

void SYSMENU_AUDIO_AGC_HOTKEY(void) {
	SYSMENU_HANDL_AUDIOMENU(0);
	uint16_t index = getIndexByName(sysmenu_handlers_selected, sysmenu_item_count, "AGC");
	setCurrentMenuIndex(index);
	LCD_redraw(false);
}

void SYSMENU_AUDIO_NB_HOTKEY(void) {
	SYSMENU_HANDL_AUDIOMENU(0);
	uint16_t index = getIndexByName(sysmenu_handlers_selected, sysmenu_item_count, "NB Threshold");
	setCurrentMenuIndex(index);
	LCD_redraw(false);
}

void SYSMEUN_CALLSIGN_INFO_HOTKEY(void) {
	SYSMENU_HANDL_CALLSIGN_INFO(0);
	LCD_redraw(false);
}

void SYSMEUN_CALLSIGN_HOTKEY(void)
{
	SYSMENU_HANDL_TRX_SetCallsign(0);
	LCD_redraw(false);
}

void SYSMEUN_TIME_HOTKEY(void) {
	SYSMENU_HANDL_SETTIME(0);
	LCD_redraw(false);
}

void SYSMEUN_WIFI_HOTKEY(void) {
#if HRDW_HAS_WIFI
	SYSMENU_HANDL_WIFIMENU(0);
	uint16_t index = getIndexByName(sysmenu_handlers_selected, sysmenu_item_count, "WIFI Enabled");
	setCurrentMenuIndex(index);
	LCD_redraw(false);
#endif
}

void SYSMEUN_SD_HOTKEY(void) {
#if HRDW_HAS_SD
	SYSMENU_HANDL_SDMENU(0);
	uint16_t index = getIndexByName(sysmenu_handlers_selected, sysmenu_item_count, "File Manager");
	setCurrentMenuIndex(index);
	LCD_redraw(false);
#endif
}

static void SYSMENU_HANDL_AUDIO_Volume(int8_t direction) {
	if (direction > 0 || TRX.Volume > 0) {
		TRX.Volume += direction;
	}
	if (TRX.Volume > 100) {
		TRX.Volume = 100;
	}
}

static void SYSMENU_HANDL_AUDIO_Volume_Step(int8_t direction) {
	if (direction > 0 || TRX.Volume_Step > 1) {
		TRX.Volume_Step += direction;
	}
	if (TRX.Volume_Step > 25) {
		TRX.Volume_Step = 25;
	}
}

static void SYSMENU_HANDL_AUDIO_DNR(int8_t direction) {
	TRX_TemporaryMute();

	if (direction > 0 || CurrentVFO->DNR_Type > 0) {
		CurrentVFO->DNR_Type += direction;
	}
	if (CurrentVFO->DNR_Type > 2) {
		CurrentVFO->DNR_Type = 2;
	}

	TRX.DNR_shadow = CurrentVFO->DNR_Type;

	int8_t band = getBandFromFreq(CurrentVFO->Freq, true);
	if (band > 0) {
		TRX.BANDS_SAVED_SETTINGS[band].DNR_Type = CurrentVFO->DNR_Type;
	}
}

static void SYSMENU_HANDL_AUDIO_AGC(int8_t direction) {
	if (direction > 0) {
		CurrentVFO->AGC = true;
	}
	if (direction < 0) {
		CurrentVFO->AGC = false;
	}

	TRX.AGC_shadow = CurrentVFO->AGC;

	int8_t band = getBandFromFreq(CurrentVFO->Freq, true);
	if (band > 0) {
		TRX.BANDS_SAVED_SETTINGS[band].AGC = CurrentVFO->AGC;
	}
}

static void SYSMENU_HANDL_AUDIO_NOISE_BLANKER(int8_t direction) {
	if (direction > 0) {
		TRX.NOISE_BLANKER = true;
	}
	if (direction < 0) {
		TRX.NOISE_BLANKER = false;
	}
}

static void SYSMENU_HANDL_AUDIO_IFGain(int8_t direction) {
	TRX.IF_Gain += direction;
	if (TRX.IF_Gain < CALIBRATE.IF_GAIN_MIN) {
		TRX.IF_Gain = CALIBRATE.IF_GAIN_MIN;
	}
	if (TRX.IF_Gain > CALIBRATE.IF_GAIN_MAX) {
		TRX.IF_Gain = CALIBRATE.IF_GAIN_MAX;
	}

	int8_t band = getBandFromFreq(CurrentVFO->Freq, true);
	if (band > 0) {
		TRX.BANDS_SAVED_SETTINGS[band].IF_Gain = TRX.IF_Gain;
	}
}

static void SYSMENU_HANDL_AUDIO_AGC_GAIN_TARGET(int8_t direction) {
	TRX.AGC_GAIN_TARGET += direction;
	if (TRX.AGC_GAIN_TARGET < -80) {
		TRX.AGC_GAIN_TARGET = -80;
	}
	if (TRX.AGC_GAIN_TARGET > -10) {
		TRX.AGC_GAIN_TARGET = -10;
	}
}

static void SYSMENU_HANDL_AUDIO_MIC_Gain(int8_t direction) {
	TRX.MIC_GAIN_DB += direction * 0.1f;
	if (TRX.MIC_GAIN_DB < 1.0f) {
		TRX.MIC_GAIN_DB = 1.0f;
	}
	if (TRX.MIC_GAIN_DB > 20.0f) {
		TRX.MIC_GAIN_DB = 20.0f;
	}
}

static void SYSMENU_HANDL_AUDIO_MIC_Boost(int8_t direction) {
	if (direction < 0) {
		TRX.MIC_Boost = false;
	}
	if (direction > 0) {
		TRX.MIC_Boost = true;
	}

	// reinit codec
	CODEC_TXRX_mode();
}

static void SYSMENU_HANDL_AUDIO_DNR1_THRES(int8_t direction) {
	TRX.DNR1_SNR_THRESHOLD += direction;
	if (TRX.DNR1_SNR_THRESHOLD < 1) {
		TRX.DNR1_SNR_THRESHOLD = 1;
	}
	if (TRX.DNR1_SNR_THRESHOLD > 100) {
		TRX.DNR1_SNR_THRESHOLD = 100;
	}
}

static void SYSMENU_HANDL_AUDIO_DNR2_THRES(int8_t direction) {
	TRX.DNR2_SNR_THRESHOLD += direction;
	if (TRX.DNR2_SNR_THRESHOLD < 1) {
		TRX.DNR2_SNR_THRESHOLD = 1;
	}
	if (TRX.DNR2_SNR_THRESHOLD > 100) {
		TRX.DNR2_SNR_THRESHOLD = 100;
	}
}

static void SYSMENU_HANDL_AUDIO_DNR_AVERAGE(int8_t direction) {
	TRX.DNR_AVERAGE += direction;
	if (TRX.DNR_AVERAGE < 1) {
		TRX.DNR_AVERAGE = 1;
	}
	if (TRX.DNR_AVERAGE > 100) {
		TRX.DNR_AVERAGE = 100;
	}
}

static void SYSMENU_HANDL_AUDIO_DNR_MINMAL(int8_t direction) {
	TRX.DNR_MINIMAL += direction;
	if (TRX.DNR_MINIMAL < 1) {
		TRX.DNR_MINIMAL = 1;
	}
	if (TRX.DNR_MINIMAL > 100) {
		TRX.DNR_MINIMAL = 100;
	}
}

static void SYSMENU_HANDL_AUDIO_NOISE_BLANKER_THRESHOLD(int8_t direction) {
	TRX.NOISE_BLANKER_THRESHOLD += direction;
	if (TRX.NOISE_BLANKER_THRESHOLD < 1) {
		TRX.NOISE_BLANKER_THRESHOLD = 1;
	}
	if (TRX.NOISE_BLANKER_THRESHOLD > 20) {
		TRX.NOISE_BLANKER_THRESHOLD = 20;
	}
}

static void SYSMENU_HANDL_AUDIO_MIC_EQ_P1_SSB(int8_t direction) {
	TRX.MIC_EQ_P1_SSB += direction;
	if (TRX.MIC_EQ_P1_SSB < -50) {
		TRX.MIC_EQ_P1_SSB = -50;
	}
	if (TRX.MIC_EQ_P1_SSB > 50) {
		TRX.MIC_EQ_P1_SSB = 50;
	}
	NeedReinitAudioFilters = true;
}

static void SYSMENU_HANDL_AUDIO_MIC_EQ_P1_AMFM(int8_t direction) {
	TRX.MIC_EQ_P1_AMFM += direction;
	if (TRX.MIC_EQ_P1_AMFM < -50) {
		TRX.MIC_EQ_P1_AMFM = -50;
	}
	if (TRX.MIC_EQ_P1_AMFM > 50) {
		TRX.MIC_EQ_P1_AMFM = 50;
	}
	NeedReinitAudioFilters = true;
}

static void SYSMENU_HANDL_AUDIO_MIC_EQ_P2_SSB(int8_t direction) {
	TRX.MIC_EQ_P2_SSB += direction;
	if (TRX.MIC_EQ_P2_SSB < -50) {
		TRX.MIC_EQ_P2_SSB = -50;
	}
	if (TRX.MIC_EQ_P2_SSB > 50) {
		TRX.MIC_EQ_P2_SSB = 50;
	}
	NeedReinitAudioFilters = true;
}

static void SYSMENU_HANDL_AUDIO_MIC_EQ_P2_AMFM(int8_t direction) {
	TRX.MIC_EQ_P2_AMFM += direction;
	if (TRX.MIC_EQ_P2_AMFM < -50) {
		TRX.MIC_EQ_P2_AMFM = -50;
	}
	if (TRX.MIC_EQ_P2_AMFM > 50) {
		TRX.MIC_EQ_P2_AMFM = 50;
	}
	NeedReinitAudioFilters = true;
}

static void SYSMENU_HANDL_AUDIO_MIC_EQ_P3_SSB(int8_t direction) {
	TRX.MIC_EQ_P3_SSB += direction;
	if (TRX.MIC_EQ_P3_SSB < -50) {
		TRX.MIC_EQ_P3_SSB = -50;
	}
	if (TRX.MIC_EQ_P3_SSB > 50) {
		TRX.MIC_EQ_P3_SSB = 50;
	}
	NeedReinitAudioFilters = true;
}

static void SYSMENU_HANDL_AUDIO_MIC_EQ_P3_AMFM(int8_t direction) {
	TRX.MIC_EQ_P3_AMFM += direction;
	if (TRX.MIC_EQ_P3_AMFM < -50) {
		TRX.MIC_EQ_P3_AMFM = -50;
	}
	if (TRX.MIC_EQ_P3_AMFM > 50) {
		TRX.MIC_EQ_P3_AMFM = 50;
	}
	NeedReinitAudioFilters = true;
}

static void SYSMENU_HANDL_AUDIO_MIC_EQ_P4_SSB(int8_t direction) {
	TRX.MIC_EQ_P4_SSB += direction;
	if (TRX.MIC_EQ_P4_SSB < -50) {
		TRX.MIC_EQ_P4_SSB = -50;
	}
	if (TRX.MIC_EQ_P4_SSB > 50) {
		TRX.MIC_EQ_P4_SSB = 50;
	}
	NeedReinitAudioFilters = true;
}

static void SYSMENU_HANDL_AUDIO_MIC_EQ_P4_AMFM(int8_t direction) {
	TRX.MIC_EQ_P4_AMFM += direction;
	if (TRX.MIC_EQ_P4_AMFM < -50) {
		TRX.MIC_EQ_P4_AMFM = -50;
	}
	if (TRX.MIC_EQ_P4_AMFM > 50) {
		TRX.MIC_EQ_P4_AMFM = 50;
	}
	NeedReinitAudioFilters = true;
}

static void SYSMENU_HANDL_AUDIO_MIC_EQ_P5_SSB(int8_t direction) {
	TRX.MIC_EQ_P5_SSB += direction;
	if (TRX.MIC_EQ_P5_SSB < -50) {
		TRX.MIC_EQ_P5_SSB = -50;
	}
	if (TRX.MIC_EQ_P5_SSB > 50) {
		TRX.MIC_EQ_P5_SSB = 50;
	}
	NeedReinitAudioFilters = true;
}

static void SYSMENU_HANDL_AUDIO_MIC_EQ_P5_AMFM(int8_t direction) {
	TRX.MIC_EQ_P5_AMFM += direction;
	if (TRX.MIC_EQ_P5_AMFM < -50) {
		TRX.MIC_EQ_P5_AMFM = -50;
	}
	if (TRX.MIC_EQ_P5_AMFM > 50) {
		TRX.MIC_EQ_P5_AMFM = 50;
	}
	NeedReinitAudioFilters = true;
}

static void SYSMENU_HANDL_AUDIO_MIC_REVERBER(int8_t direction) {
	if (direction > 0 || TRX.MIC_REVERBER > 0) {
		TRX.MIC_REVERBER += direction;
	}
	if (TRX.MIC_REVERBER > (AUDIO_MAX_REVERBER_TAPS - 1)) {
		TRX.MIC_REVERBER = (AUDIO_MAX_REVERBER_TAPS - 1);
	}
	NeedReinitReverber = true;
}

static void SYSMENU_HANDL_AUDIO_MIC_NOISE_GATE(int8_t direction) {
	TRX.MIC_NOISE_GATE += direction;
	if (TRX.MIC_NOISE_GATE < -120) {
		TRX.MIC_NOISE_GATE = -120;
	}
	if (TRX.MIC_NOISE_GATE > 0) {
		TRX.MIC_NOISE_GATE = 0;
	}
}

static void SYSMENU_HANDL_AUDIO_RX_EQ_P1(int8_t direction) {
	TRX.RX_EQ_P1 += direction;
	if (TRX.RX_EQ_P1 < -50) {
		TRX.RX_EQ_P1 = -50;
	}
	if (TRX.RX_EQ_P1 > 50) {
		TRX.RX_EQ_P1 = 50;
	}
	NeedReinitAudioFilters = true;
}

static void SYSMENU_HANDL_AUDIO_RX_EQ_P2(int8_t direction) {
	TRX.RX_EQ_P2 += direction;
	if (TRX.RX_EQ_P2 < -50) {
		TRX.RX_EQ_P2 = -50;
	}
	if (TRX.RX_EQ_P2 > 50) {
		TRX.RX_EQ_P2 = 50;
	}
	NeedReinitAudioFilters = true;
}

static void SYSMENU_HANDL_AUDIO_RX_EQ_P3(int8_t direction) {
	TRX.RX_EQ_P3 += direction;
	if (TRX.RX_EQ_P3 < -50) {
		TRX.RX_EQ_P3 = -50;
	}
	if (TRX.RX_EQ_P3 > 50) {
		TRX.RX_EQ_P3 = 50;
	}
	NeedReinitAudioFilters = true;
}

static void SYSMENU_HANDL_AUDIO_RX_EQ_P4(int8_t direction) {
	TRX.RX_EQ_P4 += direction;
	if (TRX.RX_EQ_P4 < -50) {
		TRX.RX_EQ_P4 = -50;
	}
	if (TRX.RX_EQ_P4 > 50) {
		TRX.RX_EQ_P4 = 50;
	}
	NeedReinitAudioFilters = true;
}

static void SYSMENU_HANDL_AUDIO_RX_EQ_P5(int8_t direction) {
	TRX.RX_EQ_P5 += direction;
	if (TRX.RX_EQ_P5 < -50) {
		TRX.RX_EQ_P5 = -50;
	}
	if (TRX.RX_EQ_P5 > 50) {
		TRX.RX_EQ_P5 = 50;
	}
	NeedReinitAudioFilters = true;
}

static void SYSMENU_HANDL_AUDIO_RX_AGC_SSB_Speed(int8_t direction) {
	TRX.RX_AGC_SSB_speed += direction;
	if (TRX.RX_AGC_SSB_speed < 1) {
		TRX.RX_AGC_SSB_speed = 1;
	}
	if (TRX.RX_AGC_SSB_speed > 20) {
		TRX.RX_AGC_SSB_speed = 20;
	}
}

static void SYSMENU_HANDL_AUDIO_RX_AGC_CW_Speed(int8_t direction) {
	TRX.RX_AGC_CW_speed += direction;
	if (TRX.RX_AGC_CW_speed < 1) {
		TRX.RX_AGC_CW_speed = 1;
	}
	if (TRX.RX_AGC_CW_speed > 20) {
		TRX.RX_AGC_CW_speed = 20;
	}
}

static void SYSMENU_HANDL_AUDIO_RX_AGC_Max_gain(int8_t direction) {
	TRX.RX_AGC_Max_gain += direction;
	if (TRX.RX_AGC_Max_gain < 1) {
		TRX.RX_AGC_Max_gain = 1;
	}
	if (TRX.RX_AGC_Max_gain > 50) {
		TRX.RX_AGC_Max_gain = 50;
	}
}

static void SYSMENU_HANDL_AUDIO_RX_AGC_Hold(int8_t direction) {
	if (TRX.RX_AGC_Hold > 0 || direction > 0) {
		TRX.RX_AGC_Hold += direction * 100;
	}
	if (TRX.RX_AGC_Hold > 5000) {
		TRX.RX_AGC_Hold = 5000;
	}
}

static void SYSMENU_HANDL_AUDIO_TX_CompressorSpeed_SSB(int8_t direction) {
	TRX.TX_Compressor_speed_SSB += direction;
	if (TRX.TX_Compressor_speed_SSB < 1) {
		TRX.TX_Compressor_speed_SSB = 1;
	}
	if (TRX.TX_Compressor_speed_SSB > 200) {
		TRX.TX_Compressor_speed_SSB = 200;
	}
}

static void SYSMENU_HANDL_AUDIO_TX_CompressorSpeed_AMFM(int8_t direction) {
	TRX.TX_Compressor_speed_AMFM += direction;
	if (TRX.TX_Compressor_speed_AMFM < 1) {
		TRX.TX_Compressor_speed_AMFM = 1;
	}
	if (TRX.TX_Compressor_speed_AMFM > 200) {
		TRX.TX_Compressor_speed_AMFM = 200;
	}
}

static void SYSMENU_HANDL_AUDIO_TX_CompressorMaxGain_SSB(int8_t direction) {
	TRX.TX_Compressor_maxgain_SSB += direction;
	if (TRX.TX_Compressor_maxgain_SSB < 1) {
		TRX.TX_Compressor_maxgain_SSB = 1;
	}
	if (TRX.TX_Compressor_maxgain_SSB > 30) {
		TRX.TX_Compressor_maxgain_SSB = 30;
	}
}

static void SYSMENU_HANDL_AUDIO_TX_CompressorMaxGain_AMFM(int8_t direction) {
	TRX.TX_Compressor_maxgain_AMFM += direction;
	if (TRX.TX_Compressor_maxgain_AMFM < 1) {
		TRX.TX_Compressor_maxgain_AMFM = 1;
	}
	if (TRX.TX_Compressor_maxgain_AMFM > 30) {
		TRX.TX_Compressor_maxgain_AMFM = 30;
	}
}

static void SYSMENU_HANDL_AUDIO_FMSquelch(int8_t direction) {
	CurrentVFO->FM_SQL_threshold_dbm += direction;
	TRX.FM_SQL_threshold_dbm_shadow = CurrentVFO->FM_SQL_threshold_dbm;

	int8_t band = getBandFromFreq(CurrentVFO->Freq, true);
	if (band >= 0) {
		TRX.BANDS_SAVED_SETTINGS[band].FM_SQL_threshold_dbm = CurrentVFO->FM_SQL_threshold_dbm;
	}
}

static void SYSMENU_HANDL_AUDIO_Squelch(int8_t direction) {
	if (direction > 0) {
		CurrentVFO->SQL = true;
	}
	if (direction < 0) {
		CurrentVFO->SQL = false;
	}
	TRX.SQL_shadow = CurrentVFO->SQL;

	int8_t band = getBandFromFreq(CurrentVFO->Freq, true);
	if (band >= 0) {
		TRX.BANDS_SAVED_SETTINGS[band].SQL = CurrentVFO->SQL;
	}
}

void SYSMENU_HANDL_AUDIO_SSB_HPF_RX_pass(int8_t direction) {
	if (TRX.SSB_HPF_RX_Filter > 0 || direction > 0) {
		TRX.SSB_HPF_RX_Filter += direction * 50;
	}
	if (TRX.SSB_HPF_RX_Filter > MAX_HPF_WIDTH) {
		TRX.SSB_HPF_RX_Filter = MAX_HPF_WIDTH;
	}

	if (TRX.SSB_HPF_RX_Filter > TRX.SSB_LPF_RX_Filter) {
		TRX.SSB_HPF_RX_Filter = TRX.SSB_LPF_RX_Filter;
	}

	TRX_setMode(SecondaryVFO->Mode, SecondaryVFO);
	TRX_setMode(CurrentVFO->Mode, CurrentVFO);
}

void SYSMENU_HANDL_AUDIO_SSB_HPF_TX_pass(int8_t direction) {
	if (TRX.SSB_HPF_TX_Filter > 0 || direction > 0) {
		TRX.SSB_HPF_TX_Filter += direction * 50;
	}
	if (TRX.SSB_HPF_TX_Filter > MAX_HPF_WIDTH) {
		TRX.SSB_HPF_TX_Filter = MAX_HPF_WIDTH;
	}

	if (TRX.SSB_HPF_TX_Filter > TRX.SSB_LPF_TX_Filter) {
		TRX.SSB_HPF_TX_Filter = TRX.SSB_LPF_TX_Filter;
	}

	TRX_setMode(SecondaryVFO->Mode, SecondaryVFO);
	TRX_setMode(CurrentVFO->Mode, CurrentVFO);
}

void SYSMENU_HANDL_AUDIO_CW_LPF_pass(int8_t direction) {
	if (TRX.CW_LPF_Filter > 50 || direction > 0) {
		TRX.CW_LPF_Filter += direction * 50;
	}
	if (TRX.CW_LPF_Filter > MAX_LPF_WIDTH_CW) {
		TRX.CW_LPF_Filter = MAX_LPF_WIDTH_CW;
	}

	TRX_setMode(SecondaryVFO->Mode, SecondaryVFO);
	TRX_setMode(CurrentVFO->Mode, CurrentVFO);
}

void SYSMENU_HANDL_AUDIO_DIGI_LPF_pass(int8_t direction) {
	if (TRX.DIGI_LPF_Filter > 50 || direction > 0) {
		TRX.DIGI_LPF_Filter += direction * 50;
	}
	if (TRX.DIGI_LPF_Filter > MAX_LPF_WIDTH_SSB) {
		TRX.DIGI_LPF_Filter = MAX_LPF_WIDTH_SSB;
	}

	TRX_setMode(SecondaryVFO->Mode, SecondaryVFO);
	TRX_setMode(CurrentVFO->Mode, CurrentVFO);
}

void SYSMENU_HANDL_AUDIO_SSB_LPF_RX_pass(int8_t direction) {
	if (TRX.SSB_LPF_RX_Filter > 100 || direction > 0) {
		TRX.SSB_LPF_RX_Filter += direction * 100;
	}
	if (TRX.SSB_LPF_RX_Filter > MAX_LPF_WIDTH_SSB) {
		TRX.SSB_LPF_RX_Filter = MAX_LPF_WIDTH_SSB;
	}

	TRX_setMode(SecondaryVFO->Mode, SecondaryVFO);
	TRX_setMode(CurrentVFO->Mode, CurrentVFO);
}

void SYSMENU_HANDL_AUDIO_SSB_LPF_TX_pass(int8_t direction) {
	if (TRX.SSB_LPF_TX_Filter > 100 || direction > 0) {
		TRX.SSB_LPF_TX_Filter += direction * 100;
	}
	if (TRX.SSB_LPF_TX_Filter > MAX_LPF_WIDTH_SSB) {
		TRX.SSB_LPF_TX_Filter = MAX_LPF_WIDTH_SSB;
	}

	TRX_setMode(SecondaryVFO->Mode, SecondaryVFO);
	TRX_setMode(CurrentVFO->Mode, CurrentVFO);
}

void SYSMENU_HANDL_AUDIO_AM_LPF_RX_pass(int8_t direction) {
	if (TRX.AM_LPF_RX_Filter > 100 || direction > 0) {
		TRX.AM_LPF_RX_Filter += direction * 100;
	}
	if (TRX.AM_LPF_RX_Filter > MAX_LPF_WIDTH_AM) {
		TRX.AM_LPF_RX_Filter = MAX_LPF_WIDTH_AM;
	}

	TRX_setMode(SecondaryVFO->Mode, SecondaryVFO);
	TRX_setMode(CurrentVFO->Mode, CurrentVFO);
}

void SYSMENU_HANDL_AUDIO_AM_LPF_TX_pass(int8_t direction) {
	if (TRX.AM_LPF_TX_Filter > 100 || direction > 0) {
		TRX.AM_LPF_TX_Filter += direction * 100;
	}
	if (TRX.AM_LPF_TX_Filter > MAX_LPF_WIDTH_AM) {
		TRX.AM_LPF_TX_Filter = MAX_LPF_WIDTH_AM;
	}

	TRX_setMode(SecondaryVFO->Mode, SecondaryVFO);
	TRX_setMode(CurrentVFO->Mode, CurrentVFO);
}

void SYSMENU_HANDL_AUDIO_FM_LPF_RX_pass(int8_t direction) {
	if (TRX.FM_LPF_RX_Filter > 1000 || direction > 0) {
		TRX.FM_LPF_RX_Filter += direction * 1000;
	}
	if (TRX.FM_LPF_RX_Filter > MAX_LPF_WIDTH_NFM) {
		TRX.FM_LPF_RX_Filter = MAX_LPF_WIDTH_NFM;
	}

	TRX_setMode(SecondaryVFO->Mode, SecondaryVFO);
	TRX_setMode(CurrentVFO->Mode, CurrentVFO);
}

void SYSMENU_HANDL_AUDIO_FM_LPF_TX_pass(int8_t direction) {
	if (TRX.FM_LPF_TX_Filter > 1000 || direction > 0) {
		TRX.FM_LPF_TX_Filter += direction * 1000;
	}
	if (TRX.FM_LPF_TX_Filter > MAX_LPF_WIDTH_NFM) {
		TRX.FM_LPF_TX_Filter = MAX_LPF_WIDTH_NFM;
	}

	TRX_setMode(SecondaryVFO->Mode, SecondaryVFO);
	TRX_setMode(CurrentVFO->Mode, CurrentVFO);
}

static void SYSMENU_HANDL_AUDIO_Beeper(int8_t direction) {
	if (direction > 0) {
		TRX.Beeper = true;
	}
	if (direction < 0) {
		TRX.Beeper = false;
	}
}

static void SYSMENU_HANDL_AUDIO_CTCSS_Freq(int8_t direction) {
	uint16_t current_pos = 0;
	for (uint16_t i = 0; i < CTCSS_FREQS_COUNT; i++) {
		if (CTCSS_Freqs[i] == TRX.CTCSS_Freq) {
			current_pos = i;
		}
	}
	if (direction > 0) {
		current_pos++;
	}
	if (direction < 0 && current_pos > 0) {
		current_pos--;
	}
	if (current_pos >= CTCSS_FREQS_COUNT) {
		current_pos = CTCSS_FREQS_COUNT - 1;
	}
	TRX.CTCSS_Freq = CTCSS_Freqs[current_pos];
}

static void SYSMENU_HANDL_AUDIO_SELFHEAR_Volume(int8_t direction) {
	TRX.SELFHEAR_Volume += direction;
	if (TRX.SELFHEAR_Volume > 100) {
		TRX.SELFHEAR_Volume = 100;
	}
	if (TRX.SELFHEAR_Volume < 1) {
		TRX.SELFHEAR_Volume = 1;
	}
}

static void SYSMENU_HANDL_AUDIO_FM_Stereo(int8_t direction) {
	if (direction > 0) {
		TRX.FM_Stereo = true;
	}
	if (direction < 0) {
		TRX.FM_Stereo = false;
	}
}

static void SYSMENU_HANDL_AUDIO_AGC_Spectral(int8_t direction) {
	if (direction > 0) {
		TRX.AGC_Spectral = true;
	}
	if (direction < 0) {
		TRX.AGC_Spectral = false;
	}
}

static void SYSMENU_HANDL_AUDIO_TX_CESSB(int8_t direction) {
	if (direction > 0) {
		TRX.TX_CESSB = true;
	}
	if (direction < 0) {
		TRX.TX_CESSB = false;
	}
}

static void SYSMENU_HANDL_AUDIO_TX_CESSB_COMPRESS_DB(int8_t direction) {
	TRX.TX_CESSB_COMPRESS_DB += direction * 0.1f;
	if (TRX.TX_CESSB_COMPRESS_DB < 1.0f) {
		TRX.TX_CESSB_COMPRESS_DB = 1.0f;
	}
	if (TRX.TX_CESSB_COMPRESS_DB > 20.0f) {
		TRX.TX_CESSB_COMPRESS_DB = 20.0f;
	}
}

static void SYSMENU_HANDL_AUDIO_VAD_THRESHOLD(int8_t direction) {
	TRX.VAD_THRESHOLD += direction;
	if (TRX.VAD_THRESHOLD > 200) {
		TRX.VAD_THRESHOLD = 200;
	}
	if (TRX.VAD_THRESHOLD < 1) {
		TRX.VAD_THRESHOLD = 1;
	}
}

static void SYSMENU_HANDL_AUDIO_VOX(int8_t direction) {
	if (direction > 0) {
		TRX.VOX = true;
	}
	if (direction < 0) {
		TRX.VOX = false;
	}
}
static void SYSMENU_HANDL_AUDIO_VOX_TIMEOUT(int8_t direction) {
	TRX.VOX_TIMEOUT += direction * 50;
	if (TRX.VOX_TIMEOUT > 2000) {
		TRX.VOX_TIMEOUT = 2000;
	}
	if (TRX.VOX_TIMEOUT < 50) {
		TRX.VOX_TIMEOUT = 50;
	}
}
static void SYSMENU_HANDL_AUDIO_VOX_THRESHOLD(int8_t direction) {
	TRX.VOX_THRESHOLD += direction;
	if (TRX.VOX_THRESHOLD > 0) {
		TRX.VOX_THRESHOLD = 0;
	}
	if (TRX.VOX_THRESHOLD < -120) {
		TRX.VOX_THRESHOLD = -120;
	}
}

// CW MENU

static void SYSMENU_HANDL_CWMENU(int8_t direction)
{
    (void) direction;

    sysmenu_handlers_selected = (const struct sysmenu_item_handler *)&sysmenu_cw_handlers[0];
	sysmenu_item_count = sizeof(sysmenu_cw_handlers) / sizeof(sysmenu_cw_handlers[0]);
	sysmenu_onroot = false;
	LCD_redraw(false);
}

void SYSMENU_CW_WPM_HOTKEY(void) {
	SYSMENU_HANDL_CWMENU(0);
	uint16_t index = getIndexByName(sysmenu_handlers_selected, sysmenu_item_count, "CW Keyer WPM");
	setCurrentMenuIndex(index);
	LCD_redraw(false);
}

void SYSMENU_CW_KEYER_HOTKEY(void) {
	SYSMENU_HANDL_CWMENU(0);
	uint16_t index = getIndexByName(sysmenu_handlers_selected, sysmenu_item_count, "CW Keyer");
	setCurrentMenuIndex(index);
	LCD_redraw(false);
}

static void SYSMENU_HANDL_CW_Pitch(int8_t direction) {
	TRX.CW_Pitch += direction * 10;
	if (TRX.CW_Pitch < 50) {
		TRX.CW_Pitch = 50;
	}
	if (TRX.CW_Pitch > 10000) {
		TRX.CW_Pitch = 10000;
	}
}

static void SYSMENU_HANDL_CW_Key_timeout(int8_t direction) {
	TRX.CW_Key_timeout += direction * 50;
	if (TRX.CW_Key_timeout < 50) {
		TRX.CW_Key_timeout = 50;
	}
	if (TRX.CW_Key_timeout > 5000) {
		TRX.CW_Key_timeout = 5000;
	}
}

static void SYSMENU_HANDL_CW_Keyer(int8_t direction) {
	if (direction > 0) {
		TRX.CW_KEYER = true;
	}
	if (direction < 0) {
		TRX.CW_KEYER = false;
	}
}

static void SYSMENU_HANDL_CW_GaussFilter(int8_t direction) {
	if (direction > 0) {
		TRX.CW_GaussFilter = true;
	}
	if (direction < 0) {
		TRX.CW_GaussFilter = false;
	}
	NeedReinitAudioFilters = true;
}

static void SYSMENU_HANDL_CW_Keyer_WPM(int8_t direction) {
	TRX.CW_KEYER_WPM += direction;
	if (TRX.CW_KEYER_WPM < 1) {
		TRX.CW_KEYER_WPM = 1;
	}
	if (TRX.CW_KEYER_WPM > 200) {
		TRX.CW_KEYER_WPM = 200;
	}
}

static void SYSMENU_HANDL_CW_SelfHear(int8_t direction) {
	if (direction > 0) {
		TRX.CW_SelfHear = true;
	}
	if (direction < 0) {
		TRX.CW_SelfHear = false;
	}
}

static void SYSMENU_HANDL_CW_DotToDashRate(int8_t direction) {
	TRX.CW_DotToDashRate += 0.01f * direction;
	if (TRX.CW_DotToDashRate < 3.0f) {
		TRX.CW_DotToDashRate = 3.0f;
	}
	if (TRX.CW_DotToDashRate > 5.0f) {
		TRX.CW_DotToDashRate = 5.0f;
	}
}

static void SYSMENU_HANDL_CW_Iambic(int8_t direction) {
	if (direction > 0) {
		TRX.CW_Iambic = true;
	}
	if (direction < 0) {
		TRX.CW_Iambic = false;
	}
}

static void SYSMENU_HANDL_CW_Invert(int8_t direction) {
	if (direction > 0) {
		TRX.CW_Invert = true;
	}
	if (direction < 0) {
		TRX.CW_Invert = false;
	}
}

static void SYSMENU_HANDL_CW_PTT_Type(int8_t direction) {
	if (direction > 0 || TRX.CW_PTT_Type > 0) {
		TRX.CW_PTT_Type += direction;
	}
	if (TRX.CW_PTT_Type > 2) {
		TRX.CW_PTT_Type = 2;
	}

	KEYER_symbol_status = 0;
}

// SCREEN MENU

static void SYSMENU_HANDL_LCDMENU(int8_t direction)
{
    (void) direction;

    sysmenu_handlers_selected = (const struct sysmenu_item_handler *)&sysmenu_screen_handlers[0];
	sysmenu_item_count = sizeof(sysmenu_screen_handlers) / sizeof(sysmenu_screen_handlers[0]);
	sysmenu_onroot = false;
	LCD_UpdateQuery.SystemMenuRedraw = true;
}

static void SYSMENU_HANDL_SCREEN_FFT_Enabled(int8_t direction) {
	if (direction > 0) {
		TRX.FFT_Enabled = true;
	}
	if (direction < 0) {
		TRX.FFT_Enabled = false;
	}
}

static void SYSMENU_HANDL_SCREEN_COLOR_THEME(int8_t direction) {
	if (direction > 0 || TRX.ColorThemeId > 0) {
		TRX.ColorThemeId += direction;
	}
	if (TRX.ColorThemeId > (COLOR_THEMES_COUNT - 1)) {
		TRX.ColorThemeId = (COLOR_THEMES_COUNT - 1);
	}

	COLOR = &COLOR_THEMES[TRX.ColorThemeId];
	FFT_Init();
	LCD_redraw(false);
}
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
