hristoandreev/UA3REO-DDC-Transceiver/STM32/WOLF/Src/front_unit.c

#include "front_unit.h"
#include "agc.h"
#include "audio_filters.h"
#include "auto_notch.h"
#include "functions.h"
#include "lcd.h"
#include "main.h"
#include "noise_reduction.h"
#include "rf_unit.h"
#include "sd.h"
#include "settings.h"
#include "stm32h7xx_hal.h"
#include "system_menu.h"
#include "trx_manager.h"
#include "vad.h"

int8_t FRONTPANEL_ProcessEncoder1 = 0;
int8_t FRONTPANEL_ProcessEncoder2 = 0;

#ifdef HRDW_MCP3008_1
bool FRONTPanel_MCP3008_1_Enabled = true;
#endif
#ifdef HRDW_MCP3008_2
bool FRONTPanel_MCP3008_2_Enabled = true;
#endif
#ifdef HRDW_MCP3008_3
bool FRONTPanel_MCP3008_3_Enabled = true;
#endif

static void FRONTPANEL_ENCODER_Rotated(float32_t direction);
static void FRONTPANEL_ENCODER2_Rotated(int8_t direction);
static void FRONTPANEL_ENCODER2_Rotated(int8_t direction);
static void FRONTPANEL_ENC2SW_click_handler(uint32_t parameter);
static void FRONTPANEL_ENC2SW_hold_handler(uint32_t parameter);
static uint16_t FRONTPANEL_ReadMCP3008_Value(uint8_t channel, uint8_t adc_num, uint8_t count);

static int32_t ENCODER_slowler = 0;
static uint32_t ENCODER_AValDeb = 0;
static uint32_t ENCODER2_AValDeb = 0;

#ifdef FRONTPANEL_SMALL_V1
PERIPH_FrontPanel_Button PERIPH_FrontPanel_Buttons[] = {
    {.port = 1,
     .channel = 7,
     .type = FUNIT_CTRL_BUTTON,
     .tres_min = 0,
     .tres_max = MCP3008_SINGLE_THRESHOLD,
     .state = false,
     .prev_state = false,
     .work_in_menu = false,
     .parameter = 0,
     .clickHandler = BUTTONHANDLER_PRE,
     .holdHandler = BUTTONHANDLER_PGA}, // PRE-PGA
    {.port = 1,
     .channel = 6,
     .type = FUNIT_CTRL_BUTTON,
     .tres_min = 0,
     .tres_max = MCP3008_SINGLE_THRESHOLD,
     .state = false,
     .prev_state = false,
     .work_in_menu = false,
     .parameter = 0,
     .clickHandler = BUTTONHANDLER_ATT,
     .holdHandler = BUTTONHANDLER_ATTHOLD}, // ATT-ATTHOLD
    {.port = 1,
     .channel = 5,
     .type = FUNIT_CTRL_BUTTON,
     .tres_min = 0,
     .tres_max = MCP3008_SINGLE_THRESHOLD,
     .state = false,
     .prev_state = false,
     .work_in_menu = false,
     .parameter = 0,
     .clickHandler = BUTTONHANDLER_MUTE,
     .holdHandler = BUTTONHANDLER_SCAN}, // MUTE-SCAN
    {.port = 1,
     .channel = 4,
     .type = FUNIT_CTRL_BUTTON,
     .tres_min = 0,
     .tres_max = MCP3008_SINGLE_THRESHOLD,
     .state = false,
     .prev_state = false,
     .work_in_menu = true,
     .parameter = 0,
     .clickHandler = BUTTONHANDLER_AGC,
     .holdHandler = BUTTONHANDLER_AGC_SPEED}, // AGC-AGCSPEED
    {.port = 1,
     .channel = 3,
     .type = FUNIT_CTRL_BUTTON,
     .tres_min = 0,
     .tres_max = MCP3008_SINGLE_THRESHOLD,
     .state = false,
     .prev_state = false,
     .work_in_menu = false,
     .parameter = 0,
     .clickHandler = BUTTONHANDLER_ArB,
     .holdHandler = BUTTONHANDLER_ANT}, // A=B-ANT
    {.port = 1,
     .channel = 2,
     .type = FUNIT_CTRL_BUTTON,
     .tres_min = 0,
     .tres_max = MCP3008_SINGLE_THRESHOLD,
     .state = false,
     .prev_state = false,
     .work_in_menu = true,
     .parameter = 0,
     .clickHandler = BUTTONHANDLER_TUNE,
     .holdHandler = BUTTONHANDLER_TUNE}, // TUNE
    {.port = 1,
     .channel = 1,
     .type = FUNIT_CTRL_BUTTON,
     .tres_min = 0,
     .tres_max = MCP3008_SINGLE_THRESHOLD,
     .state = false,
     .prev_state = false,
     .work_in_menu = true,
     .parameter = 0,
     .clickHandler = BUTTONHANDLER_RF_POWER,
     .holdHandler = BUTTONHANDLER_SQUELCH}, // RFPOWER-SQUELCH
    {.port = 1,
     .channel = 0,
     .type = FUNIT_CTRL_BUTTON,
     .tres_min = 0,
     .tres_max = MCP3008_SINGLE_THRESHOLD,
     .state = false,
     .prev_state = false,
     .work_in_menu = true,
     .parameter = 0,
     .clickHandler = BUTTONHANDLER_BW,
     .holdHandler = BUTTONHANDLER_HPF}, // BW-HPF

    {.port = 2, .channel = 7, .type = FUNIT_CTRL_RIT_XIT}, // RIT/XIT
    {.port = 2, .channel = 6, .type = FUNIT_CTRL_AF_GAIN}, // AF GAIN
    {.port = 2,
     .channel = 5,
     .type = FUNIT_CTRL_BUTTON,
     .tres_min = 0,
     .tres_max = MCP3008_SINGLE_THRESHOLD,
     .state = false,
     .prev_state = false,
     .work_in_menu = false,
     .parameter = 0,
     .clickHandler = BUTTONHANDLER_DNR,
     .holdHandler = BUTTONHANDLER_NB}, // DNR-NB
    {.port = 2,
     .channel = 4,
     .type = FUNIT_CTRL_BUTTON,
     .tres_min = 0,
     .tres_max = MCP3008_SINGLE_THRESHOLD,
     .state = false,
     .prev_state = false,
     .work_in_menu = false,
     .parameter = 0,
     .clickHandler = BUTTONHANDLER_NOTCH,
     .holdHandler = BUTTONHANDLER_SNAP_LEFT}, // NOTCH-SNAP_LEFT
    {.port = 2,
     .channel = 3,
     .type = FUNIT_CTRL_BUTTON,
     .tres_min = 0,
     .tres_max = MCP3008_SINGLE_THRESHOLD,
     .state = false,
     .prev_state = false,
     .work_in_menu = false,
     .parameter = 0,
     .clickHandler = BUTTONHANDLER_SPLIT,
     .holdHandler = BUTTONHANDLER_RIT}, // SPLIT-RIT
    {.port = 2,
     .channel = 2,
     .type = FUNIT_CTRL_BUTTON,
     .tres_min = 0,
     .tres_max = MCP3008_SINGLE_THRESHOLD,
     .state = false,
     .prev_state = false,
     .work_in_menu = false,
     .parameter = 0,
     .clickHandler = BUTTONHANDLER_PLAY,
     .holdHandler = BUTTONHANDLER_REC}, // REC-PLAY
    {.port = 2,
     .channel = 1,
     .type = FUNIT_CTRL_BUTTON,
     .tres_min = 0,
     .tres_max = MCP3008_SINGLE_THRESHOLD,
     .state = false,
     .prev_state = false,
     .work_in_menu = true,
     .parameter = 0,
     .clickHandler = BUTTONHANDLER_SERVICES,
     .holdHandler = BUTTONHANDLER_SNAP_RIGHT}, // SERVICES-SNAP_RIGHT
    {.port = 2,
     .channel = 0,
     .type = FUNIT_CTRL_BUTTON,
     .tres_min = 0,
     .tres_max = MCP3008_SINGLE_THRESHOLD,
     .state = false,
     .prev_state = false,
     .work_in_menu = true,
     .parameter = 0,
     .clickHandler = BUTTONHANDLER_MENU,
     .holdHandler = BUTTONHANDLER_LOCK}, // MENU-LOCK

    {.port = 3,
     .channel = 7,
     .type = FUNIT_CTRL_BUTTON,
     .tres_min = 0,
     .tres_max = MCP3008_SINGLE_THRESHOLD,
     .state = false,
     .prev_state = false,
     .work_in_menu = true,
     .parameter = 0,
     .clickHandler = BUTTONHANDLER_WPM,
     .holdHandler = BUTTONHANDLER_KEYER}, // WPM-KEYER
    {.port = 3,
     .channel = 6,
     .type = FUNIT_CTRL_BUTTON,
     .tres_min = 0,
     .tres_max = MCP3008_SINGLE_THRESHOLD,
     .state = false,
     .prev_state = false,
     .work_in_menu = false,
     .parameter = 0,
     .clickHandler = BUTTONHANDLER_DOUBLE,
     .holdHandler = BUTTONHANDLER_DOUBLEMODE}, // DOUBLE-&+
    {.port = 3,
     .channel = 5,
     .type = FUNIT_CTRL_BUTTON,
     .tres_min = 0,
     .tres_max = MCP3008_SINGLE_THRESHOLD,
     .state = false,
     .prev_state = false,
     .work_in_menu = true,
     .parameter = 0,
     .clickHandler = BUTTONHANDLER_FAST,
     .holdHandler = BUTTONHANDLER_STEP}, // FAST-FASTSETT
    {.port = 3,
     .channel = 4,
     .type = FUNIT_CTRL_BUTTON,
     .tres_min = 0,
     .tres_max = MCP3008_SINGLE_THRESHOLD,
     .state = false,
     .prev_state = false,
     .work_in_menu = false,
     .parameter = 0,
     .clickHandler = BUTTONHANDLER_BAND_N,
     .holdHandler = BUTTONHANDLER_BAND_N}, // BAND-
    {.port = 3,
     .channel = 3,
     .type = FUNIT_CTRL_BUTTON,
     .tres_min = 0,
     .tres_max = MCP3008_SINGLE_THRESHOLD,
     .state = false,
     .prev_state = false,
     .work_in_menu = false,
     .parameter = 0,
     .clickHandler = BUTTONHANDLER_BAND_P,
     .holdHandler = BUTTONHANDLER_BAND_P}, // BAND+
    {.port = 3,
     .channel = 2,
     .type = FUNIT_CTRL_BUTTON,
     .tres_min = 0,
     .tres_max = MCP3008_SINGLE_THRESHOLD,
     .state = false,
     .prev_state = false,
     .work_in_menu = false,
     .parameter = 0,
     .clickHandler = BUTTONHANDLER_MODE_P,
     .holdHandler = BUTTONHANDLER_MODE_P}, // MODE+
    {.port = 3,
     .channel = 1,
     .type = FUNIT_CTRL_BUTTON,
     .tres_min = 0,
     .tres_max = MCP3008_SINGLE_THRESHOLD,
     .state = false,
     .prev_state = false,
     .work_in_menu = false,
     .parameter = 0,
     .clickHandler = BUTTONHANDLER_MODE_N,
     .holdHandler = BUTTONHANDLER_MODE_N}, // MODE-
    {.port = 3,
     .channel = 0,
     .type = FUNIT_CTRL_BUTTON,
     .tres_min = 0,
     .tres_max = MCP3008_SINGLE_THRESHOLD,
     .state = false,
     .prev_state = false,
     .work_in_menu = false,
     .parameter = 0,
     .clickHandler = BUTTONHANDLER_AsB,
     .holdHandler = BUTTONHANDLER_BANDMAP}, // A/B-BANDMAP
};

const PERIPH_FrontPanel_FuncButton PERIPH_FrontPanel_FuncButtonsList[FUNCBUTTONS_COUNT] = {};
#endif

#ifdef FRONTPANEL_BIG_V1
PERIPH_FrontPanel_Button PERIPH_FrontPanel_Buttons[] = {
    // buttons
    {.port = 1, .channel = 0, .type = FUNIT_CTRL_AF_GAIN}, // AF GAIN
    {.port = 1, .channel = 1, .type = FUNIT_CTRL_RIT_XIT}, // RIT/XIT

    {.port = 1, .channel = 2, .type = FUNIT_CTRL_TANGENT}, // TANGENT_SW1
    {.port = 1, .channel = 3, .type = FUNIT_CTRL_TANGENT}, // TANGENT_SW2

    {.port = 1,
     .channel = 4,
     .type = FUNIT_CTRL_BUTTON,
     .tres_min = 450,
     .tres_max = 650,
     .state = false,
     .prev_state = false,
     .work_in_menu = true,
     .parameter = 0,
     .clickHandler = FRONTPANEL_ENC2SW_click_handler,
     .holdHandler = FRONTPANEL_ENC2SW_hold_handler}, // ENC2_SW
    {.port = 1,
     .channel = 4,
     .type = FUNIT_CTRL_BUTTON,
     .tres_min = 250,
     .tres_max = 450,
     .state = false,
     .prev_state = false,
     .work_in_menu = true,
     .parameter = 7,
     .clickHandler = BUTTONHANDLER_FUNC,
     .holdHandler = BUTTONHANDLER_FUNCH}, // FUNC8
    {.port = 1,
     .channel = 4,
     .type = FUNIT_CTRL_BUTTON,
     .tres_min = 000,
     .tres_max = 250,
     .state = false,
     .prev_state = false,
     .work_in_menu = true,
     .parameter = 6,
     .clickHandler = BUTTONHANDLER_FUNC,
     .holdHandler = BUTTONHANDLER_FUNCH}, // FUNC7
    {.port = 1,
     .channel = 5,
     .type = FUNIT_CTRL_BUTTON,
     .tres_min = 450,
     .tres_max = 650,
     .state = false,
     .prev_state = false,
     .work_in_menu = false,
     .parameter = 0,
     .clickHandler = BUTTONHANDLER_BAND_P,
     .holdHandler = BUTTONHANDLER_BAND_N}, // ENC_B_3
    {.port = 1,
     .channel = 5,
     .type = FUNIT_CTRL_BUTTON,
     .tres_min = 250,
     .tres_max = 450,
     .state = false,
     .prev_state = false,
     .work_in_menu = false,
     .parameter = 0,
     .clickHandler = BUTTONHANDLER_MODE_N,
     .holdHandler = BUTTONHANDLER_MODE_P}, // ENC_B_2
    {.port = 1,
     .channel = 5,
     .type = FUNIT_CTRL_BUTTON,
     .tres_min = 000,
     .tres_max = 250,
     .state = false,
     .prev_state = false,
     .work_in_menu = false,
     .parameter = 0,
     .clickHandler = BUTTONHANDLER_AsB,
     .holdHandler = BUTTONHANDLER_ArB}, // ENC_B_1
    {.port = 1,
     .channel = 6,
     .type = FUNIT_CTRL_BUTTON,
     .tres_min = 450,
     .tres_max = 650,
     .state = false,
     .prev_state = false,
     .work_in_menu = true,
     .parameter = 3,
     .clickHandler = BUTTONHANDLER_FUNC,
     .holdHandler = BUTTONHANDLER_FUNCH}, // FUNC4
    {.port = 1,
     .channel = 6,
     .type = FUNIT_CTRL_BUTTON,
     .tres_min = 250,
     .tres_max = 450,
     .state = false,
     .prev_state = false,
     .work_in_menu = true,
     .parameter = 5,
     .clickHandler = BUTTONHANDLER_FUNC,
     .holdHandler = BUTTONHANDLER_FUNCH}, // FUNC6
    {.port = 1,
     .channel = 6,
     .type = FUNIT_CTRL_BUTTON,
     .tres_min = 000,
     .tres_max = 250,
     .state = false,
     .prev_state = false,
     .work_in_menu = true,
     .parameter = 4,
     .clickHandler = BUTTONHANDLER_FUNC,
     .holdHandler = BUTTONHANDLER_FUNCH}, // FUNC5
    {.port = 1,
     .channel = 7,
     .type = FUNIT_CTRL_BUTTON,
     .tres_min = 450,
     .tres_max = 650,
     .state = false,
     .prev_state = false,
     .work_in_menu = true,
     .parameter = 2,
     .clickHandler = BUTTONHANDLER_FUNC,
     .holdHandler = BUTTONHANDLER_FUNCH}, // FUNC3
    {.port = 1,
     .channel = 7,
     .type = FUNIT_CTRL_BUTTON,
     .tres_min = 250,
     .tres_max = 450,
     .state = false,
     .prev_state = false,
     .work_in_menu = true,
     .parameter = 1,
     .clickHandler = BUTTONHANDLER_FUNC,
     .holdHandler = BUTTONHANDLER_FUNCH}, // FUNC2
    {.port = 1,
     .channel = 7,
     .type = FUNIT_CTRL_BUTTON,
     .tres_min = 000,
     .tres_max = 250,
     .state = false,
     .prev_state = false,
     .work_in_menu = true,
     .parameter = 0,
     .clickHandler = BUTTONHANDLER_FUNC,
     .holdHandler = BUTTONHANDLER_FUNCH}, // FUNC1
};

const PERIPH_FrontPanel_FuncButton PERIPH_FrontPanel_FuncButtonsList[FUNCBUTTONS_COUNT] = {
    {.name = "A / B", .work_in_menu = false, .clickHandler = BUTTONHANDLER_AsB, .holdHandler = BUTTONHANDLER_AsB, .checkBool = NULL},
    {.name = "B=A", .work_in_menu = false, .clickHandler = BUTTONHANDLER_ArB, .holdHandler = BUTTONHANDLER_ArB, .checkBool = NULL},
    {.name = "TUNE", .work_in_menu = true, .clickHandler = BUTTONHANDLER_TUNE, .holdHandler = BUTTONHANDLER_TUNE, .checkBool = (uint32_t *)&TRX_Tune},
    {.name = "POWER", .work_in_menu = true, .clickHandler = BUTTONHANDLER_RF_POWER, .holdHandler = BUTTONHANDLER_RF_POWER, .checkBool = NULL},
    {.name = "XIT", .work_in_menu = false, .clickHandler = BUTTONHANDLER_XIT, .holdHandler = BUTTONHANDLER_XIT, .checkBool = (uint32_t *)&TRX.XIT_Enabled},
    {.name = "RIT", .work_in_menu = false, .clickHandler = BUTTONHANDLER_RIT, .holdHandler = BUTTONHANDLER_RIT, .checkBool = (uint32_t *)&TRX.RIT_Enabled},
    {.name = "SERVICE", .work_in_menu = true, .clickHandler = BUTTONHANDLER_SERVICES, .holdHandler = BUTTONHANDLER_SERVICES, .checkBool = NULL},
    {.name = "MENU", .work_in_menu = true, .clickHandler = BUTTONHANDLER_MENU, .holdHandler = BUTTONHANDLER_MENU, .checkBool = NULL},

    {.name = "SNAP <", .work_in_menu = false, .clickHandler = BUTTONHANDLER_SNAP_LEFT, .holdHandler = BUTTONHANDLER_AUTO_SNAP, .checkBool = (uint32_t *)&TRX.Auto_Snap},
    {.name = "SNAP >", .work_in_menu = false, .clickHandler = BUTTONHANDLER_SNAP_RIGHT, .holdHandler = BUTTONHANDLER_AUTO_SNAP, .checkBool = (uint32_t *)&TRX.Auto_Snap},
    {.name = "DOUBLE", .work_in_menu = false, .clickHandler = BUTTONHANDLER_DOUBLE, .holdHandler = BUTTONHANDLER_DOUBLEMODE, .checkBool = (uint32_t *)&TRX.Dual_RX},
    {.name = "SPLIT", .work_in_menu = false, .clickHandler = BUTTONHANDLER_SPLIT, .holdHandler = BUTTONHANDLER_SPLIT, .checkBool = (uint32_t *)&TRX.SPLIT_Enabled},
    {.name = "SCAN", .work_in_menu = false, .clickHandler = BUTTONHANDLER_SCAN, .holdHandler = BUTTONHANDLER_SCAN, .checkBool = (uint32_t *)&TRX_ScanMode},
    {.name = "PLAY", .work_in_menu = false, .clickHandler = BUTTONHANDLER_PLAY, .holdHandler = BUTTONHANDLER_FILEMANAGER, .checkBool = (uint32_t *)&SD_PlayInProcess},
    {.name = "REC", .work_in_menu = false, .clickHandler = BUTTONHANDLER_REC, .holdHandler = BUTTONHANDLER_REC, .checkBool = (uint32_t *)&SD_RecordInProcess},
    {.name = "MENU", .work_in_menu = true, .clickHandler = BUTTONHANDLER_MENU, .holdHandler = BUTTONHANDLER_MENU, .checkBool = NULL},

    {.name = "HPF", .work_in_menu = true, .clickHandler = BUTTONHANDLER_HPF, .holdHandler = BUTTONHANDLER_HPF, .checkBool = NULL},
    {.name = "MODE-", .work_in_menu = false, .clickHandler = BUTTONHANDLER_MODE_N, .holdHandler = BUTTONHANDLER_MODE_N, .checkBool = NULL},
    {.name = "MODE+", .work_in_menu = false, .clickHandler = BUTTONHANDLER_MODE_P, .holdHandler = BUTTONHANDLER_MODE_P, .checkBool = NULL},
    {.name = "BAND-", .work_in_menu = false, .clickHandler = BUTTONHANDLER_BAND_N, .holdHandler = BUTTONHANDLER_BAND_N, .checkBool = NULL},
    {.name = "BAND+", .work_in_menu = false, .clickHandler = BUTTONHANDLER_BAND_P, .holdHandler = BUTTONHANDLER_BAND_P, .checkBool = NULL},
    {.name = "BANDMP", .work_in_menu = false, .clickHandler = BUTTONHANDLER_BANDMAP, .holdHandler = BUTTONHANDLER_BANDMAP, .checkBool = (uint32_t *)&TRX.BandMapEnabled},
    {.name = "AUTOGN", .work_in_menu = false, .clickHandler = BUTTONHANDLER_AUTOGAINER, .holdHandler = BUTTONHANDLER_AUTOGAINER, .checkBool = (uint32_t *)&TRX.AutoGain},
    {.name = "MENU", .work_in_menu = true, .clickHandler = BUTTONHANDLER_MENU, .holdHandler = BUTTONHANDLER_MENU, .checkBool = NULL},

    {.name = "SAMPLE-", .work_in_menu = true, .clickHandler = BUTTONHANDLER_SAMPLE_N, .holdHandler = BUTTONHANDLER_SAMPLE_N, .checkBool = NULL},
    {.name = "SAMPLE+", .work_in_menu = false, .clickHandler = BUTTONHANDLER_SAMPLE_P, .holdHandler = BUTTONHANDLER_SAMPLE_P, .checkBool = NULL},
    {.name = "ZOOM-", .work_in_menu = false, .clickHandler = BUTTONHANDLER_ZOOM_N, .holdHandler = BUTTONHANDLER_ZOOM_N, .checkBool = NULL},
    {.name = "ZOOM+", .work_in_menu = false, .clickHandler = BUTTONHANDLER_ZOOM_P, .holdHandler = BUTTONHANDLER_ZOOM_P, .checkBool = NULL},
    {.name = "SQL", .work_in_menu = true, .clickHandler = BUTTONHANDLER_SQUELCH, .holdHandler = BUTTONHANDLER_SQUELCH, .checkBool = (uint32_t *)&TRX.SQL_shadow},
    {.name = "WPM", .work_in_menu = true, .clickHandler = BUTTONHANDLER_WPM, .holdHandler = BUTTONHANDLER_WPM, .checkBool = NULL},
    {.name = "LOCK", .work_in_menu = true, .clickHandler = BUTTONHANDLER_LOCK, .holdHandler = BUTTONHANDLER_LOCK, .checkBool = (uint32_t *)&TRX.Locked},
    {.name = "MENU", .work_in_menu = true, .clickHandler = BUTTONHANDLER_MENU, .holdHandler = BUTTONHANDLER_MENU, .checkBool = NULL},

    // hidden entry for menu editor
    {.name = "FT8", .work_in_menu = false, .clickHandler = BUTTONHANDLER_FT8, .holdHandler = BUTTONHANDLER_FT8, .checkBool = NULL},
    {.name = "VOX", .work_in_menu = true, .clickHandler = BUTTONHANDLER_VOX, .holdHandler = BUTTONHANDLER_VOX, .checkBool = (uint32_t *)&TRX.VOX},
    {.name = "FILES", .work_in_menu = false, .clickHandler = BUTTONHANDLER_FILEMANAGER, .holdHandler = BUTTONHANDLER_FILEMANAGER, .checkBool = NULL},
    {.name = "ANT", .work_in_menu = false, .clickHandler = BUTTONHANDLER_ANT, .holdHandler = BUTTONHANDLER_ANT, .checkBool = NULL},
    {.name = "CESSB", .work_in_menu = false, .clickHandler = BUTTONHANDLER_CESSB, .holdHandler = BUTTONHANDLER_CESSB, .checkBool = (uint32_t *)&TRX.TX_CESSB},
};
#endif

#ifdef FRONTPANEL_WF_100D
PERIPH_FrontPanel_Button PERIPH_FrontPanel_Buttons[] = {
    // buttons
    {.port = 1, .channel = 0, .type = FUNIT_CTRL_AF_GAIN}, // AF GAIN
    {.port = 1, .channel = 1, .type = FUNIT_CTRL_RIT_XIT}, // RIT/XIT

    {.port = 1,
     .channel = 2,
     .type = FUNIT_CTRL_BUTTON,
     .tres_min = 100,
     .tres_max = 231,
     .state = false,
     .prev_state = false,
     .work_in_menu = true,
     .parameter = 8,
     .clickHandler = BUTTONHANDLER_FUNC,
     .holdHandler = BUTTONHANDLER_FUNCH}, // SB16 F9
    {.port = 1,
     .channel = 2,
     .type = FUNIT_CTRL_BUTTON,
     .tres_min = 231,
     .tres_max = 354,
     .state = false,
     .prev_state = false,
     .work_in_menu = true,
     .parameter = 7,
     .clickHandler = BUTTONHANDLER_FUNC,
     .holdHandler = BUTTONHANDLER_FUNCH}, // SB17 F8
    {.port = 1,
     .channel = 2,
     .type = FUNIT_CTRL_BUTTON,
     .tres_min = 354,
     .tres_max = 492,
     .state = false,
     .prev_state = false,
     .work_in_menu = true,
     .parameter = 6,
     .clickHandler = BUTTONHANDLER_FUNC,
     .holdHandler = BUTTONHANDLER_FUNCH}, // SB18 F7
    {.port = 1,
     .channel = 2,
     .type = FUNIT_CTRL_BUTTON,
     .tres_min = 492,
     .tres_max = 700,
     .state = false,
     .prev_state = false,
     .work_in_menu = true,
     .parameter = 5,
     .clickHandler = BUTTONHANDLER_FUNC,
     .holdHandler = BUTTONHANDLER_FUNCH}, // SB19 F6

    {.port = 1,
     .channel = 3,
     .type = FUNIT_CTRL_BUTTON,
     .tres_min = 117,
     .tres_max = 231,
     .state = false,
     .prev_state = false,
     .work_in_menu = true,
     .parameter = 4,
     .clickHandler = BUTTONHANDLER_FUNC,
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
     .type = FUNIT_CTRL_BUTTON,
     .tres_min = 650,
     .tres_max = 750,
     .state = false,
     .prev_state = false,
     .work_in_menu = true,
     .parameter = 0,
     .clickHandler = FRONTPANEL_ENC2SW_click_handler,
     .holdHandler = FRONTPANEL_ENC2SW_hold_handler}, // ENC2_SW
};

const PERIPH_FrontPanel_FuncButton PERIPH_FrontPanel_FuncButtonsList[FUNCBUTTONS_COUNT] = {
    {.name = "A / B", .work_in_menu = false, .clickHandler = BUTTONHANDLER_AsB, .holdHandler = BUTTONHANDLER_AsB, .checkBool = NULL},
    {.name = "B=A", .work_in_menu = false, .clickHandler = BUTTONHANDLER_ArB, .holdHandler = BUTTONHANDLER_ArB, .checkBool = NULL},
    {.name = "POWER", .work_in_menu = true, .clickHandler = BUTTONHANDLER_RF_POWER, .holdHandler = BUTTONHANDLER_RF_POWER, .checkBool = NULL},
    {.name = "DOUBLE", .work_in_menu = false, .clickHandler = BUTTONHANDLER_DOUBLE, .holdHandler = BUTTONHANDLER_DOUBLEMODE, .checkBool = (uint32_t *)&TRX.Dual_RX},
    {.name = "XIT", .work_in_menu = true, .clickHandler = BUTTONHANDLER_XIT, .holdHandler = BUTTONHANDLER_XIT, .checkBool = (uint32_t *)&TRX.XIT_Enabled},
    {.name = "RIT", .work_in_menu = false, .clickHandler = BUTTONHANDLER_RIT, .holdHandler = BUTTONHANDLER_RIT, .checkBool = (uint32_t *)&TRX.RIT_Enabled},
    {.name = "PLAY", .work_in_menu = false, .clickHandler = BUTTONHANDLER_PLAY, .holdHandler = BUTTONHANDLER_FILEMANAGER, .checkBool = (uint32_t *)&SD_PlayInProcess},
    {.name = "REC", .work_in_menu = false, .clickHandler = BUTTONHANDLER_REC, .holdHandler = BUTTONHANDLER_REC, .checkBool = (uint32_t *)&SD_RecordInProcess},
    {.name = "SERVICE", .work_in_menu = true, .clickHandler = BUTTONHANDLER_SERVICES, .holdHandler = BUTTONHANDLER_SERVICES, .checkBool = NULL},

    {.name = "SAMPL-", .work_in_menu = true, .clickHandler = BUTTONHANDLER_SAMPLE_N, .holdHandler = BUTTONHANDLER_SAMPLE_N, .checkBool = NULL},
    {.name = "SAMPL+", .work_in_menu = false, .clickHandler = BUTTONHANDLER_SAMPLE_P, .holdHandler = BUTTONHANDLER_SAMPLE_P, .checkBool = NULL},
    {.name = "ZOOM-", .work_in_menu = false, .clickHandler = BUTTONHANDLER_ZOOM_N, .holdHandler = BUTTONHANDLER_ZOOM_N, .checkBool = NULL},
    {.name = "ZOOM+", .work_in_menu = false, .clickHandler = BUTTONHANDLER_ZOOM_P, .holdHandler = BUTTONHANDLER_ZOOM_P, .checkBool = NULL},
    {.name = "SNAP <", .work_in_menu = false, .clickHandler = BUTTONHANDLER_SNAP_LEFT, .holdHandler = BUTTONHANDLER_AUTO_SNAP, .checkBool = (uint32_t *)&TRX.Auto_Snap},
    {.name = "SNAP >", .work_in_menu = false, .clickHandler = BUTTONHANDLER_SNAP_RIGHT, .holdHandler = BUTTONHANDLER_AUTO_SNAP, .checkBool = (uint32_t *)&TRX.Auto_Snap},
    {.name = "SPLIT", .work_in_menu = false, .clickHandler = BUTTONHANDLER_SPLIT, .holdHandler = BUTTONHANDLER_SPLIT, .checkBool = (uint32_t *)&TRX.SPLIT_Enabled},
    {.name = "WPM", .work_in_menu = true, .clickHandler = BUTTONHANDLER_WPM, .holdHandler = BUTTONHANDLER_WPM, .checkBool = NULL},
    {.name = "TUNE", .work_in_menu = true, .clickHandler = BUTTONHANDLER_TUNE, .holdHandler = BUTTONHANDLER_TUNE, .checkBool = (uint32_t *)&TRX_Tune},

    {.name = "SCAN", .work_in_menu = false, .clickHandler = BUTTONHANDLER_SCAN, .holdHandler = BUTTONHANDLER_SCAN, .checkBool = (uint32_t *)&TRX_ScanMode},
    {.name = "HPF", .work_in_menu = true, .clickHandler = BUTTONHANDLER_HPF, .holdHandler = BUTTONHANDLER_HPF, .checkBool = NULL},
    {.name = "MODE+", .work_in_menu = false, .clickHandler = BUTTONHANDLER_MODE_P, .holdHandler = BUTTONHANDLER_MODE_P, .checkBool = NULL},
    {.name = "MODE-", .work_in_menu = false, .clickHandler = BUTTONHANDLER_MODE_N, .holdHandler = BUTTONHANDLER_MODE_N, .checkBool = NULL},
    {.name = "BAND-", .work_in_menu = false, .clickHandler = BUTTONHANDLER_BAND_N, .holdHandler = BUTTONHANDLER_BAND_N, .checkBool = NULL},
    {.name = "BAND+", .work_in_menu = false, .clickHandler = BUTTONHANDLER_BAND_P, .holdHandler = BUTTONHANDLER_BAND_P, .checkBool = NULL},
    {.name = "BANDMP", .work_in_menu = false, .clickHandler = BUTTONHANDLER_BANDMAP, .holdHandler = BUTTONHANDLER_BANDMAP, .checkBool = (uint32_t *)&TRX.BandMapEnabled},
    {.name = "AUTOGN", .work_in_menu = false, .clickHandler = BUTTONHANDLER_AUTOGAINER, .holdHandler = BUTTONHANDLER_AUTOGAINER, .checkBool = (uint32_t *)&TRX.AutoGain},
    {.name = "LOCK", .work_in_menu = true, .clickHandler = BUTTONHANDLER_LOCK, .holdHandler = BUTTONHANDLER_LOCK, .checkBool = (uint32_t *)&TRX.Locked},

    // hidden entry for menu editor
    {.name = "MENU", .work_in_menu = true, .clickHandler = BUTTONHANDLER_MENU, .holdHandler = BUTTONHANDLER_MENU, .checkBool = NULL},
    {.name = "FT8", .work_in_menu = false, .clickHandler = BUTTONHANDLER_FT8, .holdHandler = BUTTONHANDLER_FT8, .checkBool = NULL},
    {.name = "SQL", .work_in_menu = true, .clickHandler = BUTTONHANDLER_SQUELCH, .holdHandler = BUTTONHANDLER_SQUELCH, .checkBool = (uint32_t *)&TRX.SQL_shadow},
    {.name = "VOX", .work_in_menu = true, .clickHandler = BUTTONHANDLER_VOX, .holdHandler = BUTTONHANDLER_VOX, .checkBool = (uint32_t *)&TRX.VOX},
    {.name = "FILES", .work_in_menu = false, .clickHandler = BUTTONHANDLER_FILEMANAGER, .holdHandler = BUTTONHANDLER_FILEMANAGER, .checkBool = NULL},
    {.name = "ANT", .work_in_menu = false, .clickHandler = BUTTONHANDLER_ANT, .holdHandler = BUTTONHANDLER_ANT, .checkBool = NULL},
    {.name = "CESSB", .work_in_menu = false, .clickHandler = BUTTONHANDLER_CESSB, .holdHandler = BUTTONHANDLER_CESSB, .checkBool = (uint32_t *)&TRX.TX_CESSB},
};
#endif

#ifdef FRONTPANEL_NONE
PERIPH_FrontPanel_Button PERIPH_FrontPanel_Buttons[] = {};
const PERIPH_FrontPanel_FuncButton PERIPH_FrontPanel_FuncButtonsList[FUNCBUTTONS_COUNT] = {};
#endif

PERIPH_FrontPanel_Button PERIPH_FrontPanel_TANGENT_MH36[] = {
    {.port = 1, .channel = 2, .type = FUNIT_CTRL_PTT, .tres_min = 200, .tres_max = 430}, // PTT_SW1 - PTT
    {.port = 1,
     .channel = 2,
     .type = FUNIT_CTRL_BUTTON,
     .tres_min = 430,
     .tres_max = 640,
     .state = false,
     .prev_state = false,
     .work_in_menu = false,
     .parameter = 0,
     .clickHandler = BUTTONHANDLER_DOWN,
     .holdHandler = BUTTONHANDLER_DOWN}, // PTT_SW1 - DOWN
    {.port = 1,
     .channel = 2,
     .type = FUNIT_CTRL_BUTTON,
     .tres_min = 640,
     .tres_max = 805,
     .state = false,
     .prev_state = false,
     .work_in_menu = false,
     .parameter = 0,
     .clickHandler = BUTTONHANDLER_UP,
     .holdHandler = BUTTONHANDLER_UP}, // PTT_SW1 - UP
    {.port = 1,
     .channel = 2,
     .type = FUNIT_CTRL_BUTTON,
     .tres_min = 805,
     .tres_max = 920,
     .state = false,
     .prev_state = false,
     .work_in_menu = false,
     .parameter = 0,
     .clickHandler = BUTTONHANDLER_AGC,
     .holdHandler = BUTTONHANDLER_AGC}, // PTT_SW1 - AGC
    {.port = 1,
     .channel = 3,
     .type = FUNIT_CTRL_BUTTON,
     .tres_min = 200,
     .tres_max = 430,
     .state = false,
     .prev_state = false,
     .work_in_menu = false,
     .parameter = 0,
     .clickHandler = BUTTONHANDLER_AsB,
     .holdHandler = BUTTONHANDLER_ArB}, // PTT_SW2 - VFO
    {.port = 1,
     .channel = 3,
     .type = FUNIT_CTRL_BUTTON,
     .tres_min = 430,
     .tres_max = 640,
     .state = false,
     .prev_state = false,
     .work_in_menu = false,
     .parameter = 0,
     .clickHandler = BUTTONHANDLER_BAND_N,
     .holdHandler = BUTTONHANDLER_MODE_N}, // PTT_SW2 - P1
    {.port = 1,
     .channel = 3,
     .type = FUNIT_CTRL_BUTTON,
     .tres_min = 640,
     .tres_max = 805,
     .state = false,
     .prev_state = false,
     .work_in_menu = false,
     .parameter = 0,
     .clickHandler = BUTTONHANDLER_BAND_P,
     .holdHandler = BUTTONHANDLER_MODE_P}, // PTT_SW2 - P2
};
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
